jarjuk/jrr/jrr-rpi.org

#PROPERTY: header-args+ :var  JRR5_IP_="192.168.1.241"
#PROPERTY: header-args+ :var  JRR5_IP="jrr5.local"
#+PROPERTY: header-args+ :var  JRR5_IP="jrr5x.local"
#+PROPERTY: header-args+ :var  CONDA_ENV="pyyton3"
#+PROPERTY: header-args+ :var  FIRMWARE_RELEASE="5"

Somewhat dirtyish trick to be able to tangle files pointed by a global property.

#+BEGIN_SRC elisp :eval no-export :exports none
(defun jj-org-tmp-get-global-prop ( prop )
  "Read global org property 'prop'"
(let ((keyVal 
       (seq-find (lambda (x) (string= (car(split-string  x "=")) prop))
		 (org-babel--get-vars (org-babel-parse-header-arguments (org-entry-get-with-inheritance "header-args")))
		)))	
  (if keyVal (string-trim  (nth 1 (split-string keyVal "=" )) "\""  "\""  )))
)
#+END_SRC

#+RESULTS:
: jj-org-tmp-get-global-prop

* Design
** PCB design

[[file:jrr-pcb.org]]

** 3.5inch TFT display

In jrr.org

#+begin_example
ssh pi@$IP  "cd LCD-show; sudo ./MHS35-show"

#+end_example

Search for MHS35-show finds

http://www.lcdwiki.com/MHS-3.5inch_RPi_Display#Product_Features

with specs

| Name                                  | Description                          |
|---------------------------------------+--------------------------------------|
| SKU                                   | MHS3528                              |
| Screen Size                           | 3.5inch                              |
| LCD Type                              | TFT                                  |
| Module Interface                      | SPI (upports up to 125MHz SPI input) |
| Resolution                            | 320*480 (Pixel)                      |
| Touch Screen Controller               | XPT2046                              |
| LCD Driver IC                         | ILI9486                              |
| Backlight                             | LED                                  |
| power consumption                     | 0.16A*5V                             |
| Working temperature）                 | -20~60                               |
| Active Area                           | 48.96x73.44(mm)                      |
| Module PCB Size                       | 85.42*55.60 (mm)                     |
| Package Size                          | 136x98x41 (mm)                       |
| Product Weight(Package containing)(g) | 92 (g)                               |

Especially LCD Driver IC ~ILI9486~

Locate ILI9486 python driver https://github.com/SirLefti/Python_ILI9486

** Raspberry PI pinout

https://pinout.xyz/

** Physical design

https://datasheets.raspberrypi.com/rpi3/raspberry-pi-3-b-plus-product-brief.pdf

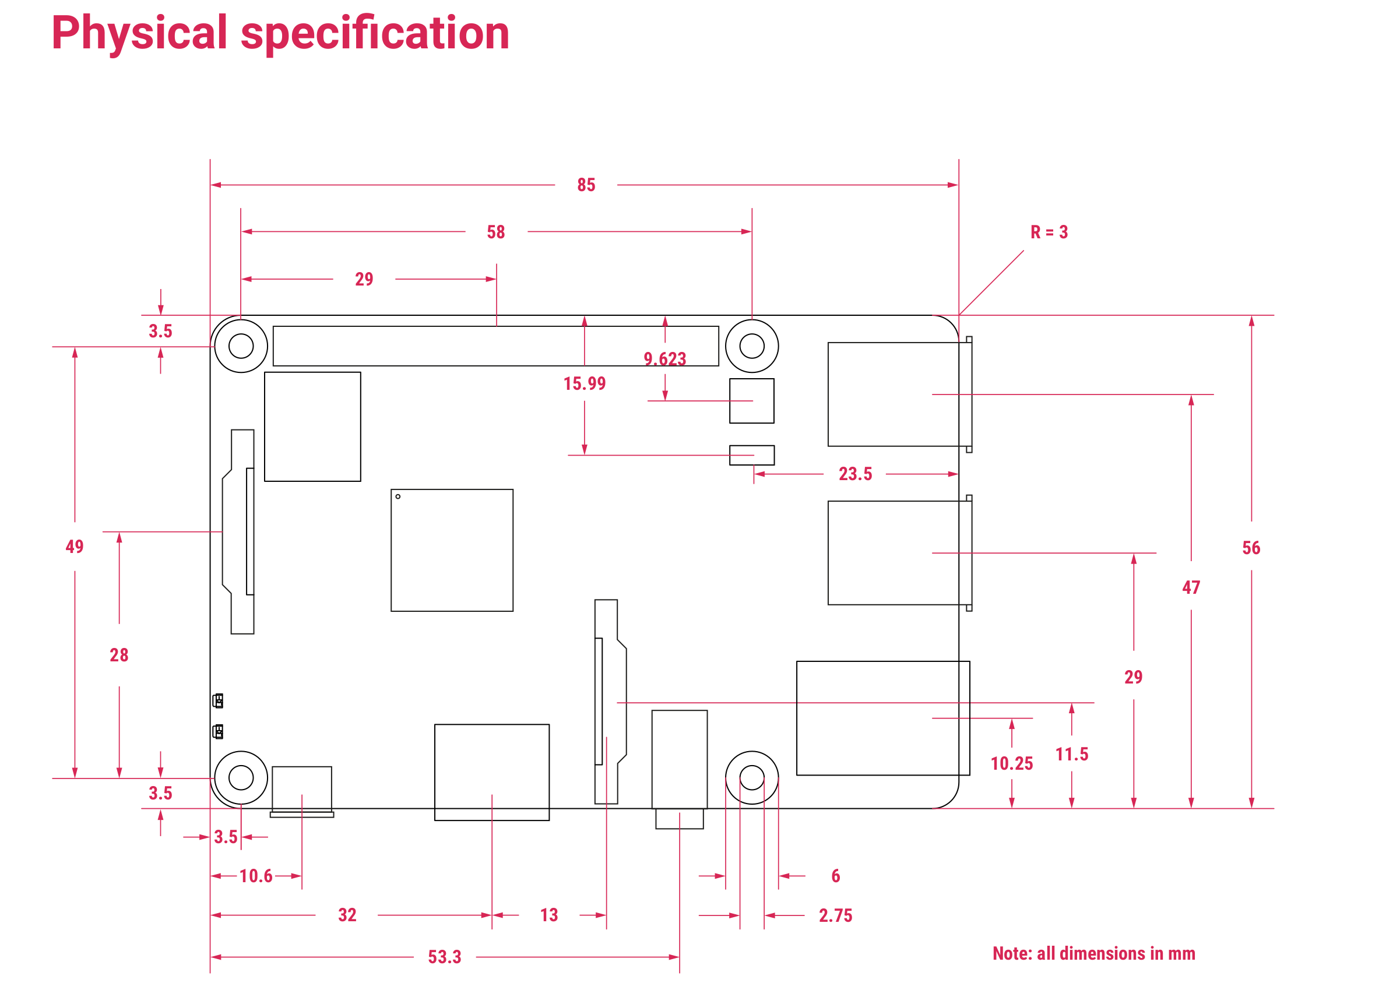
[picture p13: pics-keep/RPI-physical-dimensions.png]


** Current

Mitattu USB virrankultus jrr1
- n. 0.37A max volyymi
- n. 0.57A max virta

Mitattu USB virrankulutus jrr5
- n. 0.37A max volyymi
- n. 0.70A max virta (hekllinen)

--> 1.1A sulake ok

--> USB-C current resistores
   - https://community.infineon.com/t5/Knowledge-Base-Articles/USB-Type-C-connector-Rp-Rd-and-Ra-termination-resistors/ta-p/253544

     DFP Advertisement 	     Resistor Pull-up to
     4.75 V – 5.5 V 	     Resistor Pull-up to
     3.3 ± 5%
     Default USB power 	     56 kΩ ± 20% 	     36 kΩ ± 20%
     1.5 A at 5 V 	     22 kΩ ± 5% 	     12 kΩ ± 5%
     3.0 A at 5 V 	     10 kΩ ± 5% 	     4.7 kΩ ± 5%

| DFP Advertisement | Pull-up to 4.75 V – 5.5 V | Pull-up to 3.3 ± 5% |
|-------------------+---------------------------+---------------------|
| Default USB power | 56 kΩ ± 20%               | 36 kΩ ± 20%         |
| 1.5 A at 5 V      | 22 kΩ ± 5%                | 12 kΩ ± 5%          |
| 3.0 A at 5 V      | 10 kΩ ± 5%                | 4.7 kΩ ± 5%         |

--> 22kOhm     

* Config ssh access

** Create entry into ~.ssh/config~
:PROPERTIES:
:header-args+: :var  FILE="/home/jj/.ssh/config"
:END:

#+BEGIN_SRC bash :eval no-export :results output :dir .
echo "Running in $(pwd) for user '$(whoami)' on host '$(hostname)' on $(date)"
echo "FILE=$FILE"
echo JRR5_IP=${JRR5_IP}
#+END_SRC

#+RESULTS:
: Running in /home/jj/work/jrr for user 'jj' on host 'Leo' on ke 15.7.2026 15.39.07 +0300
: FILE=/home/jj/.ssh/config
: JRR5_IP=jrr5x.local

#+BEGIN_SRC bash :eval no-export :results output :dir .
echo "Running in $(pwd) for user '$(whoami)' on host '$(hostname)' on $(date)"
echo "FILE=$FILE"
cat $FILE
#+END_SRC

Expect raspberry pi to be online
#+call: ping-ip[:dir "."]()

#+RESULTS:
: User 'jj pinging JRR5_IP=jrr5x.local from Leo on ke 15.7.2026 15.39.31 +0300
: PING jrr5x.local (192.168.1.203) 56(84) bytes of data.
: 64 bytes from jrr5x.local (192.168.1.203): icmp_seq=1 ttl=64 time=1.92 ms
: 64 bytes from jrr5x.local (192.168.1.203): icmp_seq=2 ttl=64 time=5.18 ms
: 64 bytes from jrr5x.local (192.168.1.203): icmp_seq=3 ttl=64 time=5.69 ms
: 
: --- jrr5x.local ping statistics ---
: 3 packets transmitted, 3 received, 0% packet loss, time 2003ms
: rtt min/avg/max/mdev = 1.924/4.264/5.693/1.668 ms

#+BEGIN_SRC bash :eval no-export :results output :dir .
FILE=~/.ssh/config
START="added by raspberry.org in jrr-pi  - start"
END="added by raspberry.org in jrr-pi - end"

sed -i -e "/$START/,/$END/d" $FILE

cat <<HERE >> $FILE
# $START
host jrr5
     user pi
     IdentityFile ~/.ssh/id_ed25519
     hostname ${JRR5_IP}
# $END
HERE
#+END_SRC

#+RESULTS:

* Create SD -card image with 3-partitions
:PROPERTIES:
:header-args+: :var  SD_DEV="/dev/sda"
:END:

** Flash rasbian OS using Raspberry Pi Imager (v2.0.4)

- Selections:
  - [ ] Device: RPi 3B+
  - [ ] OS RPi Other, PI OS-light (64 bi)
    - Released 2026-04-21
    - A port of Debian Trixie with Raspberry Desktop
  - [ ] User name: pi
  - [ ] Wifi
  - [ ] Disblae Raspberry Pi Connect
  - [ ] Finnish keyboard
  - [ ] SSH identity id_ed25519.pub
  - [ ] hostname ~jrr5x~ (expect to change jrr5x1, jrr5x2, ...)

** Allocate system partiton 10G, add 2G partision 3 (CLI)
*** Extend partition 2 to include all space on SD card on RPI

#+call: ping-ip[:dir .]()

#+RESULTS:
: User 'jj pinging JRR5_IP=jrr5x.local from Leo on to 16.7.2026 12.32.57 +0300
: PING jrr5x.local (192.168.1.203) 56(84) bytes of data.
: 64 bytes from jrr5x.local (192.168.1.203): icmp_seq=1 ttl=64 time=105 ms
: 64 bytes from jrr5x.local (192.168.1.203): icmp_seq=2 ttl=64 time=5.91 ms
: 64 bytes from jrr5x.local (192.168.1.203): icmp_seq=3 ttl=64 time=5.97 ms
: 
: --- jrr5x.local ping statistics ---
: 3 packets transmitted, 3 received, 0% packet loss, time 2003ms
: rtt min/avg/max/mdev = 5.907/39.015/105.167/46.776 ms

: Ping JRR5_IP=jrr5.local on ti 19.5.2026 10.24.41 +0300
: PING jrr5.local (192.168.1.203) 56(84) bytes of data.
: 64 bytes from jrr5.local (192.168.1.203): icmp_seq=1 ttl=64 time=5.66 ms
: 64 bytes from jrr5.local (192.168.1.203): icmp_seq=2 ttl=64 time=5.60 ms
: 64 bytes from jrr5.local (192.168.1.203): icmp_seq=3 ttl=64 time=2.46 ms
: 
: --- jrr5.local ping statistics ---
: 3 packets transmitted, 3 received, 0% packet loss, time 2002ms
: rtt min/avg/max/mdev = 2.464/4.573/5.657/1.491 ms

Expect ~/ssh:jrr5:~ to log in as pi
#+call: greet-tramp[:dir /ssh:jrr5:]()

#+RESULTS:
: User 'pi' from host 'jrr5x' greeting on Thu Jul 16 12:33:52 EEST 2026  (using eshell tramp)

#+RESULTS:
: Greet Tue May 19 10:25:07 EEST 2026 from host 'jrr5' (using eshell tramp)

*** Check partions on RPI 
:PROPERTIES:
:header-args+: :dir  /ssh:jrr5:
:header-args+: :var  RPI_DISK="/dev/mmcblk0"
:END:

Ensure that running on RPI and RPI_DISK correctly set
#+BEGIN_SRC bash :eval no-export :results output
echo "Running in $(pwd) host '$(hostname)' on $(date)"
[[ -z "$RPI_DISK" ]] && echo "Missing parameter RPI_DISK" && exit 1
echo "RPI_DISK=$RPI_DISK"
#+END_SRC

#+RESULTS:
: Running in /home/pi host 'jrr5x' on Thu Jul 16 12:34:02 EEST 2026
: RPI_DISK=/dev/mmcblk0

#+BEGIN_SRC bash :eval no-export :results output :dir /ssh:jrr5:
  echo "Running in $(pwd) host '$(hostname)' on $(date)"
  sudo lsblk
#+END_SRC

#+RESULTS:
: Running in /home/pi host 'jrr5x' on Thu Jul 16 12:34:08 EEST 2026
: NAME        MAJ:MIN RM  SIZE RO TYPE MOUNTPOINTS
: loop0         7:0    0  905M  0 loop 
: mmcblk0     179:0    0 28.9G  0 disk 
: ├─mmcblk0p1 179:1    0  512M  0 part /boot/firmware
: └─mmcblk0p2 179:2    0 28.4G  0 part /
: zram0       254:0    0  905M  0 disk [SWAP]

: Running in /home/pi host 'jrr5' on Tue May 19 10:25:39 EEST 2026
: NAME        MAJ:MIN RM  SIZE RO TYPE MOUNTPOINTS
: loop0         7:0    0  905M  0 loop 
: mmcblk0     179:0    0 28.9G  0 disk 
: ├─mmcblk0p1 179:1    0  512M  0 part /boot/firmware
: └─mmcblk0p2 179:2    0 28.4G  0 part /
: zram0       254:0    0  905M  0 disk [SWAP]

#+BEGIN_SRC bash :eval no-export :results output
echo "Running in $(pwd) host '$(hostname)' on $(date)"
sudo fdisk -l $RPI_DISK
#+END_SRC

#+RESULTS:
#+begin_example
Running in /home/pi host 'jrr5x' on Thu Jul 16 12:34:14 EEST 2026
Disk /dev/mmcblk0: 28.88 GiB, 31008489472 bytes, 60563456 sectors
Units: sectors of 1 * 512 = 512 bytes
Sector size (logical/physical): 512 bytes / 512 bytes
I/O size (minimum/optimal): 512 bytes / 512 bytes
Disklabel type: dos
Disk identifier: 0x08059157

Device         Boot   Start      End  Sectors  Size Id Type
/dev/mmcblk0p1        16384  1064959  1048576  512M  c W95 FAT32 (LBA)
/dev/mmcblk0p2      1064960 60563455 59498496 28.4G 83 Linux
#+end_example

#+BEGIN_SRC sh :eval no-export :results output :noweb yes
  echo "Running in $(pwd) for user '$(whoami)' on host '$(hostname)' on $(date)"
  echo RPI_DISK=$RPI_DISK
  sudo fdisk $RPI_DISK <<EOF
  p
  EOF
#+END_SRC

#+RESULTS:
#+begin_example
Running in /home/pi for user 'pi' on host 'jrr5x' on Thu Jul 16 12:34:20 EEST 2026
RPI_DISK=/dev/mmcblk0

Welcome to fdisk (util-linux 2.41).
Changes will remain in memory only, until you decide to write them.
Be careful before using the write command.

Command (m for help): 
Disk /dev/mmcblk0: 28.88 GiB, 31008489472 bytes, 60563456 sectors
Units: sectors of 1 * 512 = 512 bytes
Sector size (logical/physical): 512 bytes / 512 bytes
I/O size (minimum/optimal): 512 bytes / 512 bytes
Disklabel type: dos
Disk identifier: 0x08059157

Device         Boot   Start      End  Sectors  Size Id Type
/dev/mmcblk0p1        16384  1064959  1048576  512M  c W95 FAT32 (LBA)
/dev/mmcblk0p2      1064960 60563455 59498496 28.4G 83 Linux

Command (m for help): 
#+end_example

*** Mount to develoment host - resize partition 2 and create new 2GB partition 3 on SD_DEV

**** Using SD_DEV
Mount SD card on host as SD_DEV

#+BEGIN_SRC bash :eval no-export :results output
  echo "Running in $(pwd) host '$(hostname)' on $(date)"
  echo SD_DEV=$SD_DEV
#+END_SRC

#+RESULTS:
: Running in /home/jj/work/jrr host 'Leo' on to 16.7.2026 18.07.29 +0300
: SD_DEV=/dev/sda

**** Ensure that ~SD_DEV~ is pointing to SD card mounted over usb

#+BEGIN_SRC bash :eval no-export :results output
echo "Running in $(pwd) host '$(hostname)' on $(date)"
echo "SD_DEV=$SD_DEV"
#+END_SRC

#+RESULTS:
: Running in /home/jj/work/jrr host 'Leo' on to 16.7.2026 18.07.34 +0300
: SD_DEV=/dev/sda

Check:
- RM=1 → removable device
- TRAN=usb → often SD card readers appear as USB
- Size matches your SD card
  - sda    28,9G usb - OK
  - sda2  28.4G    1 OS system

#+call: lsblk-conf()

#+RESULTS:
: Running in /home/jj/work/jrr host 'Leo' on to 16.7.2026 18.07.39 +0300
: SD_DEV=/dev/sda
: NAME    SIZE TRAN RM MOUNTPOINT
: sda    29,7G usb   1 
: ├─sda1  512M       1 
: └─sda2  2,3G       1 

Expect something like this:

: Running in /home/jj/work/jrr host 'Leo' on to 16.7.2026 12.07.54 +0300
: SD_DEV=/dev/sda
: NAME    SIZE TRAN RM MOUNTPOINT
: sda    28,9G usb   1 
: ├─sda1  512M       1 /media/jj/bootfs
: └─sda2  2,3G       1 /media/jj/rootfs

**** Unmount partitions on SD_DEV

#+BEGIN_SRC bash :eval no-export :results output
echo "Running in $(pwd) host '$(hostname)' on $(date)"
mount | grep $SD_DEV
#+END_SRC

#+RESULTS:
: Running in /home/jj/work/jrr host 'Leo' on to 16.7.2026 18.07.49 +0300

#+name: umount-sd-dev
#+BEGIN_SRC bash :eval no-export :results output  :dir /sudo::
echo "Running in $(pwd) host '$(hostname)' on $(date)"
sudo umount ${SD_DEV}1
sudo umount ${SD_DEV}2
sudo umount ${SD_DEV}3
#+END_SRC

#+RESULTS: umount-sd-dev
: Running in /root host 'Leo' on Thu Jul 16 06:07:53 PM EEST 2026

#+RESULTS:
: Running in /root host 'Leo' on Tue May 19 10:27:24 AM EEST 2026

Show 

#+call: sd-partitions()

#+RESULTS:
#+begin_example
Running in /root host 'Leo' on Thu Jul 16 06:13:08 PM EEST 2026
SD_DEV=/dev/sda

Welcome to fdisk (util-linux 2.39.3).
Changes will remain in memory only, until you decide to write them.
Be careful before using the write command.

Command (m for help): Disk /dev/sda: 29.72 GiB, 31914983424 bytes, 62333952 sectors
Disk model: Storage Device  
Units: sectors of 1 * 512 = 512 bytes
Sector size (logical/physical): 512 bytes / 512 bytes
I/O size (minimum/optimal): 512 bytes / 512 bytes
Disklabel type: dos
Disk identifier: 0x041bba91

Device     Boot   Start     End Sectors  Size Id Type
/dev/sda1         16384 1064959 1048576  512M  c W95 FAT32 (LBA)
/dev/sda2       1064960 5816319 4751360  2.3G 83 Linux

Command (m for help): 
#+end_example

Example of expected output
#+begin_example
Running in /root host 'Leo' on Tue May 19 10:27:32 AM EEST 2026

Welcome to fdisk (util-linux 2.39.3).
Changes will remain in memory only, until you decide to write them.
Be careful before using the write command.

Command (m for help): Disk /dev/sda: 28.88 GiB, 31008489472 bytes, 60563456 sectors
Disk model: Storage Device  
Units: sectors of 1 * 512 = 512 bytes
Sector size (logical/physical): 512 bytes / 512 bytes
I/O size (minimum/optimal): 512 bytes / 512 bytes
Disklabel type: dos
Disk identifier: 0xf307c993

Device     Boot   Start      End  Sectors  Size Id Type
/dev/sda1         16384  1064959  1048576  512M  c W95 FAT32 (LBA)
/dev/sda2       1064960 60563455 59498496 28.4G 83 Linux

Command (m for help): 
#+end_example

**** Shrink PARTITION 2 on SD_DEV 
:PROPERTIES:
:header-args+: :var  PARTITION=2
:END:

#+call: parted-print()

#+RESULTS:
#+begin_example
Running in /root host 'Leo' on Thu Jul 16 06:12:37 PM EEST 2026
Model: Mass Storage Device (scsi)
Disk /dev/sda: 31.9GB
Sector size (logical/physical): 512B/512B
Partition Table: msdos
Disk Flags: 

Number  Start   End     Size    Type     File system  Flags
 1      8389kB  545MB   537MB   primary  fat32        lba
 2      545MB   2978MB  2433MB  primary  ext4

Model: Mass Storage Device (scsi)
Disk /dev/sda: 29.7GiB
Sector size (logical/physical): 512B/512B
Partition Table: msdos
Disk Flags: 

Number  Start    End      Size     Type     File system  Flags
 1      0.01GiB  0.51GiB  0.50GiB  primary  fat32        lba
 2      0.51GiB  2.77GiB  2.27GiB  primary  ext4

#+end_example

Expect something like this

#+begin_example
Running in /root host 'Leo' on Thu Jul 16 12:58:25 PM EEST 2026
Model: Mass Storage Device (scsi)
Disk /dev/sda: 32.2GB
Sector size (logical/physical): 512B/512B
Partition Table: msdos
Disk Flags: 

Number  Start   End     Size    Type     File system  Flags
 1      8389kB  545MB   537MB   primary  fat32        lba
 2      545MB   2978MB  2433MB  primary  ext4

Model: Mass Storage Device (scsi)
Disk /dev/sda: 30.0GiB
Sector size (logical/physical): 512B/512B
Partition Table: msdos
Disk Flags: 

Number  Start    End      Size     Type     File system  Flags
 1      0.01GiB  0.51GiB  0.50GiB  primary  fat32        lba
 2      0.51GiB  2.77GiB  2.27GiB  primary  ext4

#+end_example

#+call: fs-check(PARTITION=2)
#+RESULTS:
: CHeck /dev/sda2 in /root host 'Leo' on Thu Jul 16 06:08:59 PM EEST 2026
: e2fsck 1.47.0 (5-Feb-2023)
: Pass 1: Checking inodes, blocks, and sizes
: Pass 2: Checking directory structure
: Pass 3: Checking directory connectivity
: Pass 4: Checking reference counts
: Pass 5: Checking group summary information
: rootfs: 73256/148656 files (0.2% non-contiguous), 513060/593920 blocks

Expected output 

: CHeck /dev/sda2 in /root host 'Leo' on Wed Jul 15 07:42:36 PM EEST 2026
: Pass 1: Checking inodes, blocks, and sizes
: Pass 2: Checking directory structure
: Pass 3: Checking directory connectivity
: Pass 4: Checking reference counts
: Pass 5: Checking group summary information
: rootfs: 73281/1776048 files (0.2% non-contiguous), 847924/7437312 blocks

Shrink ext4 filesystem FIRST to +22G+ 10G
#+BEGIN_SRC bash :eval no-export :results output  :dir /sudo::
  echo "Running in $(pwd) host '$(hostname)' on $(date)"
  sudo resize2fs ${SD_DEV}${PARTITION} 10G
#+END_SRC

#+RESULTS:
: Running in /root host 'Leo' on Thu Jul 16 06:11:02 PM EEST 2026

#+BEGIN_SRC bash :eval no-export :results output
  echo "Running in $(pwd) host '$(hostname)' on $(date)"
  echo Partition ${SD_DEV}${PARTITION}
  df -h ${SD_DEV}${PARTITION}
#+END_SRC

#+RESULTS:
: Running in /home/jj/work/jrr host 'Leo' on to 16.7.2026 18.10.27 +0300
: Partition /dev/sda2
: Filesystem      Size  Used Avail Use% Mounted on
: udev             16G     0   16G   0% /dev

Expected output
: Running in /home/jj/work/jrr host 'Leo' on ti 19.5.2026 10.28.03 +0300
: Partition /dev/sda2
: Filesystem      Size  Used Avail Use% Mounted on
: udev             16G     0   16G   0% /dev

#+BEGIN_SRC octave :eval no-export :results output :session *Octave* :exports both
  pico = 10^-12;
  nano = 10^-9;
  micro = 10^-6;
  milli = 10^-3;
  kilo = 10^3;
  mega = 10^6;
  giga = 10^9;

5767168 * 4*1024
  #+END_SRC   

#+RESULTS:
: ans = 2.3622e+10

Check file system (after resize - expect pass)
#+call: fs-check(PARTITION=2)

#+RESULTS:
: CHeck /dev/sda2 in /root host 'Leo' on Thu Jul 16 12:59:08 PM EEST 2026
: e2fsck 1.47.0 (5-Feb-2023)
: Pass 1: Checking inodes, blocks, and sizes
: Pass 2: Checking directory structure
: Pass 3: Checking directory connectivity
: Pass 4: Checking reference counts
: Pass 5: Checking group summary information
: rootfs: 73256/148656 files (0.2% non-contiguous), 513060/593920 blocks

Before resize confirm:
- partition 2 currently extends beyond 25GiB
- partition 1 stays untouched
- there’s room afterward for partition 3

#+call: parted-print()  

#+RESULTS:
#+begin_example
Running in /root host 'Leo' on Thu Jul 16 12:59:26 PM EEST 2026
Model: Mass Storage Device (scsi)
Disk /dev/sda: 32.2GB
Sector size (logical/physical): 512B/512B
Partition Table: msdos
Disk Flags: 

Number  Start   End     Size    Type     File system  Flags
 1      8389kB  545MB   537MB   primary  fat32        lba
 2      545MB   2978MB  2433MB  primary  ext4

Model: Mass Storage Device (scsi)
Disk /dev/sda: 30.0GiB
Sector size (logical/physical): 512B/512B
Partition Table: msdos
Disk Flags: 

Number  Start    End      Size     Type     File system  Flags
 1      0.01GiB  0.51GiB  0.50GiB  primary  fat32        lba
 2      0.51GiB  2.77GiB  2.27GiB  primary  ext4

#+end_example

Expected output
#+begin_example
Running in /root host 'Leo' on Tue May 19 10:28:20 AM EEST 2026
Model: Mass Storage Device (scsi)
Disk /dev/sda: 31.0GB
Sector size (logical/physical): 512B/512B
Partition Table: msdos
Disk Flags: 

Number  Start   End     Size    Type     File system  Flags
 1      8389kB  545MB   537MB   primary  fat32        lba
 2      545MB   31.0GB  30.5GB  primary  ext4

Model: Mass Storage Device (scsi)
Disk /dev/sda: 28.9GiB
Sector size (logical/physical): 512B/512B
Partition Table: msdos
Disk Flags: 

Number  Start    End      Size     Type     File system  Flags
 1      0.01GiB  0.51GiB  0.50GiB  primary  fat32        lba
 2      0.51GiB  28.9GiB  28.4GiB  primary  ext4

#+end_example

Run on command line (notice 23GiB for 22G filesystem)
#+BEGIN_SRC bash :eval no-export :results output  :dir /sudo::
echo "Running in $(pwd) host '$(hostname)' on $(date)"
echo sudo parted  $SD_DEV resizepart 2 23GiB
#+END_SRC

#+RESULTS:
: Running in /root host 'Leo' on Thu Jul 16 12:59:35 PM EEST 2026
: sudo parted /dev/sda resizepart 2 23GiB

Check 
#+call: parted-print()  

#+RESULTS:
#+begin_example
Running in /root host 'Leo' on Thu Jul 16 01:00:01 PM EEST 2026
Model: Mass Storage Device (scsi)
Disk /dev/sda: 32.2GB
Sector size (logical/physical): 512B/512B
Partition Table: msdos
Disk Flags: 

Number  Start   End     Size    Type     File system  Flags
 1      8389kB  545MB   537MB   primary  fat32        lba
 2      545MB   24.7GB  24.2GB  primary  ext4

Model: Mass Storage Device (scsi)
Disk /dev/sda: 30.0GiB
Sector size (logical/physical): 512B/512B
Partition Table: msdos
Disk Flags: 

Number  Start    End      Size     Type     File system  Flags
 1      0.01GiB  0.51GiB  0.50GiB  primary  fat32        lba
 2      0.51GiB  23.0GiB  22.5GiB  primary  ext4

#+end_example

Expected output

#+begin_example
Running in /root host 'Leo' on Tue May 19 10:29:16 AM EEST 2026
Model: Mass Storage Device (scsi)
Disk /dev/sda: 31.0GB
Sector size (logical/physical): 512B/512B
Partition Table: msdos
Disk Flags: 

Number  Start   End     Size    Type     File system  Flags
 1      8389kB  545MB   537MB   primary  fat32        lba
 2      545MB   24.7GB  24.2GB  primary  ext4

Model: Mass Storage Device (scsi)
Disk /dev/sda: 28.9GiB
Sector size (logical/physical): 512B/512B
Partition Table: msdos
Disk Flags: 

Number  Start    End      Size     Type     File system  Flags
 1      0.01GiB  0.51GiB  0.50GiB  primary  fat32        lba
 2      0.51GiB  23.0GiB  22.5GiB  primary  ext4

#+end_example

Expect fs-check pass
#+call: fs-check()

#+RESULTS:
: CHeck /dev/sda2 in /root host 'Leo' on Thu Jul 16 01:00:21 PM EEST 2026
: e2fsck 1.47.0 (5-Feb-2023)
: Pass 1: Checking inodes, blocks, and sizes
: Pass 2: Checking directory structure
: Pass 3: Checking directory connectivity
: Pass 4: Checking reference counts
: Pass 5: Checking group summary information
: rootfs: 73256/148656 files (0.2% non-contiguous), 513060/593920 blocks

: CHeck /dev/sda2 in /root host 'Leo' on Tue May 19 10:29:30 AM EEST 2026
: Pass 1: Checking inodes, blocks, and sizes
: Pass 2: Checking directory structure
: Pass 3: Checking directory connectivity
: Pass 4: Checking reference counts
: Pass 5: Checking group summary information
: rootfs: 73201/1441792 files (0.2% non-contiguous), 877124/5767168 blocks

#+BEGIN_SRC bash :eval no-export :results output
echo "Running in $(pwd) host '$(hostname)' on $(date)"
lsblk $SD_DEV
#+END_SRC

#+RESULTS:
: Running in /home/jj/work/jrr host 'Leo' on to 16.7.2026 13.00.50 +0300
: NAME   MAJ:MIN RM  SIZE RO TYPE MOUNTPOINTS
: sda      8:0    1   30G  0 disk 
: ├─sda1   8:1    1  512M  0 part 
: └─sda2   8:2    1 22,5G  0 part 

Expected output

: Running in /home/jj/work/jrr host 'Leo' on ti 19.5.2026 10.29.38 +0300
: NAME   MAJ:MIN RM  SIZE RO TYPE MOUNTPOINTS
: sda      8:0    1 28,9G  0 disk 
: ├─sda1   8:1    1  512M  0 part 
: └─sda2   8:2    1 22,5G  0 part 

**** Add partition 3 of size 2G and label it ~home~
:PROPERTIES:
:header-args+: :var  PARTITION=3
:END:

#+BEGIN_SRC bash :eval no-export :results output
  echo "Running in $(pwd) host '$(hostname)' on $(date)"
  echo "SD_DEV=$SD_DEV"
  echo "PARTITION=$PARTITION"
#+END_SRC

#+RESULTS:
: Running in /home/jj/work/jrr host 'Leo' on to 16.7.2026 13.00.56 +0300
: SD_DEV=/dev/sda
: PARTITION=3

#+BEGIN_SRC bash :eval no-export :results output  :dir /sudo::
echo "Running in $(pwd) host '$(hostname)' on $(date)"
sudo parted $SD_DEV unit GiB print free
#+END_SRC

#+RESULTS:
#+begin_example
Running in /root host 'Leo' on Thu Jul 16 01:01:11 PM EEST 2026
Model: Mass Storage Device (scsi)
Disk /dev/sda: 30.0GiB
Sector size (logical/physical): 512B/512B
Partition Table: msdos
Disk Flags: 

Number  Start    End      Size     Type     File system  Flags
        0.00GiB  0.01GiB  0.01GiB           Free Space
 1      0.01GiB  0.51GiB  0.50GiB  primary  fat32        lba
 2      0.51GiB  23.0GiB  22.5GiB  primary  ext4
        23.0GiB  30.0GiB  7.01GiB           Free Space

#+end_example

Expected output

#+begin_example
Running in /root host 'Leo' on Tue May 19 10:29:57 AM EEST 2026
Model: Mass Storage Device (scsi)
Disk /dev/sda: 28.9GiB
Sector size (logical/physical): 512B/512B
Partition Table: msdos
Disk Flags: 

Number  Start    End      Size     Type     File system  Flags
        0.00GiB  0.01GiB  0.01GiB           Free Space
 1      0.01GiB  0.51GiB  0.50GiB  primary  fat32        lba
 2      0.51GiB  23.0GiB  22.5GiB  primary  ext4
        23.0GiB  28.9GiB  5.88GiB           Free Space

#+end_example

Run on terminal *check start address for free space*
#+BEGIN_SRC bash :eval no-export :results output
echo "Running in $(pwd) host '$(hostname)' on $(date)"
echo sudo parted -s $SD_DEV  mkpart primary ext4 23.0GiB 25.5GiB
#+END_SRC

#+RESULTS:
: Running in /home/jj/work/jrr host 'Leo' on to 16.7.2026 13.01.27 +0300
: sudo parted -s /dev/sda mkpart primary ext4 23.0GiB 25.5GiB

Check change (expect three partitions)
#+call: parted-print()

#+RESULTS:
#+begin_example
Running in /root host 'Leo' on Thu Jul 16 01:02:12 PM EEST 2026
Model: Mass Storage Device (scsi)
Disk /dev/sda: 32.2GB
Sector size (logical/physical): 512B/512B
Partition Table: msdos
Disk Flags: 

Number  Start   End     Size    Type     File system  Flags
 1      8389kB  545MB   537MB   primary  fat32        lba
 2      545MB   24.7GB  24.2GB  primary  ext4
 3      24.7GB  26.8GB  2147MB  primary

Model: Mass Storage Device (scsi)
Disk /dev/sda: 30.0GiB
Sector size (logical/physical): 512B/512B
Partition Table: msdos
Disk Flags: 

Number  Start    End      Size     Type     File system  Flags
 1      0.01GiB  0.51GiB  0.50GiB  primary  fat32        lba
 2      0.51GiB  23.0GiB  22.5GiB  primary  ext4
 3      23.0GiB  25.0GiB  2.00GiB  primary

#+end_example

Expected output
#+begin_example
Running in /root host 'Leo' on Tue May 19 10:30:22 AM EEST 2026
Model: Mass Storage Device (scsi)
Disk /dev/sda: 31.0GB
Sector size (logical/physical): 512B/512B
Partition Table: msdos
Disk Flags: 

Number  Start   End     Size    Type     File system  Flags
 1      8389kB  545MB   537MB   primary  fat32        lba
 2      545MB   24.7GB  24.2GB  primary  ext4
 3      24.7GB  26.8GB  2147MB  primary

Model: Mass Storage Device (scsi)
Disk /dev/sda: 28.9GiB
Sector size (logical/physical): 512B/512B
Partition Table: msdos
Disk Flags: 

Number  Start    End      Size     Type     File system  Flags
 1      0.01GiB  0.51GiB  0.50GiB  primary  fat32        lba
 2      0.51GiB  23.0GiB  22.5GiB  primary  ext4
 3      23.0GiB  25.0GiB  2.00GiB  primary

#+end_example

Format filesystem on PARTITION
#+BEGIN_SRC bash :eval no-export :results output  :dir /sudo::
echo "Running in $(pwd) host '$(hostname)' on $(date)"
sudo mkfs.ext4 ${SD_DEV}${PARTITION}
#+END_SRC

#+RESULTS:
#+begin_example
Running in /root host 'Leo' on Thu Jul 16 01:02:40 PM EEST 2026
Creating filesystem with 524288 4k blocks and 131072 inodes
Filesystem UUID: 74fdccdf-2264-4627-8bf0-18e41384ce01
Superblock backups stored on blocks: 
	32768, 98304, 163840, 229376, 294912

Allocating group tables:  0/16     done                            
Writing inode tables:  0/16     done                            
Creating journal (16384 blocks): done
Writing superblocks and filesystem accounting information:  0/16     done

#+end_example

Expected output
#+begin_example
Running in /root host 'Leo' on Tue May 19 10:30:30 AM EEST 2026
Creating filesystem with 524288 4k blocks and 131072 inodes
Filesystem UUID: fa610b2a-3c01-408b-acf1-093e30072a64
Superblock backups stored on blocks: 
	32768, 98304, 163840, 229376, 294912

Allocating group tables:  0/16     done                            
Writing inode tables:  0/16     done                            
Creating journal (16384 blocks): done
Writing superblocks and filesystem accounting information:  0/16     done

#+end_example

#+BEGIN_SRC bash :eval no-export :results output
echo "Running in $(pwd) host '$(hostname)' on $(date)"
lsblk $SD_DEV
#+END_SRC

#+RESULTS:
: Running in /home/jj/work/jrr host 'Leo' on to 16.7.2026 13.03.15 +0300
: NAME   MAJ:MIN RM  SIZE RO TYPE MOUNTPOINTS
: sda      8:0    1   30G  0 disk 
: ├─sda1   8:1    1  512M  0 part 
: ├─sda2   8:2    1 22,5G  0 part 
: └─sda3   8:3    1    2G  0 part 

Expected output
: Running in /home/jj/work/jrr host 'Leo' on ti 19.5.2026 10.30.38 +0300
: NAME   MAJ:MIN RM  SIZE RO TYPE MOUNTPOINTS
: sda      8:0    1 28,9G  0 disk 
: ├─sda1   8:1    1  512M  0 part 
: ├─sda2   8:2    1 22,5G  0 part 
: └─sda3   8:3    1    2G  0 part 

Label PARTITION 3 as ~home2~
#+BEGIN_SRC bash :eval no-export :results output  :dir /sudo:: :var PARTITION=3
  echo "Running in $(pwd) host '$(hostname)' on $(date)"
  echo "SD_DEV=$SD_DEV"
  echo PARTITION=$PARTITION
  echo ${SD_DEV}${PARTITION}
  sudo e2label ${SD_DEV}${PARTITION} home2
#+END_SRC

#+RESULTS:
: Running in /root host 'Leo' on Thu Jul 16 01:03:24 PM EEST 2026
: SD_DEV=/dev/sda
: PARTITION=3
: /dev/sda3

Shouw mounts
#+BEGIN_SRC bash :eval no-export :results output
echo "Running in $(pwd) for user '$(whoami)' on host '$(hostname)' on $(date)"
echo "mount | grep $SD_DEV"
#+END_SRC

#+RESULTS:
: Running in /home/jj/work/jrr for user 'jj' on host 'Leo' on to 16.7.2026 13.03.31 +0300
: mount | grep /dev/sda

#+call: umount-sd-dev()

#+RESULTS:
: Running in /root host 'Leo' on Thu Jul 16 01:03:40 PM EEST 2026

** Allocate system partiton 10G, add 2G partision 3 (GUI)

Using gparted

#+begin_example
sudo gparted
#+end_example

- Choose SD-vard *important*
- Increate parition 2
  - right click, right arrow --> 10GB
  - apply
- Add partition 3
  - primary partition
  - label home2
  - about 2000 Mib ~ 2GB
  - apply

Check

#+call: lsblk-conf()

#+RESULTS:
: Running in /home/jj/work/jrr host 'Leo' on to 16.7.2026 18.35.23 +0300
: SD_DEV=/dev/sda
: NAME    SIZE TRAN RM MOUNTPOINT
: sda    29,7G usb   1 
: ├─sda1  512M       1 
: ├─sda2  9,8G       1 
: └─sda3    2G       1 

#+call: parted-print(PARTITION=2)

#+RESULTS:
#+begin_example
Running in /root host 'Leo' on Thu Jul 16 06:35:54 PM EEST 2026
Model: Mass Storage Device (scsi)
Disk /dev/sda: 31.9GB
Sector size (logical/physical): 512B/512B
Partition Table: msdos
Disk Flags: 

Number  Start   End     Size    Type     File system  Flags
 1      8389kB  545MB   537MB   primary  fat32        lba
 2      545MB   11.0GB  10.5GB  primary  ext4
 3      11.0GB  13.1GB  2097MB  primary  ext4

Model: Mass Storage Device (scsi)
Disk /dev/sda: 29.7GiB
Sector size (logical/physical): 512B/512B
Partition Table: msdos
Disk Flags: 

Number  Start    End      Size     Type     File system  Flags
 1      0.01GiB  0.51GiB  0.50GiB  primary  fat32        lba
 2      0.51GiB  10.3GiB  9.77GiB  primary  ext4
 3      10.3GiB  12.2GiB  1.95GiB  primary  ext4

#+end_example

Check file sysstems

#+call: fs-check(PARTITION=2)

#+RESULTS:
: CHeck /dev/sda2 in /root host 'Leo' on Thu Jul 16 06:36:23 PM EEST 2026
: e2fsck 1.47.0 (5-Feb-2023)
: Pass 1: Checking inodes, blocks, and sizes
: Pass 2: Checking directory structure
: Pass 3: Checking directory connectivity
: Pass 4: Checking reference counts
: Pass 5: Checking group summary information
: rootfs: 73256/618096 files (0.2% non-contiguous), 542958/2560000 blocks

#+call: fs-check(PARTITION=3)

#+RESULTS:
: CHeck /dev/sda3 in /root host 'Leo' on Thu Jul 16 06:36:32 PM EEST 2026
: e2fsck 1.47.0 (5-Feb-2023)
: Pass 1: Checking inodes, blocks, and sizes
: Pass 2: Checking directory structure
: Pass 3: Checking directory connectivity
: Pass 4: Checking reference counts
: Pass 5: Checking group summary information
: home2: 11/128000 files (0.0% non-contiguous), 16986/512000 blocks

#+call: vfat-chk(PARTITION=1)

#+RESULTS:
: CHeck VFAT file system on /dev/sda1 in /root host 'Leo' on Thu Jul 16 06:36:47 PM EEST 2026
: fsck.fat 4.2 (2021-01-31)
: /dev/sda1: 421 files, 152612/1032408 clusters

#+call: mount-devs[:dir .]()

#+RESULTS:
#+begin_example
Running in /home/jj/work/jrr host 'Leo' on to 16.7.2026 18.39.06 +0300
udev on /dev type devtmpfs (rw,nosuid,relatime,size=16121596k,nr_inodes=4030399,mode=755,inode64)
devpts on /dev/pts type devpts (rw,nosuid,noexec,relatime,gid=5,mode=620,ptmxmode=000)
/dev/nvme0n1p2 on / type ext4 (rw,relatime)
tmpfs on /dev/shm type tmpfs (rw,nosuid,nodev,inode64)
mqueue on /dev/mqueue type mqueue (rw,nosuid,nodev,noexec,relatime)
hugetlbfs on /dev/hugepages type hugetlbfs (rw,nosuid,nodev,relatime,pagesize=2M)
/dev/nvme0n1p1 on /boot/efi type vfat (rw,relatime,fmask=0022,dmask=0022,codepage=437,iocharset=iso8859-1,shortname=mixed,errors=remount-ro)
/dev/mapper/veracrypt1 on /home/jj/vc type ext4 (rw,relatime)
/dev/mapper/veracrypt2 on /media/veracrypt2 type vfat (rw,relatime,uid=1000,gid=1000,fmask=0077,dmask=0077,codepage=437,iocharset=iso8859-1,shortname=mixed,errors=remount-ro)
#+end_example

* OS install & config
:PROPERTIES:
:header-args+: :dir  /ssh:jrr5:
:END:

** Expect JRR_IP to respond to ping and ssh connection to work

#+call: ping-ip[:dir .]()

#+RESULTS:
: User 'jj pinging JRR5_IP=jrr5x.local from Leo on to 16.7.2026 18.45.28 +0300
: PING jrr5x.local (192.168.1.203) 56(84) bytes of data.
: 64 bytes from jrr5x.local (192.168.1.203): icmp_seq=1 ttl=64 time=106 ms
: 64 bytes from jrr5x.local (192.168.1.203): icmp_seq=2 ttl=64 time=5.32 ms
: 64 bytes from jrr5x.local (192.168.1.203): icmp_seq=3 ttl=64 time=5.83 ms
: 
: --- jrr5x.local ping statistics ---
: 3 packets transmitted, 3 received, 0% packet loss, time 2002ms
: rtt min/avg/max/mdev = 5.323/39.151/106.303/47.483 ms

#+call: greet-tramp()

#+RESULTS:
: User 'pi' from host 'jrr5x' greeting on Thu Jul 16 18:45:50 EEST 2026  (using eshell tramp)

** Update && upgrade

#+call: disk-space()

#+RESULTS:
#+begin_example
Installation target host jrr5x on Thu Jul 16 18:45:59 EEST 2026 for user pi
Free disk space
Filesystem      Size  Used Avail Use% Mounted on
udev            332M     0  332M   0% /dev
tmpfs           190M  4.0M  186M   3% /run
/dev/mmcblk0p2   11G  3.0G  6.8G  31% /
tmpfs           475M     0  475M   0% /dev/shm
tmpfs           5.3M   17k  5.3M   1% /run/lock
tmpfs           1.1M     0  1.1M   0% /run/credentials/systemd-journald.service
tmpfs           475M  4.1k  475M   1% /tmp
/dev/mmcblk0p1  529M   79M  451M  15% /boot/firmware
tmpfs           1.1M     0  1.1M   0% /run/credentials/getty@tty1.service
tmpfs           1.1M     0  1.1M   0% /run/credentials/serial-getty@ttyS0.service
tmpfs            95M  8.2k   95M   1% /run/user/1000
#+end_example

#+call: apt-update()

#+RESULTS:
#+begin_example
Running in /home/pi host 'jrr5x' on Thu Jul 16 18:46:04 EEST 2026

0% [Working]
            
Get:1 http://deb.debian.org/debian trixie InRelease [140 kB]

0% [1 InRelease 140 kB/140 kB 100%] [Connecting to archive.raspberrypi.com (176
                                                                               
0% [Connecting to archive.raspberrypi.com (176.126.243.6)]
                                                          
Get:2 http://deb.debian.org/debian trixie-updates InRelease [47.3 kB]

Get:3 http://deb.debian.org/debian-security trixie-security InRelease [43.4 kB]

0% [Waiting for headers]
0% [Waiting for headers]
                        
Get:4 http://archive.raspberrypi.com/debian trixie InRelease [54.8 kB]

0% [4 InRelease 15.7 kB/54.8 kB 29%]
                                    
Get:5 http://deb.debian.org/debian trixie/main armhf Packages [9240 kB]

0% [5 Packages 1444 B/9240 kB 0%] [4 InRelease 18.6 kB/54.8 kB 34%]
0% [5 Packages 160 kB/9240 kB 2%] [4 InRelease 43.2 kB/54.8 kB 79%]
0% [5 Packages 234 kB/9240 kB 3%] [4 InRelease 46.1 kB/54.8 kB 84%]
                                                                   
0% [5 Packages 549 kB/9240 kB 6%]
0% [5 Packages 707 kB/9240 kB 8%]
                                 
Get:6 http://archive.raspberrypi.com/debian trixie/main arm64 Packages [463 kB]

0% [5 Packages 887 kB/9240 kB 10%] [6 Packages 5547 B/463 kB 1%]
                                                                
0% [5 Packages 1577 kB/9240 kB 17%]
0% [6 Packages store 0 B] [5 Packages 1581 kB/9240 kB 17%] [Waiting for headers
                                                                               
Get:7 http://archive.raspberrypi.com/debian trixie/main armhf Packages [455 kB]

0% [6 Packages store 0 B] [5 Packages 1688 kB/9240 kB 18%] [7 Packages 1203 B/4
                                                                               
0% [5 Packages 1740 kB/9240 kB 19%] [7 Packages 123 kB/455 kB 27%]
                                                                  
0% [5 Packages 1988 kB/9240 kB 22%]
0% [7 Packages store 0 B] [5 Packages 1988 kB/9240 kB 22%]
                                                          
0% [5 Packages 2433 kB/9240 kB 26%]
0% [5 Packages 4111 kB/9240 kB 44%]
0% [5 Packages 5728 kB/9240 kB 62%]
0% [5 Packages 7281 kB/9240 kB 79%]
0% [5 Packages 8961 kB/9240 kB 97%]
0% [5 Packages 9240 kB/9240 kB 100%]
                                    
0% [Working]
0% [5 Packages store 0 B]
                         
Get:8 http://deb.debian.org/debian trixie-updates/main arm64 Packages.diff/Index [3854 B]

0% [5 Packages store 0 B] [8 Packages 3854 B/3854 B 100%]
                                                         
0% [5 Packages store 0 B]
                         
Get:9 http://deb.debian.org/debian trixie-updates/main armhf Packages.diff/Index [3854 B]

Get:10 http://deb.debian.org/debian trixie-updates/main Translation-en.diff/Index [3854 B]

48% [5 Packages store 0 B]
                          
Get:11 http://deb.debian.org/debian trixie-updates/main arm64 Packages T-2026-07-14-1401.03-F-2026-07-14-1401.03.pdiff [569 B]

48% [5 Packages store 0 B] [11 Packages 0 B/569 B 0%]
                                                     
48% [5 Packages store 0 B]
                          
Get:12 http://deb.debian.org/debian trixie-updates/main armhf Packages T-2026-07-14-1401.03-F-2026-07-14-1401.03.pdiff [568 B]

48% [5 Packages store 0 B]
                          
Get:11 http://deb.debian.org/debian trixie-updates/main arm64 Packages T-2026-07-14-1401.03-F-2026-07-14-1401.03.pdiff [569 B]

48% [5 Packages store 0 B]
                          
Get:12 http://deb.debian.org/debian trixie-updates/main armhf Packages T-2026-07-14-1401.03-F-2026-07-14-1401.03.pdiff [568 B]

48% [12 Packages rred 0 B] [5 Packages store 0 B] [Waiting for headers]
                                                                       
Get:13 http://deb.debian.org/debian trixie-updates/main Translation-en T-2026-07-14-1401.03-F-2026-07-14-1401.03.pdiff [353 B]

48% [12 Packages rred 0 B] [5 Packages store 0 B] [13 Translation-en 0 B/353 B 
                                                                               
48% [12 Packages rred 0 B] [5 Packages store 0 B]
                                                 
48% [5 Packages store 0 B]
                          
Get:13 http://deb.debian.org/debian trixie-updates/main Translation-en T-2026-07-14-1401.03-F-2026-07-14-1401.03.pdiff [353 B]

48% [13 Translation-en rred 0 B] [5 Packages store 0 B]
                                                       
49% [5 Packages store 0 B] [Waiting for headers]
                                                
Get:14 http://deb.debian.org/debian trixie/main arm64 Packages [9607 kB]

49% [5 Packages store 0 B] [14 Packages 724 B/9607 kB 0%]
54% [5 Packages store 0 B] [14 Packages 1689 kB/9607 kB 18%]
59% [5 Packages store 0 B] [14 Packages 3303 kB/9607 kB 34%]
63% [5 Packages store 0 B] [14 Packages 4926 kB/9607 kB 51%]
68% [5 Packages store 0 B] [14 Packages 6535 kB/9607 kB 68%]       2788 kB/s 3s
73% [5 Packages store 0 B] [14 Packages 8146 kB/9607 kB 85%]       2788 kB/s 3s
77% [5 Packages store 0 B] [14 Packages 9607 kB/9607 kB 100%]      2788 kB/s 2s
77% [5 Packages store 0 B]                                         2788 kB/s 2s
                                                                               
Get:15 http://deb.debian.org/debian trixie/main Translation-en [6484 kB]

77% [5 Packages store 0 B] [15 Translation-en 5381 B/6484 kB 0%]   2788 kB/s 2s
81% [15 Translation-en 1109 kB/6484 kB 17%]                        2788 kB/s 2s
                                                                               
81% [14 Packages store 0 B] [15 Translation-en 1109 kB/6484 kB 17%]
85% [14 Packages store 0 B] [15 Translation-en 2697 kB/6484 kB 42%]
90% [14 Packages store 0 B] [15 Translation-en 4344 kB/6484 kB 67%]
95% [14 Packages store 0 B] [15 Translation-en 5957 kB/6484 kB 92%]
97% [14 Packages store 0 B]                                        2788 kB/s 0s
                                                                               
Get:16 http://deb.debian.org/debian-security trixie-security/main armhf Packages [207 kB]

97% [14 Packages store 0 B] [16 Packages 8214 B/207 kB 4%]         2788 kB/s 0s
97% [14 Packages store 0 B]                                        2788 kB/s 0s
                                                                               
Get:17 http://deb.debian.org/debian-security trixie-security/main arm64 Packages [227 kB]

97% [14 Packages store 0 B] [17 Packages 54.3 kB/227 kB 24%]       2788 kB/s 0s
98% [14 Packages store 0 B]                                        2788 kB/s 0s
                                                                               
Get:18 http://deb.debian.org/debian-security trixie-security/main Translation-en [136 kB]

98% [14 Packages store 0 B] [18 Translation-en 21.0 kB/136 kB 15%]
98% [14 Packages store 0 B]                                        2788 kB/s 0s
98% [14 Packages store 0 B]                                        2788 kB/s 0s
98% [14 Packages store 0 B]                                        2788 kB/s 0s
98% [14 Packages store 0 B]                                        2788 kB/s 0s
98% [14 Packages store 0 B]                                        2788 kB/s 0s
98% [14 Packages store 0 B]                                        1672 kB/s 0s
99% [Working]                                                      1672 kB/s 0s
99% [15 Translation-en store 0 B]                                  1672 kB/s 0s
99% [15 Translation-en store 0 B]                                  1672 kB/s 0s
99% [15 Translation-en store 0 B]                                  1672 kB/s 0s
99% [15 Translation-en store 0 B]                                  1672 kB/s 0s
99% [Working]                                                      1672 kB/s 0s
99% [16 Packages store 0 B]                                        1672 kB/s 0s
99% [Working]                                                      1672 kB/s 0s
99% [17 Packages store 0 B]                                        1672 kB/s 0s
100% [Working]                                                     1672 kB/s 0s
100% [18 Translation-en store 0 B]                                 1672 kB/s 0s
100% [Working]                                                     1672 kB/s 0s
                                                                               
Fetched 26.9 MB in 14s (1880 kB/s)

Reading package lists... 0%

Reading package lists... 0%

Reading package lists... 0%

Reading package lists... 10%

Reading package lists... 20%

Reading package lists... 29%

Reading package lists... 36%

Reading package lists... 36%

Reading package lists... 37%

Reading package lists... 51%

Reading package lists... 64%

Reading package lists... 71%

Reading package lists... 71%

Reading package lists... 77%

Reading package lists... 93%

Reading package lists... 93%

Reading package lists... 94%

Reading package lists... 94%

Reading package lists... 94%

Reading package lists... 94%

Reading package lists... 94%

Reading package lists... 94%

Reading package lists... 94%

Reading package lists... 94%

Reading package lists... 94%

Reading package lists... 94%

Reading package lists... 94%

Reading package lists... 94%

Reading package lists... 94%

Reading package lists... 94%

Reading package lists... 95%

Reading package lists... 95%

Reading package lists... 95%

Reading package lists... 95%

Reading package lists... 95%

Reading package lists... 95%

Reading package lists... 95%

Reading package lists... 95%

Reading package lists... 95%

Reading package lists... 95%

Reading package lists... 96%

Reading package lists... 96%

Reading package lists... 96%

Reading package lists... 96%

Reading package lists... 97%

Reading package lists... 97%

Reading package lists... 97%

Reading package lists... 97%

Reading package lists... 98%

Reading package lists... 98%

Reading package lists... 99%

Reading package lists... 99%

Reading package lists... Done
#+end_example

#+call: apt-list-upgradeable()

#+call: apt-upgrade()

#+RESULTS:
#+begin_example
Running in /home/pi host 'jrr5x' on Thu Jul 16 18:47:11 EEST 2026

Reading package lists... 0%

Reading package lists... 100%

Reading package lists... Done

Building dependency tree... 0%

Building dependency tree... 0%

Building dependency tree... 50%

Building dependency tree... 50%

Building dependency tree... 69%

Building dependency tree... Done

Reading state information... 0% 

Reading state information... 0%

Reading state information... Done

Calculating upgrade... 0%

Calculating upgrade... 50%

Calculating upgrade... Done
The following packages will be upgraded:
  base-files curl dhcpcd-base dirmngr firmware-atheros firmware-brcm80211
  firmware-libertas firmware-mediatek firmware-realtek gnupg-utils gpg
  gpg-agent gpg-wks-client gpgconf gpgsm gpgv libcurl3t64-gnutls libcurl4t64
  libdtovl0 libgpiolib0 liblzma5 libnss3 libntfs-3g89t64 libpisp-common
  libpisp1 libpython3.13 libpython3.13-minimal libpython3.13-stdlib
  librpieepromab0 librpifwcrypto0 libssh2-1t64 libtalloc2 libtasn1-6
  libwbclient0 libxml2 ntfs-3g python3-idna python3-urllib3 python3.13
  python3.13-minimal python3.13-venv raspi-utils raspi-utils-core
  raspi-utils-dt raspi-utils-eeprom raspi-utils-otp raspinfo rpi-connect-lite
  rpi-eeprom rpi-loop-utils rpi-swap rpieepromab rpifwcrypto rsync
  wireless-regdb xz-utils
56 upgraded, 0 newly installed, 0 to remove and 0 not upgraded.
Need to get 104 MB of archives.
After this operation, 53.4 MB of additional disk space will be used.

0% [Working]
            
Get:1 http://deb.debian.org/debian trixie/main arm64 base-files arm64 13.8+deb13u6 [73.3 kB]

0% [1 base-files 0 B/73.3 kB 0%] [Connecting to archive.raspberrypi.com (93.93.
                                                                               
0% [Connecting to archive.raspberrypi.com (93.93.135.117)]
                                                          
Get:2 http://deb.debian.org/debian trixie/main arm64 python3.13-venv arm64 3.13.5-2+deb13u3 [5480 B]

0% [2 python3.13-venv 0 B/5480 B 0%] [Connecting to archive.raspberrypi.com (93
                                                                               
1% [Connecting to archive.raspberrypi.com (93.93.135.117)]
                                                          
Get:3 http://deb.debian.org/debian trixie/main arm64 libpython3.13 arm64 3.13.5-2+deb13u3 [1978 kB]

1% [3 libpython3.13 0 B/1978 kB 0%] [Connecting to archive.raspberrypi.com (93.
                                                                               
Get:4 http://archive.raspberrypi.com/debian trixie/main arm64 firmware-atheros all 1:20260519-1~bpo13+1+rpt1 [38.0 MB]

1% [3 libpython3.13 220 kB/1978 kB 11%] [4 firmware-atheros 2590 B/38.0 MB 0%]
2% [3 libpython3.13 1821 kB/1978 kB 92%] [4 firmware-atheros 159 kB/38.0 MB 0%]
                                                                               
3% [4 firmware-atheros 396 kB/38.0 MB 1%]
                                         
Get:5 http://deb.debian.org/debian trixie/main arm64 python3.13 arm64 3.13.5-2+deb13u3 [757 kB]

3% [5 python3.13 37.2 kB/757 kB 5%] [4 firmware-atheros 396 kB/38.0 MB 1%]
4% [5 python3.13 404 kB/757 kB 53%] [4 firmware-atheros 1394 kB/38.0 MB 4%]
6% [5 python3.13 745 kB/757 kB 98%] [4 firmware-atheros 2988 kB/38.0 MB 8%]
                                                                           
6% [4 firmware-atheros 3022 kB/38.0 MB 8%]
                                          
Get:6 http://deb.debian.org/debian trixie/main arm64 libpython3.13-stdlib arm64 3.13.5-2+deb13u3 [1893 kB]

6% [6 libpython3.13-stdlib 24.3 kB/1893 kB 1%] [4 firmware-atheros 3022 kB/38.0
7% [6 libpython3.13-stdlib 336 kB/1893 kB 18%] [4 firmware-atheros 4491 kB/38.0
8% [6 libpython3.13-stdlib 663 kB/1893 kB 35%] [4 firmware-atheros 5647 kB/38.0
10% [6 libpython3.13-stdlib 970 kB/1893 kB 51%] [4 firmware-atheros 6947 kB/38.
11% [6 libpython3.13-stdlib 1372 kB/1893 kB 72%] [4 firmware-atheros 8067 kB/38
12% [6 libpython3.13-stdlib 1694 kB/1893 kB 89%] [4 firmware-atheros 9580 kB/38
                                                                               
13% [4 firmware-atheros 10.3 MB/38.0 MB 27%]
                                            
Get:7 http://deb.debian.org/debian trixie/main arm64 python3.13-minimal arm64 3.13.5-2+deb13u3 [2003 kB]

13% [7 python3.13-minimal 8192 B/2003 kB 0%] [4 firmware-atheros 10.3 MB/38.0 M
15% [7 python3.13-minimal 392 kB/2003 kB 20%] [4 firmware-atheros 11.7 MB/38.0 
16% [7 python3.13-minimal 726 kB/2003 kB 36%] [4 firmware-atheros 13.0 MB/38.0 
17% [7 python3.13-minimal 1059 kB/2003 kB 53%] [4 firmware-atheros 14.3 MB/38.0
18% [7 python3.13-minimal 1439 kB/2003 kB 72%] [4 firmware-atheros 15.5 MB/38.0
20% [7 python3.13-minimal 1820 kB/2003 kB 91%] [4 firmware-atheros 16.7 MB/38.0
21% [4 firmware-atheros 17.5 MB/38.0 MB 46%]                      3170 kB/s 25s
                                                                               
Get:8 http://deb.debian.org/debian trixie/main arm64 libpython3.13-minimal arm64 3.13.5-2+deb13u3 [856 kB]

21% [8 libpython3.13-minimal 35.3 kB/856 kB 4%] [4 firmware-atheros 17.5 MB/38.
22% [8 libpython3.13-minimal 496 kB/856 kB 58%] [4 firmware-atheros 18.7 MB/38.
23% [8 libpython3.13-minimal 856 kB/856 kB 100%] [4 firmware-atheros 19.9 MB/38
24% [4 firmware-atheros 19.9 MB/38.0 MB 53%]                      3170 kB/s 24s
                                                                               
Get:9 http://deb.debian.org/debian trixie/main arm64 liblzma5 arm64 5.8.1-1+deb13u1 [303 kB]

24% [9 liblzma5 3562 B/303 kB 1%] [4 firmware-atheros 20.0 MB/38.0 MB 53%]
25% [4 firmware-atheros 20.8 MB/38.0 MB 55%]                      3170 kB/s 23s
                                                                               
Get:10 http://deb.debian.org/debian trixie/main arm64 rsync arm64 3.4.1+ds1-5+deb13u4 [414 kB]

25% [10 rsync 10.8 kB/414 kB 3%] [4 firmware-atheros 20.9 MB/38.0 MB 55%]
26% [10 rsync 353 kB/414 kB 85%] [4 firmware-atheros 22.1 MB/38.0 MB 58%]
27% [4 firmware-atheros 22.4 MB/38.0 MB 59%]                      3170 kB/s 23s
                                                                               
Get:11 http://deb.debian.org/debian trixie/main arm64 dhcpcd-base arm64 1:10.1.0-11+deb13u3 [188 kB]

27% [11 dhcpcd-base 2888 B/188 kB 2%] [4 firmware-atheros 22.5 MB/38.0 MB 59%]
28% [4 firmware-atheros 23.2 MB/38.0 MB 61%]                      3170 kB/s 22s
                                                                               
Get:12 http://deb.debian.org/debian trixie/main arm64 xz-utils arm64 5.8.1-1+deb13u1 [658 kB]

28% [12 xz-utils 7220 B/658 kB 1%] [4 firmware-atheros 23.5 MB/38.0 MB 62%]
29% [12 xz-utils 277 kB/658 kB 42%] [4 firmware-atheros 24.8 MB/38.0 MB 65%]
31% [12 xz-utils 529 kB/658 kB 80%] [4 firmware-atheros 26.2 MB/38.0 MB 69%]
32% [4 firmware-atheros 26.7 MB/38.0 MB 70%]                      3170 kB/s 21s
                                                                               
Get:13 http://deb.debian.org/debian trixie/main arm64 libssh2-1t64 arm64 1.11.1-1+deb13u1 [236 kB]

32% [13 libssh2-1t64 9340 B/236 kB 4%] [4 firmware-atheros 27.0 MB/38.0 MB 71%]
33% [4 firmware-atheros 27.9 MB/38.0 MB 74%]                      3170 kB/s 21s
                                                                               
Get:14 http://deb.debian.org/debian trixie/main arm64 curl arm64 8.14.1-2+deb13u4 [262 kB]

33% [14 curl 1444 B/262 kB 1%] [4 firmware-atheros 27.9 MB/38.0 MB 74%]
34% [14 curl 256 kB/262 kB 97%] [4 firmware-atheros 29.3 MB/38.0 MB 77%]
35% [4 firmware-atheros 29.5 MB/38.0 MB 78%]                      3170 kB/s 20s
                                                                               
Get:15 http://deb.debian.org/debian trixie/main arm64 libcurl4t64 arm64 8.14.1-2+deb13u4 [360 kB]

35% [15 libcurl4t64 1444 B/360 kB 0%] [4 firmware-atheros 29.6 MB/38.0 MB 78%]
36% [4 firmware-atheros 29.8 MB/38.0 MB 78%]                      3138 kB/s 20s
                                                                               
Get:16 http://deb.debian.org/debian trixie/main arm64 gpgsm arm64 2.4.7-21+deb13u1+b4 [252 kB]

36% [16 gpgsm 0 B/252 kB 0%] [4 firmware-atheros 29.8 MB/38.0 MB 78%]
                                                                     
36% [Waiting for headers] [4 firmware-atheros 29.9 MB/38.0 MB 79%]
                                                                  
Get:17 http://deb.debian.org/debian trixie/main arm64 gnupg-utils arm64 2.4.7-21+deb13u1+b4 [181 kB]

36% [17 gnupg-utils 14.4 kB/181 kB 8%] [4 firmware-atheros 30.0 MB/38.0 MB 79%]
37% [4 firmware-atheros 30.1 MB/38.0 MB 79%]                      3138 kB/s 20s
                                                                               
Get:18 http://deb.debian.org/debian trixie/main arm64 gpg-wks-client arm64 2.4.7-21+deb13u1+b4 [102 kB]

37% [18 gpg-wks-client 2576 B/102 kB 3%] [4 firmware-atheros 30.1 MB/38.0 MB 79
38% [4 firmware-atheros 30.5 MB/38.0 MB 80%]                      3138 kB/s 20s
                                                                               
Get:19 http://deb.debian.org/debian trixie/main arm64 dirmngr arm64 2.4.7-21+deb13u1+b4 [359 kB]

38% [19 dirmngr 2783 B/359 kB 1%] [4 firmware-atheros 30.5 MB/38.0 MB 80%]
39% [19 dirmngr 251 kB/359 kB 70%] [4 firmware-atheros 32.0 MB/38.0 MB 84%]
40% [4 firmware-atheros 32.3 MB/38.0 MB 85%]                      3138 kB/s 19s
                                                                               
Get:20 http://deb.debian.org/debian trixie/main arm64 gpg arm64 2.4.7-21+deb13u1+b4 [579 kB]

40% [20 gpg 10.1 kB/579 kB 2%] [4 firmware-atheros 32.3 MB/38.0 MB 85%]
41% [20 gpg 303 kB/579 kB 52%] [4 firmware-atheros 33.7 MB/38.0 MB 89%]
43% [4 firmware-atheros 35.0 MB/38.0 MB 92%]                      3138 kB/s 18s
                                                                               
Get:21 http://deb.debian.org/debian trixie/main arm64 gpgconf arm64 2.4.7-21+deb13u1+b4 [122 kB]

43% [21 gpgconf 16.6 kB/122 kB 14%] [4 firmware-atheros 35.0 MB/38.0 MB 92%]
43% [4 firmware-atheros 35.3 MB/38.0 MB 93%]                      3138 kB/s 18s
                                                                               
Get:22 http://deb.debian.org/debian trixie/main arm64 gpg-agent arm64 2.4.7-21+deb13u1+b4 [249 kB]

43% [22 gpg-agent 0 B/249 kB 0%] [4 firmware-atheros 35.4 MB/38.0 MB 93%]
44% [4 firmware-atheros 36.2 MB/38.0 MB 95%]                      3138 kB/s 17s
                                                                               
Get:23 http://deb.debian.org/debian trixie/main arm64 gpgv arm64 2.4.7-21+deb13u1+b4 [221 kB]

44% [23 gpgv 674 B/221 kB 0%] [4 firmware-atheros 36.2 MB/38.0 MB 95%]
46% [4 firmware-atheros 37.2 MB/38.0 MB 98%]                      3138 kB/s 17s
                                                                               
Get:24 http://deb.debian.org/debian trixie/main arm64 libcurl3t64-gnutls arm64 8.14.1-2+deb13u4 [354 kB]

46% [24 libcurl3t64-gnutls 0 B/354 kB 0%] [4 firmware-atheros 37.3 MB/38.0 MB 9
47% [4 firmware-atheros 38.0 MB/38.0 MB 100%]                     3138 kB/s 17s
                                                                               
Get:25 http://deb.debian.org/debian trixie/main arm64 libnss3 arm64 2:3.110-1+deb13u3 [1292 kB]

47% [25 libnss3 0 B/1292 kB 0%] [4 firmware-atheros 38.0 MB/38.0 MB 100%]
48% [25 libnss3 481 kB/1292 kB 37%]                               3138 kB/s 16s
                                                                               
Get:26 http://archive.raspberrypi.com/debian trixie/main arm64 firmware-brcm80211 all 1:20260519-1~bpo13+1+rpt1 [5942 kB]

48% [25 libnss3 858 kB/1292 kB 66%] [26 firmware-brcm80211 1182 B/5942 kB 0%]
49% [25 libnss3 1281 kB/1292 kB 99%] [26 firmware-brcm80211 805 kB/5942 kB 14%]
49% [26 firmware-brcm80211 805 kB/5942 kB 14%]                    3138 kB/s 16s
                                                                               
Get:27 http://deb.debian.org/debian-security trixie-security/main arm64 ntfs-3g arm64 1:2022.10.3-5+deb13u2 [377 kB]

49% [27 ntfs-3g 0 B/377 kB 0%] [26 firmware-brcm80211 805 kB/5942 kB 14%]
51% [27 ntfs-3g 352 kB/377 kB 93%] [26 firmware-brcm80211 2561 kB/5942 kB 43%]
51% [26 firmware-brcm80211 2621 kB/5942 kB 44%]                   3138 kB/s 15s
                                                                               
Get:28 http://deb.debian.org/debian-security trixie-security/main arm64 libntfs-3g89t64 arm64 1:2022.10.3-5+deb13u2 [152 kB]

51% [28 libntfs-3g89t64 10.1 kB/152 kB 7%] [26 firmware-brcm80211 2650 kB/5942 
52% [26 firmware-brcm80211 2967 kB/5942 kB 50%]                   3138 kB/s 15s
                                                                               
Get:29 http://deb.debian.org/debian trixie/main arm64 libtalloc2 arm64 2:2.4.3+samba4.22.10+dfsg-0+deb13u1 [62.0 kB]

52% [29 libtalloc2 347 B/62.0 kB 1%] [26 firmware-brcm80211 2967 kB/5942 kB 50%
52% [26 firmware-brcm80211 2983 kB/5942 kB 50%]                   3138 kB/s 15s
                                                                               
Get:30 http://deb.debian.org/debian trixie/main arm64 libtasn1-6 arm64 4.20.0-2+deb13u1 [47.3 kB]

52% [30 libtasn1-6 1072 B/47.3 kB 2%] [26 firmware-brcm80211 2983 kB/5942 kB 50
53% [26 firmware-brcm80211 3300 kB/5942 kB 56%]                   3138 kB/s 15s
                                                                               
Get:31 http://deb.debian.org/debian trixie/main arm64 libwbclient0 arm64 2:4.22.10+dfsg-0+deb13u1 [70.8 kB]

53% [31 libwbclient0 652 B/70.8 kB 1%] [26 firmware-brcm80211 3300 kB/5942 kB 5
54% [26 firmware-brcm80211 3830 kB/5942 kB 64%]                   3138 kB/s 15s
                                                                               
Get:32 http://deb.debian.org/debian trixie/main arm64 libxml2 arm64 2.12.7+dfsg+really2.9.14-2.1+deb13u3 [631 kB]

54% [32 libxml2 2767 B/631 kB 0%] [26 firmware-brcm80211 3837 kB/5942 kB 65%]
55% [32 libxml2 331 kB/631 kB 52%] [26 firmware-brcm80211 5046 kB/5942 kB 85%]
56% [26 firmware-brcm80211 5942 kB/5942 kB 100%]                  3151 kB/s 14s
                                                                               
Get:33 http://deb.debian.org/debian trixie/main arm64 python3-idna all 3.10-1+deb13u1 [43.0 kB]

56% [33 python3-idna 4488 B/43.0 kB 10%] [26 firmware-brcm80211 5942 kB/5942 kB
57% [26 firmware-brcm80211 5942 kB/5942 kB 100%]                  3151 kB/s 14s
                                                                               
Get:34 http://deb.debian.org/debian trixie/main arm64 python3-urllib3 all 2.3.0-3+deb13u2 [115 kB]

57% [34 python3-urllib3 2562 B/115 kB 2%] [26 firmware-brcm80211 5942 kB/5942 k
57% [26 firmware-brcm80211 5942 kB/5942 kB 100%]                  3151 kB/s 14s
                                                                               
Get:35 http://deb.debian.org/debian trixie/main arm64 wireless-regdb all 2026.05.30-1~deb13u1 [12.4 kB]

57% [35 wireless-regdb 533 B/12.4 kB 4%] [26 firmware-brcm80211 5942 kB/5942 kB
58% [26 firmware-brcm80211 5942 kB/5942 kB 100%]                  3151 kB/s 14s
58% [Working]                                                     3151 kB/s 14s
                                                                               
Get:36 http://archive.raspberrypi.com/debian trixie/main arm64 firmware-libertas all 1:20260519-1~bpo13+1+rpt1 [3637 kB]

58% [36 firmware-libertas 15.0 kB/3637 kB 0%]                     3151 kB/s 14s
60% [36 firmware-libertas 2202 kB/3637 kB 61%]                    3151 kB/s 13s
60% [36 firmware-libertas 3191 kB/3637 kB 88%]                    3151 kB/s 13s
61% [Working]                                                     3151 kB/s 13s
                                                                               
Get:37 http://archive.raspberrypi.com/debian trixie/main arm64 firmware-mediatek all 1:20260519-1~bpo13+1+rpt1 [25.9 MB]

61% [37 firmware-mediatek 12.6 kB/25.9 MB 0%]                     3151 kB/s 13s
63% [37 firmware-mediatek 2212 kB/25.9 MB 9%]                     3151 kB/s 12s
64% [37 firmware-mediatek 3788 kB/25.9 MB 15%]                    3151 kB/s 11s
65% [37 firmware-mediatek 5224 kB/25.9 MB 20%]                    3151 kB/s 11s
67% [37 firmware-mediatek 7057 kB/25.9 MB 27%]                    3151 kB/s 10s
68% [37 firmware-mediatek 8676 kB/25.9 MB 33%]                    3151 kB/s 10s
69% [37 firmware-mediatek 10.3 MB/25.9 MB 40%]                     3151 kB/s 9s
70% [37 firmware-mediatek 11.7 MB/25.9 MB 45%]                     3151 kB/s 9s
72% [37 firmware-mediatek 13.5 MB/25.9 MB 52%]                     3151 kB/s 8s
73% [37 firmware-mediatek 15.1 MB/25.9 MB 58%]                     3151 kB/s 8s
74% [37 firmware-mediatek 16.7 MB/25.9 MB 65%]                     3169 kB/s 7s
75% [37 firmware-mediatek 18.2 MB/25.9 MB 70%]                     3169 kB/s 7s
76% [37 firmware-mediatek 19.9 MB/25.9 MB 77%]                     3169 kB/s 6s
78% [37 firmware-mediatek 21.5 MB/25.9 MB 83%]                     3169 kB/s 6s
78% [37 firmware-mediatek 22.3 MB/25.9 MB 86%]                     3169 kB/s 5s
79% [37 firmware-mediatek 23.5 MB/25.9 MB 91%]                     3169 kB/s 5s
80% [37 firmware-mediatek 24.9 MB/25.9 MB 96%]                     3169 kB/s 5s
81% [37 firmware-mediatek 25.9 MB/25.9 MB 100%]                    3169 kB/s 4s
81% [37 firmware-mediatek 25.9 MB/25.9 MB 100%]                    3169 kB/s 4s
81% [Working]                                                      3169 kB/s 4s
                                                                               
Get:38 http://archive.raspberrypi.com/debian trixie/main arm64 firmware-realtek all 1:20260519-1~bpo13+1+rpt1 [3540 kB]

81% [38 firmware-realtek 9532 B/3540 kB 0%]                        3169 kB/s 4s
85% [Working]                                                      3169 kB/s 3s
                                                                               
Get:39 http://archive.raspberrypi.com/debian trixie/main arm64 libdtovl0 arm64 20260626-1 [30.0 kB]

85% [39 libdtovl0 12.3 kB/30.0 kB 41%]                             3169 kB/s 3s
85% [Working]                                                      3169 kB/s 3s
                                                                               
Get:40 http://archive.raspberrypi.com/debian trixie/main arm64 libgpiolib0 arm64 20260626-1 [41.0 kB]

85% [40 libgpiolib0 36.9 kB/41.0 kB 90%]                           3169 kB/s 3s
85% [Working]                                                      3169 kB/s 3s
                                                                               
Get:41 http://archive.raspberrypi.com/debian trixie/main arm64 libpisp1 arm64 1.6.0-1 [312 kB]

85% [41 libpisp1 1876 B/312 kB 1%]                                 3169 kB/s 3s
86% [Working]                                                      3169 kB/s 3s
                                                                               
Get:42 http://archive.raspberrypi.com/debian trixie/main arm64 libpisp-common all 1.6.0-1 [8942 B]

86% [42 libpisp-common 8942 B/8942 B 100%]                         3169 kB/s 3s
86% [Working]                                                      3169 kB/s 3s
                                                                               
Get:43 http://archive.raspberrypi.com/debian trixie/main arm64 librpieepromab0 arm64 20260626-1 [14.8 kB]

86% [43 librpieepromab0 8192 B/14.8 kB 55%]                        3169 kB/s 3s
87% [Working]                                                      3169 kB/s 3s
                                                                               
Get:44 http://archive.raspberrypi.com/debian trixie/main arm64 librpifwcrypto0 arm64 20260626-1 [13.8 kB]

87% [44 librpifwcrypto0 13.8 kB/13.8 kB 100%]                      3169 kB/s 3s
87% [Working]                                                      3169 kB/s 3s
                                                                               
Get:45 http://archive.raspberrypi.com/debian trixie/main arm64 raspi-utils-core arm64 20260626-1 [41.4 kB]

87% [45 raspi-utils-core 8192 B/41.4 kB 20%]                       3169 kB/s 3s
87% [Working]                                                      3169 kB/s 3s
                                                                               
Get:46 http://archive.raspberrypi.com/debian trixie/main arm64 raspinfo all 20260626-1 [10.6 kB]

87% [46 raspinfo 3015 B/10.6 kB 29%]                               3169 kB/s 3s
88% [Working]                                                      3169 kB/s 3s
                                                                               
Get:47 http://archive.raspberrypi.com/debian trixie/main arm64 raspi-utils-otp all 20260626-1 [10.3 kB]

88% [47 raspi-utils-otp 10.3 kB/10.3 kB 100%]                      3169 kB/s 3s
88% [Working]                                                      3169 kB/s 3s
                                                                               
Get:48 http://archive.raspberrypi.com/debian trixie/main arm64 raspi-utils-eeprom arm64 20260626-1 [27.6 kB]

88% [48 raspi-utils-eeprom 1186 B/27.6 kB 4%]                      3169 kB/s 3s
88% [Working]                                                      3169 kB/s 3s
                                                                               
Get:49 http://archive.raspberrypi.com/debian trixie/main arm64 raspi-utils-dt arm64 20260626-1 [54.9 kB]

88% [49 raspi-utils-dt 9874 B/54.9 kB 18%]                         3169 kB/s 3s
89% [Working]                                                      3169 kB/s 3s
                                                                               
Get:50 http://archive.raspberrypi.com/debian trixie/main arm64 raspi-utils all 20260626-1 [7794 B]

89% [50 raspi-utils 7794 B/7794 B 100%]                            3169 kB/s 3s
89% [Working]                                                      3169 kB/s 3s
                                                                               
Get:51 http://archive.raspberrypi.com/debian trixie/main arm64 rpi-connect-lite arm64 2.12.1 [8459 kB]

89% [51 rpi-connect-lite 1663 B/8459 kB 0%]                        3169 kB/s 3s
90% [51 rpi-connect-lite 1590 kB/8459 kB 19%]                      3169 kB/s 3s
92% [51 rpi-connect-lite 3208 kB/8459 kB 38%]                      3169 kB/s 2s
93% [51 rpi-connect-lite 4806 kB/8459 kB 57%]                      2860 kB/s 2s
94% [51 rpi-connect-lite 6470 kB/8459 kB 76%]                      2860 kB/s 1s
95% [51 rpi-connect-lite 8060 kB/8459 kB 95%]                      2860 kB/s 1s
96% [51 rpi-connect-lite 8459 kB/8459 kB 100%]                     2860 kB/s 0s
96% [Working]                                                      2860 kB/s 0s
                                                                               
Get:52 http://archive.raspberrypi.com/debian trixie/main arm64 rpi-eeprom all 28.28-1 [2691 kB]

96% [52 rpi-eeprom 16.1 kB/2691 kB 1%]                             2860 kB/s 0s
98% [52 rpi-eeprom 2691 kB/2691 kB 100%]                           2860 kB/s 0s
99% [Working]                                                      2860 kB/s 0s
                                                                               
Get:53 http://archive.raspberrypi.com/debian trixie/main arm64 rpi-loop-utils all 1.2.3 [7872 B]

99% [53 rpi-loop-utils 4096 B/7872 B 52%]                          2860 kB/s 0s
99% [Working]                                                      2860 kB/s 0s
                                                                               
Get:54 http://archive.raspberrypi.com/debian trixie/main arm64 rpi-swap all 1.2.3 [17.1 kB]

99% [54 rpi-swap 17.1 kB/17.1 kB 100%]                             2860 kB/s 0s
99% [Working]                                                      2860 kB/s 0s
                                                                               
Get:55 http://archive.raspberrypi.com/debian trixie/main arm64 rpieepromab arm64 20260626-1 [14.9 kB]

99% [55 rpieepromab 14.9 kB/14.9 kB 100%]                          2860 kB/s 0s
100% [Working]                                                     2860 kB/s 0s
                                                                               
Get:56 http://archive.raspberrypi.com/debian trixie/main arm64 rpifwcrypto arm64 20260626-1 [15.4 kB]

100% [56 rpifwcrypto 15.4 kB/15.4 kB 100%]                         2860 kB/s 0s
100% [Working]                                                     2860 kB/s 0s
                                                                               
Fetched 104 MB in 34s (3095 kB/s)
apt-listchanges: Reading changelogs...
(Reading database ... 
(Reading database ... 5%
(Reading database ... 10%
(Reading database ... 15%
(Reading database ... 20%
(Reading database ... 25%
(Reading database ... 30%
(Reading database ... 35%
(Reading database ... 40%
(Reading database ... 45%
(Reading database ... 50%
(Reading database ... 55%
(Reading database ... 60%
(Reading database ... 65%
(Reading database ... 70%
(Reading database ... 75%
(Reading database ... 80%
(Reading database ... 85%
(Reading database ... 90%
(Reading database ... 95%
(Reading database ... 100%
(Reading database ... 66501 files and directories currently installed.)
Preparing to unpack .../base-files_13.8+deb13u6_arm64.deb ...
Unpacking base-files (13.8+deb13u6) over (13.8+deb13u5) ...
Setting up base-files (13.8+deb13u6) ...
Installing new version of config file /etc/debian_version ...
(Reading database ... 
(Reading database ... 5%
(Reading database ... 10%
(Reading database ... 15%
(Reading database ... 20%
(Reading database ... 25%
(Reading database ... 30%
(Reading database ... 35%
(Reading database ... 40%
(Reading database ... 45%
(Reading database ... 50%
(Reading database ... 55%
(Reading database ... 60%
(Reading database ... 65%
(Reading database ... 70%
(Reading database ... 75%
(Reading database ... 80%
(Reading database ... 85%
(Reading database ... 90%
(Reading database ... 95%
(Reading database ... 100%
(Reading database ... 66501 files and directories currently installed.)
Preparing to unpack .../0-python3.13-venv_3.13.5-2+deb13u3_arm64.deb ...
Unpacking python3.13-venv (3.13.5-2+deb13u3) over (3.13.5-2+deb13u2) ...
Preparing to unpack .../1-libpython3.13_3.13.5-2+deb13u3_arm64.deb ...
Unpacking libpython3.13:arm64 (3.13.5-2+deb13u3) over (3.13.5-2+deb13u2) ...
Preparing to unpack .../2-python3.13_3.13.5-2+deb13u3_arm64.deb ...
Unpacking python3.13 (3.13.5-2+deb13u3) over (3.13.5-2+deb13u2) ...
Preparing to unpack .../3-libpython3.13-stdlib_3.13.5-2+deb13u3_arm64.deb ...
Unpacking libpython3.13-stdlib:arm64 (3.13.5-2+deb13u3) over (3.13.5-2+deb13u2) ...
Preparing to unpack .../4-python3.13-minimal_3.13.5-2+deb13u3_arm64.deb ...
Unpacking python3.13-minimal (3.13.5-2+deb13u3) over (3.13.5-2+deb13u2) ...
Preparing to unpack .../5-libpython3.13-minimal_3.13.5-2+deb13u3_arm64.deb ...
Unpacking libpython3.13-minimal:arm64 (3.13.5-2+deb13u3) over (3.13.5-2+deb13u2) ...
Preparing to unpack .../6-liblzma5_5.8.1-1+deb13u1_arm64.deb ...
Unpacking liblzma5:arm64 (5.8.1-1+deb13u1) over (5.8.1-1) ...
Setting up liblzma5:arm64 (5.8.1-1+deb13u1) ...
(Reading database ... 
(Reading database ... 5%
(Reading database ... 10%
(Reading database ... 15%
(Reading database ... 20%
(Reading database ... 25%
(Reading database ... 30%
(Reading database ... 35%
(Reading database ... 40%
(Reading database ... 45%
(Reading database ... 50%
(Reading database ... 55%
(Reading database ... 60%
(Reading database ... 65%
(Reading database ... 70%
(Reading database ... 75%
(Reading database ... 80%
(Reading database ... 85%
(Reading database ... 90%
(Reading database ... 95%
(Reading database ... 100%
(Reading database ... 66501 files and directories currently installed.)
Preparing to unpack .../00-rsync_3.4.1+ds1-5+deb13u4_arm64.deb ...
Unpacking rsync (3.4.1+ds1-5+deb13u4) over (3.4.1+ds1-5+deb13u3) ...
Preparing to unpack .../01-dhcpcd-base_1%3a10.1.0-11+deb13u3_arm64.deb ...
Unpacking dhcpcd-base (1:10.1.0-11+deb13u3) over (1:10.1.0-11+deb13u2) ...
Preparing to unpack .../02-xz-utils_5.8.1-1+deb13u1_arm64.deb ...
Unpacking xz-utils (5.8.1-1+deb13u1) over (5.8.1-1) ...
Preparing to unpack .../03-libssh2-1t64_1.11.1-1+deb13u1_arm64.deb ...
Unpacking libssh2-1t64:arm64 (1.11.1-1+deb13u1) over (1.11.1-1) ...
Preparing to unpack .../04-curl_8.14.1-2+deb13u4_arm64.deb ...
Unpacking curl (8.14.1-2+deb13u4) over (8.14.1-2+deb13u3) ...
Preparing to unpack .../05-libcurl4t64_8.14.1-2+deb13u4_arm64.deb ...
Unpacking libcurl4t64:arm64 (8.14.1-2+deb13u4) over (8.14.1-2+deb13u3) ...
Preparing to unpack .../06-gpgsm_2.4.7-21+deb13u1+b4_arm64.deb ...
Unpacking gpgsm (2.4.7-21+deb13u1+b4) over (2.4.7-21+deb13u1+b3) ...
Preparing to unpack .../07-gnupg-utils_2.4.7-21+deb13u1+b4_arm64.deb ...
Unpacking gnupg-utils (2.4.7-21+deb13u1+b4) over (2.4.7-21+deb13u1+b3) ...
Preparing to unpack .../08-gpg-wks-client_2.4.7-21+deb13u1+b4_arm64.deb ...
Unpacking gpg-wks-client (2.4.7-21+deb13u1+b4) over (2.4.7-21+deb13u1+b3) ...
Preparing to unpack .../09-dirmngr_2.4.7-21+deb13u1+b4_arm64.deb ...
Unpacking dirmngr (2.4.7-21+deb13u1+b4) over (2.4.7-21+deb13u1+b3) ...
Preparing to unpack .../10-gpg_2.4.7-21+deb13u1+b4_arm64.deb ...
Unpacking gpg (2.4.7-21+deb13u1+b4) over (2.4.7-21+deb13u1+b3) ...
Preparing to unpack .../11-gpgconf_2.4.7-21+deb13u1+b4_arm64.deb ...
Unpacking gpgconf (2.4.7-21+deb13u1+b4) over (2.4.7-21+deb13u1+b3) ...
Preparing to unpack .../12-gpg-agent_2.4.7-21+deb13u1+b4_arm64.deb ...
Unpacking gpg-agent (2.4.7-21+deb13u1+b4) over (2.4.7-21+deb13u1+b3) ...
Preparing to unpack .../13-firmware-atheros_1%3a20260519-1~bpo13+1+rpt1_all.deb ...
Unpacking firmware-atheros (1:20260519-1~bpo13+1+rpt1) over (1:20250410-2+rpt1) ...
Preparing to unpack .../14-firmware-brcm80211_1%3a20260519-1~bpo13+1+rpt1_all.deb ...
Unpacking firmware-brcm80211 (1:20260519-1~bpo13+1+rpt1) over (1:20250410-2+rpt1) ...
Preparing to unpack .../15-firmware-libertas_1%3a20260519-1~bpo13+1+rpt1_all.deb ...
Unpacking firmware-libertas (1:20260519-1~bpo13+1+rpt1) over (1:20250410-2+rpt1) ...
Preparing to unpack .../16-firmware-mediatek_1%3a20260519-1~bpo13+1+rpt1_all.deb ...
Unpacking firmware-mediatek (1:20260519-1~bpo13+1+rpt1) over (1:20250410-2+rpt1) ...
Preparing to unpack .../17-firmware-realtek_1%3a20260519-1~bpo13+1+rpt1_all.deb ...
Unpacking firmware-realtek (1:20260519-1~bpo13+1+rpt1) over (1:20250410-2+rpt1) ...
Preparing to unpack .../18-gpgv_2.4.7-21+deb13u1+b4_arm64.deb ...
Unpacking gpgv (2.4.7-21+deb13u1+b4) over (2.4.7-21+deb13u1+b3) ...
Preparing to unpack .../19-libcurl3t64-gnutls_8.14.1-2+deb13u4_arm64.deb ...
Unpacking libcurl3t64-gnutls:arm64 (8.14.1-2+deb13u4) over (8.14.1-2+deb13u3) ...
Preparing to unpack .../20-libdtovl0_20260626-1_arm64.deb ...
Unpacking libdtovl0:arm64 (20260626-1) over (20260601-1) ...
Preparing to unpack .../21-libgpiolib0_20260626-1_arm64.deb ...
Unpacking libgpiolib0:arm64 (20260626-1) over (20260601-1) ...
Preparing to unpack .../22-libnss3_2%3a3.110-1+deb13u3_arm64.deb ...
Unpacking libnss3:arm64 (2:3.110-1+deb13u3) over (2:3.110-1+deb13u2) ...
Preparing to unpack .../23-ntfs-3g_1%3a2022.10.3-5+deb13u2_arm64.deb ...
Unpacking ntfs-3g (1:2022.10.3-5+deb13u2) over (1:2022.10.3-5+deb13u1) ...
Preparing to unpack .../24-libntfs-3g89t64_1%3a2022.10.3-5+deb13u2_arm64.deb ...
Adding 'diversion of /lib/aarch64-linux-gnu/libntfs-3g.so.89 to /lib/aarch64-linux-gnu/libntfs-3g.so.89.usr-is-merged by libntfs-3g89t64'
Adding 'diversion of /lib/aarch64-linux-gnu/libntfs-3g.so.89.0.0 to /lib/aarch64-linux-gnu/libntfs-3g.so.89.0.0.usr-is-merged by libntfs-3g89t64'
Unpacking libntfs-3g89t64:arm64 (1:2022.10.3-5+deb13u2) over (1:2022.10.3-5+deb13u1) ...
Preparing to unpack .../25-libpisp1_1.6.0-1_arm64.deb ...
Unpacking libpisp1:arm64 (1.6.0-1) over (1.5.0-1) ...
Preparing to unpack .../26-libpisp-common_1.6.0-1_all.deb ...
Unpacking libpisp-common (1.6.0-1) over (1.5.0-1) ...
Preparing to unpack .../27-librpieepromab0_20260626-1_arm64.deb ...
Unpacking librpieepromab0:arm64 (20260626-1) over (20260601-1) ...
Preparing to unpack .../28-librpifwcrypto0_20260626-1_arm64.deb ...
Unpacking librpifwcrypto0:arm64 (20260626-1) over (20260601-1) ...
Preparing to unpack .../29-libtalloc2_2%3a2.4.3+samba4.22.10+dfsg-0+deb13u1_arm64.deb ...
Unpacking libtalloc2:arm64 (2:2.4.3+samba4.22.10+dfsg-0+deb13u1) over (2:2.4.3+samba4.22.8+dfsg-0+deb13u2) ...
Preparing to unpack .../30-libtasn1-6_4.20.0-2+deb13u1_arm64.deb ...
Unpacking libtasn1-6:arm64 (4.20.0-2+deb13u1) over (4.20.0-2) ...
Preparing to unpack .../31-libwbclient0_2%3a4.22.10+dfsg-0+deb13u1_arm64.deb ...
Unpacking libwbclient0:arm64 (2:4.22.10+dfsg-0+deb13u1) over (2:4.22.8+dfsg-0+deb13u2) ...
Preparing to unpack .../32-libxml2_2.12.7+dfsg+really2.9.14-2.1+deb13u3_arm64.deb ...
Unpacking libxml2:arm64 (2.12.7+dfsg+really2.9.14-2.1+deb13u3) over (2.12.7+dfsg+really2.9.14-2.1+deb13u2) ...
Preparing to unpack .../33-python3-idna_3.10-1+deb13u1_all.deb ...
Unpacking python3-idna (3.10-1+deb13u1) over (3.10-1) ...
Preparing to unpack .../34-python3-urllib3_2.3.0-3+deb13u2_all.deb ...
Unpacking python3-urllib3 (2.3.0-3+deb13u2) over (2.3.0-3+deb13u1) ...
Preparing to unpack .../35-raspi-utils-core_20260626-1_arm64.deb ...
Unpacking raspi-utils-core (20260626-1) over (20260601-1) ...
Preparing to unpack .../36-raspinfo_20260626-1_all.deb ...
Unpacking raspinfo (20260626-1) over (20260601-1) ...
Preparing to unpack .../37-raspi-utils-otp_20260626-1_all.deb ...
Unpacking raspi-utils-otp (20260626-1) over (20260601-1) ...
Preparing to unpack .../38-raspi-utils-eeprom_20260626-1_arm64.deb ...
Unpacking raspi-utils-eeprom (20260626-1) over (20260601-1) ...
Preparing to unpack .../39-raspi-utils-dt_20260626-1_arm64.deb ...
Unpacking raspi-utils-dt (20260626-1) over (20260601-1) ...
Preparing to unpack .../40-raspi-utils_20260626-1_all.deb ...
Unpacking raspi-utils (20260626-1) over (20260601-1) ...
Preparing to unpack .../41-rpi-connect-lite_2.12.1_arm64.deb ...
Unpacking rpi-connect-lite (2.12.1) over (2.12.0) ...
Preparing to unpack .../42-rpi-eeprom_28.28-1_all.deb ...
Unpacking rpi-eeprom (28.28-1) over (28.27-1) ...
Preparing to unpack .../43-rpi-loop-utils_1.2.3_all.deb ...
Unpacking rpi-loop-utils (1.2.3) over (1.2.2) ...
Preparing to unpack .../44-rpi-swap_1.2.3_all.deb ...
Unpacking rpi-swap (1.2.3) over (1.2.2) ...
Preparing to unpack .../45-rpieepromab_20260626-1_arm64.deb ...
Unpacking rpieepromab (20260626-1) over (20260601-1) ...
Preparing to unpack .../46-rpifwcrypto_20260626-1_arm64.deb ...
Unpacking rpifwcrypto (20260626-1) over (20260601-1) ...
Preparing to unpack .../47-wireless-regdb_2026.05.30-1~deb13u1_all.deb ...
Unpacking wireless-regdb (2026.05.30-1~deb13u1) over (2026.02.04-1~deb13u1) ...
Setting up raspi-utils-eeprom (20260626-1) ...
Setting up raspi-utils-otp (20260626-1) ...
Setting up libntfs-3g89t64:arm64 (1:2022.10.3-5+deb13u2) ...
Removing 'diversion of /lib/aarch64-linux-gnu/libntfs-3g.so.89 to /lib/aarch64-linux-gnu/libntfs-3g.so.89.usr-is-merged by libntfs-3g89t64'
Removing 'diversion of /lib/aarch64-linux-gnu/libntfs-3g.so.89.0.0 to /lib/aarch64-linux-gnu/libntfs-3g.so.89.0.0.usr-is-merged by libntfs-3g89t64'
Setting up libdtovl0:arm64 (20260626-1) ...
Setting up wireless-regdb (2026.05.30-1~deb13u1) ...
Setting up raspi-utils-dt (20260626-1) ...
Setting up firmware-atheros (1:20260519-1~bpo13+1+rpt1) ...
Setting up libnss3:arm64 (2:3.110-1+deb13u3) ...
Setting up libwbclient0:arm64 (2:4.22.10+dfsg-0+deb13u1) ...
Setting up ntfs-3g (1:2022.10.3-5+deb13u2) ...
Setting up libtalloc2:arm64 (2:2.4.3+samba4.22.10+dfsg-0+deb13u1) ...
Setting up libpython3.13-minimal:arm64 (3.13.5-2+deb13u3) ...
Setting up firmware-brcm80211 (1:20260519-1~bpo13+1+rpt1) ...
Setting up firmware-mediatek (1:20260519-1~bpo13+1+rpt1) ...
Setting up firmware-realtek (1:20260519-1~bpo13+1+rpt1) ...
Setting up rpi-connect-lite (2.12.1) ...

For Raspberry Pi OS Lite, enable user lingering for your user:

    loginctl enable-linger

This allows users who are not logged in to run long-running services.

For information on getting started with Raspberry Pi Connect, please see the official documentation:

    https://rpltd.co/rpi-connect

Setting up xz-utils (5.8.1-1+deb13u1) ...
Setting up libpisp-common (1.6.0-1) ...
Setting up python3-idna (3.10-1+deb13u1) ...
Setting up libgpiolib0:arm64 (20260626-1) ...
Setting up dhcpcd-base (1:10.1.0-11+deb13u3) ...
Setting up librpifwcrypto0:arm64 (20260626-1) ...
Setting up python3-urllib3 (2.3.0-3+deb13u2) ...
Setting up firmware-libertas (1:20260519-1~bpo13+1+rpt1) ...
Setting up gpgv (2.4.7-21+deb13u1+b4) ...
Setting up gpgconf (2.4.7-21+deb13u1+b4) ...
Setting up libtasn1-6:arm64 (4.20.0-2+deb13u1) ...
Setting up python3.13-minimal (3.13.5-2+deb13u3) ...
Setting up libpisp1:arm64 (1.6.0-1) ...
Setting up libssh2-1t64:arm64 (1.11.1-1+deb13u1) ...
Setting up libpython3.13-stdlib:arm64 (3.13.5-2+deb13u3) ...
Setting up libxml2:arm64 (2.12.7+dfsg+really2.9.14-2.1+deb13u3) ...
Setting up gpg (2.4.7-21+deb13u1+b4) ...
Setting up rsync (3.4.1+ds1-5+deb13u4) ...
rsync.service is a disabled or a static unit not running, not starting it.
Setting up raspi-utils-core (20260626-1) ...
Setting up gnupg-utils (2.4.7-21+deb13u1+b4) ...
Setting up librpieepromab0:arm64 (20260626-1) ...
Setting up rpi-loop-utils (1.2.3) ...
Setting up libpython3.13:arm64 (3.13.5-2+deb13u3) ...
Setting up gpg-agent (2.4.7-21+deb13u1+b4) ...
Setting up raspinfo (20260626-1) ...
Setting up libcurl4t64:arm64 (8.14.1-2+deb13u4) ...
Setting up python3.13 (3.13.5-2+deb13u3) ...
Setting up gpgsm (2.4.7-21+deb13u1+b4) ...
Setting up rpieepromab (20260626-1) ...
Setting up libcurl3t64-gnutls:arm64 (8.14.1-2+deb13u4) ...
Setting up rpifwcrypto (20260626-1) ...
Setting up python3.13-venv (3.13.5-2+deb13u3) ...
Setting up raspi-utils (20260626-1) ...
Setting up rpi-swap (1.2.3) ...
Setting up dirmngr (2.4.7-21+deb13u1+b4) ...
Setting up rpi-eeprom (28.28-1) ...
Setting up curl (8.14.1-2+deb13u4) ...
Setting up gpg-wks-client (2.4.7-21+deb13u1+b4) ...
Processing triggers for systemd (257.13-1~deb13u1) ...
Processing triggers for man-db (2.13.1-1) ...
Processing triggers for initramfs-tools (0.148.4+rpt2) ...
update-initramfs: Generating /boot/initrd.img-6.18.34+rpt-rpi-v8
'/boot/initrd.img-6.18.34+rpt-rpi-v8' -> '/boot/firmware/initramfs8'
update-initramfs: Generating /boot/initrd.img-6.18.34+rpt-rpi-2712
'/boot/initrd.img-6.18.34+rpt-rpi-2712' -> '/boot/firmware/initramfs_2712'
Processing triggers for libc-bin (2.41-12+rpt1+deb13u3) ...
#+end_example

#+call: apt-autoremove()

#+RESULTS:
: Running in /home/pi host 'jrr5x' on Thu Jul 16 18:50:50 EEST 2026
: 
Reading package lists... 0%

Reading package lists... 100%

Reading package lists... Done
: 
Building dependency tree... 0%

Building dependency tree... 0%

Building dependency tree... 50%

Building dependency tree... 50%

Building dependency tree... 69%

Building dependency tree... Done
: 
Reading state information... 0% 

Reading state information... 0%

Reading state information... Done
: 0 upgraded, 0 newly installed, 0 to remove and 0 not upgraded.

** Create ~/home/pi/tmp~ directory

#+call: create-dir(DIR="tmp")

#+RESULTS:
: Create DIR=tmp in /home/pi for user 'pi' on host='jrr5x' on Thu Jul 16 18:51:05 EEST 2026
: Directory tmp created

** ~evtest~: Input device event monitor and query tool

#+call: apt-install(PKG="evtest")

#+RESULTS:
#+begin_example
Running 'sudo apt install -y evtest' in host 'jrr5x' on Thu Jul 16 18:51:10 EEST 2026

Reading package lists... 0%

Reading package lists... 100%

Building dependency tree... 0%

Building dependency tree... 0%

Building dependency tree... 50%

Building dependency tree... 50%

Building dependency tree... 68%

Reading state information... 0%

Reading state information... 0%

Reading state information... 0%
                                
Installing:
[32m  evtest
[0m
Installing dependencies:
[32m  evemu-tools  libevdev2  libevemu3t64
[0m
Summary:
  Upgrading: 0, Installing: 4, Removing: 0, Not Upgrading: 0
  Download size: 71.9 kB
  Space needed: 693 kB / 6617 MB available

[33m
0% [Working][0m
            
Get:1 http://deb.debian.org/debian trixie/main arm64 libevdev2 arm64 1.13.4+dfsg-1 [30.4 kB]
[33m
0% [1 libevdev2 0 B/30.4 kB 0%][0m[33m
                               
39% [Working][0m
             
Get:2 http://deb.debian.org/debian trixie/main arm64 libevemu3t64 arm64 2.7.0-4+b1 [11.6 kB]
[33m
39% [2 libevemu3t64 0 B/11.6 kB 0%][0m[33m
                                   
57% [Working][0m
             
Get:3 http://deb.debian.org/debian trixie/main arm64 evemu-tools arm64 2.7.0-4+b1 [14.3 kB]
[33m
70% [3 evemu-tools 11.6 kB/14.3 kB 81%][0m[33m
                                       
78% [Working][0m
             
Get:4 http://deb.debian.org/debian trixie/main arm64 evtest arm64 1:1.35-1+b1 [15.7 kB]
[33m
84% [4 evtest 6134 B/15.7 kB 39%][0m[33m
                                 
100% [Working][0m
              
Fetched 71.9 kB in 0s (836 kB/s)
debconf: unable to initialize frontend: Dialog
debconf: (Dialog frontend will not work on a dumb terminal, an emacs shell buffer, or without a controlling terminal.)
debconf: falling back to frontend: Readline
Selecting previously unselected package libevdev2:arm64.
(Reading database ... 
(Reading database ... 5%
(Reading database ... 10%
(Reading database ... 15%
(Reading database ... 20%
(Reading database ... 25%
(Reading database ... 30%
(Reading database ... 35%
(Reading database ... 40%
(Reading database ... 45%
(Reading database ... 50%
(Reading database ... 55%
(Reading database ... 60%
(Reading database ... 65%
(Reading database ... 70%
(Reading database ... 75%
(Reading database ... 80%
(Reading database ... 85%
(Reading database ... 90%
(Reading database ... 95%
(Reading database ... 100%
(Reading database ... 66582 files and directories currently installed.)
Preparing to unpack .../libevdev2_1.13.4+dfsg-1_arm64.deb ...
Unpacking libevdev2:arm64 (1.13.4+dfsg-1) ...
Selecting previously unselected package libevemu3t64:arm64.
Preparing to unpack .../libevemu3t64_2.7.0-4+b1_arm64.deb ...
Unpacking libevemu3t64:arm64 (2.7.0-4+b1) ...
Selecting previously unselected package evemu-tools.
Preparing to unpack .../evemu-tools_2.7.0-4+b1_arm64.deb ...
Unpacking evemu-tools (2.7.0-4+b1) ...
Selecting previously unselected package evtest.
Preparing to unpack .../evtest_1%3a1.35-1+b1_arm64.deb ...
Unpacking evtest (1:1.35-1+b1) ...
Setting up evtest (1:1.35-1+b1) ...
Setting up libevdev2:arm64 (1.13.4+dfsg-1) ...
Setting up libevemu3t64:arm64 (2.7.0-4+b1) ...
Setting up evemu-tools (2.7.0-4+b1) ...
Processing triggers for man-db (2.13.1-1) ...
Processing triggers for libc-bin (2.41-12+rpt1+deb13u3) ...
#+end_example

Testing evtest. Hint: connect keyboard to have something usefull to test with

#+BEGIN_SRC elisp :noweb yes :results output :eval no-export :exports none 
(start-process "server" "buf-server" "xterm"  "-T" "evtest" "-fa" "'Monospace'" "-fs" "12"  "-hold" "-e"  "bash" "-c" "ssh jrr5 sudo evtest")
#+END_SRC

#+RESULTS:

** ~python3-dev~: 
:PROPERTIES:
:header-args+: :var  PKG="python3-dev"
:END:

#+call: apt-install-doc()

#+RESULTS:
: Running 'sudo apt install -y python3-dev' in host 'jrr5x' on Thu Jul 16 18:51:33 EEST 2026
: PKG=python3-dev

#+call: apt-install()

#+RESULTS:
#+begin_example
Running 'sudo apt install -y python3-dev' in host 'jrr5x' on Thu Jul 16 18:51:38 EEST 2026

Reading package lists... 0%

Reading package lists... 100%

Building dependency tree... 0%

Building dependency tree... 0%

Building dependency tree... 50%

Building dependency tree... 50%

Building dependency tree... 68%

Reading state information... 0%

Reading state information... 0%

Reading state information... 0%
                                
Installing:
[32m  python3-dev
[0m
Installing dependencies:
[32m  javascript-common  libjs-sphinxdoc   libpython3.13-dev
  libexpat1-dev      libjs-underscore  python3.13-dev
  libjs-jquery       libpython3-dev    zlib1g-dev
[0m
Suggested packages:
  apache2  | lighttpd  | httpd

Summary:
  Upgrading: 0, Installing: 10, Removing: 0, Not Upgrading: 0
  Download size: 7009 kB
  Space needed: 29.9 MB / 6617 MB available

[33m
0% [Working][0m
            
Get:1 http://deb.debian.org/debian trixie/main arm64 javascript-common all 12+nmu1 [4864 B]
[33m
0% [1 javascript-common 4864 B/4864 B 100%][0m[33m
                                           
2% [Working][0m
            
Get:2 http://deb.debian.org/debian trixie/main arm64 libexpat1-dev arm64 2.7.1-2 [145 kB]
[33m
2% [2 libexpat1-dev 0 B/145 kB 0%][0m[33m
                                  
6% [Working][0m
            
Get:3 http://deb.debian.org/debian trixie/main arm64 libjs-jquery all 3.6.1+dfsg+~3.5.14-1 [326 kB]
[33m
6% [3 libjs-jquery 5758 B/326 kB 2%][0m[33m
                                    
11% [Working][0m
             
Get:4 http://deb.debian.org/debian trixie/main arm64 libjs-underscore all 1.13.4~dfsg+~1.11.4-3 [116 kB]
[33m
12% [4 libjs-underscore 16.6 kB/116 kB 14%][0m[33m
                                           
15% [Working][0m
             
Get:5 http://deb.debian.org/debian trixie/main arm64 libjs-sphinxdoc all 8.1.3-5 [30.5 kB]
[33m
15% [5 libjs-sphinxdoc 30.5 kB/30.5 kB 100%][0m[33m
                                            
17% [Working][0m
             
Get:6 http://deb.debian.org/debian trixie/main arm64 zlib1g-dev arm64 1:1.3.dfsg+really1.3.1-1+b1 [917 kB]
[33m
17% [6 zlib1g-dev 0 B/917 kB 0%][0m[33m
                                
30% [Working][0m
             
Get:7 http://deb.debian.org/debian trixie/main arm64 libpython3.13-dev arm64 3.13.5-2+deb13u3 [4929 kB]
[33m
30% [7 libpython3.13-dev 0 B/4929 kB 0%][0m[33m
49% [7 libpython3.13-dev 1679 kB/4929 kB 34%][0m[33m
67% [7 libpython3.13-dev 3301 kB/4929 kB 67%][0m[33m
86% [7 libpython3.13-dev 4909 kB/4929 kB 100%][0m[33m
                                              
88% [Working][0m
             
Get:8 http://deb.debian.org/debian trixie/main arm64 libpython3-dev arm64 3.13.5-1 [10.4 kB]
[33m
88% [8 libpython3-dev 1202 B/10.4 kB 12%][0m[33m
                                         
90% [Working][0m
             
Get:9 http://deb.debian.org/debian trixie/main arm64 python3.13-dev arm64 3.13.5-2+deb13u3 [504 kB]
[33m
90% [9 python3.13-dev 12.3 kB/504 kB 2%][0m[33m
                                        
98% [Working][0m
             
Get:10 http://deb.debian.org/debian trixie/main arm64 python3-dev arm64 3.13.5-1 [26.1 kB]
[33m
98% [10 python3-dev 4510 B/26.1 kB 17%][0m[33m
                                       
100% [Working][0m
              
Fetched 7009 kB in 2s (2950 kB/s)
debconf: unable to initialize frontend: Dialog
debconf: (Dialog frontend will not work on a dumb terminal, an emacs shell buffer, or without a controlling terminal.)
debconf: falling back to frontend: Readline
Selecting previously unselected package javascript-common.
(Reading database ... 
(Reading database ... 5%
(Reading database ... 10%
(Reading database ... 15%
(Reading database ... 20%
(Reading database ... 25%
(Reading database ... 30%
(Reading database ... 35%
(Reading database ... 40%
(Reading database ... 45%
(Reading database ... 50%
(Reading database ... 55%
(Reading database ... 60%
(Reading database ... 65%
(Reading database ... 70%
(Reading database ... 75%
(Reading database ... 80%
(Reading database ... 85%
(Reading database ... 90%
(Reading database ... 95%
(Reading database ... 100%
(Reading database ... 66614 files and directories currently installed.)
Preparing to unpack .../0-javascript-common_12+nmu1_all.deb ...
Unpacking javascript-common (12+nmu1) ...
Selecting previously unselected package libexpat1-dev:arm64.
Preparing to unpack .../1-libexpat1-dev_2.7.1-2_arm64.deb ...
Unpacking libexpat1-dev:arm64 (2.7.1-2) ...
Selecting previously unselected package libjs-jquery.
Preparing to unpack .../2-libjs-jquery_3.6.1+dfsg+~3.5.14-1_all.deb ...
Unpacking libjs-jquery (3.6.1+dfsg+~3.5.14-1) ...
Selecting previously unselected package libjs-underscore.
Preparing to unpack .../3-libjs-underscore_1.13.4~dfsg+~1.11.4-3_all.deb ...
Unpacking libjs-underscore (1.13.4~dfsg+~1.11.4-3) ...
Selecting previously unselected package libjs-sphinxdoc.
Preparing to unpack .../4-libjs-sphinxdoc_8.1.3-5_all.deb ...
Unpacking libjs-sphinxdoc (8.1.3-5) ...
Selecting previously unselected package zlib1g-dev:arm64.
Preparing to unpack .../5-zlib1g-dev_1%3a1.3.dfsg+really1.3.1-1+b1_arm64.deb ...
Unpacking zlib1g-dev:arm64 (1:1.3.dfsg+really1.3.1-1+b1) ...
Selecting previously unselected package libpython3.13-dev:arm64.
Preparing to unpack .../6-libpython3.13-dev_3.13.5-2+deb13u3_arm64.deb ...
Unpacking libpython3.13-dev:arm64 (3.13.5-2+deb13u3) ...
Selecting previously unselected package libpython3-dev:arm64.
Preparing to unpack .../7-libpython3-dev_3.13.5-1_arm64.deb ...
Unpacking libpython3-dev:arm64 (3.13.5-1) ...
Selecting previously unselected package python3.13-dev.
Preparing to unpack .../8-python3.13-dev_3.13.5-2+deb13u3_arm64.deb ...
Unpacking python3.13-dev (3.13.5-2+deb13u3) ...
Selecting previously unselected package python3-dev.
Preparing to unpack .../9-python3-dev_3.13.5-1_arm64.deb ...
Unpacking python3-dev (3.13.5-1) ...
Setting up javascript-common (12+nmu1) ...
Setting up libexpat1-dev:arm64 (2.7.1-2) ...
Setting up zlib1g-dev:arm64 (1:1.3.dfsg+really1.3.1-1+b1) ...
Setting up libjs-jquery (3.6.1+dfsg+~3.5.14-1) ...
Setting up libjs-underscore (1.13.4~dfsg+~1.11.4-3) ...
Setting up libpython3.13-dev:arm64 (3.13.5-2+deb13u3) ...
Setting up libjs-sphinxdoc (8.1.3-5) ...
Setting up libpython3-dev:arm64 (3.13.5-1) ...
Setting up python3.13-dev (3.13.5-2+deb13u3) ...
Setting up python3-dev (3.13.5-1) ...
Processing triggers for man-db (2.13.1-1) ...
#+end_example

** ~git~: version control
:PROPERTIES:
:header-args+: :var  PKG="git"
:END:

#+call: apt-install-doc()

#+RESULTS:
: Running 'sudo apt install -y git' in host 'jrr5x' on Thu Jul 16 18:52:08 EEST 2026
: PKG=git

#+call: apt-install()

#+RESULTS:
#+begin_example
Running 'sudo apt install -y git' in host 'jrr5x' on Thu Jul 16 18:52:18 EEST 2026

Reading package lists... 0%

Reading package lists... 100%

Building dependency tree... 0%

Building dependency tree... 0%

Building dependency tree... 50%

Building dependency tree... 50%

Building dependency tree... 68%

Building dependency tree... 99%

Reading state information... 0%

Reading state information... 0%
                                
Installing:
[32m  git
[0m
Installing dependencies:
[32m  git-man  liberror-perl
[0m
Suggested packages:
  git-doc  git-email  git-gui  gitk  gitweb  git-cvs  git-mediawiki  git-svn

Summary:
  Upgrading: 0, Installing: 3, Removing: 0, Not Upgrading: 0
  Download size: 10.9 MB
  Space needed: 53.1 MB / 6586 MB available

[33m
0% [Working][0m
            
Get:1 http://deb.debian.org/debian trixie/main arm64 liberror-perl all 0.17030-1 [26.9 kB]
[33m
0% [1 liberror-perl 0 B/26.9 kB 0%][0m[33m
                                   
7% [Working][0m
            
Get:2 http://deb.debian.org/debian trixie/main arm64 git-man all 1:2.47.3-0+deb13u1 [2205 kB]
[33m
7% [2 git-man 0 B/2205 kB 0%][0m[33m
19% [2 git-man 1688 kB/2205 kB 77%][0m[33m
                                   
30% [Working][0m
             
Get:3 http://deb.debian.org/debian trixie/main arm64 git arm64 1:2.47.3-0+deb13u1 [8666 kB]
[33m
30% [3 git 0 B/8666 kB 0%][0m[33m
43% [3 git 1854 kB/8666 kB 21%][0m[33m
55% [3 git 3464 kB/8666 kB 40%][0m[33m
67% [3 git 5088 kB/8666 kB 59%][0m[33m
79% [3 git 6694 kB/8666 kB 77%][0m[33m
91% [3 git 8317 kB/8666 kB 96%][0m[33m
93% [3 git 8666 kB/8666 kB 100%][0m[33m
                                
100% [Working][0m
              
Fetched 10.9 MB in 4s (2845 kB/s)
debconf: unable to initialize frontend: Dialog
debconf: (Dialog frontend will not work on a dumb terminal, an emacs shell buffer, or without a controlling terminal.)
debconf: falling back to frontend: Readline
Selecting previously unselected package liberror-perl.
(Reading database ... 
(Reading database ... 5%
(Reading database ... 10%
(Reading database ... 15%
(Reading database ... 20%
(Reading database ... 25%
(Reading database ... 30%
(Reading database ... 35%
(Reading database ... 40%
(Reading database ... 45%
(Reading database ... 50%
(Reading database ... 55%
(Reading database ... 60%
(Reading database ... 65%
(Reading database ... 70%
(Reading database ... 75%
(Reading database ... 80%
(Reading database ... 85%
(Reading database ... 90%
(Reading database ... 95%
(Reading database ... 100%
(Reading database ... 67062 files and directories currently installed.)
Preparing to unpack .../liberror-perl_0.17030-1_all.deb ...
Unpacking liberror-perl (0.17030-1) ...
Selecting previously unselected package git-man.
Preparing to unpack .../git-man_1%3a2.47.3-0+deb13u1_all.deb ...
Unpacking git-man (1:2.47.3-0+deb13u1) ...
Selecting previously unselected package git.
Preparing to unpack .../git_1%3a2.47.3-0+deb13u1_arm64.deb ...
Unpacking git (1:2.47.3-0+deb13u1) ...
Setting up liberror-perl (0.17030-1) ...
Setting up git-man (1:2.47.3-0+deb13u1) ...
Setting up git (1:2.47.3-0+deb13u1) ...
Processing triggers for man-db (2.13.1-1) ...
#+end_example

** ~lsof~, ~iotop~, ~sysstat~: debug tools
:PROPERTIES:
:header-args+: :var  PKG="lsof iotop sysstat"
:END:

#+call: apt-install-doc()

#+RESULTS:
: Running 'sudo apt install -y lsof iotop sysstat' in host 'jrr5x' on Thu Jul 16 18:53:09 EEST 2026
: PKG=lsof iotop sysstat

#+call: apt-install()

#+RESULTS:
#+begin_example
Running 'sudo apt install -y lsof iotop sysstat' in host 'jrr5x' on Thu Jul 16 18:53:13 EEST 2026

Reading package lists... 0%

Reading package lists... 100%

Building dependency tree... 0%

Building dependency tree... 0%

Building dependency tree... 50%

Building dependency tree... 50%

Building dependency tree... 68%

Building dependency tree... 99%

Reading state information... 0%

Reading state information... 0%
                                
Installing:
[32m  iotop  lsof  sysstat
[0m
Installing dependencies:
[32m  liblsof0  libsensors-config  libsensors5
[0m
Suggested packages:
  lm-sensors  isag

Summary:
  Upgrading: 0, Installing: 6, Removing: 0, Not Upgrading: 0
  Download size: 1108 kB
  Space needed: 3205 kB / 6530 MB available

[33m
0% [Working][0m
            
Get:1 http://deb.debian.org/debian trixie/main arm64 liblsof0 arm64 4.99.4+dfsg-2 [128 kB]
[33m
0% [1 liblsof0 0 B/128 kB 0%][0m[33m
                             
13% [Working][0m
             
Get:2 http://deb.debian.org/debian trixie/main arm64 lsof arm64 4.99.4+dfsg-2 [306 kB]
[33m
13% [2 lsof 687 B/306 kB 0%][0m[33m
                            
38% [Working][0m
             
Get:3 http://deb.debian.org/debian trixie/main arm64 iotop arm64 0.6-42-ga14256a-0.3+b1 [24.1 kB]
[33m
39% [3 iotop 20.6 kB/24.1 kB 85%][0m[33m
                                 
43% [Working][0m
             
Get:4 http://deb.debian.org/debian trixie/main arm64 libsensors-config all 1:3.6.2-2 [16.2 kB]
[33m
44% [4 libsensors-config 16.2 kB/16.2 kB 100%][0m[33m
                                              
48% [Working][0m
             
Get:5 http://deb.debian.org/debian trixie/main arm64 libsensors5 arm64 1:3.6.2-2 [36.4 kB]
[33m
50% [5 libsensors5 36.4 kB/36.4 kB 100%][0m[33m
                                        
54% [Working][0m
             
Get:6 http://deb.debian.org/debian trixie/main arm64 sysstat arm64 12.7.5-2+b2 [597 kB]
[33m
55% [6 sysstat 24.6 kB/597 kB 4%][0m[33m
                                 
100% [Working][0m
              
Fetched 1108 kB in 0s (2801 kB/s)
debconf: unable to initialize frontend: Dialog
debconf: (Dialog frontend will not work on a dumb terminal, an emacs shell buffer, or without a controlling terminal.)
debconf: falling back to frontend: Readline
Preconfiguring packages ...
Selecting previously unselected package liblsof0.
(Reading database ... 
(Reading database ... 5%
(Reading database ... 10%
(Reading database ... 15%
(Reading database ... 20%
(Reading database ... 25%
(Reading database ... 30%
(Reading database ... 35%
(Reading database ... 40%
(Reading database ... 45%
(Reading database ... 50%
(Reading database ... 55%
(Reading database ... 60%
(Reading database ... 65%
(Reading database ... 70%
(Reading database ... 75%
(Reading database ... 80%
(Reading database ... 85%
(Reading database ... 90%
(Reading database ... 95%
(Reading database ... 100%
(Reading database ... 68210 files and directories currently installed.)
Preparing to unpack .../0-liblsof0_4.99.4+dfsg-2_arm64.deb ...
Unpacking liblsof0 (4.99.4+dfsg-2) ...
Selecting previously unselected package lsof.
Preparing to unpack .../1-lsof_4.99.4+dfsg-2_arm64.deb ...
Unpacking lsof (4.99.4+dfsg-2) ...
Selecting previously unselected package iotop.
Preparing to unpack .../2-iotop_0.6-42-ga14256a-0.3+b1_arm64.deb ...
Unpacking iotop (0.6-42-ga14256a-0.3+b1) ...
Selecting previously unselected package libsensors-config.
Preparing to unpack .../3-libsensors-config_1%3a3.6.2-2_all.deb ...
Unpacking libsensors-config (1:3.6.2-2) ...
Selecting previously unselected package libsensors5:arm64.
Preparing to unpack .../4-libsensors5_1%3a3.6.2-2_arm64.deb ...
Unpacking libsensors5:arm64 (1:3.6.2-2) ...
Selecting previously unselected package sysstat.
Preparing to unpack .../5-sysstat_12.7.5-2+b2_arm64.deb ...
Unpacking sysstat (12.7.5-2+b2) ...
Setting up liblsof0 (4.99.4+dfsg-2) ...
Setting up libsensors-config (1:3.6.2-2) ...
Setting up iotop (0.6-42-ga14256a-0.3+b1) ...
update-alternatives: using /usr/sbin/iotop-py to provide /usr/sbin/iotop (iotop) in auto mode
Setting up libsensors5:arm64 (1:3.6.2-2) ...
Setting up lsof (4.99.4+dfsg-2) ...
Setting up sysstat (12.7.5-2+b2) ...
debconf: unable to initialize frontend: Dialog
debconf: (Dialog frontend will not work on a dumb terminal, an emacs shell buffer, or without a controlling terminal.)
debconf: falling back to frontend: Readline
debconf: unable to initialize frontend: Readline
debconf: (This frontend requires a controlling tty.)
debconf: falling back to frontend: Teletype
debconf: unable to initialize frontend: Teletype
debconf: (This frontend requires a controlling tty.)
debconf: falling back to frontend: Noninteractive
Creating config file /etc/default/sysstat with new version
update-alternatives: using /usr/bin/sar.sysstat to provide /usr/bin/sar (sar) in auto mode
Created symlink '/etc/systemd/system/sysstat.service.wants/sysstat-collect.timer' → '/usr/lib/systemd/system/sysstat-collect.timer'.
Created symlink '/etc/systemd/system/sysstat.service.wants/sysstat-rotate.timer' → '/usr/lib/systemd/system/sysstat-rotate.timer'.
Created symlink '/etc/systemd/system/sysstat.service.wants/sysstat-summary.timer' → '/usr/lib/systemd/system/sysstat-summary.timer'.
Created symlink '/etc/systemd/system/multi-user.target.wants/sysstat.service' → '/usr/lib/systemd/system/sysstat.service'.
Processing triggers for man-db (2.13.1-1) ...
Processing triggers for libc-bin (2.41-12+rpt1+deb13u3) ...
#+end_example

** ~raspi-utils~: CLI utilities to access GPIO
:PROPERTIES:
:header-args+: :var  PKG="raspi-utils"
:END:

#+call: apt-install-doc()

#+RESULTS:
: Running 'sudo apt install -y raspi-utils' in host 'jrr5x' on Thu Jul 16 18:54:06 EEST 2026
: PKG=raspi-utils

#+call: apt-install()

#+RESULTS:
: Running 'sudo apt install -y raspi-utils' in host 'jrr5x' on Thu Jul 16 18:54:11 EEST 2026
: 
Reading package lists... 0%

Reading package lists... 100%

Building dependency tree... 0%

Building dependency tree... 0%

Building dependency tree... 50%

Building dependency tree... 50%

Building dependency tree... 68%

Building dependency tree... 99%

Reading state information... 0%

Reading state information... 0%
                                
raspi-utils is already the newest version (20260626-1).
: Summary:
:   Upgrading: 0, Installing: 0, Removing: 0, Not Upgrading: 0

** ~swig~: Simplified Wrapper and Interface Generator
:PROPERTIES:
:header-args+: :var  PKG="swig build-essential liblgpio-dev"
:END:

#+call: apt-install-doc()

#+RESULTS:
: Running 'sudo apt install -y swig build-essential liblgpio-dev' in host 'jrr5x' on Thu Jul 16 18:54:34 EEST 2026
: PKG=swig build-essential liblgpio-dev

#+call: apt-install()

#+RESULTS:
#+begin_example
Running 'sudo apt install -y swig build-essential liblgpio-dev' in host 'jrr5x' on Thu Jul 16 18:54:43 EEST 2026

Reading package lists... 0%

Reading package lists... 100%

Building dependency tree... 0%

Building dependency tree... 0%

Building dependency tree... 50%

Building dependency tree... 50%

Building dependency tree... 68%

Reading state information... 0%

Reading state information... 0%

Reading state information... 0%
                                
build-essential is already the newest version (12.12).
Installing:
[32m  liblgpio-dev  swig
[0m
Suggested packages:
  swig-doc  swig-examples

Summary:
  Upgrading: 0, Installing: 2, Removing: 0, Not Upgrading: 0
  Download size: 1461 kB
  Space needed: 6307 kB / 6525 MB available

[33m
0% [Working][0m
            
Get:1 http://deb.debian.org/debian trixie/main arm64 swig arm64 4.3.0-1 [1406 kB]
[33m
0% [Connecting to archive.raspberrypi.com (93.93.135.141)] [1 swig 0 B/1406 kB [0m
                                                                               
Get:2 http://archive.raspberrypi.com/debian trixie/main arm64 liblgpio-dev arm64 0.2.2-1~rpt1+trixie [54.3 kB]
[33m
                                                                               
19% [2 liblgpio-dev 2596 B/54.3 kB 5%] [1 swig 342 kB/1406 kB 24%][0m[33m
                                                                  
57% [1 swig 808 kB/1406 kB 57%][0m[33m
                               
100% [Working][0m
              
Fetched 1461 kB in 1s (2575 kB/s)
debconf: unable to initialize frontend: Dialog
debconf: (Dialog frontend will not work on a dumb terminal, an emacs shell buffer, or without a controlling terminal.)
debconf: falling back to frontend: Readline
Selecting previously unselected package liblgpio-dev:arm64.
(Reading database ... 
(Reading database ... 5%
(Reading database ... 10%
(Reading database ... 15%
(Reading database ... 20%
(Reading database ... 25%
(Reading database ... 30%
(Reading database ... 35%
(Reading database ... 40%
(Reading database ... 45%
(Reading database ... 50%
(Reading database ... 55%
(Reading database ... 60%
(Reading database ... 65%
(Reading database ... 70%
(Reading database ... 75%
(Reading database ... 80%
(Reading database ... 85%
(Reading database ... 90%
(Reading database ... 95%
(Reading database ... 100%
(Reading database ... 68380 files and directories currently installed.)
Preparing to unpack .../liblgpio-dev_0.2.2-1~rpt1+trixie_arm64.deb ...
Unpacking liblgpio-dev:arm64 (0.2.2-1~rpt1+trixie) ...
Selecting previously unselected package swig.
Preparing to unpack .../swig_4.3.0-1_arm64.deb ...
Unpacking swig (4.3.0-1) ...
Setting up swig (4.3.0-1) ...
Setting up liblgpio-dev:arm64 (0.2.2-1~rpt1+trixie) ...
Processing triggers for man-db (2.13.1-1) ...
#+end_example

** ~ffmpeg~: A complete, cross-platform solution to record, convert and stream audio and video
:PROPERTIES:
:header-args+: :var  PKG="ffmpeg"
:END:

#+call: apt-install-doc()

#+RESULTS:
: Running 'sudo apt install -y ffmpeg' in host 'jrr5x' on Thu Jul 16 18:55:04 EEST 2026
: PKG=ffmpeg

#+call: apt-install()

#+RESULTS:
#+begin_example
Running 'sudo apt install -y ffmpeg' in host 'jrr5x' on Thu Jul 16 18:55:10 EEST 2026

Reading package lists... 0%

Reading package lists... 100%

Building dependency tree... 0%

Building dependency tree... 0%

Building dependency tree... 50%

Building dependency tree... 50%

Building dependency tree... 69%

Reading state information... 0%

Reading state information... 0%
                                
Installing:
[32m  ffmpeg
[0m
Installing dependencies:
[32m  adwaita-icon-theme         libglvnd0            libtheoradec1
  at-spi2-common             libglx-mesa0         libtheoraenc1
  at-spi2-core               libglx0              libtwolame0
  dconf-gsettings-backend    libgme0              libudfread0
  dconf-service              libgraphite2-3       libunibreak6
  fontconfig                 libgsm1              libva-drm2
  fontconfig-config          libgtk-3-0t64        libva-x11-2
  fonts-dejavu-core          libgtk-3-bin         libva2
  fonts-dejavu-mono          libgtk-3-common      libvdpau-va-gl1
  gsettings-desktop-schemas  libharfbuzz0b        libvdpau1
  gtk-update-icon-cache      libhwy1t64           libvidstab1.1
  hicolor-icon-theme         libiec61883-0        libvorbisenc2
  libaacs0                   libjack-jackd2-0     libvorbisfile3
  libaom3                    libjxl0.11           libvpx9
  libass9                    liblapack3           libvulkan1
  libasyncns0                liblcms2-2           libwayland-client0
  libatk-bridge2.0-0t64      liblilv-0-0          libwayland-cursor0
  libatk1.0-0t64             libllvm19            libwayland-egl1
  libatspi2.0-0t64           libmbedcrypto16      libwayland-server0
  libavahi-client3           libmp3lame0          libwebpmux3
  libavc1394-0               libmpg123-0t64       libx11-xcb1
  libavcodec61               libmysofa1           libx264-164
  libavdevice61              libnorm1t64          libx265-215
  libavfilter10              libopenal-data       libxcb-dri3-0
  libavformat61              libopenal1           libxcb-glx0
  libavutil59                libopenjp2-7         libxcb-present0
  libbdplus0                 libopenmpt0t64       libxcb-randr0
  libblas3                   libopus0             libxcb-render0
  libbluray2                 libpango-1.0-0       libxcb-shape0
  libbs2b0                   libpangocairo-1.0-0  libxcb-shm0
  libcaca0                   libpangoft2-1.0-0    libxcb-sync1
  libcairo-gobject2          libpgm-5.3-0t64      libxcb-xfixes0
  libcairo2                  libpixman-1-0        libxcomposite1
  libcdio-cdda2t64           libplacebo349        libxcursor1
  libcdio-paranoia2t64       libpocketsphinx3     libxdamage1
  libcdio19t64               libpostproc58        libxfixes3
  libchromaprint1            libpulse0            libxi6
  libcjson1                  librabbitmq4         libxinerama1
  libcloudproviders0         librav1e0.7          libxkbcommon0
  libcodec2-1.2              libraw1394-11        libxrandr2
  libcolord2                 librist4             libxrender1
  libcups2t64                librsvg2-2           libxshmfence1
  libdatrie1                 librsvg2-common      libxss1
  libdav1d7                  librubberband2       libxtst6
  libdc1394-25               libsdl2-2.0-0        libxv1
  libdecor-0-0               libserd-0-0          libxvidcore4
  libdecor-0-plugin-1-gtk    libshine3            libxxf86vm1
  libdrm-amdgpu1             libsnappy1v5         libz3-4
  libdvdnav4                 libsndfile1          libzimg2
  libepoxy0                  libsodium23          libzix-0-0
  libfftw3-double3           libsord-0-0          libzmq5
  libflite1                  libsoxr0             libzvbi-common
  libfontconfig1             libspeex1            libzvbi0t64
  libfreetype6               libsphinxbase3t64    mesa-libgallium
  libfribidi0                libsratom-0-0        mesa-va-drivers
  libgbm1                    libsrt1.5-gnutls     mesa-vdpau-drivers
  libgdk-pixbuf-2.0-0        libssh-4             mesa-vulkan-drivers
  libgdk-pixbuf2.0-bin       libsvtav1enc2        ocl-icd-libopencl1
  libgdk-pixbuf2.0-common    libswresample5       pocketsphinx-en-us
  libgfortran5               libswscale8          va-driver-all
  libgl1                     libthai-data         vdpau-driver-all
  libgl1-mesa-dri            libthai0             x11-common
[0m
Suggested packages:
  adwaita-icon-theme-legacy  libfftw3-bin    libraw1394-doc
  ffmpeg-doc                 libfftw3-dev    librsvg2-bin
  libcuda1                   gvfs            xdg-utils
  libnvcuvid1                jackd2          serdi
  libnvidia-encode1          liblcms2-utils  sordi
  libbluray-bdj              libportaudio2   speex
  colord                     libsndio7.0     opencl-icd
  cups-common                opus-tools      nvidia-vdpau-driver
  libdvdcss2                 pulseaudio

Summary:
  Upgrading: 0, Installing: 187, Removing: 0, Not Upgrading: 0
  Download size: 176 MB
  Space needed: 564 MB / 6516 MB available

[33m
0% [Working][0m
            
Get:1 http://deb.debian.org/debian trixie/main arm64 libgdk-pixbuf2.0-common all 2.42.12+dfsg-4+deb13u1 [312 kB]
[33m
0% [1 libgdk-pixbuf2.0-common 687 B/312 kB 0%] [Connecting to archive.raspberry[0m[33m
                                                                               
0% [Waiting for headers][0m
                        
Get:2 http://archive.raspberrypi.com/debian trixie/main arm64 gsettings-desktop-schemas all 48.0-1+rpt1 [1681 kB]
[33m
0% [Waiting for headers] [2 gsettings-desktop-schemas 1144 B/1681 kB 0%][0m
                                                                        
Get:3 http://deb.debian.org/debian trixie/main arm64 libgdk-pixbuf-2.0-0 arm64 2.42.12+dfsg-4+deb13u1 [131 kB]
[33m
0% [3 libgdk-pixbuf-2.0-0 0 B/131 kB 0%] [2 gsettings-desktop-schemas 14.2 kB/1[0m[33m
                                                                               
0% [2 gsettings-desktop-schemas 22.9 kB/1681 kB 1%][0m
                                                   
Get:4 http://deb.debian.org/debian trixie/main arm64 gtk-update-icon-cache arm64 4.18.6+ds-2 [52.3 kB]
[33m
0% [4 gtk-update-icon-cache 3444 B/52.3 kB 7%] [2 gsettings-desktop-schemas 22.[0m[33m
                                                                               
1% [2 gsettings-desktop-schemas 28.7 kB/1681 kB 2%][0m
                                                   
Get:5 http://deb.debian.org/debian trixie/main arm64 hicolor-icon-theme all 0.18-2 [11.8 kB]
[33m
1% [5 hicolor-icon-theme 11.8 kB/11.8 kB 100%] [2 gsettings-desktop-schemas 28.[0m[33m
                                                                               
1% [2 gsettings-desktop-schemas 28.7 kB/1681 kB 2%][0m
                                                   
Get:6 http://deb.debian.org/debian trixie/main arm64 adwaita-icon-theme all 48.1-1 [504 kB]
[33m
1% [6 adwaita-icon-theme 13.0 kB/504 kB 3%] [2 gsettings-desktop-schemas 28.7 k[0m[33m
                                                                               
1% [2 gsettings-desktop-schemas 152 kB/1681 kB 9%][0m
                                                  
Get:7 http://deb.debian.org/debian trixie/main arm64 at-spi2-common all 2.56.2-1+deb13u1 [171 kB]
[33m
1% [7 at-spi2-common 158 B/171 kB 0%] [2 gsettings-desktop-schemas 152 kB/1681 [0m[33m
                                                                               
1% [2 gsettings-desktop-schemas 349 kB/1681 kB 21%][0m
                                                   
Get:8 http://deb.debian.org/debian trixie/main arm64 libxi6 arm64 2:1.8.2-1 [77.8 kB]
[33m
1% [8 libxi6 1867 B/77.8 kB 2%] [2 gsettings-desktop-schemas 349 kB/1681 kB 21%[0m[33m
                                                                               
1% [Waiting for headers] [2 gsettings-desktop-schemas 349 kB/1681 kB 21%][0m
                                                                         
Get:9 http://deb.debian.org/debian trixie/main arm64 libatspi2.0-0t64 arm64 2.56.2-1+deb13u1 [76.3 kB]
[33m
1% [9 libatspi2.0-0t64 2761 B/76.3 kB 4%] [2 gsettings-desktop-schemas 349 kB/1[0m[33m
                                                                               
2% [2 gsettings-desktop-schemas 1441 kB/1681 kB 86%][0m
                                                    
Get:10 http://deb.debian.org/debian trixie/main arm64 x11-common all 1:7.7+24+deb13u1 [217 kB]
[33m
2% [10 x11-common 2256 B/217 kB 1%] [2 gsettings-desktop-schemas 1469 kB/1681 k[0m[33m
                                                                               
2% [2 gsettings-desktop-schemas 1681 kB/1681 kB 100%][0m
                                                     
Get:11 http://deb.debian.org/debian trixie/main arm64 libxtst6 arm64 2:1.2.5-1 [25.7 kB]
[33m
2% [11 libxtst6 1184 B/25.7 kB 5%] [2 gsettings-desktop-schemas 1681 kB/1681 kB[0m[33m
                                                                               
3% [2 gsettings-desktop-schemas 1681 kB/1681 kB 100%][0m
                                                     
Get:12 http://deb.debian.org/debian trixie/main arm64 dconf-service arm64 0.40.0-5 [30.9 kB]
[33m
3% [12 dconf-service 2095 B/30.9 kB 7%] [2 gsettings-desktop-schemas 1681 kB/16[0m[33m
                                                                               
3% [2 gsettings-desktop-schemas 1681 kB/1681 kB 100%][0m
                                                     
Get:13 http://deb.debian.org/debian trixie/main arm64 dconf-gsettings-backend arm64 0.40.0-5 [27.3 kB]
[33m
3% [13 dconf-gsettings-backend 6509 B/27.3 kB 24%] [2 gsettings-desktop-schemas[0m[33m
                                                                               
3% [2 gsettings-desktop-schemas 1681 kB/1681 kB 100%][0m
                                                     
Get:14 http://deb.debian.org/debian trixie/main arm64 at-spi2-core arm64 2.56.2-1+deb13u1 [60.2 kB]
[33m
3% [14 at-spi2-core 16.0 kB/60.2 kB 26%] [2 gsettings-desktop-schemas 1681 kB/1[0m[33m
                                                                               
3% [14 at-spi2-core 16.0 kB/60.2 kB 26%][0m[33m
                                        
3% [Waiting for headers][0m
                        
Get:15 http://deb.debian.org/debian trixie/main arm64 libaom3 arm64 3.12.1-1 [1670 kB]
[33m
3% [15 libaom3 632 B/1670 kB 0%] [Waiting for headers][0m
                                                      
Get:16 http://archive.raspberrypi.com/debian trixie/main arm64 libavutil59 arm64 8:7.1.5-0+deb13u1+rpt1 [505 kB]
[33m
3% [15 libaom3 33.4 kB/1670 kB 2%] [16 libavutil59 4080 B/505 kB 1%][0m[33m
                                                                    
3% [15 libaom3 254 kB/1670 kB 15%][0m
                                  
Get:17 http://archive.raspberrypi.com/debian trixie/main arm64 libpixman-1-0 arm64 0.46.4-1+rpt1 [240 kB]
[33m
3% [15 libaom3 254 kB/1670 kB 15%] [17 libpixman-1-0 12.3 kB/240 kB 5%][0m[33m
                                                                       
4% [15 libaom3 295 kB/1670 kB 18%][0m
                                  
Get:18 http://archive.raspberrypi.com/debian trixie/main arm64 libcairo2 arm64 1.18.4-1+rpt1 [631 kB]
[33m
4% [15 libaom3 295 kB/1670 kB 18%] [18 libcairo2 8210 B/631 kB 1%][0m[33m
                                                                  
4% [15 libaom3 342 kB/1670 kB 20%][0m
                                  
Get:19 http://archive.raspberrypi.com/debian trixie/main arm64 libcairo-gobject2 arm64 1.18.4-1+rpt1 [134 kB]
[33m
4% [15 libaom3 342 kB/1670 kB 20%] [19 libcairo-gobject2 21.6 kB/134 kB 16%][0m[33m
                                                                            
4% [15 libaom3 347 kB/1670 kB 21%][0m
                                  
Get:20 http://archive.raspberrypi.com/debian trixie/main arm64 libswresample5 arm64 8:7.1.5-0+deb13u1+rpt1 [113 kB]
[33m
4% [15 libaom3 347 kB/1670 kB 21%] [20 libswresample5 18.7 kB/113 kB 17%][0m[33m
                                                                         
4% [15 libaom3 358 kB/1670 kB 21%][0m
                                  
Get:21 http://archive.raspberrypi.com/debian trixie/main arm64 libavcodec61 arm64 8:7.1.5-0+deb13u1+rpt1 [7236 kB]
[33m
4% [15 libaom3 358 kB/1670 kB 21%] [21 libavcodec61 21.2 kB/7236 kB 0%][0m[33m
5% [15 libaom3 501 kB/1670 kB 30%] [21 libavcodec61 1602 kB/7236 kB 22%][0m[33m
6% [15 libaom3 647 kB/1670 kB 39%] [21 libavcodec61 2962 kB/7236 kB 41%][0m[33m
7% [15 libaom3 815 kB/1670 kB 49%] [21 libavcodec61 4421 kB/7236 kB 61%][0m[33m
7% [15 libaom3 1011 kB/1670 kB 61%] [21 libavcodec61 5937 kB/7236 kB 82%][0m[33m
8% [15 libaom3 1246 kB/1670 kB 75%] [21 libavcodec61 7236 kB/7236 kB 100%][0m[33m
                                                                          
8% [15 libaom3 1415 kB/1670 kB 85%][0m
                                   
Get:22 http://archive.raspberrypi.com/debian trixie/main arm64 libavformat61 arm64 8:7.1.5-0+deb13u1+rpt1 [1475 kB]
[33m
8% [15 libaom3 1415 kB/1670 kB 85%] [22 libavformat61 9394 B/1475 kB 1%][0m[33m
                                                                        
9% [15 libaom3 1629 kB/1670 kB 98%][0m
                                   
Get:23 http://archive.raspberrypi.com/debian trixie/main arm64 libpulse0 arm64 17.0+dfsg1-2+rpt1 [336 kB]
[33m
9% [15 libaom3 1629 kB/1670 kB 98%] [23 libpulse0 41.5 kB/336 kB 12%][0m[33m
                                                                     
10% [15 libaom3 1670 kB/1670 kB 100%] [Waiting for headers][0m
                                                           
Get:24 http://archive.raspberrypi.com/debian trixie/main arm64 libpostproc58 arm64 8:7.1.5-0+deb13u1+rpt1 [94.3 kB]
[33m
10% [15 libaom3 1670 kB/1670 kB 100%] [24 libpostproc58 32.8 kB/94.3 kB 35%][0m[33m
                                                                            
10% [15 libaom3 1670 kB/1670 kB 100%][0m
                                     
Get:25 http://archive.raspberrypi.com/debian trixie/main arm64 libswscale8 arm64 8:7.1.5-0+deb13u1+rpt1 [269 kB]
[33m
10% [15 libaom3 1670 kB/1670 kB 100%] [25 libswscale8 15.1 kB/269 kB 6%][0m[33m
                                                                        
10% [25 libswscale8 238 kB/269 kB 88%][0m
                                      
Get:26 http://deb.debian.org/debian trixie/main arm64 libva2 arm64 2.22.0-3 [74.2 kB]
[33m
10% [26 libva2 21.6 kB/74.2 kB 29%] [25 libswscale8 250 kB/269 kB 93%][0m[33m
                                                                      
10% [26 libva2 31.7 kB/74.2 kB 43%][0m
                                   
Get:27 http://archive.raspberrypi.com/debian trixie/main arm64 libavfilter10 arm64 8:7.1.5-0+deb13u1+rpt1 [5307 kB]
[33m
10% [26 libva2 31.7 kB/74.2 kB 43%] [27 libavfilter10 33.5 kB/5307 kB 1%][0m[33m
                                                                         
10% [27 libavfilter10 287 kB/5307 kB 5%][0m
                                        
Get:28 http://deb.debian.org/debian trixie/main arm64 libva-drm2 arm64 2.22.0-3 [18.5 kB]
[33m
10% [28 libva-drm2 9 B/18.5 kB 0%] [27 libavfilter10 287 kB/5307 kB 5%][0m[33m
                                                                       
10% [27 libavfilter10 387 kB/5307 kB 7%][0m
                                        
Get:29 http://deb.debian.org/debian trixie/main arm64 libx11-xcb1 arm64 2:1.8.12-1 [247 kB]
[33m
10% [29 libx11-xcb1 2365 B/247 kB 1%] [27 libavfilter10 387 kB/5307 kB 7%][0m[33m
11% [29 libx11-xcb1 231 kB/247 kB 93%] [27 libavfilter10 1770 kB/5307 kB 33%][0m[33m
                                                                             
11% [27 libavfilter10 1871 kB/5307 kB 35%][0m
                                          
Get:30 http://deb.debian.org/debian trixie/main arm64 libxcb-dri3-0 arm64 1.17.0-2+b1 [107 kB]
[33m
11% [30 libxcb-dri3-0 7220 B/107 kB 7%] [27 libavfilter10 1928 kB/5307 kB 36%][0m[33m
12% [27 libavfilter10 2583 kB/5307 kB 49%]                        3164 kB/s 49s[0m
                                                                               
Get:31 http://deb.debian.org/debian trixie/main arm64 libxfixes3 arm64 1:6.0.0-2+b4 [20.5 kB]
[33m
                                                                               
12% [31 libxfixes3 3365 B/20.5 kB 16%] [27 libavfilter10 2583 kB/5307 kB 49%][0m[33m
12% [27 libavfilter10 2670 kB/5307 kB 50%]                        3164 kB/s 49s[0m
                                                                               
Get:32 http://deb.debian.org/debian trixie/main arm64 libva-x11-2 arm64 2.22.0-3 [23.0 kB]
[33m
                                                                               
12% [32 libva-x11-2 2368 B/23.0 kB 10%] [27 libavfilter10 2686 kB/5307 kB 51%][0m[33m
12% [27 libavfilter10 2795 kB/5307 kB 53%]                        3164 kB/s 49s[0m
                                                                               
Get:33 http://deb.debian.org/debian trixie/main arm64 libvdpau1 arm64 1.5-3+b1 [24.4 kB]
[33m
                                                                               
12% [33 libvdpau1 269 B/24.4 kB 1%] [27 libavfilter10 2795 kB/5307 kB 53%][0m[33m
12% [Waiting for headers] [27 libavfilter10 2890 kB/5307 kB 54%]  3164 kB/s 49s[0m
                                                                               
Get:34 http://deb.debian.org/debian trixie/main arm64 ocl-icd-libopencl1 arm64 2.3.3-1 [42.7 kB]
[33m
12% [34 ocl-icd-libopencl1 3985 B/42.7 kB 9%] [27 libavfilter10 2890 kB/5307 kB[0m[33m
12% [27 libavfilter10 3005 kB/5307 kB 57%]                        3164 kB/s 49s[0m
                                                                               
Get:35 http://deb.debian.org/debian trixie/main arm64 libfreetype6 arm64 2.13.3+dfsg-1+deb13u1 [422 kB]
[33m
                                                                               
13% [35 libfreetype6 10.1 kB/422 kB 2%] [27 libavfilter10 3111 kB/5307 kB 59%][0m[33m
13% [35 libfreetype6 289 kB/422 kB 68%] [27 libavfilter10 4518 kB/5307 kB 85%][0m[33m
14% [27 libavfilter10 5041 kB/5307 kB 95%]                        3164 kB/s 48s[0m
                                                                               
Get:36 http://deb.debian.org/debian trixie/main arm64 fonts-dejavu-mono all 2.37-8 [489 kB]
[33m
14% [36 fonts-dejavu-mono 3648 B/489 kB 1%] [27 libavfilter10 5090 kB/5307 kB 9[0m[33m
14% [36 fonts-dejavu-mono 232 kB/489 kB 47%]                      3164 kB/s 48s[0m
                                                                               
Get:37 http://archive.raspberrypi.com/debian trixie/main arm64 libdrm-amdgpu1 arm64 2.4.131-1~bpo13+1+rpt2 [27.8 kB]
[33m
14% [36 fonts-dejavu-mono 232 kB/489 kB 47%] [37 libdrm-amdgpu1 27.8 kB/27.8 kB[0m[33m
14% [36 fonts-dejavu-mono 235 kB/489 kB 48%]                      3164 kB/s 48s[0m
                                                                               
Get:38 http://archive.raspberrypi.com/debian trixie/main arm64 mesa-libgallium arm64 25.0.7-2+rpt4 [11.8 MB]
[33m
14% [36 fonts-dejavu-mono 235 kB/489 kB 48%] [38 mesa-libgallium 35.2 kB/11.8 M[0m[33m
15% [38 mesa-libgallium 1870 kB/11.8 MB 16%]                      3164 kB/s 47s[0m
                                                                               
Get:39 http://deb.debian.org/debian trixie/main arm64 fonts-dejavu-core all 2.37-8 [840 kB]
[33m
15% [39 fonts-dejavu-core 568 B/840 kB 0%] [38 mesa-libgallium 1884 kB/11.8 MB [0m[33m
16% [39 fonts-dejavu-core 324 kB/840 kB 39%] [38 mesa-libgallium 3279 kB/11.8 M[0m[33m
17% [39 fonts-dejavu-core 584 kB/840 kB 69%] [38 mesa-libgallium 4504 kB/11.8 M[0m[33m
17% [39 fonts-dejavu-core 840 kB/840 kB 100%] [38 mesa-libgallium 5992 kB/11.8 [0m[33m
18% [38 mesa-libgallium 6005 kB/11.8 MB 51%]                      3164 kB/s 46s[0m
                                                                               
Get:40 http://deb.debian.org/debian trixie/main arm64 fontconfig-config arm64 2.15.0-2.3 [318 kB]
[33m
18% [40 fontconfig-config 4332 B/318 kB 1%] [38 mesa-libgallium 6035 kB/11.8 MB[0m[33m
18% [40 fontconfig-config 312 kB/318 kB 98%] [38 mesa-libgallium 7321 kB/11.8 M[0m[33m
18% [38 mesa-libgallium 7321 kB/11.8 MB 62%]                      3164 kB/s 45s[0m
                                                                               
Get:41 http://deb.debian.org/debian trixie/main arm64 libfontconfig1 arm64 2.15.0-2.3 [387 kB]
[33m
18% [41 libfontconfig1 5017 B/387 kB 1%] [38 mesa-libgallium 7321 kB/11.8 MB 62[0m[33m
19% [38 mesa-libgallium 8320 kB/11.8 MB 71%]                      3164 kB/s 45s[0m
                                                                               
Get:42 http://deb.debian.org/debian trixie/main arm64 libxcb-render0 arm64 1.17.0-2+b1 [115 kB]
[33m
19% [42 libxcb-render0 11.6 kB/115 kB 10%] [38 mesa-libgallium 8320 kB/11.8 MB [0m[33m
19% [38 mesa-libgallium 8323 kB/11.8 MB 71%]                      3164 kB/s 45s[0m
                                                                               
Get:43 http://deb.debian.org/debian trixie/main arm64 libxcb-shm0 arm64 1.17.0-2+b1 [105 kB]
[33m
                                                                               
19% [43 libxcb-shm0 2700 B/105 kB 3%] [38 mesa-libgallium 8323 kB/11.8 MB 71%][0m[33m
19% [38 mesa-libgallium 8327 kB/11.8 MB 71%]                      3164 kB/s 45s[0m
                                                                               
Get:44 http://deb.debian.org/debian trixie/main arm64 libxrender1 arm64 1:0.9.12-1 [27.0 kB]
[33m
20% [44 libxrender1 9121 B/27.0 kB 34%] [38 mesa-libgallium 8327 kB/11.8 MB 71%[0m[33m
                                                                               
20% [Waiting for headers] [38 mesa-libgallium 8327 kB/11.8 MB 71%][0m
                                                                  
Get:45 http://deb.debian.org/debian trixie/main arm64 libcodec2-1.2 arm64 1.2.0-3 [8163 kB]
[33m
20% [45 libcodec2-1.2 13.1 kB/8163 kB 0%] [38 mesa-libgallium 8327 kB/11.8 MB 7[0m[33m
20% [45 libcodec2-1.2 726 kB/8163 kB 9%] [38 mesa-libgallium 9276 kB/11.8 MB 79[0m[33m
21% [45 libcodec2-1.2 1028 kB/8163 kB 13%] [38 mesa-libgallium 10.5 MB/11.8 MB [0m[33m
22% [45 libcodec2-1.2 1329 kB/8163 kB 16%]                        3164 kB/s 43s[0m
                                                                               
Get:46 http://archive.raspberrypi.com/debian trixie/main arm64 libwayland-server0 arm64 1.24.0-2~bpo13+1~rpt1 [42.4 kB]
[33m
22% [45 libcodec2-1.2 1329 kB/8163 kB 16%] [46 libwayland-server0 25.8 kB/42.4 [0m[33m
22% [45 libcodec2-1.2 1334 kB/8163 kB 16%]                        3164 kB/s 43s[0m
                                                                               
Get:47 http://archive.raspberrypi.com/debian trixie/main arm64 libgbm1 arm64 25.0.7-2+rpt4 [53.7 kB]
[33m
                                                                               
22% [45 libcodec2-1.2 1334 kB/8163 kB 16%] [47 libgbm1 1966 B/53.7 kB 4%][0m[33m
22% [45 libcodec2-1.2 1347 kB/8163 kB 17%]                        3164 kB/s 43s[0m
                                                                               
Get:48 http://archive.raspberrypi.com/debian trixie/main arm64 libgl1-mesa-dri arm64 25.0.7-2+rpt4 [57.0 kB]
[33m
22% [45 libcodec2-1.2 1347 kB/8163 kB 17%] [48 libgl1-mesa-dri 1576 B/57.0 kB 3[0m[33m
22% [45 libcodec2-1.2 1360 kB/8163 kB 17%]                        3164 kB/s 43s[0m
                                                                               
Get:49 http://archive.raspberrypi.com/debian trixie/main arm64 libglx-mesa0 arm64 25.0.7-2+rpt4 [189 kB]
[33m
                                                                               
22% [45 libcodec2-1.2 1360 kB/8163 kB 17%] [49 libglx-mesa0 2198 B/189 kB 1%][0m[33m
23% [45 libcodec2-1.2 1446 kB/8163 kB 18%] [Waiting for headers]  3164 kB/s 43s[0m
                                                                               
Get:50 http://archive.raspberrypi.com/debian trixie/main arm64 libwayland-client0 arm64 1.24.0-2~bpo13+1~rpt1 [33.5 kB]
[33m
23% [45 libcodec2-1.2 1447 kB/8163 kB 18%] [50 libwayland-client0 914 B/33.5 kB[0m[33m
23% [45 libcodec2-1.2 1453 kB/8163 kB 18%]                        3164 kB/s 43s[0m
                                                                               
Get:51 http://archive.raspberrypi.com/debian trixie/main arm64 libwayland-cursor0 arm64 1.24.0-2~bpo13+1~rpt1 [13.9 kB]
[33m
23% [45 libcodec2-1.2 1456 kB/8163 kB 18%] [51 libwayland-cursor0 10.6 kB/13.9 [0m[33m
23% [45 libcodec2-1.2 1464 kB/8163 kB 18%]                        3197 kB/s 43s[0m
                                                                               
Get:52 http://archive.raspberrypi.com/debian trixie/main arm64 libwayland-egl1 arm64 1.24.0-2~bpo13+1~rpt1 [6772 B]
[33m
23% [45 libcodec2-1.2 1464 kB/8163 kB 18%] [52 libwayland-egl1 6772 B/6772 B 10[0m[33m
23% [45 libcodec2-1.2 1464 kB/8163 kB 18%]                        3197 kB/s 43s[0m
                                                                               
Get:53 http://archive.raspberrypi.com/debian trixie/main arm64 libavdevice61 arm64 8:7.1.5-0+deb13u1+rpt1 [151 kB]
[33m
23% [45 libcodec2-1.2 1470 kB/8163 kB 18%] [53 libavdevice61 48.5 kB/151 kB 32%[0m[33m
23% [45 libcodec2-1.2 1513 kB/8163 kB 19%]                        3197 kB/s 42s[0m
                                                                               
Get:54 http://archive.raspberrypi.com/debian trixie/main arm64 ffmpeg arm64 8:7.1.5-0+deb13u1+rpt1 [2220 kB]
[33m
                                                                               
23% [45 libcodec2-1.2 1513 kB/8163 kB 19%] [54 ffmpeg 19.4 kB/2220 kB 1%][0m[33m
24% [45 libcodec2-1.2 1828 kB/8163 kB 22%] [54 ffmpeg 1334 kB/2220 kB 60%][0m[33m
24% [45 libcodec2-1.2 2124 kB/8163 kB 26%]                        3197 kB/s 42s[0m
                                                                               
Get:55 http://archive.raspberrypi.com/debian trixie/main arm64 libcups2t64 arm64 2.4.10-3+rpt2+deb13u2 [304 kB]
[33m
                                                                               
24% [45 libcodec2-1.2 2124 kB/8163 kB 26%] [55 libcups2t64 17.6 kB/304 kB 6%][0m[33m
25% [45 libcodec2-1.2 2166 kB/8163 kB 27%]                        3197 kB/s 41s[0m
                                                                               
Get:56 http://archive.raspberrypi.com/debian trixie/main arm64 libgtk-3-common all 1:3.24.49-3+rpt8 [10.4 MB]
[33m
25% [45 libcodec2-1.2 2166 kB/8163 kB 27%] [56 libgtk-3-common 17.5 kB/10.4 MB [0m[33m
26% [45 libcodec2-1.2 2474 kB/8163 kB 30%] [56 libgtk-3-common 1474 kB/10.4 MB [0m[33m
26% [45 libcodec2-1.2 2767 kB/8163 kB 34%] [56 libgtk-3-common 2805 kB/10.4 MB [0m[33m
27% [45 libcodec2-1.2 3067 kB/8163 kB 38%] [56 libgtk-3-common 4098 kB/10.4 MB [0m[33m
28% [45 libcodec2-1.2 3378 kB/8163 kB 41%] [56 libgtk-3-common 5420 kB/10.4 MB [0m[33m
28% [45 libcodec2-1.2 3655 kB/8163 kB 45%] [56 libgtk-3-common 6606 kB/10.4 MB [0m[33m
29% [45 libcodec2-1.2 3945 kB/8163 kB 48%] [56 libgtk-3-common 8080 kB/10.4 MB [0m[33m
30% [45 libcodec2-1.2 4263 kB/8163 kB 52%] [56 libgtk-3-common 9289 kB/10.4 MB [0m[33m
31% [45 libcodec2-1.2 4524 kB/8163 kB 55%]                        3197 kB/s 37s[0m
                                                                               
Get:57 http://archive.raspberrypi.com/debian trixie/main arm64 libgtk-3-0t64 arm64 1:3.24.49-3+rpt8 [3638 kB]
[33m
31% [45 libcodec2-1.2 4524 kB/8163 kB 55%] [57 libgtk-3-0t64 3626 B/3638 kB 0%][0m[33m
31% [45 libcodec2-1.2 4868 kB/8163 kB 60%] [57 libgtk-3-0t64 1492 kB/3638 kB 41[0m[33m
32% [45 libcodec2-1.2 5188 kB/8163 kB 64%] [57 libgtk-3-0t64 2761 kB/3638 kB 76[0m[33m
33% [45 libcodec2-1.2 5464 kB/8163 kB 67%]                        3235 kB/s 36s[0m
                                                                               
Get:58 http://archive.raspberrypi.com/debian trixie/main arm64 libgtk-3-bin arm64 1:3.24.49-3+rpt8 [111 kB]
[33m
                                                                               
33% [45 libcodec2-1.2 5464 kB/8163 kB 67%] [58 libgtk-3-bin 4096 B/111 kB 4%][0m[33m
33% [45 libcodec2-1.2 5471 kB/8163 kB 67%]                        3235 kB/s 36s[0m
                                                                               
Get:59 http://archive.raspberrypi.com/debian trixie/main arm64 mesa-va-drivers arm64 25.0.7-2+rpt4 [21.3 kB]
[33m
33% [45 libcodec2-1.2 5471 kB/8163 kB 67%] [59 mesa-va-drivers 8164 B/21.3 kB 3[0m[33m
33% [45 libcodec2-1.2 5509 kB/8163 kB 67%]                        3235 kB/s 36s[0m
                                                                               
Get:60 http://archive.raspberrypi.com/debian trixie/main arm64 mesa-vdpau-drivers arm64 25.0.7-2+rpt4 [21.4 kB]
[33m
33% [45 libcodec2-1.2 5509 kB/8163 kB 67%] [60 mesa-vdpau-drivers 21.4 kB/21.4 [0m[33m
33% [45 libcodec2-1.2 5512 kB/8163 kB 68%]                        3235 kB/s 36s[0m
                                                                               
Get:61 http://archive.raspberrypi.com/debian trixie/main arm64 mesa-vulkan-drivers arm64 25.0.7-2+rpt4 [16.7 MB]
[33m
33% [45 libcodec2-1.2 5512 kB/8163 kB 68%] [61 mesa-vulkan-drivers 43.1 kB/16.7[0m[33m
33% [45 libcodec2-1.2 5577 kB/8163 kB 68%] [61 mesa-vulkan-drivers 438 kB/16.7 [0m[33m
33% [45 libcodec2-1.2 5577 kB/8163 kB 68%] [61 mesa-vulkan-drivers 438 kB/16.7 [0m[33m
33% [45 libcodec2-1.2 5577 kB/8163 kB 68%] [61 mesa-vulkan-drivers 438 kB/16.7 [0m[33m
36% [45 libcodec2-1.2 6365 kB/8163 kB 78%] [61 mesa-vulkan-drivers 4503 kB/16.7[0m[33m
36% [45 libcodec2-1.2 6567 kB/8163 kB 80%] [61 mesa-vulkan-drivers 6083 kB/16.7[0m[33m
37% [45 libcodec2-1.2 6811 kB/8163 kB 83%] [61 mesa-vulkan-drivers 7466 kB/16.7[0m[33m
38% [45 libcodec2-1.2 7073 kB/8163 kB 87%] [61 mesa-vulkan-drivers 8738 kB/16.7[0m[33m
39% [45 libcodec2-1.2 7376 kB/8163 kB 90%] [61 mesa-vulkan-drivers 10.1 MB/16.7[0m[33m
39% [45 libcodec2-1.2 7655 kB/8163 kB 94%] [61 mesa-vulkan-drivers 11.5 MB/16.7[0m[33m
40% [45 libcodec2-1.2 7946 kB/8163 kB 97%] [61 mesa-vulkan-drivers 12.8 MB/16.7[0m[33m
41% [45 libcodec2-1.2 8163 kB/8163 kB 100%] [61 mesa-vulkan-drivers 14.2 MB/16.[0m[33m
41% [61 mesa-vulkan-drivers 15.0 MB/16.7 MB 90%]                  3043 kB/s 32s[0m
                                                                               
Get:62 http://deb.debian.org/debian trixie/main arm64 libdav1d7 arm64 1.5.1-1 [252 kB]
[33m
41% [62 libdav1d7 58.3 kB/252 kB 23%] [61 mesa-vulkan-drivers 15.0 MB/16.7 MB 9[0m[33m
42% [61 mesa-vulkan-drivers 15.7 MB/16.7 MB 94%]                  3043 kB/s 32s[0m
                                                                               
Get:63 http://deb.debian.org/debian trixie/main arm64 libgsm1 arm64 1.0.22-1+b2 [27.3 kB]
[33m
42% [63 libgsm1 2702 B/27.3 kB 10%] [61 mesa-vulkan-drivers 15.7 MB/16.7 MB 94%[0m[33m
42% [61 mesa-vulkan-drivers 16.0 MB/16.7 MB 96%]                  3043 kB/s 32s[0m
                                                                               
Get:64 http://deb.debian.org/debian trixie/main arm64 libhwy1t64 arm64 1.2.0-2+b2 [499 kB]
[33m
42% [64 libhwy1t64 2118 B/499 kB 0%] [61 mesa-vulkan-drivers 16.0 MB/16.7 MB 96[0m[33m
43% [61 mesa-vulkan-drivers 16.7 MB/16.7 MB 100%]                 3043 kB/s 31s[0m
                                                                               
Get:65 http://deb.debian.org/debian trixie/main arm64 liblcms2-2 arm64 2.16-2+deb13u2 [152 kB]
[33m
43% [65 liblcms2-2 688 B/152 kB 0%] [61 mesa-vulkan-drivers 16.7 MB/16.7 MB 100[0m[33m
43% [61 mesa-vulkan-drivers 16.7 MB/16.7 MB 100%]                 3043 kB/s 31s[0m
                                                                               
Get:66 http://deb.debian.org/debian trixie/main arm64 libjxl0.11 arm64 0.11.2-0.1~deb13u2 [887 kB]
[33m
43% [66 libjxl0.11 0 B/887 kB 0%] [61 mesa-vulkan-drivers 16.7 MB/16.7 MB 100%][0m[33m
43% [66 libjxl0.11 670 kB/887 kB 76%]                             3043 kB/s 31s[0m[33m
44% [Working]                                                     3043 kB/s 31s[0m
                                                                               
Get:67 http://deb.debian.org/debian trixie/main arm64 libmp3lame0 arm64 3.100-6+b3 [355 kB]
[33m
44% [67 libmp3lame0 6351 B/355 kB 2%]                             3043 kB/s 31s[0m[33m
44% [Working]                                                     3043 kB/s 31s[0m
                                                                               
Get:68 http://deb.debian.org/debian trixie/main arm64 libopenjp2-7 arm64 2.5.3-2.1~deb13u2 [189 kB]
[33m
44% [68 libopenjp2-7 0 B/189 kB 0%]                               3043 kB/s 31s[0m[33m
44% [Working]                                                     3043 kB/s 31s[0m
                                                                               
Get:69 http://deb.debian.org/debian trixie/main arm64 libopus0 arm64 1.5.2-2 [2813 kB]
[33m
44% [69 libopus0 375 B/2813 kB 0%]                                3043 kB/s 31s[0m[33m
45% [69 libopus0 1618 kB/2813 kB 58%]                             3043 kB/s 30s[0m[33m
45% [69 libopus0 2813 kB/2813 kB 100%]                            3043 kB/s 30s[0m[33m
45% [Working]                                                     3043 kB/s 30s[0m
                                                                               
Get:70 http://deb.debian.org/debian trixie/main arm64 librav1e0.7 arm64 0.7.1-9+b2 [662 kB]
[33m
46% [70 librav1e0.7 55.4 kB/662 kB 8%]                            3043 kB/s 30s[0m[33m
46% [Working]                                                     3043 kB/s 30s[0m
                                                                               
Get:71 http://deb.debian.org/debian trixie/main arm64 fontconfig arm64 2.15.0-2.3 [463 kB]
[33m
46% [71 fontconfig 13.4 kB/463 kB 3%]                             3043 kB/s 30s[0m[33m
46% [Working]                                                     3043 kB/s 29s[0m
                                                                               
Get:72 http://deb.debian.org/debian trixie/main arm64 libfribidi0 arm64 1.0.16-1 [26.5 kB]
[33m
46% [72 libfribidi0 3010 B/26.5 kB 11%]                           3043 kB/s 29s[0m[33m
46% [Working]                                                     3043 kB/s 29s[0m
                                                                               
Get:73 http://deb.debian.org/debian trixie/main arm64 libgraphite2-3 arm64 1.3.14-2+deb13u1 [70.3 kB]
[33m
46% [73 libgraphite2-3 15.9 kB/70.3 kB 23%]                       3043 kB/s 29s[0m[33m
46% [Working]                                                     3043 kB/s 29s[0m
                                                                               
Get:74 http://deb.debian.org/debian trixie/main arm64 libharfbuzz0b arm64 10.2.0-1+deb13u1 [442 kB]
[33m
46% [74 libharfbuzz0b 10.3 kB/442 kB 2%]                          3043 kB/s 29s[0m[33m
47% [Working]                                                     3043 kB/s 29s[0m
                                                                               
Get:75 http://deb.debian.org/debian trixie/main arm64 libthai-data all 0.1.29-2 [168 kB]
[33m
47% [75 libthai-data 0 B/168 kB 0%]                               3043 kB/s 29s[0m[33m
47% [Working]                                                     3043 kB/s 29s[0m
                                                                               
Get:76 http://deb.debian.org/debian trixie/main arm64 libdatrie1 arm64 0.2.13-3+b1 [37.6 kB]
[33m
47% [76 libdatrie1 3570 B/37.6 kB 9%]                             3043 kB/s 29s[0m[33m
47% [Working]                                                     3043 kB/s 29s[0m
                                                                               
Get:77 http://deb.debian.org/debian trixie/main arm64 libthai0 arm64 0.1.29-2+b1 [48.4 kB]
[33m
47% [77 libthai0 7090 B/48.4 kB 15%]                              3043 kB/s 29s[0m[33m
47% [Working]                                                     3043 kB/s 29s[0m
                                                                               
Get:78 http://deb.debian.org/debian trixie/main arm64 libpango-1.0-0 arm64 1.56.3-1 [213 kB]
[33m
47% [78 libpango-1.0-0 2602 B/213 kB 1%]                          3043 kB/s 29s[0m[33m
47% [Working]                                                     3043 kB/s 29s[0m
                                                                               
Get:79 http://deb.debian.org/debian trixie/main arm64 libpangoft2-1.0-0 arm64 1.56.3-1 [52.9 kB]
[33m
47% [79 libpangoft2-1.0-0 3993 B/52.9 kB 8%]                      3043 kB/s 29s[0m[33m
48% [Working]                                                     3043 kB/s 29s[0m
                                                                               
Get:80 http://deb.debian.org/debian trixie/main arm64 libpangocairo-1.0-0 arm64 1.56.3-1 [33.7 kB]
[33m
48% [80 libpangocairo-1.0-0 9497 B/33.7 kB 28%]                   3043 kB/s 29s[0m[33m
48% [Working]                                                     3043 kB/s 29s[0m
                                                                               
Get:81 http://deb.debian.org/debian trixie/main arm64 librsvg2-2 arm64 2.60.0+dfsg-1 [1588 kB]
[33m
48% [81 librsvg2-2 0 B/1588 kB 0%]                                3043 kB/s 29s[0m[33m
48% [81 librsvg2-2 1588 kB/1588 kB 100%]                          3043 kB/s 29s[0m[33m
48% [Working]                                                     3043 kB/s 29s[0m
                                                                               
Get:82 http://deb.debian.org/debian trixie/main arm64 libshine3 arm64 3.1.1-2+b2 [24.6 kB]
[33m
48% [82 libshine3 8713 B/24.6 kB 35%]                             3043 kB/s 29s[0m[33m
49% [Working]                                                     3043 kB/s 29s[0m
                                                                               
Get:83 http://deb.debian.org/debian trixie/main arm64 libsnappy1v5 arm64 1.2.2-1 [28.3 kB]
[33m
49% [83 libsnappy1v5 17.5 kB/28.3 kB 62%]                         3043 kB/s 29s[0m[33m
49% [Working]                                                     3043 kB/s 29s[0m
                                                                               
Get:84 http://deb.debian.org/debian trixie/main arm64 libspeex1 arm64 1.2.1-3 [50.4 kB]
[33m
49% [84 libspeex1 41.0 kB/50.4 kB 81%]                            3043 kB/s 28s[0m[33m
49% [Working]                                                     3043 kB/s 28s[0m
                                                                               
Get:85 http://deb.debian.org/debian trixie/main arm64 libsvtav1enc2 arm64 2.3.0+dfsg-1 [1558 kB]
[33m
49% [85 libsvtav1enc2 36.0 kB/1558 kB 2%]                         3043 kB/s 28s[0m[33m
50% [85 libsvtav1enc2 1558 kB/1558 kB 100%]                       3043 kB/s 28s[0m[33m
50% [Working]                                                     3043 kB/s 28s[0m
                                                                               
Get:86 http://deb.debian.org/debian trixie/main arm64 libsoxr0 arm64 0.1.3-4+b2 [54.9 kB]
[33m
50% [86 libsoxr0 8192 B/54.9 kB 15%]                              3043 kB/s 28s[0m[33m
50% [Working]                                                     3043 kB/s 28s[0m
                                                                               
Get:87 http://deb.debian.org/debian trixie/main arm64 libtheoradec1 arm64 1.2.0~alpha1+dfsg-6 [52.6 kB]
[33m
50% [87 libtheoradec1 16.4 kB/52.6 kB 31%]                        3043 kB/s 28s[0m[33m
50% [Working]                                                     3043 kB/s 28s[0m
                                                                               
Get:88 http://deb.debian.org/debian trixie/main arm64 libtheoraenc1 arm64 1.2.0~alpha1+dfsg-6 [99.1 kB]
[33m
50% [88 libtheoraenc1 28.6 kB/99.1 kB 29%]                        3043 kB/s 28s[0m[33m
50% [Working]                                                     3043 kB/s 28s[0m
                                                                               
Get:89 http://deb.debian.org/debian trixie/main arm64 libtwolame0 arm64 0.4.0-2+b2 [49.3 kB]
[33m
50% [89 libtwolame0 11.4 kB/49.3 kB 23%]                          3043 kB/s 28s[0m[33m
50% [Working]                                                     3043 kB/s 28s[0m
                                                                               
Get:90 http://deb.debian.org/debian trixie/main arm64 libvorbisenc2 arm64 1.3.7-3 [75.5 kB]
[33m
50% [90 libvorbisenc2 20.2 kB/75.5 kB 27%]                        3043 kB/s 28s[0m[33m
50% [Working]                                                     3043 kB/s 28s[0m
                                                                               
Get:91 http://deb.debian.org/debian trixie/main arm64 libvpx9 arm64 1.15.0-2.1+deb13u1 [1158 kB]
[33m
50% [91 libvpx9 20.7 kB/1158 kB 2%]                               3043 kB/s 28s[0m[33m
51% [Working]                                                     3043 kB/s 27s[0m
                                                                               
Get:92 http://deb.debian.org/debian trixie/main arm64 libwebpmux3 arm64 1.5.0-0.1 [125 kB]
[33m
51% [92 libwebpmux3 12.4 kB/125 kB 10%]                           3043 kB/s 27s[0m[33m
51% [Working]                                                     3043 kB/s 27s[0m
                                                                               
Get:93 http://deb.debian.org/debian trixie/main arm64 libx264-164 arm64 2:0.164.3108+git31e19f9-2+b1 [454 kB]
[33m
51% [93 libx264-164 7018 B/454 kB 2%]                             3043 kB/s 27s[0m[33m
51% [Working]                                                     3043 kB/s 27s[0m
                                                                               
Get:94 http://deb.debian.org/debian trixie/main arm64 libx265-215 arm64 4.1-2 [1857 kB]
[33m
51% [94 libx265-215 0 B/1857 kB 0%]                               3043 kB/s 27s[0m[33m
52% [94 libx265-215 1627 kB/1857 kB 88%]                          3043 kB/s 27s[0m[33m
52% [Working]                                                     3043 kB/s 27s[0m
                                                                               
Get:95 http://deb.debian.org/debian trixie/main arm64 libxvidcore4 arm64 2:1.3.7-1+b2 [202 kB]
[33m
52% [95 libxvidcore4 17.4 kB/202 kB 9%]                           3043 kB/s 27s[0m[33m
53% [Working]                                                     3043 kB/s 27s[0m
                                                                               
Get:96 http://deb.debian.org/debian trixie/main arm64 libzvbi-common all 0.2.44-1 [71.4 kB]
[33m
53% [96 libzvbi-common 11.2 kB/71.4 kB 16%]                       3043 kB/s 27s[0m[33m
53% [Working]                                                     3043 kB/s 27s[0m
                                                                               
Get:97 http://deb.debian.org/debian trixie/main arm64 libzvbi0t64 arm64 0.2.44-1 [262 kB]
[33m
53% [97 libzvbi0t64 24.6 kB/262 kB 9%]                            3043 kB/s 27s[0m[33m
53% [Working]                                                     3043 kB/s 27s[0m
                                                                               
Get:98 http://deb.debian.org/debian trixie/main arm64 libraw1394-11 arm64 2.1.2-2+b2 [38.1 kB]
[33m
53% [98 libraw1394-11 4758 B/38.1 kB 12%]                         3043 kB/s 27s[0m[33m
53% [Working]                                                     3043 kB/s 26s[0m
                                                                               
Get:99 http://deb.debian.org/debian trixie/main arm64 libavc1394-0 arm64 0.5.4-5+b2 [17.9 kB]
[33m
53% [99 libavc1394-0 10.6 kB/17.9 kB 59%]                         3043 kB/s 26s[0m[33m
53% [Working]                                                     3043 kB/s 26s[0m
                                                                               
Get:100 http://deb.debian.org/debian trixie/main arm64 libunibreak6 arm64 6.1-3 [21.5 kB]
[33m
53% [100 libunibreak6 3408 B/21.5 kB 16%]                         3043 kB/s 26s[0m[33m
53% [Working]                                                     3043 kB/s 26s[0m
                                                                               
Get:101 http://deb.debian.org/debian trixie/main arm64 libass9 arm64 1:0.17.3-1+deb13u1 [101 kB]
[33m
53% [101 libass9 12.9 kB/101 kB 13%]                              3043 kB/s 26s[0m[33m
53% [Working]                                                     3043 kB/s 26s[0m
                                                                               
Get:102 http://deb.debian.org/debian trixie/main arm64 libudfread0 arm64 1.1.2-1+b2 [17.3 kB]
[33m
53% [102 libudfread0 331 B/17.3 kB 2%]                            3043 kB/s 26s[0m[33m
54% [Working]                                                     3043 kB/s 26s[0m
                                                                               
Get:103 http://deb.debian.org/debian trixie/main arm64 libbluray2 arm64 1:1.3.4-1+b2 [126 kB]
[33m
54% [103 libbluray2 9642 B/126 kB 8%]                             3043 kB/s 26s[0m[33m
54% [Working]                                                     3043 kB/s 26s[0m
                                                                               
Get:104 http://deb.debian.org/debian trixie/main arm64 libchromaprint1 arm64 1.5.1-7 [38.9 kB]
[33m
54% [104 libchromaprint1 1734 B/38.9 kB 4%]                       3043 kB/s 26s[0m[33m
54% [Working]                                                     3043 kB/s 26s[0m
                                                                               
Get:105 http://deb.debian.org/debian trixie/main arm64 libdvdnav4 arm64 6.1.1-3+b1 [41.0 kB]
[33m
54% [105 libdvdnav4 12.3 kB/41.0 kB 30%]                          3043 kB/s 26s[0m[33m
54% [Working]                                                     3043 kB/s 26s[0m
                                                                               
Get:106 http://deb.debian.org/debian trixie/main arm64 libgme0 arm64 0.6.3-7+b2 [120 kB]
[33m
54% [106 libgme0 1126 B/120 kB 1%]                                3043 kB/s 26s[0m[33m
54% [Working]                                                     3043 kB/s 26s[0m
                                                                               
Get:107 http://deb.debian.org/debian trixie/main arm64 libmpg123-0t64 arm64 1.32.10-1+deb13u1 [143 kB]
[33m
54% [107 libmpg123-0t64 0 B/143 kB 0%]                            3043 kB/s 26s[0m[33m
54% [Working]                                                     3043 kB/s 26s[0m
                                                                               
Get:108 http://deb.debian.org/debian trixie/main arm64 libvorbisfile3 arm64 1.3.7-3 [20.1 kB]
[33m
54% [108 libvorbisfile3 1827 B/20.1 kB 9%]                        3043 kB/s 26s[0m[33m
54% [Working]                                                     3043 kB/s 26s[0m
                                                                               
Get:109 http://deb.debian.org/debian trixie/main arm64 libopenmpt0t64 arm64 0.7.13-1+b1 [745 kB]
[33m
54% [109 libopenmpt0t64 15.6 kB/745 kB 2%]                        3043 kB/s 26s[0m[33m
55% [Working]                                                     3043 kB/s 26s[0m
                                                                               
Get:110 http://deb.debian.org/debian trixie/main arm64 librabbitmq4 arm64 0.15.0-1+deb13u1 [41.1 kB]
[33m
55% [110 librabbitmq4 41.1 kB/41.1 kB 100%]                       3043 kB/s 26s[0m[33m
55% [Working]                                                     3043 kB/s 26s[0m
                                                                               
Get:111 http://deb.debian.org/debian trixie/main arm64 libcjson1 arm64 1.7.18-3.1+deb13u1 [29.0 kB]
[33m
55% [111 libcjson1 28.3 kB/29.0 kB 98%]                           3043 kB/s 26s[0m[33m
55% [Working]                                                     3043 kB/s 26s[0m
                                                                               
Get:112 http://deb.debian.org/debian trixie/main arm64 libmbedcrypto16 arm64 3.6.5-0.1~deb13u1 [347 kB]
[33m
55% [112 libmbedcrypto16 21.7 kB/347 kB 6%]                       3043 kB/s 26s[0m[33m
55% [Working]                                                     3043 kB/s 26s[0m
                                                                               
Get:113 http://deb.debian.org/debian trixie/main arm64 librist4 arm64 0.2.11+dfsg-1 [69.0 kB]
[33m
55% [113 librist4 17.1 kB/69.0 kB 25%]                            3043 kB/s 26s[0m[33m
56% [Working]                                                     3043 kB/s 26s[0m
                                                                               
Get:114 http://deb.debian.org/debian trixie/main arm64 libsrt1.5-gnutls arm64 1.5.4-1 [300 kB]
[33m
56% [114 libsrt1.5-gnutls 0 B/300 kB 0%]                          3043 kB/s 26s[0m[33m
56% [Working]                                                     3161 kB/s 25s[0m
                                                                               
Get:115 http://deb.debian.org/debian trixie/main arm64 libssh-4 arm64 0.11.2-1+deb13u1 [196 kB]
[33m
56% [115 libssh-4 0 B/196 kB 0%]                                  3161 kB/s 25s[0m[33m
56% [Working]                                                     3161 kB/s 25s[0m
                                                                               
Get:116 http://deb.debian.org/debian trixie/main arm64 libnorm1t64 arm64 1.5.9+dfsg-3.1+b2 [205 kB]
[33m
56% [116 libnorm1t64 0 B/205 kB 0%]                               3161 kB/s 25s[0m[33m
56% [Working]                                                     3161 kB/s 25s[0m
                                                                               
Get:117 http://deb.debian.org/debian trixie/main arm64 libpgm-5.3-0t64 arm64 5.3.128~dfsg-2.1+b1 [152 kB]
[33m
56% [117 libpgm-5.3-0t64 0 B/152 kB 0%]                           3161 kB/s 25s[0m[33m
56% [Working]                                                     3161 kB/s 25s[0m
                                                                               
Get:118 http://deb.debian.org/debian trixie/main arm64 libsodium23 arm64 1.0.18-1+deb13u1 [120 kB]
[33m
56% [118 libsodium23 8664 B/120 kB 7%]                            3161 kB/s 25s[0m[33m
57% [Working]                                                     3161 kB/s 25s[0m
                                                                               
Get:119 http://deb.debian.org/debian trixie/main arm64 libzmq5 arm64 4.3.5-1+b3 [253 kB]
[33m
57% [119 libzmq5 0 B/253 kB 0%]                                   3161 kB/s 25s[0m[33m
57% [Working]                                                     3161 kB/s 25s[0m
                                                                               
Get:120 http://deb.debian.org/debian trixie/main arm64 libbs2b0 arm64 3.1.0+dfsg-8+b1 [11.4 kB]
[33m
57% [120 libbs2b0 8953 B/11.4 kB 78%]                             3161 kB/s 25s[0m[33m
57% [Working]                                                     3161 kB/s 25s[0m
                                                                               
Get:121 http://deb.debian.org/debian trixie/main arm64 libflite1 arm64 2.2-7 [12.8 MB]
[33m
57% [121 libflite1 8258 B/12.8 MB 0%]                             3161 kB/s 24s[0m[33m
58% [121 libflite1 1665 kB/12.8 MB 13%]                           3161 kB/s 24s[0m[33m
58% [121 libflite1 3277 kB/12.8 MB 26%]                           3161 kB/s 23s[0m[33m
59% [121 libflite1 4891 kB/12.8 MB 38%]                           3161 kB/s 23s[0m[33m
60% [121 libflite1 6496 kB/12.8 MB 51%]                           3161 kB/s 22s[0m[33m
61% [121 libflite1 8115 kB/12.8 MB 63%]                           3161 kB/s 22s[0m[33m
61% [121 libflite1 9728 kB/12.8 MB 76%]                           3161 kB/s 21s[0m[33m
62% [121 libflite1 11.3 MB/12.8 MB 88%]                           3161 kB/s 21s[0m[33m
63% [121 libflite1 12.8 MB/12.8 MB 100%]                          3161 kB/s 20s[0m[33m
63% [121 libflite1 12.8 MB/12.8 MB 100%]                          3161 kB/s 20s[0m[33m
63% [Working]                                                     3161 kB/s 20s[0m
                                                                               
Get:122 http://deb.debian.org/debian trixie/main arm64 libserd-0-0 arm64 0.32.4-1 [45.6 kB]
[33m
63% [122 libserd-0-0 8681 B/45.6 kB 19%]                          3161 kB/s 20s[0m[33m
63% [Working]                                                     3161 kB/s 20s[0m
                                                                               
Get:123 http://deb.debian.org/debian trixie/main arm64 libzix-0-0 arm64 0.6.2-1 [22.5 kB]
[33m
63% [123 libzix-0-0 14.6 kB/22.5 kB 65%]                          3161 kB/s 20s[0m[33m
63% [Working]                                                     3161 kB/s 20s[0m
                                                                               
Get:124 http://deb.debian.org/debian trixie/main arm64 libsord-0-0 arm64 0.16.18-1 [17.3 kB]
[33m
63% [124 libsord-0-0 17.3 kB/17.3 kB 100%]                        3161 kB/s 20s[0m[33m
63% [Working]                                                     3161 kB/s 20s[0m
                                                                               
Get:125 http://deb.debian.org/debian trixie/main arm64 libsratom-0-0 arm64 0.6.18-1 [16.0 kB]
[33m
63% [125 libsratom-0-0 16.0 kB/16.0 kB 100%]                      3161 kB/s 20s[0m[33m
63% [Working]                                                     3161 kB/s 20s[0m
                                                                               
Get:126 http://deb.debian.org/debian trixie/main arm64 liblilv-0-0 arm64 0.24.26-1 [41.7 kB]
[33m
63% [126 liblilv-0-0 22.0 kB/41.7 kB 53%]                         3161 kB/s 20s[0m[33m
63% [Working]                                                     3161 kB/s 20s[0m
                                                                               
Get:127 http://deb.debian.org/debian trixie/main arm64 libmysofa1 arm64 1.3.3+dfsg-1 [1157 kB]
[33m
63% [127 libmysofa1 45.0 kB/1157 kB 4%]                           3161 kB/s 20s[0m[33m
64% [Working]                                                     3161 kB/s 20s[0m
                                                                               
Get:128 http://deb.debian.org/debian trixie/main arm64 libvulkan1 arm64 1.4.309.0-1 [127 kB]
[33m
64% [128 libvulkan1 64.8 kB/127 kB 51%]                           3161 kB/s 20s[0m[33m
64% [Working]                                                     3161 kB/s 20s[0m
                                                                               
Get:129 http://deb.debian.org/debian trixie/main arm64 libplacebo349 arm64 7.349.0-3 [2275 kB]
[33m
64% [129 libplacebo349 0 B/2275 kB 0%]                            3161 kB/s 20s[0m[33m
65% [129 libplacebo349 1687 kB/2275 kB 74%]                       3161 kB/s 19s[0m[33m
65% [Working]                                                     3161 kB/s 19s[0m
                                                                               
Get:130 http://deb.debian.org/debian trixie/main arm64 libblas3 arm64 3.12.1-6 [104 kB]
[33m
65% [130 libblas3 22.8 kB/104 kB 22%]                             3161 kB/s 19s[0m[33m
66% [Working]                                                     3161 kB/s 19s[0m
                                                                               
Get:131 http://deb.debian.org/debian trixie/main arm64 libgfortran5 arm64 14.2.0-19 [361 kB]
[33m
66% [131 libgfortran5 0 B/361 kB 0%]                              3161 kB/s 19s[0m[33m
66% [Working]                                                     3161 kB/s 19s[0m
                                                                               
Get:132 http://deb.debian.org/debian trixie/main arm64 liblapack3 arm64 3.12.1-6 [1820 kB]
[33m
66% [132 liblapack3 424 B/1820 kB 0%]                             3161 kB/s 19s[0m[33m
67% [132 liblapack3 1622 kB/1820 kB 89%]                          3037 kB/s 19s[0m[33m
67% [Working]                                                     3037 kB/s 19s[0m
                                                                               
Get:133 http://deb.debian.org/debian trixie/main arm64 libasyncns0 arm64 0.8-6+b5 [11.7 kB]
[33m
67% [133 libasyncns0 11.7 kB/11.7 kB 100%]                        3037 kB/s 19s[0m[33m
67% [Working]                                                     3037 kB/s 19s[0m
                                                                               
Get:134 http://deb.debian.org/debian trixie/main arm64 libsndfile1 arm64 1.2.2-2+deb13u1 [186 kB]
[33m
67% [134 libsndfile1 16.3 kB/186 kB 9%]                           3037 kB/s 19s[0m[33m
67% [Working]                                                     3037 kB/s 19s[0m
                                                                               
Get:135 http://deb.debian.org/debian trixie/main arm64 libsphinxbase3t64 arm64 0.8+5prealpha+1-21+b1 [112 kB]
[33m
67% [135 libsphinxbase3t64 0 B/112 kB 0%]                         3037 kB/s 19s[0m[33m
67% [Working]                                                     3037 kB/s 19s[0m
                                                                               
Get:136 http://deb.debian.org/debian trixie/main arm64 libpocketsphinx3 arm64 0.8+5prealpha+1-15+b4 [115 kB]
[33m
67% [136 libpocketsphinx3 15.8 kB/115 kB 14%]                     3037 kB/s 19s[0m[33m
67% [Working]                                                     3037 kB/s 19s[0m
                                                                               
Get:137 http://deb.debian.org/debian trixie/main arm64 libfftw3-double3 arm64 3.3.10-2+b1 [337 kB]
[33m
67% [137 libfftw3-double3 5898 B/337 kB 2%]                       3037 kB/s 19s[0m[33m
68% [Working]                                                     3037 kB/s 19s[0m
                                                                               
Get:138 http://deb.debian.org/debian trixie/main arm64 librubberband2 arm64 3.3.0+dfsg-2+b3 [123 kB]
[33m
68% [138 librubberband2 0 B/123 kB 0%]                            3037 kB/s 19s[0m[33m
68% [Working]                                                     3037 kB/s 19s[0m
                                                                               
Get:139 http://deb.debian.org/debian trixie/main arm64 libvidstab1.1 arm64 1.1.0-2+b2 [36.8 kB]
[33m
68% [139 libvidstab1.1 3482 B/36.8 kB 9%]                         3037 kB/s 19s[0m[33m
68% [Working]                                                     3037 kB/s 19s[0m
                                                                               
Get:140 http://deb.debian.org/debian trixie/main arm64 libzimg2 arm64 3.0.5+ds1-1+b2 [117 kB]
[33m
68% [140 libzimg2 4908 B/117 kB 4%]                               3037 kB/s 19s[0m[33m
68% [Working]                                                     3037 kB/s 19s[0m
                                                                               
Get:141 http://deb.debian.org/debian trixie/main arm64 libcaca0 arm64 0.99.beta20-5+deb13u1 [196 kB]
[33m
68% [141 libcaca0 0 B/196 kB 0%]                                  3037 kB/s 19s[0m[33m
68% [Working]                                                     3037 kB/s 19s[0m
                                                                               
Get:142 http://deb.debian.org/debian trixie/main arm64 libcdio19t64 arm64 2.2.0-4.1~deb13u1 [59.3 kB]
[33m
68% [142 libcdio19t64 10.8 kB/59.3 kB 18%]                        3037 kB/s 19s[0m[33m
68% [Working]                                                     3037 kB/s 19s[0m
                                                                               
Get:143 http://deb.debian.org/debian trixie/main arm64 libcdio-cdda2t64 arm64 10.2+2.0.2-1+b1 [17.2 kB]
[33m
68% [143 libcdio-cdda2t64 12.7 kB/17.2 kB 74%]                    3037 kB/s 19s[0m[33m
69% [Working]                                                     3037 kB/s 19s[0m
                                                                               
Get:144 http://deb.debian.org/debian trixie/main arm64 libcdio-paranoia2t64 arm64 10.2+2.0.2-1+b1 [16.5 kB]
[33m
69% [144 libcdio-paranoia2t64 6316 B/16.5 kB 38%]                 3037 kB/s 19s[0m[33m
69% [Working]                                                     3037 kB/s 19s[0m
                                                                               
Get:145 http://deb.debian.org/debian trixie/main arm64 libdc1394-25 arm64 2.2.6-5 [106 kB]
[33m
69% [145 libdc1394-25 6372 B/106 kB 6%]                           3037 kB/s 19s[0m[33m
69% [Working]                                                     3037 kB/s 19s[0m
                                                                               
Get:146 http://deb.debian.org/debian trixie/main arm64 libepoxy0 arm64 1.5.10-2 [200 kB]
[33m
69% [146 libepoxy0 0 B/200 kB 0%]                                 3037 kB/s 19s[0m[33m
69% [Working]                                                     3037 kB/s 19s[0m
                                                                               
Get:147 http://deb.debian.org/debian trixie/main arm64 libglvnd0 arm64 1.7.0-1+b2 [41.6 kB]
[33m
69% [147 libglvnd0 5315 B/41.6 kB 13%]                            3037 kB/s 19s[0m[33m
69% [Working]                                                     3037 kB/s 19s[0m
                                                                               
Get:148 http://deb.debian.org/debian trixie/main arm64 libxcb-glx0 arm64 1.17.0-2+b1 [123 kB]
[33m
69% [148 libxcb-glx0 461 B/123 kB 0%]                             3037 kB/s 19s[0m[33m
69% [Working]                                                     3037 kB/s 19s[0m
                                                                               
Get:149 http://deb.debian.org/debian trixie/main arm64 libxcb-present0 arm64 1.17.0-2+b1 [106 kB]
[33m
69% [149 libxcb-present0 0 B/106 kB 0%]                           3037 kB/s 19s[0m[33m
69% [Working]                                                     3037 kB/s 19s[0m
                                                                               
Get:150 http://deb.debian.org/debian trixie/main arm64 libxcb-xfixes0 arm64 1.17.0-2+b1 [110 kB]
[33m
69% [150 libxcb-xfixes0 258 B/110 kB 0%]                          3037 kB/s 19s[0m[33m
70% [Working]                                                     3037 kB/s 19s[0m
                                                                               
Get:151 http://deb.debian.org/debian trixie/main arm64 libxxf86vm1 arm64 1:1.1.4-1+b4 [19.2 kB]
[33m
70% [151 libxxf86vm1 8264 B/19.2 kB 43%]                          3037 kB/s 19s[0m[33m
70% [Working]                                                     3037 kB/s 19s[0m
                                                                               
Get:152 http://deb.debian.org/debian trixie/main arm64 libz3-4 arm64 4.13.3-1 [7507 kB]
[33m
70% [152 libz3-4 12.8 kB/7507 kB 0%]                              3037 kB/s 19s[0m[33m
70% [152 libz3-4 1632 kB/7507 kB 22%]                             3037 kB/s 18s[0m[33m
71% [152 libz3-4 3253 kB/7507 kB 43%]                             3037 kB/s 18s[0m[33m
72% [152 libz3-4 4859 kB/7507 kB 65%]                             3037 kB/s 17s[0m[33m
73% [152 libz3-4 6479 kB/7507 kB 86%]                             3037 kB/s 17s[0m[33m
73% [152 libz3-4 7507 kB/7507 kB 100%]                            3037 kB/s 16s[0m[33m
73% [Working]                                                     3037 kB/s 16s[0m
                                                                               
Get:153 http://deb.debian.org/debian trixie/main arm64 libllvm19 arm64 1:19.1.7-3+b1 [23.3 MB]
[33m
73% [153 libllvm19 43.4 kB/23.3 MB 0%]                            3037 kB/s 16s[0m[33m
74% [153 libllvm19 2306 kB/23.3 MB 10%]                           3037 kB/s 15s[0m[33m
75% [153 libllvm19 3916 kB/23.3 MB 17%]                           3037 kB/s 15s[0m[33m
76% [153 libllvm19 5483 kB/23.3 MB 24%]                           3037 kB/s 14s[0m[33m
76% [153 libllvm19 7106 kB/23.3 MB 31%]                           3037 kB/s 14s[0m[33m
77% [153 libllvm19 8719 kB/23.3 MB 37%]                           3037 kB/s 13s[0m[33m
78% [153 libllvm19 10.3 MB/23.3 MB 44%]                           3128 kB/s 12s[0m[33m
79% [153 libllvm19 11.9 MB/23.3 MB 51%]                           3128 kB/s 12s[0m[33m
79% [153 libllvm19 13.5 MB/23.3 MB 58%]                           3128 kB/s 11s[0m[33m
80% [153 libllvm19 15.2 MB/23.3 MB 65%]                           3128 kB/s 11s[0m[33m
81% [153 libllvm19 16.8 MB/23.3 MB 72%]                           3128 kB/s 10s[0m[33m
82% [153 libllvm19 18.4 MB/23.3 MB 79%]                           3128 kB/s 10s[0m[33m
82% [153 libllvm19 20.0 MB/23.3 MB 86%]                            3128 kB/s 9s[0m[33m
83% [153 libllvm19 21.6 MB/23.3 MB 93%]                            3128 kB/s 9s[0m[33m
84% [153 libllvm19 23.2 MB/23.3 MB 100%]                           3128 kB/s 8s[0m[33m
84% [153 libllvm19 23.3 MB/23.3 MB 100%]                           3128 kB/s 8s[0m[33m
84% [Waiting for headers]                                          3128 kB/s 8s[0m
                                                                               
Get:154 http://deb.debian.org/debian trixie/main arm64 libxcb-randr0 arm64 1.17.0-2+b1 [117 kB]
[33m
84% [Waiting for headers]                                          3128 kB/s 8s[0m
                                                                               
Get:155 http://deb.debian.org/debian trixie/main arm64 libxcb-sync1 arm64 1.17.0-2+b1 [109 kB]
[33m
84% [155 libxcb-sync1 36.1 kB/109 kB 33%]                          3128 kB/s 8s[0m[33m
84% [Working]                                                      3128 kB/s 8s[0m
                                                                               
Get:156 http://deb.debian.org/debian trixie/main arm64 libxshmfence1 arm64 1.3.3-1 [11.1 kB]
[33m
84% [156 libxshmfence1 11.1 kB/11.1 kB 100%]                       3128 kB/s 8s[0m[33m
84% [Working]                                                      3128 kB/s 8s[0m
                                                                               
Get:157 http://deb.debian.org/debian trixie/main arm64 libglx0 arm64 1.7.0-1+b2 [31.1 kB]
[33m
84% [157 libglx0 31.1 kB/31.1 kB 100%]                             3128 kB/s 8s[0m[33m
84% [Working]                                                      3128 kB/s 8s[0m
                                                                               
Get:158 http://deb.debian.org/debian trixie/main arm64 libgl1 arm64 1.7.0-1+b2 [90.9 kB]
[33m
84% [158 libgl1 13.8 kB/90.9 kB 15%]                               3128 kB/s 8s[0m[33m
85% [Working]                                                      3128 kB/s 8s[0m
                                                                               
Get:159 http://deb.debian.org/debian trixie/main arm64 libiec61883-0 arm64 1.2.0-7 [29.1 kB]
[33m
85% [159 libiec61883-0 29.1 kB/29.1 kB 100%]                       3128 kB/s 8s[0m[33m
85% [Working]                                                      3128 kB/s 8s[0m
                                                                               
Get:160 http://deb.debian.org/debian trixie/main arm64 libjack-jackd2-0 arm64 1.9.22~dfsg-4 [265 kB]
[33m
85% [160 libjack-jackd2-0 23.3 kB/265 kB 9%]                       3128 kB/s 8s[0m[33m
85% [Working]                                                      3128 kB/s 8s[0m
                                                                               
Get:161 http://deb.debian.org/debian trixie/main arm64 libopenal-data all 1:1.24.2-1 [168 kB]
[33m
85% [161 libopenal-data 19.5 kB/168 kB 12%]                        3128 kB/s 8s[0m[33m
85% [Working]                                                      3128 kB/s 8s[0m
                                                                               
Get:162 http://deb.debian.org/debian trixie/main arm64 libopenal1 arm64 1:1.24.2-1 [577 kB]
[33m
85% [162 libopenal1 23.4 kB/577 kB 4%]                             3128 kB/s 8s[0m[33m
86% [Working]                                                      3128 kB/s 8s[0m
                                                                               
Get:163 http://deb.debian.org/debian trixie/main arm64 libdecor-0-0 arm64 0.2.2-2 [15.2 kB]
[33m
86% [163 libdecor-0-0 11.0 kB/15.2 kB 72%]                         3128 kB/s 8s[0m[33m
86% [Working]                                                      3128 kB/s 8s[0m
                                                                               
Get:164 http://deb.debian.org/debian trixie/main arm64 libxcursor1 arm64 1:1.2.3-1 [39.3 kB]
[33m
86% [164 libxcursor1 12.4 kB/39.3 kB 32%]                          3128 kB/s 8s[0m[33m
86% [Working]                                                      3128 kB/s 8s[0m
                                                                               
Get:165 http://deb.debian.org/debian trixie/main arm64 libxkbcommon0 arm64 1.7.0-2 [106 kB]
[33m
86% [165 libxkbcommon0 14.2 kB/106 kB 13%]                         3128 kB/s 8s[0m[33m
86% [Waiting for headers]                                          3128 kB/s 8s[0m
                                                                               
Get:166 http://deb.debian.org/debian trixie/main arm64 libxrandr2 arm64 2:1.5.4-1+b3 [35.9 kB]
[33m
86% [166 libxrandr2 8286 B/35.9 kB 23%]                            3128 kB/s 8s[0m[33m
86% [Working]                                                      3128 kB/s 8s[0m
                                                                               
Get:167 http://deb.debian.org/debian trixie/main arm64 libxss1 arm64 1:1.2.3-1+b3 [17.1 kB]
[33m
86% [167 libxss1 4760 B/17.1 kB 28%]                               3128 kB/s 8s[0m[33m
86% [Working]                                                      3128 kB/s 8s[0m
                                                                               
Get:168 http://deb.debian.org/debian trixie/main arm64 libsdl2-2.0-0 arm64 2.32.4+dfsg-1 [603 kB]
[33m
86% [168 libsdl2-2.0-0 2746 B/603 kB 0%]                           3128 kB/s 8s[0m[33m
87% [Working]                                                      3128 kB/s 8s[0m
                                                                               
Get:169 http://deb.debian.org/debian trixie/main arm64 libxcb-shape0 arm64 1.17.0-2+b1 [106 kB]
[33m
87% [169 libxcb-shape0 122 B/106 kB 0%]                            3128 kB/s 8s[0m[33m
87% [Working]                                                      3128 kB/s 8s[0m
                                                                               
Get:170 http://deb.debian.org/debian trixie/main arm64 libxv1 arm64 2:1.0.11-1.1+b3 [23.3 kB]
[33m
87% [170 libxv1 9098 B/23.3 kB 39%]                                3128 kB/s 8s[0m[33m
87% [Working]                                                      3128 kB/s 8s[0m
                                                                               
Get:171 http://deb.debian.org/debian trixie/main arm64 libaacs0 arm64 0.11.1-4+b1 [52.6 kB]
[33m
87% [171 libaacs0 13.9 kB/52.6 kB 26%]                             3128 kB/s 8s[0m[33m
87% [Working]                                                      3128 kB/s 7s[0m
                                                                               
Get:172 http://deb.debian.org/debian trixie/main arm64 libatk1.0-0t64 arm64 2.56.2-1+deb13u1 [50.2 kB]
[33m
87% [172 libatk1.0-0t64 11.1 kB/50.2 kB 22%]                       3128 kB/s 7s[0m[33m
87% [Working]                                                      3128 kB/s 7s[0m
                                                                               
Get:173 http://deb.debian.org/debian trixie/main arm64 libatk-bridge2.0-0t64 arm64 2.56.2-1+deb13u1 [65.0 kB]
[33m
87% [173 libatk-bridge2.0-0t64 477 B/65.0 kB 1%]                   3128 kB/s 7s[0m[33m
87% [Waiting for headers]                                          3128 kB/s 7s[0m
                                                                               
Get:174 http://deb.debian.org/debian trixie/main arm64 libavahi-client3 arm64 0.8-16 [46.7 kB]
[33m
87% [174 libavahi-client3 11.2 kB/46.7 kB 24%]                     3128 kB/s 7s[0m[33m
87% [Working]                                                      3128 kB/s 7s[0m
                                                                               
Get:175 http://deb.debian.org/debian trixie/main arm64 libbdplus0 arm64 0.2.0-4+b1 [49.7 kB]
[33m
87% [175 libbdplus0 9898 B/49.7 kB 20%]                            3128 kB/s 7s[0m[33m
87% [Working]                                                      3128 kB/s 7s[0m
                                                                               
Get:176 http://deb.debian.org/debian trixie/main arm64 libcloudproviders0 arm64 0.3.6-2 [27.4 kB]
[33m
87% [176 libcloudproviders0 1290 B/27.4 kB 5%]                     3128 kB/s 7s[0m[33m
88% [Working]                                                      3128 kB/s 7s[0m
                                                                               
Get:177 http://deb.debian.org/debian trixie/main arm64 libcolord2 arm64 1.4.7-3 [130 kB]
[33m
88% [177 libcolord2 12.2 kB/130 kB 9%]                             3128 kB/s 7s[0m[33m
88% [Working]                                                      3128 kB/s 7s[0m
                                                                               
Get:178 http://deb.debian.org/debian trixie/main arm64 libxcomposite1 arm64 1:0.4.6-1 [16.4 kB]
[33m
88% [178 libxcomposite1 13.1 kB/16.4 kB 80%]                       3128 kB/s 7s[0m[33m
88% [Working]                                                      3128 kB/s 7s[0m
                                                                               
Get:179 http://deb.debian.org/debian trixie/main arm64 libxdamage1 arm64 1:1.1.6-1+b2 [15.6 kB]
[33m
88% [179 libxdamage1 7448 B/15.6 kB 48%]                           3128 kB/s 7s[0m[33m
88% [Working]                                                      3128 kB/s 7s[0m
                                                                               
Get:180 http://deb.debian.org/debian trixie/main arm64 libxinerama1 arm64 2:1.1.4-3+b4 [16.0 kB]
[33m
88% [180 libxinerama1 5442 B/16.0 kB 34%]                          3128 kB/s 7s[0m[33m
88% [Working]                                                      3128 kB/s 7s[0m
                                                                               
Get:181 http://deb.debian.org/debian trixie/main arm64 libdecor-0-plugin-1-gtk arm64 0.2.2-2 [20.9 kB]
[33m
88% [181 libdecor-0-plugin-1-gtk 11.7 kB/20.9 kB 56%]              3128 kB/s 7s[0m[33m
88% [Working]                                                      3128 kB/s 7s[0m
                                                                               
Get:182 http://deb.debian.org/debian trixie/main arm64 libgdk-pixbuf2.0-bin arm64 2.42.12+dfsg-4+deb13u1 [19.2 kB]
[33m
88% [182 libgdk-pixbuf2.0-bin 13.2 kB/19.2 kB 69%]                 3128 kB/s 7s[0m[33m
88% [Working]                                                      3128 kB/s 7s[0m
                                                                               
Get:183 http://deb.debian.org/debian trixie/main arm64 librsvg2-common arm64 2.60.0+dfsg-1 [139 kB]
[33m
88% [183 librsvg2-common 7682 B/139 kB 6%]                         3128 kB/s 7s[0m[33m
88% [Working]                                                      3128 kB/s 7s[0m
                                                                               
Get:184 http://deb.debian.org/debian trixie/main arm64 libvdpau-va-gl1 arm64 0.4.2-2 [65.1 kB]
[33m
88% [184 libvdpau-va-gl1 12.3 kB/65.1 kB 19%]                      3128 kB/s 7s[0m[33m
89% [Working]                                                      3128 kB/s 7s[0m
                                                                               
Get:185 http://deb.debian.org/debian trixie/main arm64 pocketsphinx-en-us all 0.8+5prealpha+1-15 [24.3 MB]
[33m
89% [185 pocketsphinx-en-us 8511 B/24.3 MB 0%]                     3128 kB/s 7s[0m[33m
89% [185 pocketsphinx-en-us 1625 kB/24.3 MB 7%]                    3128 kB/s 7s[0m[33m
90% [185 pocketsphinx-en-us 3239 kB/24.3 MB 13%]                   3058 kB/s 6s[0m[33m
91% [185 pocketsphinx-en-us 4846 kB/24.3 MB 20%]                   3058 kB/s 6s[0m[33m
92% [185 pocketsphinx-en-us 6474 kB/24.3 MB 27%]                   3058 kB/s 5s[0m[33m
92% [185 pocketsphinx-en-us 8081 kB/24.3 MB 33%]                   3058 kB/s 5s[0m[33m
93% [185 pocketsphinx-en-us 9703 kB/24.3 MB 40%]                   3058 kB/s 4s[0m[33m
94% [185 pocketsphinx-en-us 11.3 MB/24.3 MB 47%]                   3058 kB/s 4s[0m[33m
94% [185 pocketsphinx-en-us 12.9 MB/24.3 MB 53%]                   3058 kB/s 3s[0m[33m
95% [185 pocketsphinx-en-us 14.5 MB/24.3 MB 60%]                   3058 kB/s 3s[0m[33m
96% [185 pocketsphinx-en-us 16.2 MB/24.3 MB 66%]                   3058 kB/s 2s[0m[33m
97% [185 pocketsphinx-en-us 17.8 MB/24.3 MB 73%]                   3058 kB/s 2s[0m[33m
97% [185 pocketsphinx-en-us 19.4 MB/24.3 MB 80%]                   3058 kB/s 1s[0m[33m
98% [185 pocketsphinx-en-us 21.0 MB/24.3 MB 86%]                   3058 kB/s 1s[0m[33m
99% [185 pocketsphinx-en-us 22.6 MB/24.3 MB 93%]                   3223 kB/s 0s[0m[33m
100% [185 pocketsphinx-en-us 24.2 MB/24.3 MB 100%]                 3223 kB/s 0s[0m[33m
100% [185 pocketsphinx-en-us 24.3 MB/24.3 MB 100%]                 3223 kB/s 0s[0m[33m
100% [185 pocketsphinx-en-us 24.3 MB/24.3 MB 100%]                 3223 kB/s 0s[0m[33m
100% [Working]                                                     3223 kB/s 0s[0m
                                                                               
Get:186 http://deb.debian.org/debian trixie/main arm64 va-driver-all arm64 2.22.0-3 [14.9 kB]
[33m
100% [186 va-driver-all 14.9 kB/14.9 kB 100%]                      3223 kB/s 0s[0m[33m
100% [Working]                                                     3223 kB/s 0s[0m
                                                                               
Get:187 http://deb.debian.org/debian trixie/main arm64 vdpau-driver-all arm64 1.5-3+b1 [4676 B]
[33m
100% [187 vdpau-driver-all 4676 B/4676 B 100%]                     3223 kB/s 0s[0m[33m
100% [Working]                                                     3223 kB/s 0s[0m
                                                                               
Fetched 176 MB in 57s (3076 kB/s)
debconf: unable to initialize frontend: Dialog
debconf: (Dialog frontend will not work on a dumb terminal, an emacs shell buffer, or without a controlling terminal.)
debconf: falling back to frontend: Readline

Extracting templates from packages: 16%
Extracting templates from packages: 32%
Extracting templates from packages: 48%
Extracting templates from packages: 64%
Extracting templates from packages: 80%
Extracting templates from packages: 96%
Extracting templates from packages: 100%
Preconfiguring packages ...
Selecting previously unselected package libgdk-pixbuf2.0-common.
(Reading database ... 
(Reading database ... 5%
(Reading database ... 10%
(Reading database ... 15%
(Reading database ... 20%
(Reading database ... 25%
(Reading database ... 30%
(Reading database ... 35%
(Reading database ... 40%
(Reading database ... 45%
(Reading database ... 50%
(Reading database ... 55%
(Reading database ... 60%
(Reading database ... 65%
(Reading database ... 70%
(Reading database ... 75%
(Reading database ... 80%
(Reading database ... 85%
(Reading database ... 90%
(Reading database ... 95%
(Reading database ... 100%
(Reading database ... 69279 files and directories currently installed.)
Preparing to unpack .../000-libgdk-pixbuf2.0-common_2.42.12+dfsg-4+deb13u1_all.deb ...
Unpacking libgdk-pixbuf2.0-common (2.42.12+dfsg-4+deb13u1) ...
Selecting previously unselected package libgdk-pixbuf-2.0-0:arm64.
Preparing to unpack .../001-libgdk-pixbuf-2.0-0_2.42.12+dfsg-4+deb13u1_arm64.deb ...
Unpacking libgdk-pixbuf-2.0-0:arm64 (2.42.12+dfsg-4+deb13u1) ...
Selecting previously unselected package gtk-update-icon-cache.
Preparing to unpack .../002-gtk-update-icon-cache_4.18.6+ds-2_arm64.deb ...
No diversion 'diversion of /usr/sbin/update-icon-caches to /usr/sbin/update-icon-caches.gtk2 by libgtk-3-bin', none removed.
No diversion 'diversion of /usr/share/man/man8/update-icon-caches.8.gz to /usr/share/man/man8/update-icon-caches.gtk2.8.gz by libgtk-3-bin', none removed.
Unpacking gtk-update-icon-cache (4.18.6+ds-2) ...
Selecting previously unselected package hicolor-icon-theme.
Preparing to unpack .../003-hicolor-icon-theme_0.18-2_all.deb ...
Unpacking hicolor-icon-theme (0.18-2) ...
Selecting previously unselected package adwaita-icon-theme.
Preparing to unpack .../004-adwaita-icon-theme_48.1-1_all.deb ...
Unpacking adwaita-icon-theme (48.1-1) ...
Selecting previously unselected package at-spi2-common.
Preparing to unpack .../005-at-spi2-common_2.56.2-1+deb13u1_all.deb ...
Unpacking at-spi2-common (2.56.2-1+deb13u1) ...
Selecting previously unselected package libxi6:arm64.
Preparing to unpack .../006-libxi6_2%3a1.8.2-1_arm64.deb ...
Unpacking libxi6:arm64 (2:1.8.2-1) ...
Selecting previously unselected package libatspi2.0-0t64:arm64.
Preparing to unpack .../007-libatspi2.0-0t64_2.56.2-1+deb13u1_arm64.deb ...
Unpacking libatspi2.0-0t64:arm64 (2.56.2-1+deb13u1) ...
Selecting previously unselected package x11-common.
Preparing to unpack .../008-x11-common_1%3a7.7+24+deb13u1_all.deb ...
Unpacking x11-common (1:7.7+24+deb13u1) ...
Selecting previously unselected package libxtst6:arm64.
Preparing to unpack .../009-libxtst6_2%3a1.2.5-1_arm64.deb ...
Unpacking libxtst6:arm64 (2:1.2.5-1) ...
Selecting previously unselected package dconf-service.
Preparing to unpack .../010-dconf-service_0.40.0-5_arm64.deb ...
Unpacking dconf-service (0.40.0-5) ...
Selecting previously unselected package dconf-gsettings-backend:arm64.
Preparing to unpack .../011-dconf-gsettings-backend_0.40.0-5_arm64.deb ...
Unpacking dconf-gsettings-backend:arm64 (0.40.0-5) ...
Selecting previously unselected package gsettings-desktop-schemas.
Preparing to unpack .../012-gsettings-desktop-schemas_48.0-1+rpt1_all.deb ...
Unpacking gsettings-desktop-schemas (48.0-1+rpt1) ...
Selecting previously unselected package at-spi2-core.
Preparing to unpack .../013-at-spi2-core_2.56.2-1+deb13u1_arm64.deb ...
Unpacking at-spi2-core (2.56.2-1+deb13u1) ...
Selecting previously unselected package libaom3:arm64.
Preparing to unpack .../014-libaom3_3.12.1-1_arm64.deb ...
Unpacking libaom3:arm64 (3.12.1-1) ...
Selecting previously unselected package libva2:arm64.
Preparing to unpack .../015-libva2_2.22.0-3_arm64.deb ...
Unpacking libva2:arm64 (2.22.0-3) ...
Selecting previously unselected package libva-drm2:arm64.
Preparing to unpack .../016-libva-drm2_2.22.0-3_arm64.deb ...
Unpacking libva-drm2:arm64 (2.22.0-3) ...
Selecting previously unselected package libx11-xcb1:arm64.
Preparing to unpack .../017-libx11-xcb1_2%3a1.8.12-1_arm64.deb ...
Unpacking libx11-xcb1:arm64 (2:1.8.12-1) ...
Selecting previously unselected package libxcb-dri3-0:arm64.
Preparing to unpack .../018-libxcb-dri3-0_1.17.0-2+b1_arm64.deb ...
Unpacking libxcb-dri3-0:arm64 (1.17.0-2+b1) ...
Selecting previously unselected package libxfixes3:arm64.
Preparing to unpack .../019-libxfixes3_1%3a6.0.0-2+b4_arm64.deb ...
Unpacking libxfixes3:arm64 (1:6.0.0-2+b4) ...
Selecting previously unselected package libva-x11-2:arm64.
Preparing to unpack .../020-libva-x11-2_2.22.0-3_arm64.deb ...
Unpacking libva-x11-2:arm64 (2.22.0-3) ...
Selecting previously unselected package libvdpau1:arm64.
Preparing to unpack .../021-libvdpau1_1.5-3+b1_arm64.deb ...
Unpacking libvdpau1:arm64 (1.5-3+b1) ...
Selecting previously unselected package ocl-icd-libopencl1:arm64.
Preparing to unpack .../022-ocl-icd-libopencl1_2.3.3-1_arm64.deb ...
Unpacking ocl-icd-libopencl1:arm64 (2.3.3-1) ...
Selecting previously unselected package libavutil59:arm64.
Preparing to unpack .../023-libavutil59_8%3a7.1.5-0+deb13u1+rpt1_arm64.deb ...
Unpacking libavutil59:arm64 (8:7.1.5-0+deb13u1+rpt1) ...
Selecting previously unselected package libfreetype6:arm64.
Preparing to unpack .../024-libfreetype6_2.13.3+dfsg-1+deb13u1_arm64.deb ...
Unpacking libfreetype6:arm64 (2.13.3+dfsg-1+deb13u1) ...
Selecting previously unselected package fonts-dejavu-mono.
Preparing to unpack .../025-fonts-dejavu-mono_2.37-8_all.deb ...
Unpacking fonts-dejavu-mono (2.37-8) ...
Selecting previously unselected package fonts-dejavu-core.
Preparing to unpack .../026-fonts-dejavu-core_2.37-8_all.deb ...
Unpacking fonts-dejavu-core (2.37-8) ...
Selecting previously unselected package fontconfig-config.
Preparing to unpack .../027-fontconfig-config_2.15.0-2.3_arm64.deb ...
Unpacking fontconfig-config (2.15.0-2.3) ...
Selecting previously unselected package libfontconfig1:arm64.
Preparing to unpack .../028-libfontconfig1_2.15.0-2.3_arm64.deb ...
Unpacking libfontconfig1:arm64 (2.15.0-2.3) ...
Selecting previously unselected package libpixman-1-0:arm64.
Preparing to unpack .../029-libpixman-1-0_0.46.4-1+rpt1_arm64.deb ...
Unpacking libpixman-1-0:arm64 (0.46.4-1+rpt1) ...
Selecting previously unselected package libxcb-render0:arm64.
Preparing to unpack .../030-libxcb-render0_1.17.0-2+b1_arm64.deb ...
Unpacking libxcb-render0:arm64 (1.17.0-2+b1) ...
Selecting previously unselected package libxcb-shm0:arm64.
Preparing to unpack .../031-libxcb-shm0_1.17.0-2+b1_arm64.deb ...
Unpacking libxcb-shm0:arm64 (1.17.0-2+b1) ...
Selecting previously unselected package libxrender1:arm64.
Preparing to unpack .../032-libxrender1_1%3a0.9.12-1_arm64.deb ...
Unpacking libxrender1:arm64 (1:0.9.12-1) ...
Selecting previously unselected package libcairo2:arm64.
Preparing to unpack .../033-libcairo2_1.18.4-1+rpt1_arm64.deb ...
Unpacking libcairo2:arm64 (1.18.4-1+rpt1) ...
Selecting previously unselected package libcodec2-1.2:arm64.
Preparing to unpack .../034-libcodec2-1.2_1.2.0-3_arm64.deb ...
Unpacking libcodec2-1.2:arm64 (1.2.0-3) ...
Selecting previously unselected package libdav1d7:arm64.
Preparing to unpack .../035-libdav1d7_1.5.1-1_arm64.deb ...
Unpacking libdav1d7:arm64 (1.5.1-1) ...
Selecting previously unselected package libgsm1:arm64.
Preparing to unpack .../036-libgsm1_1.0.22-1+b2_arm64.deb ...
Unpacking libgsm1:arm64 (1.0.22-1+b2) ...
Selecting previously unselected package libhwy1t64:arm64.
Preparing to unpack .../037-libhwy1t64_1.2.0-2+b2_arm64.deb ...
Unpacking libhwy1t64:arm64 (1.2.0-2+b2) ...
Selecting previously unselected package liblcms2-2:arm64.
Preparing to unpack .../038-liblcms2-2_2.16-2+deb13u2_arm64.deb ...
Unpacking liblcms2-2:arm64 (2.16-2+deb13u2) ...
Selecting previously unselected package libjxl0.11:arm64.
Preparing to unpack .../039-libjxl0.11_0.11.2-0.1~deb13u2_arm64.deb ...
Unpacking libjxl0.11:arm64 (0.11.2-0.1~deb13u2) ...
Selecting previously unselected package libmp3lame0:arm64.
Preparing to unpack .../040-libmp3lame0_3.100-6+b3_arm64.deb ...
Unpacking libmp3lame0:arm64 (3.100-6+b3) ...
Selecting previously unselected package libopenjp2-7:arm64.
Preparing to unpack .../041-libopenjp2-7_2.5.3-2.1~deb13u2_arm64.deb ...
Unpacking libopenjp2-7:arm64 (2.5.3-2.1~deb13u2) ...
Selecting previously unselected package libopus0:arm64.
Preparing to unpack .../042-libopus0_1.5.2-2_arm64.deb ...
Unpacking libopus0:arm64 (1.5.2-2) ...
Selecting previously unselected package librav1e0.7:arm64.
Preparing to unpack .../043-librav1e0.7_0.7.1-9+b2_arm64.deb ...
Unpacking librav1e0.7:arm64 (0.7.1-9+b2) ...
Selecting previously unselected package libcairo-gobject2:arm64.
Preparing to unpack .../044-libcairo-gobject2_1.18.4-1+rpt1_arm64.deb ...
Unpacking libcairo-gobject2:arm64 (1.18.4-1+rpt1) ...
Selecting previously unselected package fontconfig.
Preparing to unpack .../045-fontconfig_2.15.0-2.3_arm64.deb ...
Unpacking fontconfig (2.15.0-2.3) ...
Selecting previously unselected package libfribidi0:arm64.
Preparing to unpack .../046-libfribidi0_1.0.16-1_arm64.deb ...
Unpacking libfribidi0:arm64 (1.0.16-1) ...
Selecting previously unselected package libgraphite2-3:arm64.
Preparing to unpack .../047-libgraphite2-3_1.3.14-2+deb13u1_arm64.deb ...
Unpacking libgraphite2-3:arm64 (1.3.14-2+deb13u1) ...
Selecting previously unselected package libharfbuzz0b:arm64.
Preparing to unpack .../048-libharfbuzz0b_10.2.0-1+deb13u1_arm64.deb ...
Unpacking libharfbuzz0b:arm64 (10.2.0-1+deb13u1) ...
Selecting previously unselected package libthai-data.
Preparing to unpack .../049-libthai-data_0.1.29-2_all.deb ...
Unpacking libthai-data (0.1.29-2) ...
Selecting previously unselected package libdatrie1:arm64.
Preparing to unpack .../050-libdatrie1_0.2.13-3+b1_arm64.deb ...
Unpacking libdatrie1:arm64 (0.2.13-3+b1) ...
Selecting previously unselected package libthai0:arm64.
Preparing to unpack .../051-libthai0_0.1.29-2+b1_arm64.deb ...
Unpacking libthai0:arm64 (0.1.29-2+b1) ...
Selecting previously unselected package libpango-1.0-0:arm64.
Preparing to unpack .../052-libpango-1.0-0_1.56.3-1_arm64.deb ...
Unpacking libpango-1.0-0:arm64 (1.56.3-1) ...
Selecting previously unselected package libpangoft2-1.0-0:arm64.
Preparing to unpack .../053-libpangoft2-1.0-0_1.56.3-1_arm64.deb ...
Unpacking libpangoft2-1.0-0:arm64 (1.56.3-1) ...
Selecting previously unselected package libpangocairo-1.0-0:arm64.
Preparing to unpack .../054-libpangocairo-1.0-0_1.56.3-1_arm64.deb ...
Unpacking libpangocairo-1.0-0:arm64 (1.56.3-1) ...
Selecting previously unselected package librsvg2-2:arm64.
Preparing to unpack .../055-librsvg2-2_2.60.0+dfsg-1_arm64.deb ...
Unpacking librsvg2-2:arm64 (2.60.0+dfsg-1) ...
Selecting previously unselected package libshine3:arm64.
Preparing to unpack .../056-libshine3_3.1.1-2+b2_arm64.deb ...
Unpacking libshine3:arm64 (3.1.1-2+b2) ...
Selecting previously unselected package libsnappy1v5:arm64.
Preparing to unpack .../057-libsnappy1v5_1.2.2-1_arm64.deb ...
Unpacking libsnappy1v5:arm64 (1.2.2-1) ...
Selecting previously unselected package libspeex1:arm64.
Preparing to unpack .../058-libspeex1_1.2.1-3_arm64.deb ...
Unpacking libspeex1:arm64 (1.2.1-3) ...
Selecting previously unselected package libsvtav1enc2:arm64.
Preparing to unpack .../059-libsvtav1enc2_2.3.0+dfsg-1_arm64.deb ...
Unpacking libsvtav1enc2:arm64 (2.3.0+dfsg-1) ...
Selecting previously unselected package libsoxr0:arm64.
Preparing to unpack .../060-libsoxr0_0.1.3-4+b2_arm64.deb ...
Unpacking libsoxr0:arm64 (0.1.3-4+b2) ...
Selecting previously unselected package libswresample5:arm64.
Preparing to unpack .../061-libswresample5_8%3a7.1.5-0+deb13u1+rpt1_arm64.deb ...
Unpacking libswresample5:arm64 (8:7.1.5-0+deb13u1+rpt1) ...
Selecting previously unselected package libtheoradec1:arm64.
Preparing to unpack .../062-libtheoradec1_1.2.0~alpha1+dfsg-6_arm64.deb ...
Unpacking libtheoradec1:arm64 (1.2.0~alpha1+dfsg-6) ...
Selecting previously unselected package libtheoraenc1:arm64.
Preparing to unpack .../063-libtheoraenc1_1.2.0~alpha1+dfsg-6_arm64.deb ...
Unpacking libtheoraenc1:arm64 (1.2.0~alpha1+dfsg-6) ...
Selecting previously unselected package libtwolame0:arm64.
Preparing to unpack .../064-libtwolame0_0.4.0-2+b2_arm64.deb ...
Unpacking libtwolame0:arm64 (0.4.0-2+b2) ...
Selecting previously unselected package libvorbisenc2:arm64.
Preparing to unpack .../065-libvorbisenc2_1.3.7-3_arm64.deb ...
Unpacking libvorbisenc2:arm64 (1.3.7-3) ...
Selecting previously unselected package libvpx9:arm64.
Preparing to unpack .../066-libvpx9_1.15.0-2.1+deb13u1_arm64.deb ...
Unpacking libvpx9:arm64 (1.15.0-2.1+deb13u1) ...
Selecting previously unselected package libwebpmux3:arm64.
Preparing to unpack .../067-libwebpmux3_1.5.0-0.1_arm64.deb ...
Unpacking libwebpmux3:arm64 (1.5.0-0.1) ...
Selecting previously unselected package libx264-164:arm64.
Preparing to unpack .../068-libx264-164_2%3a0.164.3108+git31e19f9-2+b1_arm64.deb ...
Unpacking libx264-164:arm64 (2:0.164.3108+git31e19f9-2+b1) ...
Selecting previously unselected package libx265-215:arm64.
Preparing to unpack .../069-libx265-215_4.1-2_arm64.deb ...
Unpacking libx265-215:arm64 (4.1-2) ...
Selecting previously unselected package libxvidcore4:arm64.
Preparing to unpack .../070-libxvidcore4_2%3a1.3.7-1+b2_arm64.deb ...
Unpacking libxvidcore4:arm64 (2:1.3.7-1+b2) ...
Selecting previously unselected package libzvbi-common.
Preparing to unpack .../071-libzvbi-common_0.2.44-1_all.deb ...
Unpacking libzvbi-common (0.2.44-1) ...
Selecting previously unselected package libzvbi0t64:arm64.
Preparing to unpack .../072-libzvbi0t64_0.2.44-1_arm64.deb ...
Unpacking libzvbi0t64:arm64 (0.2.44-1) ...
Selecting previously unselected package libavcodec61:arm64.
Preparing to unpack .../073-libavcodec61_8%3a7.1.5-0+deb13u1+rpt1_arm64.deb ...
Unpacking libavcodec61:arm64 (8:7.1.5-0+deb13u1+rpt1) ...
Selecting previously unselected package libraw1394-11:arm64.
Preparing to unpack .../074-libraw1394-11_2.1.2-2+b2_arm64.deb ...
Unpacking libraw1394-11:arm64 (2.1.2-2+b2) ...
Selecting previously unselected package libavc1394-0:arm64.
Preparing to unpack .../075-libavc1394-0_0.5.4-5+b2_arm64.deb ...
Unpacking libavc1394-0:arm64 (0.5.4-5+b2) ...
Selecting previously unselected package libunibreak6:arm64.
Preparing to unpack .../076-libunibreak6_6.1-3_arm64.deb ...
Unpacking libunibreak6:arm64 (6.1-3) ...
Selecting previously unselected package libass9:arm64.
Preparing to unpack .../077-libass9_1%3a0.17.3-1+deb13u1_arm64.deb ...
Unpacking libass9:arm64 (1:0.17.3-1+deb13u1) ...
Selecting previously unselected package libudfread0:arm64.
Preparing to unpack .../078-libudfread0_1.1.2-1+b2_arm64.deb ...
Unpacking libudfread0:arm64 (1.1.2-1+b2) ...
Selecting previously unselected package libbluray2:arm64.
Preparing to unpack .../079-libbluray2_1%3a1.3.4-1+b2_arm64.deb ...
Unpacking libbluray2:arm64 (1:1.3.4-1+b2) ...
Selecting previously unselected package libchromaprint1:arm64.
Preparing to unpack .../080-libchromaprint1_1.5.1-7_arm64.deb ...
Unpacking libchromaprint1:arm64 (1.5.1-7) ...
Selecting previously unselected package libdvdnav4:arm64.
Preparing to unpack .../081-libdvdnav4_6.1.1-3+b1_arm64.deb ...
Unpacking libdvdnav4:arm64 (6.1.1-3+b1) ...
Selecting previously unselected package libgme0:arm64.
Preparing to unpack .../082-libgme0_0.6.3-7+b2_arm64.deb ...
Unpacking libgme0:arm64 (0.6.3-7+b2) ...
Selecting previously unselected package libmpg123-0t64:arm64.
Preparing to unpack .../083-libmpg123-0t64_1.32.10-1+deb13u1_arm64.deb ...
Unpacking libmpg123-0t64:arm64 (1.32.10-1+deb13u1) ...
Selecting previously unselected package libvorbisfile3:arm64.
Preparing to unpack .../084-libvorbisfile3_1.3.7-3_arm64.deb ...
Unpacking libvorbisfile3:arm64 (1.3.7-3) ...
Selecting previously unselected package libopenmpt0t64:arm64.
Preparing to unpack .../085-libopenmpt0t64_0.7.13-1+b1_arm64.deb ...
Unpacking libopenmpt0t64:arm64 (0.7.13-1+b1) ...
Selecting previously unselected package librabbitmq4:arm64.
Preparing to unpack .../086-librabbitmq4_0.15.0-1+deb13u1_arm64.deb ...
Unpacking librabbitmq4:arm64 (0.15.0-1+deb13u1) ...
Selecting previously unselected package libcjson1:arm64.
Preparing to unpack .../087-libcjson1_1.7.18-3.1+deb13u1_arm64.deb ...
Unpacking libcjson1:arm64 (1.7.18-3.1+deb13u1) ...
Selecting previously unselected package libmbedcrypto16:arm64.
Preparing to unpack .../088-libmbedcrypto16_3.6.5-0.1~deb13u1_arm64.deb ...
Unpacking libmbedcrypto16:arm64 (3.6.5-0.1~deb13u1) ...
Selecting previously unselected package librist4:arm64.
Preparing to unpack .../089-librist4_0.2.11+dfsg-1_arm64.deb ...
Unpacking librist4:arm64 (0.2.11+dfsg-1) ...
Selecting previously unselected package libsrt1.5-gnutls:arm64.
Preparing to unpack .../090-libsrt1.5-gnutls_1.5.4-1_arm64.deb ...
Unpacking libsrt1.5-gnutls:arm64 (1.5.4-1) ...
Selecting previously unselected package libssh-4:arm64.
Preparing to unpack .../091-libssh-4_0.11.2-1+deb13u1_arm64.deb ...
Unpacking libssh-4:arm64 (0.11.2-1+deb13u1) ...
Selecting previously unselected package libnorm1t64:arm64.
Preparing to unpack .../092-libnorm1t64_1.5.9+dfsg-3.1+b2_arm64.deb ...
Unpacking libnorm1t64:arm64 (1.5.9+dfsg-3.1+b2) ...
Selecting previously unselected package libpgm-5.3-0t64:arm64.
Preparing to unpack .../093-libpgm-5.3-0t64_5.3.128~dfsg-2.1+b1_arm64.deb ...
Unpacking libpgm-5.3-0t64:arm64 (5.3.128~dfsg-2.1+b1) ...
Selecting previously unselected package libsodium23:arm64.
Preparing to unpack .../094-libsodium23_1.0.18-1+deb13u1_arm64.deb ...
Unpacking libsodium23:arm64 (1.0.18-1+deb13u1) ...
Selecting previously unselected package libzmq5:arm64.
Preparing to unpack .../095-libzmq5_4.3.5-1+b3_arm64.deb ...
Unpacking libzmq5:arm64 (4.3.5-1+b3) ...
Selecting previously unselected package libavformat61:arm64.
Preparing to unpack .../096-libavformat61_8%3a7.1.5-0+deb13u1+rpt1_arm64.deb ...
Unpacking libavformat61:arm64 (8:7.1.5-0+deb13u1+rpt1) ...
Selecting previously unselected package libbs2b0:arm64.
Preparing to unpack .../097-libbs2b0_3.1.0+dfsg-8+b1_arm64.deb ...
Unpacking libbs2b0:arm64 (3.1.0+dfsg-8+b1) ...
Selecting previously unselected package libflite1:arm64.
Preparing to unpack .../098-libflite1_2.2-7_arm64.deb ...
Unpacking libflite1:arm64 (2.2-7) ...
Selecting previously unselected package libserd-0-0:arm64.
Preparing to unpack .../099-libserd-0-0_0.32.4-1_arm64.deb ...
Unpacking libserd-0-0:arm64 (0.32.4-1) ...
Selecting previously unselected package libzix-0-0:arm64.
Preparing to unpack .../100-libzix-0-0_0.6.2-1_arm64.deb ...
Unpacking libzix-0-0:arm64 (0.6.2-1) ...
Selecting previously unselected package libsord-0-0:arm64.
Preparing to unpack .../101-libsord-0-0_0.16.18-1_arm64.deb ...
Unpacking libsord-0-0:arm64 (0.16.18-1) ...
Selecting previously unselected package libsratom-0-0:arm64.
Preparing to unpack .../102-libsratom-0-0_0.6.18-1_arm64.deb ...
Unpacking libsratom-0-0:arm64 (0.6.18-1) ...
Selecting previously unselected package liblilv-0-0:arm64.
Preparing to unpack .../103-liblilv-0-0_0.24.26-1_arm64.deb ...
Unpacking liblilv-0-0:arm64 (0.24.26-1) ...
Selecting previously unselected package libmysofa1:arm64.
Preparing to unpack .../104-libmysofa1_1.3.3+dfsg-1_arm64.deb ...
Unpacking libmysofa1:arm64 (1.3.3+dfsg-1) ...
Selecting previously unselected package libvulkan1:arm64.
Preparing to unpack .../105-libvulkan1_1.4.309.0-1_arm64.deb ...
Unpacking libvulkan1:arm64 (1.4.309.0-1) ...
Selecting previously unselected package libplacebo349:arm64.
Preparing to unpack .../106-libplacebo349_7.349.0-3_arm64.deb ...
Unpacking libplacebo349:arm64 (7.349.0-3) ...
Selecting previously unselected package libblas3:arm64.
Preparing to unpack .../107-libblas3_3.12.1-6_arm64.deb ...
Unpacking libblas3:arm64 (3.12.1-6) ...
Selecting previously unselected package libgfortran5:arm64.
Preparing to unpack .../108-libgfortran5_14.2.0-19_arm64.deb ...
Unpacking libgfortran5:arm64 (14.2.0-19) ...
Selecting previously unselected package liblapack3:arm64.
Preparing to unpack .../109-liblapack3_3.12.1-6_arm64.deb ...
Unpacking liblapack3:arm64 (3.12.1-6) ...
Selecting previously unselected package libasyncns0:arm64.
Preparing to unpack .../110-libasyncns0_0.8-6+b5_arm64.deb ...
Unpacking libasyncns0:arm64 (0.8-6+b5) ...
Selecting previously unselected package libsndfile1:arm64.
Preparing to unpack .../111-libsndfile1_1.2.2-2+deb13u1_arm64.deb ...
Unpacking libsndfile1:arm64 (1.2.2-2+deb13u1) ...
Selecting previously unselected package libpulse0:arm64.
Preparing to unpack .../112-libpulse0_17.0+dfsg1-2+rpt1_arm64.deb ...
Unpacking libpulse0:arm64 (17.0+dfsg1-2+rpt1) ...
Selecting previously unselected package libsphinxbase3t64:arm64.
Preparing to unpack .../113-libsphinxbase3t64_0.8+5prealpha+1-21+b1_arm64.deb ...
Unpacking libsphinxbase3t64:arm64 (0.8+5prealpha+1-21+b1) ...
Selecting previously unselected package libpocketsphinx3:arm64.
Preparing to unpack .../114-libpocketsphinx3_0.8+5prealpha+1-15+b4_arm64.deb ...
Unpacking libpocketsphinx3:arm64 (0.8+5prealpha+1-15+b4) ...
Selecting previously unselected package libpostproc58:arm64.
Preparing to unpack .../115-libpostproc58_8%3a7.1.5-0+deb13u1+rpt1_arm64.deb ...
Unpacking libpostproc58:arm64 (8:7.1.5-0+deb13u1+rpt1) ...
Selecting previously unselected package libfftw3-double3:arm64.
Preparing to unpack .../116-libfftw3-double3_3.3.10-2+b1_arm64.deb ...
Unpacking libfftw3-double3:arm64 (3.3.10-2+b1) ...
Selecting previously unselected package librubberband2:arm64.
Preparing to unpack .../117-librubberband2_3.3.0+dfsg-2+b3_arm64.deb ...
Unpacking librubberband2:arm64 (3.3.0+dfsg-2+b3) ...
Selecting previously unselected package libswscale8:arm64.
Preparing to unpack .../118-libswscale8_8%3a7.1.5-0+deb13u1+rpt1_arm64.deb ...
Unpacking libswscale8:arm64 (8:7.1.5-0+deb13u1+rpt1) ...
Selecting previously unselected package libvidstab1.1:arm64.
Preparing to unpack .../119-libvidstab1.1_1.1.0-2+b2_arm64.deb ...
Unpacking libvidstab1.1:arm64 (1.1.0-2+b2) ...
Selecting previously unselected package libzimg2:arm64.
Preparing to unpack .../120-libzimg2_3.0.5+ds1-1+b2_arm64.deb ...
Unpacking libzimg2:arm64 (3.0.5+ds1-1+b2) ...
Selecting previously unselected package libavfilter10:arm64.
Preparing to unpack .../121-libavfilter10_8%3a7.1.5-0+deb13u1+rpt1_arm64.deb ...
Unpacking libavfilter10:arm64 (8:7.1.5-0+deb13u1+rpt1) ...
Selecting previously unselected package libcaca0:arm64.
Preparing to unpack .../122-libcaca0_0.99.beta20-5+deb13u1_arm64.deb ...
Unpacking libcaca0:arm64 (0.99.beta20-5+deb13u1) ...
Selecting previously unselected package libcdio19t64:arm64.
Preparing to unpack .../123-libcdio19t64_2.2.0-4.1~deb13u1_arm64.deb ...
Unpacking libcdio19t64:arm64 (2.2.0-4.1~deb13u1) ...
Selecting previously unselected package libcdio-cdda2t64:arm64.
Preparing to unpack .../124-libcdio-cdda2t64_10.2+2.0.2-1+b1_arm64.deb ...
Unpacking libcdio-cdda2t64:arm64 (10.2+2.0.2-1+b1) ...
Selecting previously unselected package libcdio-paranoia2t64:arm64.
Preparing to unpack .../125-libcdio-paranoia2t64_10.2+2.0.2-1+b1_arm64.deb ...
Unpacking libcdio-paranoia2t64:arm64 (10.2+2.0.2-1+b1) ...
Selecting previously unselected package libdc1394-25:arm64.
Preparing to unpack .../126-libdc1394-25_2.2.6-5_arm64.deb ...
Unpacking libdc1394-25:arm64 (2.2.6-5) ...
Selecting previously unselected package libepoxy0:arm64.
Preparing to unpack .../127-libepoxy0_1.5.10-2_arm64.deb ...
Unpacking libepoxy0:arm64 (1.5.10-2) ...
Selecting previously unselected package libglvnd0:arm64.
Preparing to unpack .../128-libglvnd0_1.7.0-1+b2_arm64.deb ...
Unpacking libglvnd0:arm64 (1.7.0-1+b2) ...
Selecting previously unselected package libxcb-glx0:arm64.
Preparing to unpack .../129-libxcb-glx0_1.17.0-2+b1_arm64.deb ...
Unpacking libxcb-glx0:arm64 (1.17.0-2+b1) ...
Selecting previously unselected package libxcb-present0:arm64.
Preparing to unpack .../130-libxcb-present0_1.17.0-2+b1_arm64.deb ...
Unpacking libxcb-present0:arm64 (1.17.0-2+b1) ...
Selecting previously unselected package libxcb-xfixes0:arm64.
Preparing to unpack .../131-libxcb-xfixes0_1.17.0-2+b1_arm64.deb ...
Unpacking libxcb-xfixes0:arm64 (1.17.0-2+b1) ...
Selecting previously unselected package libxxf86vm1:arm64.
Preparing to unpack .../132-libxxf86vm1_1%3a1.1.4-1+b4_arm64.deb ...
Unpacking libxxf86vm1:arm64 (1:1.1.4-1+b4) ...
Selecting previously unselected package libdrm-amdgpu1:arm64.
Preparing to unpack .../133-libdrm-amdgpu1_2.4.131-1~bpo13+1+rpt2_arm64.deb ...
Unpacking libdrm-amdgpu1:arm64 (2.4.131-1~bpo13+1+rpt2) ...
Selecting previously unselected package libz3-4:arm64.
Preparing to unpack .../134-libz3-4_4.13.3-1_arm64.deb ...
Unpacking libz3-4:arm64 (4.13.3-1) ...
Selecting previously unselected package libllvm19:arm64.
Preparing to unpack .../135-libllvm19_1%3a19.1.7-3+b1_arm64.deb ...
Unpacking libllvm19:arm64 (1:19.1.7-3+b1) ...
Selecting previously unselected package libxcb-randr0:arm64.
Preparing to unpack .../136-libxcb-randr0_1.17.0-2+b1_arm64.deb ...
Unpacking libxcb-randr0:arm64 (1.17.0-2+b1) ...
Selecting previously unselected package libxcb-sync1:arm64.
Preparing to unpack .../137-libxcb-sync1_1.17.0-2+b1_arm64.deb ...
Unpacking libxcb-sync1:arm64 (1.17.0-2+b1) ...
Selecting previously unselected package libxshmfence1:arm64.
Preparing to unpack .../138-libxshmfence1_1.3.3-1_arm64.deb ...
Unpacking libxshmfence1:arm64 (1.3.3-1) ...
Selecting previously unselected package mesa-libgallium:arm64.
Preparing to unpack .../139-mesa-libgallium_25.0.7-2+rpt4_arm64.deb ...
Unpacking mesa-libgallium:arm64 (25.0.7-2+rpt4) ...
Selecting previously unselected package libwayland-server0:arm64.
Preparing to unpack .../140-libwayland-server0_1.24.0-2~bpo13+1~rpt1_arm64.deb ...
Unpacking libwayland-server0:arm64 (1.24.0-2~bpo13+1~rpt1) ...
Selecting previously unselected package libgbm1:arm64.
Preparing to unpack .../141-libgbm1_25.0.7-2+rpt4_arm64.deb ...
Unpacking libgbm1:arm64 (25.0.7-2+rpt4) ...
Selecting previously unselected package libgl1-mesa-dri:arm64.
Preparing to unpack .../142-libgl1-mesa-dri_25.0.7-2+rpt4_arm64.deb ...
Unpacking libgl1-mesa-dri:arm64 (25.0.7-2+rpt4) ...
Selecting previously unselected package libglx-mesa0:arm64.
Preparing to unpack .../143-libglx-mesa0_25.0.7-2+rpt4_arm64.deb ...
Unpacking libglx-mesa0:arm64 (25.0.7-2+rpt4) ...
Selecting previously unselected package libglx0:arm64.
Preparing to unpack .../144-libglx0_1.7.0-1+b2_arm64.deb ...
Unpacking libglx0:arm64 (1.7.0-1+b2) ...
Selecting previously unselected package libgl1:arm64.
Preparing to unpack .../145-libgl1_1.7.0-1+b2_arm64.deb ...
Unpacking libgl1:arm64 (1.7.0-1+b2) ...
Selecting previously unselected package libiec61883-0:arm64.
Preparing to unpack .../146-libiec61883-0_1.2.0-7_arm64.deb ...
Unpacking libiec61883-0:arm64 (1.2.0-7) ...
Selecting previously unselected package libjack-jackd2-0:arm64.
Preparing to unpack .../147-libjack-jackd2-0_1.9.22~dfsg-4_arm64.deb ...
Unpacking libjack-jackd2-0:arm64 (1.9.22~dfsg-4) ...
Selecting previously unselected package libopenal-data.
Preparing to unpack .../148-libopenal-data_1%3a1.24.2-1_all.deb ...
Unpacking libopenal-data (1:1.24.2-1) ...
Selecting previously unselected package libopenal1:arm64.
Preparing to unpack .../149-libopenal1_1%3a1.24.2-1_arm64.deb ...
Unpacking libopenal1:arm64 (1:1.24.2-1) ...
Selecting previously unselected package libwayland-client0:arm64.
Preparing to unpack .../150-libwayland-client0_1.24.0-2~bpo13+1~rpt1_arm64.deb ...
Unpacking libwayland-client0:arm64 (1.24.0-2~bpo13+1~rpt1) ...
Selecting previously unselected package libdecor-0-0:arm64.
Preparing to unpack .../151-libdecor-0-0_0.2.2-2_arm64.deb ...
Unpacking libdecor-0-0:arm64 (0.2.2-2) ...
Selecting previously unselected package libwayland-cursor0:arm64.
Preparing to unpack .../152-libwayland-cursor0_1.24.0-2~bpo13+1~rpt1_arm64.deb ...
Unpacking libwayland-cursor0:arm64 (1.24.0-2~bpo13+1~rpt1) ...
Selecting previously unselected package libwayland-egl1:arm64.
Preparing to unpack .../153-libwayland-egl1_1.24.0-2~bpo13+1~rpt1_arm64.deb ...
Unpacking libwayland-egl1:arm64 (1.24.0-2~bpo13+1~rpt1) ...
Selecting previously unselected package libxcursor1:arm64.
Preparing to unpack .../154-libxcursor1_1%3a1.2.3-1_arm64.deb ...
Unpacking libxcursor1:arm64 (1:1.2.3-1) ...
Selecting previously unselected package libxkbcommon0:arm64.
Preparing to unpack .../155-libxkbcommon0_1.7.0-2_arm64.deb ...
Unpacking libxkbcommon0:arm64 (1.7.0-2) ...
Selecting previously unselected package libxrandr2:arm64.
Preparing to unpack .../156-libxrandr2_2%3a1.5.4-1+b3_arm64.deb ...
Unpacking libxrandr2:arm64 (2:1.5.4-1+b3) ...
Selecting previously unselected package libxss1:arm64.
Preparing to unpack .../157-libxss1_1%3a1.2.3-1+b3_arm64.deb ...
Unpacking libxss1:arm64 (1:1.2.3-1+b3) ...
Selecting previously unselected package libsdl2-2.0-0:arm64.
Preparing to unpack .../158-libsdl2-2.0-0_2.32.4+dfsg-1_arm64.deb ...
Unpacking libsdl2-2.0-0:arm64 (2.32.4+dfsg-1) ...
Selecting previously unselected package libxcb-shape0:arm64.
Preparing to unpack .../159-libxcb-shape0_1.17.0-2+b1_arm64.deb ...
Unpacking libxcb-shape0:arm64 (1.17.0-2+b1) ...
Selecting previously unselected package libxv1:arm64.
Preparing to unpack .../160-libxv1_2%3a1.0.11-1.1+b3_arm64.deb ...
Unpacking libxv1:arm64 (2:1.0.11-1.1+b3) ...
Selecting previously unselected package libavdevice61:arm64.
Preparing to unpack .../161-libavdevice61_8%3a7.1.5-0+deb13u1+rpt1_arm64.deb ...
Unpacking libavdevice61:arm64 (8:7.1.5-0+deb13u1+rpt1) ...
Selecting previously unselected package ffmpeg.
Preparing to unpack .../162-ffmpeg_8%3a7.1.5-0+deb13u1+rpt1_arm64.deb ...
Unpacking ffmpeg (8:7.1.5-0+deb13u1+rpt1) ...
Selecting previously unselected package libaacs0:arm64.
Preparing to unpack .../163-libaacs0_0.11.1-4+b1_arm64.deb ...
Unpacking libaacs0:arm64 (0.11.1-4+b1) ...
Selecting previously unselected package libatk1.0-0t64:arm64.
Preparing to unpack .../164-libatk1.0-0t64_2.56.2-1+deb13u1_arm64.deb ...
Unpacking libatk1.0-0t64:arm64 (2.56.2-1+deb13u1) ...
Selecting previously unselected package libatk-bridge2.0-0t64:arm64.
Preparing to unpack .../165-libatk-bridge2.0-0t64_2.56.2-1+deb13u1_arm64.deb ...
Unpacking libatk-bridge2.0-0t64:arm64 (2.56.2-1+deb13u1) ...
Selecting previously unselected package libavahi-client3:arm64.
Preparing to unpack .../166-libavahi-client3_0.8-16_arm64.deb ...
Unpacking libavahi-client3:arm64 (0.8-16) ...
Selecting previously unselected package libbdplus0:arm64.
Preparing to unpack .../167-libbdplus0_0.2.0-4+b1_arm64.deb ...
Unpacking libbdplus0:arm64 (0.2.0-4+b1) ...
Selecting previously unselected package libcloudproviders0:arm64.
Preparing to unpack .../168-libcloudproviders0_0.3.6-2_arm64.deb ...
Unpacking libcloudproviders0:arm64 (0.3.6-2) ...
Selecting previously unselected package libcolord2:arm64.
Preparing to unpack .../169-libcolord2_1.4.7-3_arm64.deb ...
Unpacking libcolord2:arm64 (1.4.7-3) ...
Selecting previously unselected package libcups2t64:arm64.
Preparing to unpack .../170-libcups2t64_2.4.10-3+rpt2+deb13u2_arm64.deb ...
Unpacking libcups2t64:arm64 (2.4.10-3+rpt2+deb13u2) ...
Selecting previously unselected package libxcomposite1:arm64.
Preparing to unpack .../171-libxcomposite1_1%3a0.4.6-1_arm64.deb ...
Unpacking libxcomposite1:arm64 (1:0.4.6-1) ...
Selecting previously unselected package libxdamage1:arm64.
Preparing to unpack .../172-libxdamage1_1%3a1.1.6-1+b2_arm64.deb ...
Unpacking libxdamage1:arm64 (1:1.1.6-1+b2) ...
Selecting previously unselected package libxinerama1:arm64.
Preparing to unpack .../173-libxinerama1_2%3a1.1.4-3+b4_arm64.deb ...
Unpacking libxinerama1:arm64 (2:1.1.4-3+b4) ...
Selecting previously unselected package libgtk-3-common.
Preparing to unpack .../174-libgtk-3-common_1%3a3.24.49-3+rpt8_all.deb ...
Unpacking libgtk-3-common (1:3.24.49-3+rpt8) ...
Selecting previously unselected package libgtk-3-0t64:arm64.
Preparing to unpack .../175-libgtk-3-0t64_1%3a3.24.49-3+rpt8_arm64.deb ...
Unpacking libgtk-3-0t64:arm64 (1:3.24.49-3+rpt8) ...
Selecting previously unselected package libdecor-0-plugin-1-gtk:arm64.
Preparing to unpack .../176-libdecor-0-plugin-1-gtk_0.2.2-2_arm64.deb ...
Unpacking libdecor-0-plugin-1-gtk:arm64 (0.2.2-2) ...
Selecting previously unselected package libgdk-pixbuf2.0-bin.
Preparing to unpack .../177-libgdk-pixbuf2.0-bin_2.42.12+dfsg-4+deb13u1_arm64.deb ...
Unpacking libgdk-pixbuf2.0-bin (2.42.12+dfsg-4+deb13u1) ...
Selecting previously unselected package libgtk-3-bin.
Preparing to unpack .../178-libgtk-3-bin_1%3a3.24.49-3+rpt8_arm64.deb ...
Unpacking libgtk-3-bin (1:3.24.49-3+rpt8) ...
Selecting previously unselected package librsvg2-common:arm64.
Preparing to unpack .../179-librsvg2-common_2.60.0+dfsg-1_arm64.deb ...
Unpacking librsvg2-common:arm64 (2.60.0+dfsg-1) ...
Selecting previously unselected package libvdpau-va-gl1:arm64.
Preparing to unpack .../180-libvdpau-va-gl1_0.4.2-2_arm64.deb ...
Unpacking libvdpau-va-gl1:arm64 (0.4.2-2) ...
Selecting previously unselected package mesa-va-drivers:arm64.
Preparing to unpack .../181-mesa-va-drivers_25.0.7-2+rpt4_arm64.deb ...
Unpacking mesa-va-drivers:arm64 (25.0.7-2+rpt4) ...
Selecting previously unselected package mesa-vdpau-drivers:arm64.
Preparing to unpack .../182-mesa-vdpau-drivers_25.0.7-2+rpt4_arm64.deb ...
Unpacking mesa-vdpau-drivers:arm64 (25.0.7-2+rpt4) ...
Selecting previously unselected package mesa-vulkan-drivers:arm64.
Preparing to unpack .../183-mesa-vulkan-drivers_25.0.7-2+rpt4_arm64.deb ...
Unpacking mesa-vulkan-drivers:arm64 (25.0.7-2+rpt4) ...
Selecting previously unselected package pocketsphinx-en-us.
Preparing to unpack .../184-pocketsphinx-en-us_0.8+5prealpha+1-15_all.deb ...
Unpacking pocketsphinx-en-us (0.8+5prealpha+1-15) ...
Selecting previously unselected package va-driver-all:arm64.
Preparing to unpack .../185-va-driver-all_2.22.0-3_arm64.deb ...
Unpacking va-driver-all:arm64 (2.22.0-3) ...
Selecting previously unselected package vdpau-driver-all:arm64.
Preparing to unpack .../186-vdpau-driver-all_1.5-3+b1_arm64.deb ...
Unpacking vdpau-driver-all:arm64 (1.5-3+b1) ...
Setting up libgme0:arm64 (0.6.3-7+b2) ...
Setting up libchromaprint1:arm64 (1.5.1-7) ...
Setting up libhwy1t64:arm64 (1.2.0-2+b2) ...
Setting up libgraphite2-3:arm64 (1.3.14-2+deb13u1) ...
Setting up libxcb-dri3-0:arm64 (1.17.0-2+b1) ...
Setting up liblcms2-2:arm64 (2.16-2+deb13u2) ...
Setting up libpixman-1-0:arm64 (0.46.4-1+rpt1) ...
Setting up libudfread0:arm64 (1.1.2-1+b2) ...
Setting up libnorm1t64:arm64 (1.5.9+dfsg-3.1+b2) ...
Setting up libwayland-server0:arm64 (1.24.0-2~bpo13+1~rpt1) ...
Setting up libaom3:arm64 (3.12.1-1) ...
Setting up libx11-xcb1:arm64 (2:1.8.12-1) ...
Setting up librabbitmq4:arm64 (0.15.0-1+deb13u1) ...
Setting up libraw1394-11:arm64 (2.1.2-2+b2) ...
Setting up libsodium23:arm64 (1.0.18-1+deb13u1) ...
Setting up libxdamage1:arm64 (1:1.1.6-1+b2) ...
Setting up libxcb-xfixes0:arm64 (1.17.0-2+b1) ...
Setting up libspeex1:arm64 (1.2.1-3) ...
Setting up libshine3:arm64 (3.1.1-2+b2) ...
Setting up libcaca0:arm64 (0.99.beta20-5+deb13u1) ...
Setting up hicolor-icon-theme (0.18-2) ...
Setting up libxi6:arm64 (2:1.8.2-1) ...
Setting up libx264-164:arm64 (2:0.164.3108+git31e19f9-2+b1) ...
Setting up libtwolame0:arm64 (0.4.0-2+b2) ...
Setting up libxrender1:arm64 (1:0.9.12-1) ...
Setting up libdatrie1:arm64 (0.2.13-3+b1) ...
Setting up libgsm1:arm64 (1.0.22-1+b2) ...
Setting up libxcb-render0:arm64 (1.17.0-2+b1) ...
Setting up libsoxr0:arm64 (0.1.3-4+b2) ...
Setting up libzix-0-0:arm64 (0.6.2-1) ...
Setting up libglvnd0:arm64 (1.7.0-1+b2) ...
Setting up libcodec2-1.2:arm64 (1.2.0-3) ...
Setting up libxcb-glx0:arm64 (1.17.0-2+b1) ...
Setting up libgdk-pixbuf2.0-common (2.42.12+dfsg-4+deb13u1) ...
Setting up libmysofa1:arm64 (1.3.3+dfsg-1) ...
Setting up libxcb-shape0:arm64 (1.17.0-2+b1) ...
Setting up x11-common (1:7.7+24+deb13u1) ...
debconf: unable to initialize frontend: Dialog
debconf: (Dialog frontend will not work on a dumb terminal, an emacs shell buffer, or without a controlling terminal.)
debconf: falling back to frontend: Readline
debconf: unable to initialize frontend: Readline
debconf: (This frontend requires a controlling tty.)
debconf: falling back to frontend: Teletype
debconf: unable to initialize frontend: Teletype
debconf: (This frontend requires a controlling tty.)
debconf: falling back to frontend: Noninteractive
Setting up libcdio19t64:arm64 (2.2.0-4.1~deb13u1) ...
Setting up libcloudproviders0:arm64 (0.3.6-2) ...
Setting up dconf-service (0.40.0-5) ...
Setting up libxcb-shm0:arm64 (1.17.0-2+b1) ...
Setting up libmpg123-0t64:arm64 (1.32.10-1+deb13u1) ...
Setting up libcjson1:arm64 (1.7.18-3.1+deb13u1) ...
Setting up libxvidcore4:arm64 (2:1.3.7-1+b2) ...
Setting up libcolord2:arm64 (1.4.7-3) ...
Setting up libxxf86vm1:arm64 (1:1.1.4-1+b4) ...
Setting up libsnappy1v5:arm64 (1.2.2-1) ...
Setting up libcdio-cdda2t64:arm64 (10.2+2.0.2-1+b1) ...
Setting up libxcb-present0:arm64 (1.17.0-2+b1) ...
Setting up libvorbisfile3:arm64 (1.3.7-3) ...
Setting up libpgm-5.3-0t64:arm64 (5.3.128~dfsg-2.1+b1) ...
Setting up libtheoraenc1:arm64 (1.2.0~alpha1+dfsg-6) ...
Setting up libz3-4:arm64 (4.13.3-1) ...
Setting up libblas3:arm64 (3.12.1-6) ...
update-alternatives: using /usr/lib/aarch64-linux-gnu/blas/libblas.so.3 to provide /usr/lib/aarch64-linux-gnu/libblas.so.3 (libblas.so.3-aarch64-linux-gnu) in auto mode
Setting up libva2:arm64 (2.22.0-3) ...
Setting up libfreetype6:arm64 (2.13.3+dfsg-1+deb13u1) ...
Setting up libsvtav1enc2:arm64 (2.3.0+dfsg-1) ...
Setting up libepoxy0:arm64 (1.5.10-2) ...
Setting up libxfixes3:arm64 (1:6.0.0-2+b4) ...
Setting up libxcb-sync1:arm64 (1.17.0-2+b1) ...
Setting up libatspi2.0-0t64:arm64 (2.56.2-1+deb13u1) ...
Setting up libfribidi0:arm64 (1.0.16-1) ...
Setting up libopus0:arm64 (1.5.2-2) ...
Setting up libxinerama1:arm64 (2:1.1.4-3+b4) ...
Setting up libcdio-paranoia2t64:arm64 (10.2+2.0.2-1+b1) ...
Setting up libdc1394-25:arm64 (2.2.6-5) ...
Setting up libxv1:arm64 (2:1.0.11-1.1+b3) ...
Setting up fonts-dejavu-mono (2.37-8) ...
Setting up libxrandr2:arm64 (2:1.5.4-1+b3) ...
Setting up fonts-dejavu-core (2.37-8) ...
Setting up libaacs0:arm64 (0.11.1-4+b1) ...
Setting up pocketsphinx-en-us (0.8+5prealpha+1-15) ...
Setting up libfftw3-double3:arm64 (3.3.10-2+b1) ...
Setting up libssh-4:arm64 (0.11.2-1+deb13u1) ...
Setting up libgfortran5:arm64 (14.2.0-19) ...
Setting up libvulkan1:arm64 (1.4.309.0-1) ...
Setting up librubberband2:arm64 (3.3.0+dfsg-2+b3) ...
Setting up libbdplus0:arm64 (0.2.0-4+b1) ...
Setting up libjack-jackd2-0:arm64 (1.9.22~dfsg-4) ...
Setting up libvidstab1.1:arm64 (1.1.0-2+b2) ...
Setting up libvpx9:arm64 (1.15.0-2.1+deb13u1) ...
Setting up libsrt1.5-gnutls:arm64 (1.5.4-1) ...
Setting up libflite1:arm64 (2.2-7) ...
Setting up libdav1d7:arm64 (1.5.1-1) ...
Setting up libva-drm2:arm64 (2.22.0-3) ...
Setting up ocl-icd-libopencl1:arm64 (2.3.3-1) ...
Setting up libasyncns0:arm64 (0.8-6+b5) ...
Setting up libxshmfence1:arm64 (1.3.3-1) ...
Setting up at-spi2-common (2.56.2-1+deb13u1) ...
Setting up libvdpau1:arm64 (1.5-3+b1) ...
Setting up libbs2b0:arm64 (3.1.0+dfsg-8+b1) ...
Setting up libxcb-randr0:arm64 (1.17.0-2+b1) ...
Setting up librav1e0.7:arm64 (0.7.1-9+b2) ...
Setting up libzimg2:arm64 (3.0.5+ds1-1+b2) ...
Setting up libopenjp2-7:arm64 (2.5.3-2.1~deb13u2) ...
Setting up libharfbuzz0b:arm64 (10.2.0-1+deb13u1) ...
Setting up libopenal-data (1:1.24.2-1) ...
Setting up libthai-data (0.1.29-2) ...
Setting up libgdk-pixbuf-2.0-0:arm64 (2.42.12+dfsg-4+deb13u1) ...
Setting up libunibreak6:arm64 (6.1-3) ...
Setting up libwayland-egl1:arm64 (1.24.0-2~bpo13+1~rpt1) ...
Setting up libxss1:arm64 (1:1.2.3-1+b3) ...
Setting up libmbedcrypto16:arm64 (3.6.5-0.1~deb13u1) ...
Setting up libx265-215:arm64 (4.1-2) ...
Setting up libva-x11-2:arm64 (2.22.0-3) ...
Setting up libwebpmux3:arm64 (1.5.0-0.1) ...
Setting up libxcomposite1:arm64 (1:0.4.6-1) ...
Setting up libjxl0.11:arm64 (0.11.2-0.1~deb13u2) ...
Setting up libopenmpt0t64:arm64 (0.7.13-1+b1) ...
Setting up libavahi-client3:arm64 (0.8-16) ...
Setting up libzvbi-common (0.2.44-1) ...
Setting up libmp3lame0:arm64 (3.100-6+b3) ...
Setting up libvorbisenc2:arm64 (1.3.7-3) ...
Setting up libdvdnav4:arm64 (6.1.1-3+b1) ...
Setting up libiec61883-0:arm64 (1.2.0-7) ...
Setting up libserd-0-0:arm64 (0.32.4-1) ...
Setting up libdrm-amdgpu1:arm64 (2.4.131-1~bpo13+1+rpt2) ...
Setting up libxkbcommon0:arm64 (1.7.0-2) ...
Setting up libwayland-client0:arm64 (1.24.0-2~bpo13+1~rpt1) ...
Setting up libavc1394-0:arm64 (0.5.4-5+b2) ...
Setting up mesa-vdpau-drivers:arm64 (25.0.7-2+rpt4) ...
Setting up libllvm19:arm64 (1:19.1.7-3+b1) ...
Setting up gtk-update-icon-cache (4.18.6+ds-2) ...
Setting up mesa-libgallium:arm64 (25.0.7-2+rpt4) ...
Setting up liblapack3:arm64 (3.12.1-6) ...
update-alternatives: using /usr/lib/aarch64-linux-gnu/lapack/liblapack.so.3 to provide /usr/lib/aarch64-linux-gnu/liblapack.so.3 (liblapack.so.3-aarch64-linux-gnu) in auto mode
Setting up libatk1.0-0t64:arm64 (2.56.2-1+deb13u1) ...
Setting up libzmq5:arm64 (4.3.5-1+b3) ...
Setting up libzvbi0t64:arm64 (0.2.44-1) ...
Setting up dconf-gsettings-backend:arm64 (0.40.0-5) ...
Setting up libgbm1:arm64 (25.0.7-2+rpt4) ...
Setting up fontconfig-config (2.15.0-2.3) ...
debconf: unable to initialize frontend: Dialog
debconf: (Dialog frontend will not work on a dumb terminal, an emacs shell buffer, or without a controlling terminal.)
debconf: falling back to frontend: Readline
debconf: unable to initialize frontend: Readline
debconf: (This frontend requires a controlling tty.)
debconf: falling back to frontend: Teletype
debconf: unable to initialize frontend: Teletype
debconf: (This frontend requires a controlling tty.)
debconf: falling back to frontend: Noninteractive
Setting up libxtst6:arm64 (2:1.2.5-1) ...
Setting up libxcursor1:arm64 (1:1.2.3-1) ...
Setting up libgl1-mesa-dri:arm64 (25.0.7-2+rpt4) ...
Setting up libopenal1:arm64 (1:1.24.2-1) ...
Setting up libavutil59:arm64 (8:7.1.5-0+deb13u1+rpt1) ...
Setting up libpostproc58:arm64 (8:7.1.5-0+deb13u1+rpt1) ...
Setting up librist4:arm64 (0.2.11+dfsg-1) ...
Setting up libthai0:arm64 (0.1.29-2+b1) ...
Setting up libswresample5:arm64 (8:7.1.5-0+deb13u1+rpt1) ...
Setting up libswscale8:arm64 (8:7.1.5-0+deb13u1+rpt1) ...
Setting up adwaita-icon-theme (48.1-1) ...
update-alternatives: using /usr/share/icons/Adwaita/cursor.theme to provide /usr/share/icons/default/index.theme (x-cursor-theme) in auto mode
Setting up libplacebo349:arm64 (7.349.0-3) ...
Setting up libgdk-pixbuf2.0-bin (2.42.12+dfsg-4+deb13u1) ...
Setting up libsord-0-0:arm64 (0.16.18-1) ...
Setting up libwayland-cursor0:arm64 (1.24.0-2~bpo13+1~rpt1) ...
Setting up libsratom-0-0:arm64 (0.6.18-1) ...
Setting up libdecor-0-0:arm64 (0.2.2-2) ...
Setting up libsndfile1:arm64 (1.2.2-2+deb13u1) ...
Setting up mesa-va-drivers:arm64 (25.0.7-2+rpt4) ...
Setting up liblilv-0-0:arm64 (0.24.26-1) ...
Setting up libcups2t64:arm64 (2.4.10-3+rpt2+deb13u2) ...
Setting up libgtk-3-common (1:3.24.49-3+rpt8) ...
Setting up gsettings-desktop-schemas (48.0-1+rpt1) ...
Setting up libatk-bridge2.0-0t64:arm64 (2.56.2-1+deb13u1) ...
Setting up mesa-vulkan-drivers:arm64 (25.0.7-2+rpt4) ...
Setting up libglx-mesa0:arm64 (25.0.7-2+rpt4) ...
Setting up libglx0:arm64 (1.7.0-1+b2) ...
Setting up libpulse0:arm64 (17.0+dfsg1-2+rpt1) ...
Setting up libsphinxbase3t64:arm64 (0.8+5prealpha+1-21+b1) ...
Setting up libgl1:arm64 (1.7.0-1+b2) ...
Setting up va-driver-all:arm64 (2.22.0-3) ...
Setting up libsdl2-2.0-0:arm64 (2.32.4+dfsg-1) ...
Setting up libvdpau-va-gl1:arm64 (0.4.2-2) ...
Setting up libpocketsphinx3:arm64 (0.8+5prealpha+1-15+b4) ...
Setting up vdpau-driver-all:arm64 (1.5-3+b1) ...
Processing triggers for libc-bin (2.41-12+rpt1+deb13u3) ...
Processing triggers for man-db (2.13.1-1) ...
Processing triggers for libglib2.0-0t64:arm64 (2.84.4-3~deb13u3) ...
Setting up at-spi2-core (2.56.2-1+deb13u1) ...
Processing triggers for sgml-base (1.31+nmu1) ...
Setting up libfontconfig1:arm64 (2.15.0-2.3) ...
Setting up libbluray2:arm64 (1:1.3.4-1+b2) ...
Setting up fontconfig (2.15.0-2.3) ...
Regenerating fonts cache... done.
Setting up libpango-1.0-0:arm64 (1.56.3-1) ...
Setting up libcairo2:arm64 (1.18.4-1+rpt1) ...
Setting up libass9:arm64 (1:0.17.3-1+deb13u1) ...
Setting up libtheoradec1:arm64 (1.2.0~alpha1+dfsg-6) ...
Setting up libcairo-gobject2:arm64 (1.18.4-1+rpt1) ...
Setting up libpangoft2-1.0-0:arm64 (1.56.3-1) ...
Setting up libpangocairo-1.0-0:arm64 (1.56.3-1) ...
Setting up librsvg2-2:arm64 (2.60.0+dfsg-1) ...
Setting up libgtk-3-0t64:arm64 (1:3.24.49-3+rpt8) ...
Setting up libavcodec61:arm64 (8:7.1.5-0+deb13u1+rpt1) ...
Setting up librsvg2-common:arm64 (2.60.0+dfsg-1) ...
Setting up libdecor-0-plugin-1-gtk:arm64 (0.2.2-2) ...
Setting up libgtk-3-bin (1:3.24.49-3+rpt8) ...
Setting up libavformat61:arm64 (8:7.1.5-0+deb13u1+rpt1) ...
Setting up libavfilter10:arm64 (8:7.1.5-0+deb13u1+rpt1) ...
Setting up libavdevice61:arm64 (8:7.1.5-0+deb13u1+rpt1) ...
Setting up ffmpeg (8:7.1.5-0+deb13u1+rpt1) ...
Processing triggers for libc-bin (2.41-12+rpt1+deb13u3) ...
Processing triggers for libgdk-pixbuf-2.0-0:arm64 (2.42.12+dfsg-4+deb13u1) ...
#+end_example

** ILI94486 driver

[[https://github.com/ustropo/Python_ILI9486]]

#+BEGIN_SRC bash :eval no-export :results output
cd tmp
echo "Running in host '$(hostname)' on $(date)"
git clone https://github.com/ustropo/Python_ILI9486
#+END_SRC

#+RESULTS:
: Running in host 'jrr5x' on Thu Jul 16 18:58:29 EEST 2026

[[file:tmp/Python_ILI9486]]

#+BEGIN_SRC bash :eval no-export :results output
echo "Running in $(pwd) for user '$(whoami)' on host '$(hostname)' on $(date)"
ls tmp

#+END_SRC

#+RESULTS:
: Running in /home/pi for user 'pi' on host 'jrr5x' on Thu Jul 16 18:58:39 EEST 2026
: Python_ILI9486

** Install RPI display driver from ~LCD-show~

Instructions from http://www.lcdwiki.com/3.5inch_RPi_Display#Driver_Installation

*** Git clone LCD-show

#+BEGIN_SRC bash :eval no-export :results output 
cd tmp
echo "Running in $(pwd) host '$(hostname)' on $(date)"
git clone https://github.com/goodtft/LCD-show.git
#+END_SRC

#+RESULTS:
: Running in /home/pi/tmp host 'jrr5x' on Thu Jul 16 18:58:47 EEST 2026

#+BEGIN_SRC bash :eval no-export :results output
  echo "Running in $(pwd) host '$(hostname)' on $(date)"
  ls tmp
#+END_SRC

#+RESULTS:
: Running in /home/pi host 'jrr5x' on Thu Jul 16 18:58:57 EEST 2026
: LCD-show  Python_ILI9486

*** Show content of ~LCD-show~

Executable bit on ~LCD-show~
#+BEGIN_SRC bash :eval no-export :results output
echo "Running in $(pwd) host '$(hostname)' on $(date)"
cd tmp
chmod -R 755 LCD-show
#+END_SRC

#+RESULTS:
: Running in /home/pi host 'jrr5x' on Thu Jul 16 18:59:03 EEST 2026

#+BEGIN_SRC bash :eval no-export :results output
cd tmp/LCD-show
echo "Running in $(pwd) host '$(hostname)' on $(date)"
ls -ltr
#+END_SRC

#+RESULTS:
#+begin_example
Running in /home/pi/tmp/LCD-show host 'jrr5x' on Thu Jul 16 18:59:06 EEST 2026
total 696
-rwxr-xr-x 1 pi pi    855 Jul 16 18:58 LCD-hdmi
-rwxr-xr-x 1 pi pi   1222 Jul 16 18:58 DPI7_1024_600-show
-rwxr-xr-x 1 pi pi   1222 Jul 16 18:58 DPI5_7_800_480-show
-rwxr-xr-x 1 pi pi   1838 Jul 16 18:58 LCD7S-show
-rwxr-xr-x 1 pi pi   1838 Jul 16 18:58 LCD7H-show
-rwxr-xr-x 1 pi pi   1777 Jul 16 18:58 LCD7C-show
-rwxr-xr-x 1 pi pi   1773 Jul 16 18:58 LCD7B-show
-rwxr-xr-x 1 pi pi   1849 Jul 16 18:58 LCD55-show
-rwxr-xr-x 1 pi pi   4157 Jul 16 18:58 LCD5-show
-rwxr-xr-x 1 pi pi   4766 Jul 16 18:58 LCD35-show
-rwxr-xr-x 1 pi pi   4772 Jul 16 18:58 LCD32-show
-rwxr-xr-x 1 pi pi   4772 Jul 16 18:58 LCD28-show
-rwxr-xr-x 1 pi pi   4771 Jul 16 18:58 LCD24-show
-rwxr-xr-x 1 pi pi   4768 Jul 16 18:58 LCD24-3A+-show
-rwxr-xr-x 1 pi pi   5152 Jul 16 18:58 LCD154-show
-rwxr-xr-x 1 pi pi   1779 Jul 16 18:58 LCD101Y-show
-rwxr-xr-x 1 pi pi   1884 Jul 16 18:58 LCD101TMP-show
-rwxr-xr-x 1 pi pi   1794 Jul 16 18:58 LCD101S-show
-rwxr-xr-x 1 pi pi   1878 Jul 16 18:58 LCD101H-show
-rwxr-xr-x 1 pi pi   1877 Jul 16 18:58 MPI5001-show
-rwxr-xr-x 1 pi pi   3449 Jul 16 18:58 MPI4009-show
-rwxr-xr-x 1 pi pi   4257 Jul 16 18:58 MPI4008-show
-rwxr-xr-x 1 pi pi   1064 Jul 16 18:58 MPI3510-show
-rwxr-xr-x 1 pi pi   1022 Jul 16 18:58 MPI3508_480_320-show
-rwxr-xr-x 1 pi pi   4066 Jul 16 18:58 MPI3508-show
-rwxr-xr-x 1 pi pi   4771 Jul 16 18:58 MIS35-show
-rwxr-xr-x 1 pi pi   5086 Jul 16 18:58 MHS40C-show
-rwxr-xr-x 1 pi pi   4776 Jul 16 18:58 MHS40-show
-rwxr-xr-x 1 pi pi   4764 Jul 16 18:58 MHS35IPS-show
-rwxr-xr-x 1 pi pi   4937 Jul 16 18:58 MHS35B-show
-rwxr-xr-x 1 pi pi   4746 Jul 16 18:58 MHS35-show
-rwxr-xr-x 1 pi pi   4773 Jul 16 18:58 MHS32-show
-rwxr-xr-x 1 pi pi   1409 Jul 16 18:58 MHS24-show
-rwxr-xr-x 1 pi pi   6520 Jul 16 18:58 README.md
-rwxr-xr-x 1 pi pi   4019 Jul 16 18:58 PyMouse-1.0.tar.gz
-rwxr-xr-x 1 pi pi   4601 Jul 16 18:58 NANO24-show
-rwxr-xr-x 1 pi pi   1751 Jul 16 18:58 Mouse_Key.py
-rwxr-xr-x 1 pi pi    750 Jul 16 18:58 MPI5094-show
drwxr-xr-x 2 pi pi   4096 Jul 16 18:58 boot
-rwxr-xr-x 1 pi pi   3215 Jul 16 18:58 system_restore.sh
-rwxr-xr-x 1 pi pi   1292 Jul 16 18:58 system_config.sh
-rwxr-xr-x 1 pi pi   3440 Jul 16 18:58 system_backup.sh
-rwxr-xr-x 1 pi pi   6482 Jul 16 18:58 rotate.sh
-rwxr-xr-x 1 pi pi 119448 Jul 16 18:58 python-xlib_0.23-2_all.deb
drwxr-xr-x 3 pi pi   4096 Jul 16 18:58 etc
-rwxr-xr-x 1 pi pi  41542 Jul 16 18:58 xinput-calibrator_0.7.5-1_armhf.deb
-rwxr-xr-x 1 pi pi  43920 Jul 16 18:58 xinput-calibrator_0.7.5+git20140201-1+b2_arm64.deb
drwxr-xr-x 4 pi pi   4096 Jul 16 18:58 usr
-rwxr-xr-x 1 pi pi 117184 Jul 16 18:58 xserver-xorg-input-evdev_1%3a2.10.6-1+b1_armhf.deb
-rwxr-xr-x 1 pi pi 119392 Jul 16 18:58 xserver-xorg-input-evdev_1%3a2.10.6-2_arm64.deb
#+end_example

*** +TFT 3.5 inch display driver installation+
:PROPERTIES:
:header-args+: :dir  /ssh:jrr5:tmp/LCD-show
:END:

Ref: https://www.lcdwiki.com/3.5inch_RPi_Display#Driver_Installation

#+BEGIN_SRC bash :eval no-export :results output
echo "Running in $(pwd) host '$(hostname)' on $(date)"
ls
#+END_SRC

#+RESULTS:
#+begin_example
Running in /home/pi/tmp/LCD-show host 'jrr5' on Tue May 19 09:51:55 EEST 2026
DPI5_7_800_480-show  MHS40C-show
DPI7_1024_600-show   MIS35-show
LCD-hdmi	     MPI3508-show
LCD101H-show	     MPI3508_480_320-show
LCD101S-show	     MPI3510-show
LCD101TMP-show	     MPI4008-show
LCD101Y-show	     MPI4009-show
LCD154-show	     MPI5001-show
LCD24-3A+-show	     MPI5094-show
LCD24-show	     Mouse_Key.py
LCD28-show	     NANO24-show
LCD32-show	     PyMouse-1.0.tar.gz
LCD35-show	     README.md
LCD5-show	     boot
LCD55-show	     etc
LCD7B-show	     python-xlib_0.23-2_all.deb
LCD7C-show	     rotate.sh
LCD7H-show	     system_backup.sh
LCD7S-show	     system_config.sh
MHS24-show	     system_restore.sh
MHS32-show	     usr
MHS35-show	     xinput-calibrator_0.7.5+git20140201-1+b2_arm64.deb
MHS35B-show	     xinput-calibrator_0.7.5-1_armhf.deb
MHS35IPS-show	     xserver-xorg-input-evdev_1%3a2.10.6-1+b1_armhf.deb
MHS40-show	     xserver-xorg-input-evdev_1%3a2.10.6-2_arm64.deb
#+end_example

#+RESULTS:
: Running in /home/pi/tmp/LCD-show host 'jrr5' on Tue May 19 09:52:35 EEST 2026

Install driver
#+BEGIN_SRC bash :eval no-export :results output
echo "Running in $(pwd) host '$(hostname)' on $(date)"
sudo ./LCD35-show 
#+END_SRC

Reboots automagically

#+call: ping-ip()

#+RESULTS:
: Ping JRR5_IP=jrr5.local on Tue May 19 09:54:29 EEST 2026
: PING jrr5.local (192.168.1.203) 56(84) bytes of data.
: 64 bytes from jrr5.local (192.168.1.203): icmp_seq=1 ttl=64 time=0.101 ms
: 64 bytes from jrr5.local (192.168.1.203): icmp_seq=2 ttl=64 time=0.065 ms
: 64 bytes from jrr5.local (192.168.1.203): icmp_seq=3 ttl=64 time=0.070 ms
: 
: --- jrr5.local ping statistics ---
: 3 packets transmitted, 3 received, 0% packet loss, time 2008ms
: rtt min/avg/max/mdev = 0.065/0.078/0.101/0.015 ms

#+call: reboot()

** Install packages needed by ILI9486 -drive

As instructed on: https://github.com/SirLefti/Python_ILI9486

#+BEGIN_SRC bash :eval no-export :results output
echo "Running in $(pwd) host '$(hostname)' on $(date)"
sudo apt -y install \
     libopenjp2-7 \
     libopenblas0 \
     python3 \
     python3-rpi-lgpio 
#+END_SRC

#+RESULTS:
#+begin_example
Running in /home/pi host 'jrr5x' on Thu Jul 16 18:59:16 EEST 2026

Reading package lists... 0%

Reading package lists... 100%

Building dependency tree... 0%

Building dependency tree... 0%

Building dependency tree... 50%

Building dependency tree... 50%

Building dependency tree... 55%

Building dependency tree... 71%

Building dependency tree... 87%

Reading state information... 0%

Reading state information... 0%
                                
libopenjp2-7 is already the newest version (2.5.3-2.1~deb13u2).
libopenjp2-7 set to manually installed.
python3 is already the newest version (3.13.5-1).
python3 set to manually installed.
python3-rpi-lgpio is already the newest version (0.6-0~rpt1+trixie).
Installing:
[32m  libopenblas0
[0m
Installing dependencies:
[32m  libopenblas0-pthread
[0m
Summary:
  Upgrading: 0, Installing: 2, Removing: 0, Not Upgrading: 0
  Download size: 3599 kB
  Space needed: 25.6 MB / 5918 MB available

[33m
0% [Working][0m
            
Get:1 http://deb.debian.org/debian trixie/main arm64 libopenblas0-pthread arm64 0.3.29+ds-3 [3557 kB]
[33m
0% [1 libopenblas0-pthread 0 B/3557 kB 0%][0m[33m
38% [1 libopenblas0-pthread 1714 kB/3557 kB 48%][0m[33m
66% [1 libopenblas0-pthread 2992 kB/3557 kB 84%][0m[33m
                                                
89% [Working][0m
             
Get:2 http://deb.debian.org/debian trixie/main arm64 libopenblas0 arm64 0.3.29+ds-3 [42.7 kB]
[33m
89% [2 libopenblas0 1444 B/42.7 kB 3%][0m[33m
                                      
100% [Working][0m
              
Fetched 3599 kB in 1s (2536 kB/s)
Selecting previously unselected package libopenblas0-pthread:arm64.
(Reading database ... 
(Reading database ... 5%
(Reading database ... 10%
(Reading database ... 15%
(Reading database ... 20%
(Reading database ... 25%
(Reading database ... 30%
(Reading database ... 35%
(Reading database ... 40%
(Reading database ... 45%
(Reading database ... 50%
(Reading database ... 55%
(Reading database ... 60%
(Reading database ... 65%
(Reading database ... 70%
(Reading database ... 75%
(Reading database ... 80%
(Reading database ... 85%
(Reading database ... 90%
(Reading database ... 95%
(Reading database ... 100%
(Reading database ... 73134 files and directories currently installed.)
Preparing to unpack .../libopenblas0-pthread_0.3.29+ds-3_arm64.deb ...
Unpacking libopenblas0-pthread:arm64 (0.3.29+ds-3) ...
Selecting previously unselected package libopenblas0:arm64.
Preparing to unpack .../libopenblas0_0.3.29+ds-3_arm64.deb ...
Unpacking libopenblas0:arm64 (0.3.29+ds-3) ...
Setting up libopenblas0-pthread:arm64 (0.3.29+ds-3) ...
update-alternatives: using /usr/lib/aarch64-linux-gnu/openblas-pthread/libblas.so.3 to provide /usr/lib/aarch64-linux-gnu/libblas.so.3 (libblas.so.3-aarch64-linux-gnu) in auto mode
update-alternatives: using /usr/lib/aarch64-linux-gnu/openblas-pthread/liblapack.so.3 to provide /usr/lib/aarch64-linux-gnu/liblapack.so.3 (liblapack.so.3-aarch64-linux-gnu) in auto mode
update-alternatives: using /usr/lib/aarch64-linux-gnu/openblas-pthread/libopenblas.so.0 to provide /usr/lib/aarch64-linux-gnu/libopenblas.so.0 (libopenblas.so.0-aarch64-linux-gnu) in auto mode
Setting up libopenblas0:arm64 (0.3.29+ds-3) ...
Processing triggers for libc-bin (2.41-12+rpt1+deb13u3) ...
#+end_example

* Packages NOT installed
** +~vlc~: vlc playrer+

#+call: apt-install(PKG="vlc")

#+RESULTS:
: Running 'sudo apt install -y vlc' in host 'jrr5' on Wed Nov 20 14:31:34 EET 2024
: 
Reading package lists... 0%

Reading package lists... 100%

Reading package lists... Done
: 
Building dependency tree... 0%

Building dependency tree... 0%

Building dependency tree... 50%

Building dependency tree... 50%

Building dependency tree... 67%

Building dependency tree... 97%

Building dependency tree... Done
: 
Reading state information... 0% 

Reading state information... 0%

Reading state information... Done
: vlc is already the newest version (1:3.0.21-0+rpt3+deb12u1).
: 0 upgraded, 0 newly installed, 0 to remove and 0 not upgraded.

Ensure that ffmpgeg is installed

#+BEGIN_SRC bash :eval no-export :results output :dir /ssh:jrr5:
echo "Running in host $(hostname) on $(date)"
ffmpeg --help 2>&1; true
#+END_SRC

#+RESULTS:
#+begin_example
Running in host jrr5 on Wed Nov 20 14:39:18 EET 2024
ffmpeg version 5.1.6-0+deb12u1+rpt1 Copyright (c) 2000-2024 the FFmpeg developers
  built with gcc 12 (Debian 12.2.0-14)
  configuration: --prefix=/usr --extra-version=0+deb12u1+rpt1 --toolchain=hardened --incdir=/usr/include/aarch64-linux-gnu --enable-gpl --disable-stripping --disable-mmal --enable-gnutls --enable-ladspa --enable-libaom --enable-libass --enable-libbluray --enable-libbs2b --enable-libcaca --enable-libcdio --enable-libcodec2 --enable-libdav1d --enable-libflite --enable-libfontconfig --enable-libfreetype --enable-libfribidi --enable-libglslang --enable-libgme --enable-libgsm --enable-libjack --enable-libmp3lame --enable-libmysofa --enable-libopenjpeg --enable-libopenmpt --enable-libopus --enable-libpulse --enable-librabbitmq --enable-librist --enable-librubberband --enable-libshine --enable-libsnappy --enable-libsoxr --enable-libspeex --enable-libsrt --enable-libssh --enable-libsvtav1 --enable-libtheora --enable-libtwolame --enable-libvidstab --enable-libvorbis --enable-libvpx --enable-libwebp --enable-libx265 --enable-libxml2 --enable-libxvid --enable-libzimg --enable-libzmq --enable-libzvbi --enable-lv2 --enable-omx --enable-openal --enable-opencl --enable-opengl --enable-sand --enable-sdl2 --disable-sndio --enable-libjxl --enable-neon --enable-v4l2-request --enable-libudev --enable-epoxy --libdir=/usr/lib/aarch64-linux-gnu --arch=arm64 --enable-pocketsphinx --enable-librsvg --enable-libdc1394 --enable-libdrm --enable-vout-drm --enable-libiec61883 --enable-chromaprint --enable-frei0r --enable-libx264 --enable-libplacebo --enable-librav1e --enable-shared
  libavutil      57. 28.100 / 57. 28.100
  libavcodec     59. 37.100 / 59. 37.100
  libavformat    59. 27.100 / 59. 27.100
  libavdevice    59.  7.100 / 59.  7.100
  libavfilter     8. 44.100 /  8. 44.100
  libswscale      6.  7.100 /  6.  7.100
  libswresample   4.  7.100 /  4.  7.100
  libpostproc    56.  6.100 / 56.  6.100
Hyper fast Audio and Video encoder
usage: ffmpeg [options] [[infile options] -i infile]... {[outfile options] outfile}...

Getting help:
    -h      -- print basic options
    -h long -- print more options
    -h full -- print all options (including all format and codec specific options, very long)
    -h type=name -- print all options for the named decoder/encoder/demuxer/muxer/filter/bsf/protocol
    See man ffmpeg for detailed description of the options.

Print help / information / capabilities:
-L                  show license
-h topic            show help
-? topic            show help
-help topic         show help
--help topic        show help
-version            show version
-buildconf          show build configuration
-formats            show available formats
-muxers             show available muxers
-demuxers           show available demuxers
-devices            show available devices
-codecs             show available codecs
-decoders           show available decoders
-encoders           show available encoders
-bsfs               show available bit stream filters
-protocols          show available protocols
-filters            show available filters
-pix_fmts           show available pixel formats
-layouts            show standard channel layouts
-sample_fmts        show available audio sample formats
-dispositions       show available stream dispositions
-colors             show available color names
-sources device     list sources of the input device
-sinks device       list sinks of the output device
-hwaccels           show available HW acceleration methods

Global options (affect whole program instead of just one file):
-loglevel loglevel  set logging level
-v loglevel         set logging level
-report             generate a report
-max_alloc bytes    set maximum size of a single allocated block
-y                  overwrite output files
-n                  never overwrite output files
-ignore_unknown     Ignore unknown stream types
-filter_threads     number of non-complex filter threads
-filter_complex_threads  number of threads for -filter_complex
-stats              print progress report during encoding
-max_error_rate maximum error rate  ratio of decoding errors (0.0: no errors, 1.0: 100% errors) above which ffmpeg returns an error instead of success.
-vol volume         change audio volume (256=normal)

Per-file main options:
-f fmt              force format
-c codec            codec name
-codec codec        codec name
-pre preset         preset name
-map_metadata outfile[,metadata]:infile[,metadata]  set metadata information of outfile from infile
-t duration         record or transcode "duration" seconds of audio/video
-to time_stop       record or transcode stop time
-fs limit_size      set the limit file size in bytes
-ss time_off        set the start time offset
-sseof time_off     set the start time offset relative to EOF
-seek_timestamp     enable/disable seeking by timestamp with -ss
-timestamp time     set the recording timestamp ('now' to set the current time)
-metadata string=string  add metadata
-program title=string:st=number...  add program with specified streams
-target type        specify target file type ("vcd", "svcd", "dvd", "dv" or "dv50" with optional prefixes "pal-", "ntsc-" or "film-")
-apad               audio pad
-frames number      set the number of frames to output
-filter filter_graph  set stream filtergraph
-filter_script filename  read stream filtergraph description from a file
-reinit_filter      reinit filtergraph on input parameter changes
-discard            discard
-disposition        disposition

Video options:
-vframes number     set the number of video frames to output
-r rate             set frame rate (Hz value, fraction or abbreviation)
-fpsmax rate        set max frame rate (Hz value, fraction or abbreviation)
-s size             set frame size (WxH or abbreviation)
-aspect aspect      set aspect ratio (4:3, 16:9 or 1.3333, 1.7777)
-vn                 disable video
-vcodec codec       force video codec ('copy' to copy stream)
-timecode hh:mm:ss[:;.]ff  set initial TimeCode value.
-pass n             select the pass number (1 to 3)
-vf filter_graph    set video filters
-ab bitrate         audio bitrate (please use -b:a)
-b bitrate          video bitrate (please use -b:v)
-dn                 disable data

Audio options:
-aframes number     set the number of audio frames to output
-aq quality         set audio quality (codec-specific)
-ar rate            set audio sampling rate (in Hz)
-ac channels        set number of audio channels
-an                 disable audio
-acodec codec       force audio codec ('copy' to copy stream)
-vol volume         change audio volume (256=normal)
-af filter_graph    set audio filters

Subtitle options:
-s size             set frame size (WxH or abbreviation)
-sn                 disable subtitle
-scodec codec       force subtitle codec ('copy' to copy stream)
-stag fourcc/tag    force subtitle tag/fourcc
-fix_sub_duration   fix subtitles duration
-canvas_size size   set canvas size (WxH or abbreviation)
-spre preset        set the subtitle options to the indicated preset

#+end_example

Generate sine wave in ~tmp/sine_1000.wav~

Ref: https://stackoverflow.com/questions/5109038/linux-sine-wave-audio-generator

#+BEGIN_SRC bash :eval no-export :results output :dir /ssh:jrr5:
echo "Running in $(pwd) in host '$(hostname)' on $(date)"
FILE="tmp/sine_1000.wav"
rm -f $FILE
ffmpeg -f lavfi -i "sine=f=1000:d=2" -ac 2 -y -nostdin $FILE 2>&1; true
ls -ltr $FILE
#+END_SRC

#+RESULTS:
#+begin_example
Running in /home/pi in host 'jrr5' on Wed Nov 20 14:52:03 EET 2024
ffmpeg version 5.1.6-0+deb12u1+rpt1 Copyright (c) 2000-2024 the FFmpeg developers
  built with gcc 12 (Debian 12.2.0-14)
  configuration: --prefix=/usr --extra-version=0+deb12u1+rpt1 --toolchain=hardened --incdir=/usr/include/aarch64-linux-gnu --enable-gpl --disable-stripping --disable-mmal --enable-gnutls --enable-ladspa --enable-libaom --enable-libass --enable-libbluray --enable-libbs2b --enable-libcaca --enable-libcdio --enable-libcodec2 --enable-libdav1d --enable-libflite --enable-libfontconfig --enable-libfreetype --enable-libfribidi --enable-libglslang --enable-libgme --enable-libgsm --enable-libjack --enable-libmp3lame --enable-libmysofa --enable-libopenjpeg --enable-libopenmpt --enable-libopus --enable-libpulse --enable-librabbitmq --enable-librist --enable-librubberband --enable-libshine --enable-libsnappy --enable-libsoxr --enable-libspeex --enable-libsrt --enable-libssh --enable-libsvtav1 --enable-libtheora --enable-libtwolame --enable-libvidstab --enable-libvorbis --enable-libvpx --enable-libwebp --enable-libx265 --enable-libxml2 --enable-libxvid --enable-libzimg --enable-libzmq --enable-libzvbi --enable-lv2 --enable-omx --enable-openal --enable-opencl --enable-opengl --enable-sand --enable-sdl2 --disable-sndio --enable-libjxl --enable-neon --enable-v4l2-request --enable-libudev --enable-epoxy --libdir=/usr/lib/aarch64-linux-gnu --arch=arm64 --enable-pocketsphinx --enable-librsvg --enable-libdc1394 --enable-libdrm --enable-vout-drm --enable-libiec61883 --enable-chromaprint --enable-frei0r --enable-libx264 --enable-libplacebo --enable-librav1e --enable-shared
  libavutil      57. 28.100 / 57. 28.100
  libavcodec     59. 37.100 / 59. 37.100
  libavformat    59. 27.100 / 59. 27.100
  libavdevice    59.  7.100 / 59.  7.100
  libavfilter     8. 44.100 /  8. 44.100
  libswscale      6.  7.100 /  6.  7.100
  libswresample   4.  7.100 /  4.  7.100
  libpostproc    56.  6.100 / 56.  6.100
Input #0, lavfi, from 'sine=f=1000:d=2':
  Duration: N/A, start: 0.000000, bitrate: 705 kb/s
  Stream #0:0: Audio: pcm_s16le, 44100 Hz, mono, s16, 705 kb/s
Stream mapping:
  Stream #0:0 -> #0:0 (pcm_s16le (native) -> pcm_s16le (native))
Output #0, wav, to 'tmp/sine_1000.wav':
  Metadata:
    ISFT            : Lavf59.27.100
  Stream #0:0: Audio: pcm_s16le ([1][0][0][0] / 0x0001), 44100 Hz, stereo, s16, 1411 kb/s
    Metadata:
      encoder         : Lavc59.37.100 pcm_s16le
size=       4kB time=00:00:00.02 bitrate=1438.1kbits/s speed=1.16e+04x    
size=     345kB time=00:00:02.00 bitrate=1411.5kbits/s speed=65.2x    
video:0kB audio:345kB subtitle:0kB other streams:0kB global headers:0kB muxing overhead: 0.022109%
-rw-r--r-- 1 pi pi 352878 Nov 20 14:52 tmp/sine_1000.wav
#+end_example
** +~audacity~: the world's most popular audio editing and recording app+

#+BEGIN_SRC bash :eval no-export :results output
echo "Running in host '$(hostname)' on $(date)"

#+END_SRC

#+RESULTS:
: Running in host 'jrr5' on Tue Nov 26 10:31:46 EET 2024

#+BEGIN_SRC bash :eval no-export :results output
sudo apt-get -y install audacity
#+END_SRC

#+RESULTS:
#+begin_example

Reading package lists... 0%

Reading package lists... 100%

Reading package lists... Done

Building dependency tree... 0%

Building dependency tree... 0%

Building dependency tree... 50%

Building dependency tree... 50%

Building dependency tree... 57%

Building dependency tree... 76%

Building dependency tree... 96%

Building dependency tree... Done

Reading state information... 0% 

Reading state information... 0%

Reading state information... Done
The following additional packages will be installed:
  audacity-data libflac++10 libpcre2-32-0 libportaudio2 libportsmf0 libsbsms10
  libsuil-0-0 libvamp-hostsdk3v5 libwxbase3.2-1 libwxgtk3.2-1
Suggested packages:
  ladspa-plugin
The following NEW packages will be installed:
  audacity audacity-data libflac++10 libpcre2-32-0 libportaudio2 libportsmf0
  libsbsms10 libsuil-0-0 libvamp-hostsdk3v5 libwxbase3.2-1 libwxgtk3.2-1
0 upgraded, 11 newly installed, 0 to remove and 9 not upgraded.
Need to get 12.7 MB of archives.
After this operation, 61.3 MB of additional disk space will be used.

0% [Working]
            
Get:1 http://deb.debian.org/debian bookworm/main arm64 audacity-data all 3.2.4+dfsg-1 [2409 kB]

0% [1 audacity-data 0 B/2409 kB 0%]
11% [1 audacity-data 1679 kB/2409 kB 70%]
                                         
17% [Working]
             
Get:2 http://deb.debian.org/debian bookworm/main arm64 libflac++10 arm64 1.4.2+ds-2 [50.4 kB]

17% [2 libflac++10 2888 B/50.4 kB 6%]
                                     
19% [Working]
             
Get:3 http://deb.debian.org/debian bookworm/main arm64 libportaudio2 arm64 19.6.0-1.2 [61.2 kB]

19% [3 libportaudio2 2335 B/61.2 kB 4%]
                                       
21% [Working]
             
Get:4 http://deb.debian.org/debian bookworm/main arm64 libportsmf0 arm64 0.1~svn20101010-6 [52.3 kB]

21% [4 libportsmf0 5776 B/52.3 kB 11%]
                                      
23% [Working]
             
Get:5 http://deb.debian.org/debian bookworm/main arm64 libsbsms10 arm64 2.3.0-1 [100 kB]

23% [5 libsbsms10 0 B/100 kB 0%]
                                
26% [Working]
             
Get:6 http://deb.debian.org/debian bookworm/main arm64 libsuil-0-0 arm64 0.10.18-1 [26.2 kB]

26% [6 libsuil-0-0 9433 B/26.2 kB 36%]
                                      
28% [Working]
             
Get:7 http://deb.debian.org/debian bookworm/main arm64 libvamp-hostsdk3v5 arm64 2.10.0-3 [81.7 kB]

28% [7 libvamp-hostsdk3v5 769 B/81.7 kB 1%]
                                           
30% [Working]
             
Get:8 http://deb.debian.org/debian bookworm/main arm64 libpcre2-32-0 arm64 10.42-1 [207 kB]

30% [8 libpcre2-32-0 15.5 kB/207 kB 8%]
                                       
33% [Working]
             
Get:9 http://deb.debian.org/debian bookworm/main arm64 libwxbase3.2-1 arm64 3.2.2+dfsg-2 [835 kB]

33% [9 libwxbase3.2-1 2966 B/835 kB 0%]
                                       
40% [Working]
             
Get:10 http://deb.debian.org/debian bookworm/main arm64 libwxgtk3.2-1 arm64 3.2.2+dfsg-2 [3984 kB]

40% [10 libwxgtk3.2-1 153 B/3984 kB 0%]
51% [10 libwxgtk3.2-1 1615 kB/3984 kB 41%]
61% [10 libwxgtk3.2-1 3242 kB/3984 kB 81%]
                                          
67% [Working]
             
Get:11 http://deb.debian.org/debian bookworm/main arm64 audacity arm64 3.2.4+dfsg-1 [4880 kB]

68% [11 audacity 21.2 kB/4880 kB 0%]
77% [11 audacity 1571 kB/4880 kB 32%]
88% [11 audacity 3250 kB/4880 kB 67%]
98% [11 audacity 4807 kB/4880 kB 98%]
                                     
100% [Working]
              
Fetched 12.7 MB in 4s (3109 kB/s)
Selecting previously unselected package audacity-data.
(Reading database ... 
(Reading database ... 5%
(Reading database ... 10%
(Reading database ... 15%
(Reading database ... 20%
(Reading database ... 25%
(Reading database ... 30%
(Reading database ... 35%
(Reading database ... 40%
(Reading database ... 45%
(Reading database ... 50%
(Reading database ... 55%
(Reading database ... 60%
(Reading database ... 65%
(Reading database ... 70%
(Reading database ... 75%
(Reading database ... 80%
(Reading database ... 85%
(Reading database ... 90%
(Reading database ... 95%
(Reading database ... 100%
(Reading database ... 128596 files and directories currently installed.)
Preparing to unpack .../00-audacity-data_3.2.4+dfsg-1_all.deb ...
Unpacking audacity-data (3.2.4+dfsg-1) ...
Selecting previously unselected package libflac++10:arm64.
Preparing to unpack .../01-libflac++10_1.4.2+ds-2_arm64.deb ...
Unpacking libflac++10:arm64 (1.4.2+ds-2) ...
Selecting previously unselected package libportaudio2:arm64.
Preparing to unpack .../02-libportaudio2_19.6.0-1.2_arm64.deb ...
Unpacking libportaudio2:arm64 (19.6.0-1.2) ...
Selecting previously unselected package libportsmf0:arm64.
Preparing to unpack .../03-libportsmf0_0.1~svn20101010-6_arm64.deb ...
Unpacking libportsmf0:arm64 (0.1~svn20101010-6) ...
Selecting previously unselected package libsbsms10:arm64.
Preparing to unpack .../04-libsbsms10_2.3.0-1_arm64.deb ...
Unpacking libsbsms10:arm64 (2.3.0-1) ...
Selecting previously unselected package libsuil-0-0:arm64.
Preparing to unpack .../05-libsuil-0-0_0.10.18-1_arm64.deb ...
Unpacking libsuil-0-0:arm64 (0.10.18-1) ...
Selecting previously unselected package libvamp-hostsdk3v5:arm64.
Preparing to unpack .../06-libvamp-hostsdk3v5_2.10.0-3_arm64.deb ...
Unpacking libvamp-hostsdk3v5:arm64 (2.10.0-3) ...
Selecting previously unselected package libpcre2-32-0:arm64.
Preparing to unpack .../07-libpcre2-32-0_10.42-1_arm64.deb ...
Unpacking libpcre2-32-0:arm64 (10.42-1) ...
Selecting previously unselected package libwxbase3.2-1:arm64.
Preparing to unpack .../08-libwxbase3.2-1_3.2.2+dfsg-2_arm64.deb ...
Unpacking libwxbase3.2-1:arm64 (3.2.2+dfsg-2) ...
Selecting previously unselected package libwxgtk3.2-1:arm64.
Preparing to unpack .../09-libwxgtk3.2-1_3.2.2+dfsg-2_arm64.deb ...
Unpacking libwxgtk3.2-1:arm64 (3.2.2+dfsg-2) ...
Selecting previously unselected package audacity.
Preparing to unpack .../10-audacity_3.2.4+dfsg-1_arm64.deb ...
Unpacking audacity (3.2.4+dfsg-1) ...
Setting up libportaudio2:arm64 (19.6.0-1.2) ...
Setting up libvamp-hostsdk3v5:arm64 (2.10.0-3) ...
Setting up audacity-data (3.2.4+dfsg-1) ...
Setting up libportsmf0:arm64 (0.1~svn20101010-6) ...
Setting up libsuil-0-0:arm64 (0.10.18-1) ...
Setting up libflac++10:arm64 (1.4.2+ds-2) ...
Setting up libpcre2-32-0:arm64 (10.42-1) ...
Setting up libsbsms10:arm64 (2.3.0-1) ...
Setting up libwxbase3.2-1:arm64 (3.2.2+dfsg-2) ...
Setting up libwxgtk3.2-1:arm64 (3.2.2+dfsg-2) ...
Setting up audacity (3.2.4+dfsg-1) ...
Processing triggers for shared-mime-info (2.2-1) ...
Processing triggers for mailcap (3.70+nmu1) ...
Processing triggers for desktop-file-utils (0.26-1) ...
Processing triggers for hicolor-icon-theme (0.17-2) ...
Processing triggers for gnome-menus (3.36.0-1.1) ...
Processing triggers for libc-bin (2.36-9+rpt2+deb12u9) ...
Processing triggers for man-db (2.11.2-2) ...
#+end_example

** ~python3-pip~: 

#+call: apt-install(PKG="python3-pip")

#+RESULTS:
#+begin_example
Running 'sudo apt install -y python3-pip' in host 'jrr5x' on Wed Jul 15 20:04:43 EEST 2026

Reading package lists... 0%

Reading package lists... 100%

Building dependency tree... 0%

Building dependency tree... 0%

Building dependency tree... 50%

Building dependency tree... 50%

Building dependency tree... 68%

Building dependency tree... 99%

Reading state information... 0%

Reading state information... 0%
                                
Installing:
[32m  python3-pip
[0m
Installing dependencies:
[32m  javascript-common  libjs-sphinxdoc   libpython3.13-dev  python3-wheel
  libexpat1-dev      libjs-underscore  python3-dev        python3.13-dev
  libjs-jquery       libpython3-dev    python3-packaging  zlib1g-dev
[0m
Suggested packages:
  apache2  | lighttpd  | httpd  python3-setuptools

Summary:
  Upgrading: 0, Installing: 13, Removing: 0, Not Upgrading: 0
  Download size: 9353 kB
  Space needed: 40.7 MB / 19.1 GB available

[33m
0% [Working][0m
            
Get:1 http://deb.debian.org/debian trixie/main arm64 javascript-common all 12+nmu1 [4864 B]
[33m
0% [1 javascript-common 1444 B/4864 B 30%] [Connecting to archive.raspberrypi.c[0m[33m
                                                                               
2% [Connecting to archive.raspberrypi.com][0m
                                          
Get:2 http://deb.debian.org/debian trixie/main arm64 libexpat1-dev arm64 2.7.1-2 [145 kB]
[33m
2% [2 libexpat1-dev 0 B/145 kB 0%] [Connecting to archive.raspberrypi.com][0m[33m
                                                                          
4% [Connecting to archive.raspberrypi.com][0m
                                          
Get:3 http://deb.debian.org/debian trixie/main arm64 libjs-jquery all 3.6.1+dfsg+~3.5.14-1 [326 kB]
[33m
4% [3 libjs-jquery 1299 B/326 kB 0%] [Connecting to archive.raspberrypi.com][0m[33m
                                                                            
9% [Connecting to archive.raspberrypi.com (46.235.231.145)][0m
                                                           
Get:4 http://deb.debian.org/debian trixie/main arm64 libjs-underscore all 1.13.4~dfsg+~1.11.4-3 [116 kB]
[33m
9% [4 libjs-underscore 25.1 kB/116 kB 22%] [Connecting to archive.raspberrypi.c[0m[33m
                                                                               
11% [Waiting for headers][0m
                         
Get:5 http://deb.debian.org/debian trixie/main arm64 libjs-sphinxdoc all 8.1.3-5 [30.5 kB]
[33m
11% [5 libjs-sphinxdoc 6774 B/30.5 kB 22%] [Waiting for headers][0m[33m
                                                                
13% [Waiting for headers][0m
                         
Get:6 http://archive.raspberrypi.com/debian trixie/main arm64 python3-pip all 25.1.1+dfsg-1+rpt1 [2266 kB]
[33m
13% [Waiting for headers] [6 python3-pip 1144 B/2266 kB 0%][0m
                                                           
Get:7 http://deb.debian.org/debian trixie/main arm64 zlib1g-dev arm64 1:1.3.dfsg+really1.3.1-1+b1 [917 kB]
[33m
13% [7 zlib1g-dev 3567 B/917 kB 0%] [6 python3-pip 20.0 kB/2266 kB 1%][0m[33m
26% [7 zlib1g-dev 802 kB/917 kB 87%] [6 python3-pip 763 kB/2266 kB 34%][0m[33m
                                                                       
36% [6 python3-pip 1597 kB/2266 kB 70%][0m
                                       
Get:8 http://deb.debian.org/debian trixie/main arm64 libpython3.13-dev arm64 3.13.5-2+deb13u3 [4929 kB]
[33m
36% [8 libpython3.13-dev 5007 B/4929 kB 0%] [6 python3-pip 1597 kB/2266 kB 70%][0m[33m
                                                                               
45% [8 libpython3.13-dev 186 kB/4929 kB 4%][0m[33m
55% [8 libpython3.13-dev 1390 kB/4929 kB 28%][0m[33m
70% [8 libpython3.13-dev 3062 kB/4929 kB 62%][0m[33m
83% [8 libpython3.13-dev 4678 kB/4929 kB 95%][0m[33m
                                             
87% [Working][0m
             
Get:9 http://deb.debian.org/debian trixie/main arm64 libpython3-dev arm64 3.13.5-1 [10.4 kB]
[33m
87% [9 libpython3-dev 7777 B/10.4 kB 74%][0m[33m
                                         
89% [Working][0m
             
Get:10 http://deb.debian.org/debian trixie/main arm64 python3.13-dev arm64 3.13.5-2+deb13u3 [504 kB]
[33m
89% [10 python3.13-dev 24.6 kB/504 kB 5%][0m[33m
                                         
94% [Waiting for headers][0m
                         
Get:11 http://deb.debian.org/debian trixie/main arm64 python3-dev arm64 3.13.5-1 [26.1 kB]
[33m
95% [11 python3-dev 2959 B/26.1 kB 11%][0m[33m
                                       
96% [Working][0m
             
Get:12 http://deb.debian.org/debian trixie/main arm64 python3-packaging all 25.0-1 [56.6 kB]
[33m
96% [12 python3-packaging 19.5 kB/56.6 kB 35%][0m[33m
                                              
98% [Working][0m
             
Get:13 http://deb.debian.org/debian trixie/main arm64 python3-wheel all 0.46.1-2 [21.7 kB]
[33m
98% [13 python3-wheel 21.7 kB/21.7 kB 100%][0m[33m
                                           
100% [Working][0m
              
Fetched 9353 kB in 3s (2794 kB/s)
debconf: unable to initialize frontend: Dialog
debconf: (Dialog frontend will not work on a dumb terminal, an emacs shell buffer, or without a controlling terminal.)
debconf: falling back to frontend: Readline
Selecting previously unselected package javascript-common.
(Reading database ... 
(Reading database ... 5%
(Reading database ... 10%
(Reading database ... 15%
(Reading database ... 20%
(Reading database ... 25%
(Reading database ... 30%
(Reading database ... 35%
(Reading database ... 40%
(Reading database ... 45%
(Reading database ... 50%
(Reading database ... 55%
(Reading database ... 60%
(Reading database ... 65%
(Reading database ... 70%
(Reading database ... 75%
(Reading database ... 80%
(Reading database ... 85%
(Reading database ... 90%
(Reading database ... 95%
(Reading database ... 100%
(Reading database ... 66614 files and directories currently installed.)
Preparing to unpack .../00-javascript-common_12+nmu1_all.deb ...
Unpacking javascript-common (12+nmu1) ...
Selecting previously unselected package libexpat1-dev:arm64.
Preparing to unpack .../01-libexpat1-dev_2.7.1-2_arm64.deb ...
Unpacking libexpat1-dev:arm64 (2.7.1-2) ...
Selecting previously unselected package libjs-jquery.
Preparing to unpack .../02-libjs-jquery_3.6.1+dfsg+~3.5.14-1_all.deb ...
Unpacking libjs-jquery (3.6.1+dfsg+~3.5.14-1) ...
Selecting previously unselected package libjs-underscore.
Preparing to unpack .../03-libjs-underscore_1.13.4~dfsg+~1.11.4-3_all.deb ...
Unpacking libjs-underscore (1.13.4~dfsg+~1.11.4-3) ...
Selecting previously unselected package libjs-sphinxdoc.
Preparing to unpack .../04-libjs-sphinxdoc_8.1.3-5_all.deb ...
Unpacking libjs-sphinxdoc (8.1.3-5) ...
Selecting previously unselected package zlib1g-dev:arm64.
Preparing to unpack .../05-zlib1g-dev_1%3a1.3.dfsg+really1.3.1-1+b1_arm64.deb ...
Unpacking zlib1g-dev:arm64 (1:1.3.dfsg+really1.3.1-1+b1) ...
Selecting previously unselected package libpython3.13-dev:arm64.
Preparing to unpack .../06-libpython3.13-dev_3.13.5-2+deb13u3_arm64.deb ...
Unpacking libpython3.13-dev:arm64 (3.13.5-2+deb13u3) ...
Selecting previously unselected package libpython3-dev:arm64.
Preparing to unpack .../07-libpython3-dev_3.13.5-1_arm64.deb ...
Unpacking libpython3-dev:arm64 (3.13.5-1) ...
Selecting previously unselected package python3.13-dev.
Preparing to unpack .../08-python3.13-dev_3.13.5-2+deb13u3_arm64.deb ...
Unpacking python3.13-dev (3.13.5-2+deb13u3) ...
Selecting previously unselected package python3-dev.
Preparing to unpack .../09-python3-dev_3.13.5-1_arm64.deb ...
Unpacking python3-dev (3.13.5-1) ...
Selecting previously unselected package python3-packaging.
Preparing to unpack .../10-python3-packaging_25.0-1_all.deb ...
Unpacking python3-packaging (25.0-1) ...
Selecting previously unselected package python3-wheel.
Preparing to unpack .../11-python3-wheel_0.46.1-2_all.deb ...
Unpacking python3-wheel (0.46.1-2) ...
Selecting previously unselected package python3-pip.
Preparing to unpack .../12-python3-pip_25.1.1+dfsg-1+rpt1_all.deb ...
Unpacking python3-pip (25.1.1+dfsg-1+rpt1) ...
Setting up javascript-common (12+nmu1) ...
Setting up python3-packaging (25.0-1) ...
Setting up libexpat1-dev:arm64 (2.7.1-2) ...
Setting up zlib1g-dev:arm64 (1:1.3.dfsg+really1.3.1-1+b1) ...
Setting up libjs-jquery (3.6.1+dfsg+~3.5.14-1) ...
Setting up libjs-underscore (1.13.4~dfsg+~1.11.4-3) ...
Setting up python3-wheel (0.46.1-2) ...
Setting up libpython3.13-dev:arm64 (3.13.5-2+deb13u3) ...
Setting up python3-pip (25.1.1+dfsg-1+rpt1) ...
Setting up libjs-sphinxdoc (8.1.3-5) ...
Setting up libpython3-dev:arm64 (3.13.5-1) ...
Setting up python3.13-dev (3.13.5-2+deb13u3) ...
Setting up python3-dev (3.13.5-1) ...
Processing triggers for man-db (2.13.1-1) ...
#+end_example

** ~python-pil~: install PKG 'pillow'

#+call: apt-install(PKG="python3-pillow")

#+RESULTS:
#+begin_example
Running 'sudo apt install -y python3-pillow' in host 'jrr5x' on Wed Jul 15 20:05:41 EEST 2026

Reading package lists... 0%

Reading package lists... 100%

Building dependency tree... 0%

Building dependency tree... 0%

Building dependency tree... 50%

Building dependency tree... 50%

Building dependency tree... 68%

Building dependency tree... 99%

Reading state information... 0%

Reading state information... 0%
                                
Note, selecting 'python3-pil' instead of 'python3-pillow'
Installing:
[32m  python3-pil
[0m
Installing dependencies:
[32m  libfreetype6    libharfbuzz0b   libopenjp2-7   libwebpmux3
  libfribidi0     libimagequant0  libraqm0       python3-olefile
  libgraphite2-3  liblcms2-2      libwebpdemux2
[0m
Suggested packages:
  liblcms2-utils  python-pil-doc

Summary:
  Upgrading: 0, Installing: 12, Removing: 0, Not Upgrading: 0
  Download size: 2122 kB
  Space needed: 6661 kB / 19.1 GB available

[33m
0% [Working][0m
            
Get:1 http://deb.debian.org/debian trixie/main arm64 libfreetype6 arm64 2.13.3+dfsg-1+deb13u1 [422 kB]
[33m
0% [1 libfreetype6 0 B/422 kB 0%][0m[33m
                                 
18% [Working][0m
             
Get:2 http://deb.debian.org/debian trixie/main arm64 libfribidi0 arm64 1.0.16-1 [26.5 kB]
[33m
18% [2 libfribidi0 1444 B/26.5 kB 5%][0m[33m
                                     
20% [Working][0m
             
Get:3 http://deb.debian.org/debian trixie/main arm64 libgraphite2-3 arm64 1.3.14-2+deb13u1 [70.3 kB]
[33m
20% [3 libgraphite2-3 0 B/70.3 kB 0%][0m[33m
                                     
25% [Working][0m
             
Get:4 http://deb.debian.org/debian trixie/main arm64 libharfbuzz0b arm64 10.2.0-1+deb13u1 [442 kB]
[33m
25% [4 libharfbuzz0b 21.3 kB/442 kB 5%][0m[33m
                                       
43% [Working][0m
             
Get:5 http://deb.debian.org/debian trixie/main arm64 libimagequant0 arm64 2.18.0-1+b2 [34.6 kB]
[33m
43% [5 libimagequant0 3263 B/34.6 kB 9%][0m[33m
                                        
46% [Working][0m
             
Get:6 http://deb.debian.org/debian trixie/main arm64 liblcms2-2 arm64 2.16-2+deb13u2 [152 kB]
[33m
46% [6 liblcms2-2 0 B/152 kB 0%][0m[33m
                                
53% [Working][0m
             
Get:7 http://deb.debian.org/debian trixie/main arm64 libopenjp2-7 arm64 2.5.3-2.1~deb13u2 [189 kB]
[33m
53% [7 libopenjp2-7 0 B/189 kB 0%][0m[33m
                                  
62% [Working][0m
             
Get:8 http://deb.debian.org/debian trixie/main arm64 libraqm0 arm64 0.10.2-1 [13.6 kB]
[33m
62% [8 libraqm0 3275 B/13.6 kB 24%][0m[33m
                                   
64% [Working][0m
             
Get:9 http://deb.debian.org/debian trixie/main arm64 libwebpdemux2 arm64 1.5.0-0.1 [113 kB]
[33m
64% [9 libwebpdemux2 0 B/113 kB 0%][0m[33m
                                   
70% [Working][0m
             
Get:10 http://deb.debian.org/debian trixie/main arm64 libwebpmux3 arm64 1.5.0-0.1 [125 kB]
[33m
70% [10 libwebpmux3 0 B/125 kB 0%][0m[33m
                                  
77% [Working][0m
             
Get:11 http://deb.debian.org/debian trixie/main arm64 python3-olefile all 0.47-1 [39.3 kB]
[33m
77% [11 python3-olefile 14.8 kB/39.3 kB 38%][0m[33m
                                            
80% [Working][0m
             
Get:12 http://deb.debian.org/debian trixie/main arm64 python3-pil arm64 11.1.0-5+deb13u4 [495 kB]
[33m
80% [12 python3-pil 0 B/495 kB 0%][0m[33m
                                  
100% [Working][0m
              
Fetched 2122 kB in 1s (2726 kB/s)
debconf: unable to initialize frontend: Dialog
debconf: (Dialog frontend will not work on a dumb terminal, an emacs shell buffer, or without a controlling terminal.)
debconf: falling back to frontend: Readline
Selecting previously unselected package libfreetype6:arm64.
(Reading database ... 
(Reading database ... 5%
(Reading database ... 10%
(Reading database ... 15%
(Reading database ... 20%
(Reading database ... 25%
(Reading database ... 30%
(Reading database ... 35%
(Reading database ... 40%
(Reading database ... 45%
(Reading database ... 50%
(Reading database ... 55%
(Reading database ... 60%
(Reading database ... 65%
(Reading database ... 70%
(Reading database ... 75%
(Reading database ... 80%
(Reading database ... 85%
(Reading database ... 90%
(Reading database ... 95%
(Reading database ... 100%
(Reading database ... 67873 files and directories currently installed.)
Preparing to unpack .../00-libfreetype6_2.13.3+dfsg-1+deb13u1_arm64.deb ...
Unpacking libfreetype6:arm64 (2.13.3+dfsg-1+deb13u1) ...
Selecting previously unselected package libfribidi0:arm64.
Preparing to unpack .../01-libfribidi0_1.0.16-1_arm64.deb ...
Unpacking libfribidi0:arm64 (1.0.16-1) ...
Selecting previously unselected package libgraphite2-3:arm64.
Preparing to unpack .../02-libgraphite2-3_1.3.14-2+deb13u1_arm64.deb ...
Unpacking libgraphite2-3:arm64 (1.3.14-2+deb13u1) ...
Selecting previously unselected package libharfbuzz0b:arm64.
Preparing to unpack .../03-libharfbuzz0b_10.2.0-1+deb13u1_arm64.deb ...
Unpacking libharfbuzz0b:arm64 (10.2.0-1+deb13u1) ...
Selecting previously unselected package libimagequant0:arm64.
Preparing to unpack .../04-libimagequant0_2.18.0-1+b2_arm64.deb ...
Unpacking libimagequant0:arm64 (2.18.0-1+b2) ...
Selecting previously unselected package liblcms2-2:arm64.
Preparing to unpack .../05-liblcms2-2_2.16-2+deb13u2_arm64.deb ...
Unpacking liblcms2-2:arm64 (2.16-2+deb13u2) ...
Selecting previously unselected package libopenjp2-7:arm64.
Preparing to unpack .../06-libopenjp2-7_2.5.3-2.1~deb13u2_arm64.deb ...
Unpacking libopenjp2-7:arm64 (2.5.3-2.1~deb13u2) ...
Selecting previously unselected package libraqm0:arm64.
Preparing to unpack .../07-libraqm0_0.10.2-1_arm64.deb ...
Unpacking libraqm0:arm64 (0.10.2-1) ...
Selecting previously unselected package libwebpdemux2:arm64.
Preparing to unpack .../08-libwebpdemux2_1.5.0-0.1_arm64.deb ...
Unpacking libwebpdemux2:arm64 (1.5.0-0.1) ...
Selecting previously unselected package libwebpmux3:arm64.
Preparing to unpack .../09-libwebpmux3_1.5.0-0.1_arm64.deb ...
Unpacking libwebpmux3:arm64 (1.5.0-0.1) ...
Selecting previously unselected package python3-olefile.
Preparing to unpack .../10-python3-olefile_0.47-1_all.deb ...
Unpacking python3-olefile (0.47-1) ...
Selecting previously unselected package python3-pil:arm64.
Preparing to unpack .../11-python3-pil_11.1.0-5+deb13u4_arm64.deb ...
Unpacking python3-pil:arm64 (11.1.0-5+deb13u4) ...
Setting up libgraphite2-3:arm64 (1.3.14-2+deb13u1) ...
Setting up liblcms2-2:arm64 (2.16-2+deb13u2) ...
Setting up python3-olefile (0.47-1) ...
Setting up libwebpdemux2:arm64 (1.5.0-0.1) ...
Setting up libfreetype6:arm64 (2.13.3+dfsg-1+deb13u1) ...
Setting up libfribidi0:arm64 (1.0.16-1) ...
Setting up libimagequant0:arm64 (2.18.0-1+b2) ...
Setting up libopenjp2-7:arm64 (2.5.3-2.1~deb13u2) ...
Setting up libharfbuzz0b:arm64 (10.2.0-1+deb13u1) ...
Setting up libwebpmux3:arm64 (1.5.0-0.1) ...
Setting up libraqm0:arm64 (0.10.2-1) ...
Setting up python3-pil:arm64 (11.1.0-5+deb13u4) ...
Processing triggers for libc-bin (2.41-12+rpt1+deb13u3) ...
#+end_example

** TODO ~RPi.GPIO~ 
:PROPERTIES:
:header-args+: :var  PKG="python3-Jetson.GPIO"
:END:

#+call: apt-search(PKG="GPIO")

#+RESULTS:
#+begin_example
Running in host 'jrr5x' on Wed Jul 15 20:07:27 EEST 2026
PKG=GPIO
airspyhf - HF+VHF software defined radio receiver - user runtime
libbcm2835-dev - access to GPIO and other IO functions on the Broadcom BCM 2835 chip
librte-raw-cnxk-gpio25 - Data Plane Development Kit (librte-raw-cnxk-gpio runtime library)
ledmon - Enclosure LED Utilities
gpiod - Tools for interacting with Linux GPIO character device - binary
libgpiod-dev - C library for interacting with Linux GPIO device - static libraries and headers
libgpiod-doc - C library for interacting with Linux GPIO device - library documentation
libgpiod3 - C library for interacting with Linux GPIO device - shared libraries
python3-libgpiod - Python bindings for libgpiod (Python 3)
libhipi-perl - Raspberry Pi GPIO Perl Modules
libpigpiod-if-dev - Development headers for client libraries for Raspberry Pi GPIO control
libpigpiod-if1t64 - Client library for Raspberry Pi GPIO control (deprecated)
libpigpiod-if2-1t64 - Client library for Raspberry Pi GPIO control
pigpio-tools - Client tools for Raspberry Pi GPIO control
python3-pigpio - Python module which talks to the pigpio daemon (Python 3)
python3-ftdi - user-space driver for popular FTDI devices
python3-ftdi-doc - user-space driver for popular FTDI devices. Documentation
python3-pyotgw - Library for interfacing with the OpenTherm Gateway
python-periphery-doc - Peripheral I/O (Documentation)
python3-periphery - Peripheral I/O (Python3 version)
reform2-lpc-dkms - dkms driver sources for Reform 2 LPC11U24
python3-rpi.gpio - Module to control Raspberry Pi GPIO channels (Python 3)
rpi.gpio-common - Module to control Raspberry Pi GPIO channels (common files)
stm32flash - STM32 chip flashing utility using a serial bootloader
svxlink-gpio - GPIO control scripts SvxLink amateur radio server
python3-typeshed - collection of library stubs for Python, with static types
python3-zigpy-zigate - Zigbee communication library for ZiGate-based devices
cm5-programming-jig-gpio-config - CM5 Programming Jig GPIO Configuration
cm5-programming-jig-gpio-config-dbgsym - debug symbols for cm5-programming-jig-gpio-config
libgpiolib-dev - GPIO library for Raspberry Pi devices
libgpiolib0 - GPIO library for Raspberry Pi devices
libgpiolib0-dbgsym - debug symbols for libgpiolib0
liblgpio-dev - Control GPIO pins via gpiochip devices - static libraries and headers
liblgpio1 - Control GPIO pins via gpiochip devices - shared libraries
librgpio-dev - Control GPIO pins remotely via rgpiod - static libraries and headers
librgpio1 - Control GPIO pins remotely via rgpiod - shared libraries
python-gpiozero-doc - Documentation for the gpiozero Python API
python-rpi-lgpio-doc - Compatibility shim for lgpio emulating the RPi.GPIO API - docs
python3-gpiozero - Simple API for controlling devices attached to a Pi's GPIO pins
python3-lgpio - Control GPIO pins via gpiochip devices - python3 bindings
python3-lgpio-dbgsym - debug symbols for python3-lgpio
python3-rgpio - Control GPIO pins remotely via rgpiod - python3 bindings
python3-rpi-lgpio - Compatibility shim for lgpio emulating the RPi.GPIO API
raspi-utils-core - Collection of scripts and simple applications
rgpio-tools - Control GPIO pins remotely
rgpiod - Daemon permitting remote control of GPIO pins
rpi-systemd-gpio - Run commands when a GPIO button is pressed on a Raspberry Pi
rpi-systemd-gpio-dbgsym - debug symbols for rpi-systemd-gpio
#+end_example

#+call: apt-install-doc()

#+RESULTS:
: Running 'sudo apt install -y python3-Jetson.GPIO' in host 'jrr5x' on Wed Jul 15 20:07:49 EEST 2026
: PKG=python3-Jetson.GPIO

#+call: apt-install()

#+RESULTS:
: Running 'sudo apt install -y python3-Jetson.GPIO' in host 'jrr5' on Tue May 19 09:37:06 EEST 2026
: 
Reading package lists... 0%

Reading package lists... 100%

Building dependency tree... 0%

Building dependency tree... 0%

Building dependency tree... 50%

Building dependency tree... 50%

Building dependency tree... 68%

Building dependency tree... 99%

Reading state information... 0%

Reading state information... 0%
                                
[1;31mError: [0m[1mUnable to locate package python3-Jetson.GPIO[0m
: [1;31mError: [0m[1mCouldn't find any package by glob 'python3-Jetson.GPIO'[0m

** ~python3-numpy~
:PROPERTIES:
:header-args+: :var  PKG="python3-numpy"
:END:

#+call: apt-search()

#+RESULTS:
: Running in host 'jrr5' on Tue May 19 10:43:03 EEST 2026
: PKG=python3-numpy
: python3-numpy - Python library for numerical computations (Python 3)
: python3-numpy-dev - Python library for numerical computations (Python 3 headers)
: python3-stl - stl file and 3d object handling for the Python language
: python3-numpydoc - Sphinx extension to support docstrings in Numpy format -- Python3
: python3-numpy-groupies - performs operations on/with subsets of n-dim arrays
: python3-numpysane - more-reasonable core functionality for numpy

#+call: apt-install()

#+RESULTS:
#+begin_example
Running 'sudo apt install -y python3-numpy' in host 'jrr5' on Tue May 19 10:43:15 EEST 2026

Reading package lists... 0%

Reading package lists... 100%

Building dependency tree... 0%

Building dependency tree... 0%

Building dependency tree... 50%

Building dependency tree... 50%

Building dependency tree... 68%

Building dependency tree... 99%

Reading state information... 0%

Reading state information... 0%
                                
Installing:
[32m  python3-numpy
[0m
Installing dependencies:
[32m  libblas3  libgfortran5  liblapack3  python3-numpy-dev
[0m
Suggested packages:
  gfortran  python-numpy-doc  python3-pytest

Summary:
  Upgrading: 0, Installing: 5, Removing: 0, Not Upgrading: 4
  Download size: 6026 kB
  Space needed: 28.8 MB / 19.1 GB available

[33m
0% [Working][0m
            
Get:1 http://deb.debian.org/debian trixie/main arm64 python3-numpy-dev arm64 1:2.2.4+ds-1 [136 kB]
[33m
0% [1 python3-numpy-dev 0 B/136 kB 0%][0m[33m
                                      
6% [Working][0m
            
Get:2 http://deb.debian.org/debian trixie/main arm64 libblas3 arm64 3.12.1-6 [104 kB]
[33m
6% [2 libblas3 0 B/104 kB 0%][0m[33m
                             
11% [Working][0m
             
Get:3 http://deb.debian.org/debian trixie/main arm64 libgfortran5 arm64 14.2.0-19 [361 kB]
[33m
11% [3 libgfortran5 0 B/361 kB 0%][0m[33m
                                  
20% [Working][0m
             
Get:4 http://deb.debian.org/debian trixie/main arm64 liblapack3 arm64 3.12.1-6 [1820 kB]
[33m
20% [4 liblapack3 0 B/1820 kB 0%][0m[33m
42% [4 liblapack3 1632 kB/1820 kB 90%][0m[33m
                                      
48% [Working][0m
             
Get:5 http://deb.debian.org/debian trixie/main arm64 python3-numpy arm64 1:2.2.4+ds-1 [3604 kB]
[33m
49% [5 python3-numpy 45.1 kB/3604 kB 1%][0m[33m
72% [5 python3-numpy 1770 kB/3604 kB 49%][0m[33m
93% [5 python3-numpy 3388 kB/3604 kB 94%][0m[33m
                                         
100% [Working][0m
              
Fetched 6026 kB in 2s (2882 kB/s)
debconf: unable to initialize frontend: Dialog
debconf: (Dialog frontend will not work on a dumb terminal, an emacs shell buffer, or without a controlling terminal.)
debconf: falling back to frontend: Readline
Selecting previously unselected package python3-numpy-dev:arm64.
(Reading database ... 
(Reading database ... 5%
(Reading database ... 10%
(Reading database ... 15%
(Reading database ... 20%
(Reading database ... 25%
(Reading database ... 30%
(Reading database ... 35%
(Reading database ... 40%
(Reading database ... 45%
(Reading database ... 50%
(Reading database ... 55%
(Reading database ... 60%
(Reading database ... 65%
(Reading database ... 70%
(Reading database ... 75%
(Reading database ... 80%
(Reading database ... 85%
(Reading database ... 90%
(Reading database ... 95%
(Reading database ... 100%
(Reading database ... 67636 files and directories currently installed.)
Preparing to unpack .../python3-numpy-dev_1%3a2.2.4+ds-1_arm64.deb ...
Unpacking python3-numpy-dev:arm64 (1:2.2.4+ds-1) ...
Selecting previously unselected package libblas3:arm64.
Preparing to unpack .../libblas3_3.12.1-6_arm64.deb ...
Unpacking libblas3:arm64 (3.12.1-6) ...
Selecting previously unselected package libgfortran5:arm64.
Preparing to unpack .../libgfortran5_14.2.0-19_arm64.deb ...
Unpacking libgfortran5:arm64 (14.2.0-19) ...
Selecting previously unselected package liblapack3:arm64.
Preparing to unpack .../liblapack3_3.12.1-6_arm64.deb ...
Unpacking liblapack3:arm64 (3.12.1-6) ...
Selecting previously unselected package python3-numpy.
Preparing to unpack .../python3-numpy_1%3a2.2.4+ds-1_arm64.deb ...
Unpacking python3-numpy (1:2.2.4+ds-1) ...
Setting up libblas3:arm64 (3.12.1-6) ...
update-alternatives: using /usr/lib/aarch64-linux-gnu/blas/libblas.so.3 to provide /usr/lib/aarch64-linux-gnu/libblas.so.3 (libblas.so.3-aarch64-linux-gnu) in auto mode
Setting up python3-numpy-dev:arm64 (1:2.2.4+ds-1) ...
Setting up libgfortran5:arm64 (14.2.0-19) ...
Setting up liblapack3:arm64 (3.12.1-6) ...
update-alternatives: using /usr/lib/aarch64-linux-gnu/lapack/liblapack.so.3 to provide /usr/lib/aarch64-linux-gnu/liblapack.so.3 (liblapack.so.3-aarch64-linux-gnu) in auto mode
Setting up python3-numpy (1:2.2.4+ds-1) ...
Processing triggers for man-db (2.13.1-1) ...
Processing triggers for libc-bin (2.41-12+rpt1+deb13u2) ...
#+end_example

** ~python3-spidev~
:PROPERTIES:
:header-args+: :var  PKG="python3-spidev"
:END:

#+call: apt-search(PKG="spidev")

#+RESULTS:
: Running in host 'jrr5' on Tue May 19 10:43:54 EEST 2026
: PKG=spidev
: flashrom - Identify, read, write, erase, and verify BIOS/ROM/flash chips
: spi-tools - Simple command line tools to help using Linux spidev devices
: python3-spidev - Python bindings for Linux SPI access through spidev
: libtss2-tcti-spidev0 - TPM2 Software stack library - TSS and TCTI libraries

: Running in host 'jrr5' on Mon Dec  9 09:52:05 EET 2024
: PKG=spidev
: flashrom - Identify, read, write, erase, and verify BIOS/ROM/flash chips
: spi-tools - Simple command line tools to help using Linux spidev devices
: python3-spidev - Bindings for Linux SPI access through spidev (Python 3)
: python3-spidev-dbgsym - debug symbols for python3-spidev

#+call: apt-install-doc()

#+RESULTS:
: Running 'sudo apt install -y python3-spidev' in host 'jrr5' on Tue May 19 10:44:15 EEST 2026
: PKG=python3-spidev

#+call: apt-install()

#+RESULTS:
: Running 'sudo apt install -y python3-spidev' in host 'jrr5' on Tue May 19 10:44:22 EEST 2026
: 
Reading package lists... 0%

Reading package lists... 100%

Building dependency tree... 0%

Building dependency tree... 0%

Building dependency tree... 50%

Building dependency tree... 50%

Building dependency tree... 68%

Building dependency tree... 99%

Reading state information... 0%

Reading state information... 0%
                                
python3-spidev is already the newest version (3.6-1+b6).
: Summary:
:   Upgrading: 0, Installing: 0, Removing: 0, Not Upgrading: 4

** ~spi-tools~:
:PROPERTIES:
:header-args+: :var  PKG="spi-tools"
:END:

#+call: apt-install-doc()

#+RESULTS:
: Running 'sudo apt install -y spi-tools' in host 'jrr5' on Tue May 19 10:45:19 EEST 2026
: PKG=spi-tools

#+call: apt-install()

#+RESULTS:
#+begin_example
Running 'sudo apt install -y spi-tools' in host 'jrr5' on Tue May 19 10:45:26 EEST 2026

Reading package lists... 0%

Reading package lists... 100%

Building dependency tree... 0%

Building dependency tree... 0%

Building dependency tree... 50%

Building dependency tree... 50%

Building dependency tree... 69%

Reading state information... 0%

Reading state information... 0%
                                
Installing:
[32m  spi-tools
[0m
Summary:
  Upgrading: 0, Installing: 1, Removing: 0, Not Upgrading: 4
  Download size: 9472 B
  Space needed: 154 kB / 19.0 GB available

[33m
0% [Working][0m
            
Get:1 http://deb.debian.org/debian trixie/main arm64 spi-tools arm64 0.8.4-1+b1 [9472 B]
[33m
12% [1 spi-tools 1444 B/9472 B 15%][0m[33m
                                   
100% [Working][0m
              
Fetched 9472 B in 0s (156 kB/s)
debconf: unable to initialize frontend: Dialog
debconf: (Dialog frontend will not work on a dumb terminal, an emacs shell buffer, or without a controlling terminal.)
debconf: falling back to frontend: Readline
Selecting previously unselected package spi-tools.
(Reading database ... 
(Reading database ... 5%
(Reading database ... 10%
(Reading database ... 15%
(Reading database ... 20%
(Reading database ... 25%
(Reading database ... 30%
(Reading database ... 35%
(Reading database ... 40%
(Reading database ... 45%
(Reading database ... 50%
(Reading database ... 55%
(Reading database ... 60%
(Reading database ... 65%
(Reading database ... 70%
(Reading database ... 75%
(Reading database ... 80%
(Reading database ... 85%
(Reading database ... 90%
(Reading database ... 95%
(Reading database ... 100%
(Reading database ... 68639 files and directories currently installed.)
Preparing to unpack .../spi-tools_0.8.4-1+b1_arm64.deb ...
Unpacking spi-tools (0.8.4-1+b1) ...
Setting up spi-tools (0.8.4-1+b1) ...
Processing triggers for man-db (2.13.1-1) ...
#+end_example

** ~pyyaml~: install yaml
:PROPERTIES:
:header-args+: :var  PKG="python3-yaml"
:END:

#+call: apt-install-doc()

#+RESULTS:
: Running 'sudo apt install -y python3-yaml' in host 'jrr5' on Tue May 19 10:45:57 EEST 2026
: PKG=python3-yaml

#+call: apt-search()

#+RESULTS:
: Running in host 'jrr5' on Tue May 19 10:46:02 EEST 2026
: PKG=python3-yaml
: python3-yamlfix - Simple opionated yaml formatter that keeps your comments
: python3-yamlordereddictloader - loader and dump for PyYAML keeping keys order
: python3-yaml - YAML parser and emitter for Python3

#+call: apt-install()

#+RESULTS:
: Running 'sudo apt install -y python3-yaml' in host 'jrr5' on Tue May 19 10:46:10 EEST 2026
: 
Reading package lists... 0%

Reading package lists... 100%

Building dependency tree... 0%

Building dependency tree... 0%

Building dependency tree... 50%

Building dependency tree... 50%

Building dependency tree... 68%

Building dependency tree... 99%

Reading state information... 0%

Reading state information... 0%
                                
python3-yaml is already the newest version (6.0.2-1+b2).
: python3-yaml set to manually installed.
: Summary:
:   Upgrading: 0, Installing: 0, Removing: 0, Not Upgrading: 4

* Configure Raspberry
** Enable SPI

Run termianal
#+begin_example
sudo raspi-config
#+end_example

#+begin_example
Interfacing Options -> SPI -> Enable SPI Interface
#+end_example

Run example program (NOT DONE)

#+BEGIN_SRC bash :eval no-export :results output :dir /ssh:jrr5:src
echo "Running in host '$(hostname)' on $(date)"
epaper/epd_2in13b_V3_test.py 2>&1; true
#+END_SRC

#+RESULTS:
#+begin_example
Running in host 'jrr5' on Mon Dec  9 09:49:07 EET 2024
INFO:root:epd2in13b_V3 Demo
INFO:root:init
DEBUG:waveshare_epd.epdconfig:module_init
DEBUG:waveshare_epd.epdconfig:setwarnings
DEBUG:waveshare_epd.epdconfig:self.RST_PIN
Traceback (most recent call last):
  File "/home/pi/src/epaper/epd_2in13b_V3_test.py", line 23, in <module>
    epd.init()
  File "/home/pi/src/lib/waveshare_epd/epd2in13b_V3.py", line 78, in init
    if (epdconfig.module_init() != 0):
        ^^^^^^^^^^^^^^^^^^^^^^^
  File "/home/pi/src/lib/waveshare_epd/epdconfig.py", line 76, in module_init
    self.GPIO.setup(self.CS_PIN, self.GPIO.OUT)
  File "/usr/lib/python3/dist-packages/RPi/GPIO/__init__.py", line 704, in setup
    initial = _check(lgpio.gpio_read(_chip, gpio))
                     ^^^^^^^^^^^^^^^^^^^^^^^^^^^^
  File "/usr/lib/python3/dist-packages/lgpio.py", line 903, in gpio_read
    return _u2i(_lgpio._gpio_read(handle&0xffff, gpio))
           ^^^^^^^^^^^^^^^^^^^^^^^^^^^^^^^^^^^^^^^^^^^^
  File "/usr/lib/python3/dist-packages/lgpio.py", line 458, in _u2i
    raise error(error_text(v))
lgpio.error: 'GPIO not allocated'
#+end_example

** Add mount for ~home2~ (PARTITION 3) to ~/etc/fstab~
:PROPERTIES:
:header-args+: :dir  /ssh:jrr5:
:header-args+:   :var  FILE="/etc/fstab"
:END:

Show current mounts 

#+name: mount-devs
#+BEGIN_SRC bash :eval no-export :results output :dir /ssh:jrr5:
echo "Running in $(pwd) host '$(hostname)' on $(date)"
mount | grep '/dev'
#+END_SRC

#+RESULTS: mount-devs
: Running in /home/pi host 'jrr5x' on Thu Jul 16 19:00:35 EEST 2026
: udev on /dev type devtmpfs (rw,nosuid,relatime,size=323340k,nr_inodes=80835,mode=755)
: devpts on /dev/pts type devpts (rw,nosuid,noexec,relatime,gid=5,mode=600,ptmxmode=000)
: /dev/mmcblk0p2 on / type ext4 (rw,noatime)
: tmpfs on /dev/shm type tmpfs (rw,nosuid,nodev)
: mqueue on /dev/mqueue type mqueue (rw,nosuid,nodev,noexec,relatime)
: /dev/mmcblk0p1 on /boot/firmware type vfat (rw,relatime,fmask=0022,dmask=0022,codepage=437,iocharset=ascii,shortname=mixed,errors=remount-ro)

Expected output

: Running in /home/pi host 'jrr5' on Tue May 19 10:51:42 EEST 2026
: udev on /dev type devtmpfs (rw,nosuid,relatime,size=323932k,nr_inodes=80983,mode=755)
: devpts on /dev/pts type devpts (rw,nosuid,noexec,relatime,gid=5,mode=600,ptmxmode=000)
: /dev/mmcblk0p2 on / type ext4 (rw,noatime)
: tmpfs on /dev/shm type tmpfs (rw,nosuid,nodev)
: mqueue on /dev/mqueue type mqueue (rw,nosuid,nodev,noexec,relatime)
: /dev/mmcblk0p1 on /boot/firmware type vfat (rw,relatime,fmask=0022,dmask=0022,codepage=437,iocharset=ascii,shortname=mixed,errors=remount-ro)

#+call: disk-space()

#+RESULTS:
#+begin_example
Installation target host jrr5x on Thu Jul 16 19:00:45 EEST 2026 for user pi
Free disk space
Filesystem      Size  Used Avail Use% Mounted on
udev            332M     0  332M   0% /dev
tmpfs           190M  4.1M  186M   3% /run
/dev/mmcblk0p2   11G  3.9G  5.9G  40% /
tmpfs           475M     0  475M   0% /dev/shm
tmpfs           5.3M   17k  5.3M   1% /run/lock
tmpfs           1.1M     0  1.1M   0% /run/credentials/systemd-journald.service
tmpfs           475M   46k  475M   1% /tmp
/dev/mmcblk0p1  529M   70M  460M  14% /boot/firmware
tmpfs           1.1M     0  1.1M   0% /run/credentials/getty@tty1.service
tmpfs           1.1M     0  1.1M   0% /run/credentials/serial-getty@ttyS0.service
tmpfs            95M  8.2k   95M   1% /run/user/1000
#+end_example

Expected output:

#+begin_example
Installation target host jrr5x on Wed Jul 15 20:17:33 EEST 2026 for user pi
Free disk space
Filesystem      Size  Used Avail Use% Mounted on
udev            332M     0  332M   0% /dev
tmpfs           190M  4.1M  186M   3% /run
/dev/mmcblk0p2   24G  3.9G   19G  18% /
tmpfs           475M     0  475M   0% /dev/shm
tmpfs           5.3M   17k  5.3M   1% /run/lock
tmpfs           1.1M     0  1.1M   0% /run/credentials/systemd-journald.service
tmpfs           475M   50k  475M   1% /tmp
/dev/mmcblk0p1  529M   70M  460M  14% /boot/firmware
tmpfs           1.1M     0  1.1M   0% /run/credentials/getty@tty1.service
tmpfs           1.1M     0  1.1M   0% /run/credentials/serial-getty@ttyS0.service
tmpfs            95M  8.2k   95M   1% /run/user/1000
#+end_example

Show partition PARTUUIDs

#+BEGIN_SRC bash :eval no-export :results output 
echo "Running in $(pwd) host '$(hostname)' on $(date)"
blkid
#+END_SRC

#+RESULTS:
: Running in /home/pi host 'jrr5x' on Thu Jul 16 19:00:59 EEST 2026
: /dev/mmcblk0p3: LABEL="home2" UUID="30f2451a-bc8f-44d6-809c-4a455f49bb52" BLOCK_SIZE="4096" TYPE="ext4" PARTUUID="0249d47d-03"
: /dev/mmcblk0p1: LABEL_FATBOOT="bootfs" LABEL="bootfs" UUID="B2F0-82D2" BLOCK_SIZE="512" TYPE="vfat" PARTUUID="0249d47d-01"
: /dev/mmcblk0p2: LABEL="rootfs" UUID="15f4c6be-1102-4331-9904-f78e78afd1fd" BLOCK_SIZE="4096" TYPE="ext4" PARTUUID="0249d47d-02"
: /dev/loop0: TYPE="swap"
: /dev/zram0: LABEL="zram0" UUID="145f73d1-c3ae-424e-85fd-7277fca7483c" TYPE="swap"

Expected output (PARTUID may change)

: Running in /home/pi host 'jrr5' on Tue May 19 10:51:56 EEST 2026
: /dev/mmcblk0p3: LABEL="home2" UUID="fa610b2a-3c01-408b-acf1-093e30072a64" BLOCK_SIZE="4096" TYPE="ext4" PARTUUID="f307c993-03"
: /dev/mmcblk0p1: LABEL_FATBOOT="bootfs" LABEL="bootfs" UUID="0D58-6978" BLOCK_SIZE="512" TYPE="vfat" PARTUUID="f307c993-01"
: /dev/mmcblk0p2: LABEL="rootfs" UUID="e634e0a4-a958-46cb-abad-862d2102573f" BLOCK_SIZE="4096" TYPE="ext4" PARTUUID="f307c993-02"
: /dev/loop0: TYPE="swap"
: /dev/zram0: LABEL="zram0" UUID="9abea693-9507-4a7e-bb07-8de1e7098aaa" TYPE="swap"

Modify ~/etc/fstab~ on SD_DEV PARTITION 2 mounted on MNT
- *Check and possibly fix PARTUUID for /home2* 

#+BEGIN_SRC bash :eval no-export :results output
#FILE=$MNT/etc/fstab
START="Modifications from  org-document raspberry.org - start"
END="Modifications from  org-document raspberry.org - end"

echo "modifying $FILE on host '$(hostname)'"
ls -ltr $FILE
sudo sed -i -e "/$START/,/$END/d" $FILE

cat <<HERE | sudo tee -a $FILE
# $START

# Mount partition 3 as  /home2 on 
PARTUUID=0249d47d-03 /home2             ext4    defaults,noatime  0       1

## tmp directorises to tmpfs (these will be lost on reboot)
# tmpfs /var/tmp tmpfs defaults,noatime,nosuid,size=50m 0 0
# tmpfs /var/cache tmpfs defaults,noatime,nosuid,size=100m 0 0

# $END
HERE

#+END_SRC

#+RESULTS:
#+begin_example
modifying /etc/fstab on host 'jrr5x'
-rw-r--r-- 1 root root 216 Jan  1  1970 /etc/fstab
# Modifications from  org-document raspberry.org - start

# Mount partition 3 as  /home2 on 
PARTUUID=0249d47d-03 /home2             ext4    defaults,noatime  0       1

## tmp directorises to tmpfs (these will be lost on reboot)
# tmpfs /var/tmp tmpfs defaults,noatime,nosuid,size=50m 0 0
# tmpfs /var/cache tmpfs defaults,noatime,nosuid,size=100m 0 0

# Modifications from  org-document raspberry.org - end
#+end_example

Show resulting file
#+BEGIN_SRC bash :eval no-export :results output
echo "Running in $(pwd) host '$(hostname)' on $(date)"
echo "FILE=$FILE"
cat $FILE
#+END_SRC

#+RESULTS:
#+begin_example
Running in /home/pi host 'jrr5x' on Thu Jul 16 19:01:28 EEST 2026
FILE=/etc/fstab
proc            /proc           proc    defaults          0       0
PARTUUID=0249d47d-01  /boot/firmware  vfat    defaults          0       2
PARTUUID=0249d47d-02  /               ext4    defaults,noatime  0       1
# Modifications from  org-document raspberry.org - start

# Mount partition 3 as  /home2 on 
PARTUUID=0249d47d-03 /home2             ext4    defaults,noatime  0       1

## tmp directorises to tmpfs (these will be lost on reboot)
# tmpfs /var/tmp tmpfs defaults,noatime,nosuid,size=50m 0 0
# tmpfs /var/cache tmpfs defaults,noatime,nosuid,size=100m 0 0

# Modifications from  org-document raspberry.org - end
#+end_example

#+begin_example
Running in /home/pi host 'jrr5' on Tue May 19 10:52:44 EEST 2026
FILE=/etc/fstab
proc            /proc           proc    defaults          0       0
PARTUUID=f307c993-01  /boot/firmware  vfat    defaults          0       2
PARTUUID=f307c993-02  /               ext4    defaults,noatime  0       1
# Modifications from  org-document raspberry.org - start

# Mount partition 3 as  /home2 on 
PARTUUID=f307c993-03  /home2             ext4    defaults,noatime  0       1

# tmp directorises to tmpfs (these will be lost on reboot)
# tmpfs /tmp tmpfs defaults,noatime,nosuid,size=100m 0 0
# tmpfs /var/tmp tmpfs defaults,noatime,nosuid,size=50m 0 0
# tmpfs /var/cache tmpfs defaults,noatime,nosuid,size=100m 0 0

# Modifications from  org-document raspberry.org - end
#+end_example

#+call: reboot()

#+call: ping-ip[:dir .]()

#+RESULTS:
: User 'jj pinging JRR5_IP=jrr5x.local from Leo on to 16.7.2026 19.02.43 +0300
: PING jrr5x.local (192.168.1.203) 56(84) bytes of data.
: 64 bytes from jrr5x.local (192.168.1.203): icmp_seq=1 ttl=64 time=16.9 ms
: 64 bytes from jrr5x.local (192.168.1.203): icmp_seq=2 ttl=64 time=5.11 ms
: 64 bytes from jrr5x.local (192.168.1.203): icmp_seq=3 ttl=64 time=5.40 ms
: 
: --- jrr5x.local ping statistics ---
: 3 packets transmitted, 3 received, 0% packet loss, time 2002ms
: rtt min/avg/max/mdev = 5.106/9.142/16.918/5.499 ms

Expect to see  ~/home2~ mounted
#+call: mount-devs()

#+RESULTS:
: Running in /home/pi host 'jrr5x' on Thu Jul 16 19:02:56 EEST 2026
: udev on /dev type devtmpfs (rw,nosuid,relatime,size=325532k,nr_inodes=81383,mode=755)
: devpts on /dev/pts type devpts (rw,nosuid,noexec,relatime,gid=5,mode=600,ptmxmode=000)
: /dev/mmcblk0p2 on / type ext4 (rw,noatime)
: tmpfs on /dev/shm type tmpfs (rw,nosuid,nodev)
: mqueue on /dev/mqueue type mqueue (rw,nosuid,nodev,noexec,relatime)
: /dev/mmcblk0p3 on /home2 type ext4 (rw,noatime)
: /dev/mmcblk0p1 on /boot/firmware type vfat (rw,relatime,fmask=0022,dmask=0022,codepage=437,iocharset=ascii,shortname=mixed,errors=remount-ro)

: Running in /home/pi host 'jrr5' on Tue May 19 11:49:43 EEST 2026
: udev on /dev type devtmpfs (rw,nosuid,relatime,size=325992k,nr_inodes=81498,mode=755)
: devpts on /dev/pts type devpts (rw,nosuid,noexec,relatime,gid=5,mode=600,ptmxmode=000)
: /dev/mmcblk0p2 on / type ext4 (rw,noatime)
: tmpfs on /dev/shm type tmpfs (rw,nosuid,nodev)
: mqueue on /dev/mqueue type mqueue (rw,nosuid,nodev,noexec,relatime)
: /dev/mmcblk0p3 on /home2 type ext4 (rw,noatime)
: /dev/mmcblk0p1 on /boot/firmware type vfat (rw,relatime,fmask=0022,dmask=0022,codepage=437,iocharset=ascii,shortname=mixed,errors=remount-ro)

** Create user ~jrr~  with right group permissions (pi@jrr5)
:PROPERTIES:
:header-args+: :dir  /ssh:jrr5:
:END:

#+BEGIN_SRC bash :eval no-export :results output
echo "Running in $(pwd) host '$(hostname)' on $(date)"
#+END_SRC

#+RESULTS:
: Running in /home/pi host 'jrr5x' on Thu Jul 16 19:03:09 EEST 2026

#+BEGIN_SRC bash :eval no-export :results output
echo "Running in $(pwd) host '$(hostname)' on $(date)"
sudo useradd -m -d /home2/jrr jrr
#+END_SRC

#+RESULTS:
: Running in /home/pi host 'jrr5x' on Thu Jul 16 19:03:13 EEST 2026

Check that user ~jrr~ found in ~/etc/passwd~
#+BEGIN_SRC bash :eval no-export :results output
echo "Running in $(pwd) host '$(hostname)' on $(date)"
cat /etc/passwd | grep jrr
#+END_SRC

#+RESULTS:
: Running in /home/pi host 'jrr5x' on Thu Jul 16 19:03:18 EEST 2026
: jrr:x:1001:1001::/home2/jrr:/bin/bash

Check what permissions are needed to access SPI

#+BEGIN_SRC bash :eval no-export :results output
echo "Running in $(pwd) for user '$(whoami)' on host '$(hostname)' on $(date)"
ls -latr /dev/spi*
ls -latr /dev/mem*
ls -latr /dev/kmsg
cat /etc/group
ls -l /dev/input/event*
#+END_SRC

#+RESULTS:
#+begin_example
Running in /home/pi for user 'pi' on host 'jrr5x' on Fri Jul 17 12:07:42 EEST 2026
crw-rw---- 1 root spi 153, 0 Jul 17 09:40 /dev/spidev0.0
crw-rw---- 1 root spi 153, 1 Jul 17 09:40 /dev/spidev0.1
crw-r----- 1 root kmem 1, 1 Jul 17 09:40 /dev/mem
crw-r--r-- 1 root root 1, 11 Jul 17 09:40 /dev/kmsg
root:x:0:
daemon:x:1:
bin:x:2:
sys:x:3:
adm:x:4:pi,jrr
tty:x:5:
disk:x:6:
lp:x:7:
mail:x:8:
news:x:9:
uucp:x:10:
man:x:12:
proxy:x:13:
kmem:x:15:jrr
dialout:x:20:pi
fax:x:21:
voice:x:22:
cdrom:x:24:pi
floppy:x:25:
tape:x:26:
sudo:x:27:pi,jrr
audio:x:29:pi,jrr
dip:x:30:
www-data:x:33:
backup:x:34:
operator:x:37:
list:x:38:
irc:x:39:
src:x:40:
shadow:x:42:
utmp:x:43:
video:x:44:pi
sasl:x:45:
plugdev:x:46:pi
staff:x:50:
games:x:60:pi
users:x:100:pi
nogroup:x:65534:
systemd-journal:x:999:
systemd-network:x:998:
crontab:x:997:
input:x:996:pi
sgx:x:995:
clock:x:994:
kvm:x:993:
render:x:992:pi
pi:x:1000:
systemd-timesync:x:991:
messagebus:x:990:
_ssh:x:101:
netdev:x:102:pi
bluetooth:x:103:
avahi:x:104:
polkitd:x:987:
spi:x:989:pi,jrr
i2c:x:988:pi
gpio:x:986:pi,jrr
jrr:x:1001:
crw-rw---- 1 root input 13, 64 Jul 17 09:40 /dev/input/event0
crw-rw---- 1 root input 13, 65 Jul 17 09:40 /dev/input/event1
crw-rw---- 1 root input 13, 66 Jul 17 09:40 /dev/input/event2
crw-rw---- 1 root input 13, 67 Jul 17 12:02 /dev/input/event3
crw-rw---- 1 root input 13, 68 Jul 17 12:02 /dev/input/event4
crw-rw---- 1 root input 13, 69 Jul 17 12:02 /dev/input/event5
#+end_example

Add jrr to required groups
#+BEGIN_SRC bash :eval no-export :results output
echo "Running in $(pwd) for user '$(whoami)' on host '$(hostname)' on $(date)"
sudo usermod -aG spi jrr
sudo usermod -aG kmem jrr
sudo usermod -aG gpio jrr
sudo usermod -aG audio jrr
sudo usermod -aG adm jrr    # to access kernel logs
sudo usermod -aG input jrr  # to evdev devices
#+END_SRC

#+RESULTS:
: Running in /home/pi for user 'pi' on host 'jrr5x' on Fri Jul 17 12:08:06 EEST 2026

#+BEGIN_SRC bash :eval no-export :results output :dir /ssh:jrr5_user:
echo "Running in $(pwd) for user '$(whoami)' on host '$(hostname)' on $(date)"
id
#+END_SRC

#+RESULTS:
: Running in /home2/jrr for user 'jrr' on host 'jrr5x' on Fri Jul 17 12:08:33 EEST 2026
: uid=1001(jrr) gid=1001(jrr) groups=1001(jrr),4(adm),15(kmem),27(sudo),29(audio),986(gpio),989(spi),996(input)

** Add ~jrr~ to sudo
:PROPERTIES:
:header-args+: :dir  /ssh:jrr5:
:END:

#+BEGIN_SRC bash :eval no-export :results output
echo "Running in $(pwd) for user '$(whoami)' on host '$(hostname)' on $(date)"
#+END_SRC

#+RESULTS:
: Running in /home/jj/work/jrr for user 'jj' on host 'Leo' on pe 17.7.2026 08.42.29 +0300

#+BEGIN_SRC bash :eval no-export :results output
echo "Running in $(pwd) for user '$(whoami)' on host '$(hostname)' on $(date)"
sudo usermod -aG sudo jrr
#+END_SRC

#+RESULTS:
: Running in /home/pi for user 'pi' on host 'jrr5x' on Thu Jul 16 22:48:19 EEST 2026

As pi -user run
#+begin_example
sudo visudo
#+end_example

#+begin_example
jrr ALL=(ALL) NOPASSWD: ALL
#+end_example

** Config ssh  ~jrr@jrr5.local~ and short cut ~jrr5_user~
:PROPERTIES:
:header-args+: :dir  /ssh:jrr5:
:END:

*** Copy .ssh/authorized_keys from pi to jrr

Expect to find ssh key in ~/home/pi/.ssh~

#+BEGIN_SRC bash :eval no-export :results output
echo "User '$(whoami)' running in $(pwd) host '$(hostname)' on $(date)"
ls -ltr .ssh
cat .ssh/authorized_keys
#+END_SRC

#+RESULTS:
: User 'pi' running in /home/pi host 'jrr5x' on Thu Jul 16 19:07:02 EEST 2026
: total 4
: -rw------- 1 pi pi 88 Jun 18 03:27 authorized_keys
: ssh-ed25519 AAAAC3NzaC1lZDI1NTE5AAAAIHPBMIivarXwrRC5vwWRihG9T13s9/fDybxfYIfX+Kjw jj@Leo

Copy ~authorized_keys~ from ~pi~ -user to user ~jrr~ :

#+BEGIN_SRC bash :eval no-export :results output
echo "Running in $(pwd) host '$(hostname)' on $(date)"
PI_SSH=/home/pi/.ssh/authorized_keys
JRR_SSH=/home2/jrr/.ssh/authorized_keys
sudo mkdir $(dirname $JRR_SSH)
sudo cp  $PI_SSH $JRR_SSH
sudo chown -R jrr:jrr $(dirname $JRR_SSH)
sudo ls -lart /home2/jrr
#+END_SRC

#+RESULTS:
: Running in /home/pi host 'jrr5x' on Thu Jul 16 19:07:17 EEST 2026
: total 24
: -rw-r--r-- 1 jrr  jrr   807 May  9 13:58 .profile
: -rw-r--r-- 1 jrr  jrr   220 May  9 13:58 .bash_logout
: -rw-r--r-- 1 jrr  jrr  3523 Jun 18 03:20 .bashrc
: drwxr-xr-x 4 root root 4096 Jul 16 19:03 ..
: drwx------ 3 jrr  jrr  4096 Jul 16 19:07 .
: drwxr-xr-x 2 jrr  jrr  4096 Jul 16 19:07 .ssh

Test

#+call: greet-tramp[:dir /ssh:jrr@jrr5x.local:]

#+RESULTS:
: User 'jrr' from host 'jrr5x' greeting on Thu Jul 16 19:07:28 EEST 2026  (using eshell tramp)

Expected output

: User 'jrr' from host 'jrr5x' greeting on Wed Jul 15 20:24:31 EEST 2026  (using eshell tramp)

*** Create entry into ~.ssh/config~
:PROPERTIES:
:header-args+: :var  FILE="/home/jj/.ssh/config"
:END:

#+BEGIN_SRC bash :eval no-export :results output :dir .
echo "Running in $(pwd) for user '$(whoami)' on host '$(hostname)' on $(date)"
echo "FILE=$FILE"
echo JRR5_IP=${JRR5_IP}
#+END_SRC

#+RESULTS:
: Running in /home/jj/work/jrr for user 'jj' on host 'Leo' on ke 15.7.2026 20.24.47 +0300
: FILE=/home/jj/.ssh/config
: JRR5_IP=jrr5x.local

#+BEGIN_SRC bash :eval no-export :results output :dir .
echo "Running in $(pwd) for user '$(whoami)' on host '$(hostname)' on $(date)"
echo "FILE=$FILE"
cat $FILE
#+END_SRC

#+RESULTS:
#+begin_example
Running in /home/jj/work/jrr for user 'jj' on host 'Leo' on ke 15.7.2026 15.31.55 +0300
FILE=/home/jj/.ssh/config
host raspis.local
     user pi

host raspisrepo
     user pi
     IdentityFile ~/.ssh/git/id_rsa

host santtu
     user jj
     hostname 192.168.1.4
     IdentityFile ~/.ssh/id_rsa

host git-jarjuk
     user git
     hostname github.com
     IdentityFile ~/.ssh/git-jarjuk/git-jarjuk
     IdentitiesOnly yes

host gitti
     user git
     hostname github.com
     IdentityFile ~/.ssh/git/id_rsa
     IdentitiesOnly yes

host tsr
     user pi
     IdentityFile ~/.ssh/id_rsa
     hostname 192.168.100.101
     
host tcg-ai
     user hacklab
     IdentityFile ~/ssh2/id_rsa
     hostname tcg-ai.com

host pertti
     user pi
     IdentityFile ~/ssh2/id_rsa
     hostname 192.168.100.9

host frankfurt
     user ec2-user
     IdentityFile ~/.ssh/marcus-frankfurt/marcus-franfurt.pem
     hostname ec2-18-185-108-147.eu-central-1.compute.amazonaws.com

host tsr2
     user pi
     IdentityFile ~/.ssh/id_rsa
     hostname 192.168.1.99
host linuxcnc
     user linuxcnc
     IdentityFile ~/.ssh/id_rsa
     hostname 127.0.0.1
     port 3022

# host git-jukka358
#      user git
#      hostname github.com
#      IdentityFile ~/.ssh/id_jukka358

host git-hacklab-jukkaj
     user git
     hostname github.com
     IdentityFile ~/.ssh/id_jukka358

# IdentityFile /media/jj/JJ/.ssh/id_jukka358

# added from org-document org-primer.org - start
host org_primer_demo
     user pi
     IdentityFile ~/.ssh/id_rsa
     hostname 192.168.100.102
# added from org-document org-primer.org - end
# added by oracle.org - start
host oracle-docker-host
     user opc
     IdentityFile ~/.ssh/oracle-docker-host
     hostname 129.151.219.196
# added by oracle.org - end
# added by welleri.org - start
host welleri
     user pi
     IdentityFile ~/.ssh/id_rsa
     hostname 192.168.100.100
# added by welleri.org - end
# added by lavatin.org - start
host lavatin
     user pi
     IdentityFile ~/.ssh/id_rsa
     hostname 192.168.1.104
# added by lavatin.org - end
# added by raspberry.org in jrr5 - start
host jrr5
     user pi
     IdentityFile ~/.ssh/id_rsa
     hostname jrr5.local
# added by raspberry.org in jrr5 - end
# added by raspberry.org in airthings - start
host sorsa
     user pi
     IdentityFile ~/.ssh/id_rsa
     hostname /ssh:pi@sorsa.local
# added by raspberry.org in airthings - end
# added by raspberry.org in jrr  - start
host jrr5_user
     user jrr
     IdentityFile ~/.ssh/id_ed25519
     hostname jrr5x.local
# added by raspberry.org in jrr - end
#+end_example

#+call: ping-ip[:dir "."]()

#+RESULTS:
: User 'jj pinging JRR5_IP=jrr5x.local from Leo on ke 15.7.2026 20.24.56 +0300
: PING jrr5x.local (192.168.1.203) 56(84) bytes of data.
: 64 bytes from jrr5x.local (192.168.1.203): icmp_seq=1 ttl=64 time=5.53 ms
: 64 bytes from jrr5x.local (192.168.1.203): icmp_seq=2 ttl=64 time=5.29 ms
: 64 bytes from jrr5x.local (192.168.1.203): icmp_seq=3 ttl=64 time=5.39 ms
: 
: --- jrr5x.local ping statistics ---
: 3 packets transmitted, 3 received, 0% packet loss, time 2002ms
: rtt min/avg/max/mdev = 5.286/5.400/5.525/0.097 ms

#+BEGIN_SRC bash :eval no-export :results output :dir .
FILE=~/.ssh/config
START="added by raspberry.org in jrr  - start"
END="added by raspberry.org in jrr - end"

sed -i -e "/$START/,/$END/d" $FILE

cat <<HERE >> $FILE
# $START
host jrr5_user
     user jrr
     IdentityFile ~/.ssh/id_ed25519
     hostname ${JRR5_IP}
# $END
HERE
#+END_SRC

#+RESULTS:

*** Test ssh user ~jrr5_user~
#+BEGIN_SRC bash :eval no-export :results output :dir /ssh:jrr5_user:
pwd
whoami
hostname
date
groups
echo PATH=$PATH
#+END_SRC

#+RESULTS:
: /home2/jrr
: jrr
: jrr5x
: Thu Jul 16 19:07:45 EEST 2026
: jrr kmem audio gpio spi
: PATH=/bin:/usr/bin:/sbin:/usr/sbin:/usr/local/bin:/usr/local/sbin

#+BEGIN_SRC bash :eval no-export :results output :dir .
# ssh sorsa hostname
ssh jrr5_user "hostname;pwd;date"
#+END_SRC

#+RESULTS:
: jrr5x
: /home2/jrr
: Thu Jul 16 19:07:48 EEST 2026

#+call: hosti()

#+RESULTS:
: User pi in host jrr5x on Thu Jul 16 19:07:53 EEST 2026

#+call: hosti[:dir .]()

#+RESULTS:
: User jj in host Leo on to 16.7.2026 19.07.56 +0300

* Local app development
:PROPERTIES:
:header-args+: :var  SRC_DIR="src"
:END:

Check - maybe should be moved to [[file:DEVELOPMENT.org]]

** +Run Waveshare examples on PI+                                  :noexport:
*** Clone Waveshare git to  ~/ssh:pi:tmp~
:PROPERTIES:
:header-args+: :dir /ssh:jrr5:tmp
:END:

Ref: https://www.waveshare.com/wiki/2.13inch_e-Paper_HAT_Manual#Working_With_Raspberry_Pi

#+BEGIN_SRC bash :eval no-export :results output
echo "Cloning to directory $(pwd) in host '$(hostname)' on $(date)"
pwd
#+END_SRC

#+RESULTS:
: Cloning to directory /home/pi/tmp in host 'jrr5' on Wed Dec 18 08:43:27 EET 2024
: /home/pi/tmp

#+BEGIN_SRC bash :eval no-export :results output 
echo "Running in host '$(hostname)' on $(date)"
git clone https://github.com/waveshare/e-Paper.git
#+END_SRC

#+RESULTS:
: Running in host 'jrr5' on Mon Dec  9 09:59:41 EET 2024

#+BEGIN_SRC bash :eval no-export :results output
echo "Running in direcotory $(pwd) host '$(hostname)' on $(date)"
wget https://files.waveshare.com/upload/7/71/E-Paper_code.zip
#+END_SRC

#+RESULTS:
: Running in direcotory /home/pi/tmp host 'jrr5' on Mon Dec  9 10:03:33 EET 2024

#+BEGIN_SRC bash :eval no-export :results output 
echo "Running in host '$(hostname)' on $(date)"
unzip E-Paper_code.zip
#+END_SRC

#+RESULTS:
: Running in host 'jrr5' on Mon Dec  9 10:05:17 EET 2024
: Archive:  E-Paper_code.zip

*** 2in13 examples 
:PROPERTIES:
:header-args+: :dir /ssh:jrr5:tmp/e-Paper/RaspberryPi_JetsonNano/python/examples
:END:

#+call: edp-demo-ls()

#+RESULTS:
: List DEMOS='epd*2in13*' for 2.13 inch display in /home/pi/tmp/e-Paper/RaspberryPi_JetsonNano/python/examples host 'jrr5' on Wed Dec 18 08:19:41 EET 2024
: epd_2in13_V2_test.py  epd_2in13_test.py      epd_2in13bc_test.py
: epd_2in13_V3_test.py  epd_2in13b_V3_test.py  epd_2in13d_test.py
: epd_2in13_V4_test.py  epd_2in13b_V4_test.py  epd_2in13g_test.py

#+call: edp-demo(EXAMPLE="epd_2in13b_V3_test.py")

Probably the best (smooth changes)

#+call: edp-demo(EXAMPLE="epd_2in13d_test.py")

- [[file:/ssh:jrr5:/home/pi/tmp/RaspberryPi_JetsonNano/python/examples/epd_2in13d_test.py]]

#+RESULTS:
#+begin_example
Running EXAMPLE='epd_2in13d_test.py' in /home/pi/tmp/RaspberryPi_JetsonNano/python/examples host 'jrr5' on Mon Dec  9 12:32:33 EET 2024
-rw-r--r-- 1 pi pi 3146 Dec 22  2023 epd_2in13d_test.py
INFO:root:epd2in13d Demo
INFO:root:init and Clear
DEBUG:waveshare_epd.epd2in13d:e-Paper busy
DEBUG:waveshare_epd.epd2in13d:e-Paper busy release
DEBUG:waveshare_epd.epd2in13d:e-Paper busy
DEBUG:waveshare_epd.epd2in13d:e-Paper busy release
INFO:root:1.Drawing on the Horizontal image...
DEBUG:waveshare_epd.epd2in13d:Horizontal
DEBUG:waveshare_epd.epd2in13d:e-Paper busy
DEBUG:waveshare_epd.epd2in13d:e-Paper busy release
INFO:root:3.read bmp file
DEBUG:waveshare_epd.epd2in13d:Horizontal
DEBUG:waveshare_epd.epd2in13d:e-Paper busy
DEBUG:waveshare_epd.epd2in13d:e-Paper busy release
INFO:root:4.read bmp file on window
DEBUG:waveshare_epd.epd2in13d:Horizontal
DEBUG:waveshare_epd.epd2in13d:e-Paper busy
DEBUG:waveshare_epd.epd2in13d:e-Paper busy release
INFO:root:5.show time...
INFO:root:Clear...
DEBUG:waveshare_epd.epd2in13d:e-Paper busy
DEBUG:waveshare_epd.epd2in13d:e-Paper busy release
DEBUG:waveshare_epd.epd2in13d:e-Paper busy
DEBUG:waveshare_epd.epd2in13d:e-Paper busy release
INFO:root:Goto Sleep...
DEBUG:waveshare_epd.epdconfig:spi end
DEBUG:waveshare_epd.epdconfig:close 5V, Module enters 0 power consumption ...
#+end_example

Seems to work -however some flikering
#+call: edp-demo(EXAMPLE="epd_2in13bc_test.py")

#+RESULTS:
#+begin_example
Running EXAMPLE='epd_2in13bc_test.py' in /home/pi/tmp/RaspberryPi_JetsonNano/python/examples host 'jrr5' on Mon Dec  9 12:29:09 EET 2024
-rw-r--r-- 1 pi pi 3768 Dec 22  2023 epd_2in13bc_test.py
INFO:root:epd2in13bc Demo
INFO:root:init and Clear
DEBUG:waveshare_epd.epd2in13bc:e-Paper busy
DEBUG:waveshare_epd.epd2in13bc:e-Paper busy release
DEBUG:waveshare_epd.epd2in13bc:e-Paper busy
DEBUG:waveshare_epd.epd2in13bc:e-Paper busy release
INFO:root:Drawing
INFO:root:1.Drawing on the Horizontal image...
DEBUG:waveshare_epd.epd2in13bc:Horizontal
DEBUG:waveshare_epd.epd2in13bc:Horizontal
DEBUG:waveshare_epd.epd2in13bc:e-Paper busy
DEBUG:waveshare_epd.epd2in13bc:e-Paper busy release
INFO:root:2.Drawing on the Vertical image...
DEBUG:waveshare_epd.epd2in13bc:Vertical
DEBUG:waveshare_epd.epd2in13bc:Vertical
DEBUG:waveshare_epd.epd2in13bc:e-Paper busy
DEBUG:waveshare_epd.epd2in13bc:e-Paper busy release
INFO:root:3.read bmp file
DEBUG:waveshare_epd.epd2in13bc:Horizontal
DEBUG:waveshare_epd.epd2in13bc:Horizontal
DEBUG:waveshare_epd.epd2in13bc:e-Paper busy
DEBUG:waveshare_epd.epd2in13bc:e-Paper busy release
INFO:root:4.read bmp file on window
DEBUG:waveshare_epd.epd2in13bc:Horizontal
DEBUG:waveshare_epd.epd2in13bc:Horizontal
DEBUG:waveshare_epd.epd2in13bc:e-Paper busy
DEBUG:waveshare_epd.epd2in13bc:e-Paper busy release
INFO:root:Clear...
DEBUG:waveshare_epd.epd2in13bc:e-Paper busy
DEBUG:waveshare_epd.epd2in13bc:e-Paper busy release
DEBUG:waveshare_epd.epd2in13bc:e-Paper busy
DEBUG:waveshare_epd.epd2in13bc:e-Paper busy release
INFO:root:Goto Sleep...
DEBUG:waveshare_epd.epd2in13bc:e-Paper busy
DEBUG:waveshare_epd.epd2in13bc:e-Paper busy release
DEBUG:waveshare_epd.epdconfig:spi end
DEBUG:waveshare_epd.epdconfig:close 5V, Module enters 0 power consumption ...
#+end_example

Hangs
#+call: edp-demo(EXAMPLE="epd_2in13_test.py")

#+RESULTS:
: Running EXAMPLE='epd_2in13b_test.py' in /home/pi/tmp/RaspberryPi_JetsonNano/python/examples host 'jrr5' on Mon Dec  9 12:31:38 EET 2024
: python3: can't open file '/home/pi/tmp/RaspberryPi_JetsonNano/python/examples/epd_2in13b_test.py': [Errno 2] No such file or directory

*** 2in7 -examples 
:PROPERTIES:
:header-args+: :dir /ssh:jrr5:tmp/e-Paper/RaspberryPi_JetsonNano/python/examples
:END:

#+call: edp-demo-ls(DEMOS="epd*2in7*")

#+RESULTS:
: List DEMOS='epd*2in7*' for Waveshare ePaper display in /home/pi/tmp/e-Paper/RaspberryPi_JetsonNano/python/examples host 'jrr5' on Mon Dec 30 13:22:04 EET 2024
: epd_2in7_V2_test.py  epd_2in7_test.py  epd_2in7b_V2_test.py  epd_2in7b_test.py

#+call: edp-demo(EXAMPLE="epd_2in7_V2_test.py")

#+RESULTS:
#+begin_example
Running EXAMPLE='epd_2in7_V2_test.py' in /home/pi/tmp/e-Paper/RaspberryPi_JetsonNano/python/examples host 'jrr5' on Mon Dec 30 13:23:18 EET 2024
-rw-r--r-- 1 pi pi 5987 Dec  9 10:01 epd_2in7_V2_test.py
INFO:root:epd2in7 Demo
INFO:root:init and Clear
DEBUG:waveshare_epd.epd2in7_V2:e-Paper busy
DEBUG:waveshare_epd.epd2in7_V2:e-Paper busy release
DEBUG:waveshare_epd.epd2in7_V2:e-Paper busy
DEBUG:waveshare_epd.epd2in7_V2:e-Paper busy release
DEBUG:waveshare_epd.epd2in7_V2:e-Paper busy
DEBUG:waveshare_epd.epd2in7_V2:e-Paper busy release
INFO:root:Quick refresh demo
DEBUG:waveshare_epd.epd2in7_V2:e-Paper busy
DEBUG:waveshare_epd.epd2in7_V2:e-Paper busy release
DEBUG:waveshare_epd.epd2in7_V2:e-Paper busy
DEBUG:waveshare_epd.epd2in7_V2:e-Paper busy release
DEBUG:waveshare_epd.epd2in7_V2:e-Paper busy
DEBUG:waveshare_epd.epd2in7_V2:e-Paper busy release
DEBUG:waveshare_epd.epd2in7_V2:e-Paper busy
DEBUG:waveshare_epd.epd2in7_V2:e-Paper busy release
DEBUG:waveshare_epd.epd2in7_V2:e-Paper busy
DEBUG:waveshare_epd.epd2in7_V2:e-Paper busy release
INFO:root:1.Drawing on the Vertical image...
DEBUG:waveshare_epd.epd2in7_V2:Vertical
DEBUG:waveshare_epd.epd2in7_V2:e-Paper busy
DEBUG:waveshare_epd.epd2in7_V2:e-Paper busy release
INFO:root:2.read bmp file
DEBUG:waveshare_epd.epd2in7_V2:Vertical
DEBUG:waveshare_epd.epd2in7_V2:e-Paper busy
DEBUG:waveshare_epd.epd2in7_V2:e-Paper busy release
INFO:root:Normal refresh demo
DEBUG:waveshare_epd.epd2in7_V2:e-Paper busy
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
DEBUG:waveshare_epd.epd2in7_V2:e-Paper busy
DEBUG:waveshare_epd.epd2in7_V2:e-Paper busy release
INFO:root:Goto Sleep...
DEBUG:waveshare_epd.epdconfig:spi end
DEBUG:waveshare_epd.epdconfig:close 5V, Module enters 0 power consumption ...
#+end_example

#+begin_example
Running EXAMPLE='epd_2in7_V2_test.py' in /home/pi/tmp/e-Paper/RaspberryPi_JetsonNano/python/examples host 'jrr5' on Wed Dec 18 08:27:12 EET 2024
-rw-r--r-- 1 pi pi 5987 Dec  9 10:01 epd_2in7_V2_test.py
INFO:root:epd2in7 Demo
INFO:root:init and Clear
DEBUG:waveshare_epd.epd2in7_V2:e-Paper busy
DEBUG:waveshare_epd.epd2in7_V2:e-Paper busy release
DEBUG:waveshare_epd.epd2in7_V2:e-Paper busy
DEBUG:waveshare_epd.epd2in7_V2:e-Paper busy release
DEBUG:waveshare_epd.epd2in7_V2:e-Paper busy
DEBUG:waveshare_epd.epd2in7_V2:e-Paper busy release
INFO:root:Quick refresh demo
DEBUG:waveshare_epd.epd2in7_V2:e-Paper busy
DEBUG:waveshare_epd.epd2in7_V2:e-Paper busy release
DEBUG:waveshare_epd.epd2in7_V2:e-Paper busy
DEBUG:waveshare_epd.epd2in7_V2:e-Paper busy release
DEBUG:waveshare_epd.epd2in7_V2:e-Paper busy
DEBUG:waveshare_epd.epd2in7_V2:e-Paper busy release
DEBUG:waveshare_epd.epd2in7_V2:e-Paper busy
DEBUG:waveshare_epd.epd2in7_V2:e-Paper busy release
DEBUG:waveshare_epd.epd2in7_V2:e-Paper busy
DEBUG:waveshare_epd.epd2in7_V2:e-Paper busy release
INFO:root:1.Drawing on the Vertical image...
DEBUG:waveshare_epd.epd2in7_V2:Vertical
DEBUG:waveshare_epd.epd2in7_V2:e-Paper busy
DEBUG:waveshare_epd.epd2in7_V2:e-Paper busy release
INFO:root:2.read bmp file
DEBUG:waveshare_epd.epd2in7_V2:Vertical
DEBUG:waveshare_epd.epd2in7_V2:e-Paper busy
DEBUG:waveshare_epd.epd2in7_V2:e-Paper busy release
INFO:root:Normal refresh demo
DEBUG:waveshare_epd.epd2in7_V2:e-Paper busy
DEBUG:waveshare_epd.epd2in7_V2:e-Paper busy release
DEBUG:waveshare_epd.epd2in7_V2:e-Paper busy
DEBUG:waveshare_epd.epd2in7_V2:e-Paper busy release
INFO:root:3.read bmp file on window
DEBUG:waveshare_epd.epd2in7_V2:Horizontal
DEBUG:waveshare_epd.epd2in7_V2:e-Paper busy
DEBUG:waveshare_epd.epd2in7_V2:e-Paper busy release
INFO:root:4.Drawing on the Horizontal image...
DEBUG:waveshare_epd.epd2in7_V2:Horizontal
DEBUG:waveshare_epd.epd2in7_V2:e-Paper busy
DEBUG:waveshare_epd.epd2in7_V2:e-Paper busy release
INFO:root:5.show time
DEBUG:waveshare_epd.epd2in7_V2:e-Paper busy
DEBUG:waveshare_epd.epd2in7_V2:e-Paper busy release
DEBUG:waveshare_epd.epd2in7_V2:e-Paper busy
DEBUG:waveshare_epd.epd2in7_V2:e-Paper busy release
DEBUG:waveshare_epd.epd2in7_V2:Horizontal
DEBUG:waveshare_epd.epd2in7_V2:e-Paper busy
DEBUG:waveshare_epd.epd2in7_V2:e-Paper busy release
DEBUG:waveshare_epd.epd2in7_V2:Horizontal
DEBUG:waveshare_epd.epd2in7_V2:e-Paper busy
DEBUG:waveshare_epd.epd2in7_V2:e-Paper busy release
DEBUG:waveshare_epd.epd2in7_V2:Horizontal
DEBUG:waveshare_epd.epd2in7_V2:e-Paper busy
DEBUG:waveshare_epd.epd2in7_V2:e-Paper busy release
DEBUG:waveshare_epd.epd2in7_V2:Horizontal
DEBUG:waveshare_epd.epd2in7_V2:e-Paper busy
DEBUG:waveshare_epd.epd2in7_V2:e-Paper busy release
DEBUG:waveshare_epd.epd2in7_V2:Horizontal
DEBUG:waveshare_epd.epd2in7_V2:e-Paper busy
DEBUG:waveshare_epd.epd2in7_V2:e-Paper busy release
DEBUG:waveshare_epd.epd2in7_V2:Horizontal
DEBUG:waveshare_epd.epd2in7_V2:e-Paper busy
DEBUG:waveshare_epd.epd2in7_V2:e-Paper busy release
DEBUG:waveshare_epd.epd2in7_V2:Horizontal
DEBUG:waveshare_epd.epd2in7_V2:e-Paper busy
DEBUG:waveshare_epd.epd2in7_V2:e-Paper busy release
DEBUG:waveshare_epd.epd2in7_V2:Horizontal
DEBUG:waveshare_epd.epd2in7_V2:e-Paper busy
DEBUG:waveshare_epd.epd2in7_V2:e-Paper busy release
DEBUG:waveshare_epd.epd2in7_V2:Horizontal
DEBUG:waveshare_epd.epd2in7_V2:e-Paper busy
DEBUG:waveshare_epd.epd2in7_V2:e-Paper busy release
DEBUG:waveshare_epd.epd2in7_V2:Horizontal
DEBUG:waveshare_epd.epd2in7_V2:e-Paper busy
DEBUG:waveshare_epd.epd2in7_V2:e-Paper busy release
INFO:root:4Gray display--------------------------------
DEBUG:waveshare_epd.epd2in7_V2:e-Paper busy
DEBUG:waveshare_epd.epd2in7_V2:e-Paper busy release
DEBUG:waveshare_epd.epd2in7_V2:e-Paper busy
DEBUG:waveshare_epd.epd2in7_V2:e-Paper busy release
DEBUG:waveshare_epd.epd2in7_V2:Vertical
DEBUG:waveshare_epd.epd2in7_V2:e-Paper busy
DEBUG:waveshare_epd.epd2in7_V2:e-Paper busy release
DEBUG:waveshare_epd.epd2in7_V2:Vertical
DEBUG:waveshare_epd.epd2in7_V2:e-Paper busy
DEBUG:waveshare_epd.epd2in7_V2:e-Paper busy release
INFO:root:Clear...
DEBUG:waveshare_epd.epd2in7_V2:e-Paper busy
DEBUG:waveshare_epd.epd2in7_V2:e-Paper busy release
DEBUG:waveshare_epd.epd2in7_V2:e-Paper busy
DEBUG:waveshare_epd.epd2in7_V2:e-Paper busy release
DEBUG:waveshare_epd.epd2in7_V2:e-Paper busy
DEBUG:waveshare_epd.epd2in7_V2:e-Paper busy release
INFO:root:Goto Sleep...
DEBUG:waveshare_epd.epdconfig:spi end
DEBUG:waveshare_epd.epdconfig:close 5V, Module enters 0 power consumption ...
#+end_example

** +Copy epaper demo-code to ~tmp/RaspberryPi_JetsonNano~ from to ~src~+
:PROPERTIES:
:header-args+: :var  DEMO_DIR_OLD="tmp/RaspberryPi_JetsonNano"
:header-args+: :var  DEMO_DIR="tmp/e-Paper/RaspberryPi_JetsonNano"
:END:

*** Init directories

#+BEGIN_SRC bash :eval no-export :results output
echo "Running in host '$(hostname)' on $(date)"
echo "DEMO_DIR_DIR=$DEMO_DIR"
echo "SRC_DIR=$SRC_DIR"
#+END_SRC

#+RESULTS:
: Running in host 'eero' on ma 9.12.2024 10.13.09 +0200
: DEMO_DIR_DIR=tmp/RaspberryPi_JetsonNano
: SRC_DIR=src

Init local directories

*Warning deletes directories*
#+BEGIN_SRC bash :eval no-export :results output
echo "Running in host '$(hostname)' on $(date)"
rm -rf src/lib
rm -rf src/pic
rm -rf src/examples
#+END_SRC

#+RESULTS:
: Running in host 'eero' on ma 9.12.2024 12.50.53 +0200

#+call: create-dir[:dir .](DIR="src/lib")

#+RESULTS:
: Create DIR=src/lib in host='eero' on ma 9.12.2024 12.51.10 +0200
: Directory src/lib created

#+call: create-dir[:dir .](DIR="src/lib/waveshare_epd")

#+RESULTS:
: Create DIR=src/lib/waveshare_epd in host='eero' on ma 9.12.2024 12.51.12 +0200
: Directory src/lib/waveshare_epd created

#+call: create-dir[:dir .](DIR="src/pic")

#+RESULTS:
: Create DIR=src/pic in host='eero' on ma 9.12.2024 12.51.14 +0200
: Directory src/pic created

#+call: create-dir[:dir .](DIR="src/examples")

#+RESULTS:
: Create DIR=src/examples in host='eero' on ma 9.12.2024 12.51.16 +0200
: Directory src/examples created

*** Copy files  ~DEMO_DIR~  to ~SRC_DIR~

#+BEGIN_SRC bash :eval no-export :results output
echo "Running in host '$(hostname)' on $(date)"
echo "DEMO_DIR_DIR=$DEMO_DIR"
echo "SRC_DIR=$SRC_DIR"
#+END_SRC

#+RESULTS:
: Running in host 'eero' on ke 18.12.2024 10.52.33 +0200
: DEMO_DIR_DIR=tmp/e-Paper/RaspberryPi_JetsonNano
: SRC_DIR=src

#+BEGIN_SRC bash :eval no-export :results output
echo "Running in host '$(hostname)' on $(date)"
ls -ltr $DEMO_DIR/python/examples/epd_2in13d_test.py
ls -ltr $DEMO_DIR/python/examples/epd_2in7_V2_test.py
#+END_SRC

#+RESULTS:
: Running in host 'eero' on ke 18.12.2024 10.52.42 +0200
: -rw-rw-r-- 1 jj jj 3056 joulu   9 09:55 tmp/e-Paper/RaspberryPi_JetsonNano/python/examples/epd_2in13d_test.py
: -rw-rw-r-- 1 jj jj 5987 joulu   9 09:55 tmp/e-Paper/RaspberryPi_JetsonNano/python/examples/epd_2in7_V2_test.py

: Running in host 'eero' on ke 18.12.2024 08.31.53 +0200
: -rw-rw-r-- 1 jj jj 3146 joulu  22  2023 tmp/RaspberryPi_JetsonNano/python/examples/epd_2in13d_test.py
: -rw-rw-r-- 1 jj jj 6146 joulu  22  2023 tmp/RaspberryPi_JetsonNano/python/examples/epd_2in7_V2_test.py

Copy pics files
#+BEGIN_SRC bash :eval no-export :results output
echo "Running in host '$(hostname)' on $(date)"
cp -R $DEMO_DIR/python/pic/100x100.bmp $SRC_DIR/pic
cp -R $DEMO_DIR/python/pic/2in13*.bmp $SRC_DIR/pic
cp -R $DEMO_DIR/python/pic/2in7*.bmp $SRC_DIR/pic
cp -R $DEMO_DIR/python/pic/Font.ttc $SRC_DIR/pic
cp -R $DEMO_DIR/python/lib/waveshare_epd/epdconfig.py $SRC_DIR/lib/waveshare_epd
#+END_SRC

#+RESULTS:
: Running in host 'eero' on to 19.12.2024 10.17.39 +0200

#+name: edp-copy-ls
#+BEGIN_SRC bash :eval no-export :results output :var DRIVER="epd2in13d" EXAMPLE="epd_2in13d_test"
echo "Running in host '$(hostname)' on $(date)"
echo DRIVER=$DRIVER
echo EXAMPLE=$EXAMPLE
ls -ltr $DEMO_DIR/python/lib/waveshare_epd/$DRIVER.py
ls -ltr $DEMO_DIR/python/examples/$EXAMPLE.py 
#+END_SRC

#+RESULTS: edp-copy-ls
: Running in host 'eero' on ke 18.12.2024 10.53.08 +0200
: DRIVER=epd2in13d
: EXAMPLE=epd_2in13d_test
: -rw-rw-r-- 1 jj jj 12269 joulu   9 09:55 tmp/e-Paper/RaspberryPi_JetsonNano/python/lib/waveshare_epd/epd2in13d.py
: -rw-rw-r-- 1 jj jj 3056 joulu   9 09:55 tmp/e-Paper/RaspberryPi_JetsonNano/python/examples/epd_2in13d_test.py

#+name: edp-copy
#+BEGIN_SRC bash :eval no-export :results output :var DRIVER="epd2in13d" EXAMPLE="epd_2in13d_test"
echo "Running in $(pwd) host '$(hostname)' on $(date)"
echo DRIVER=$DRIVER
echo EXAMPLE=$EXAMPLE
echo DEMO_DIR=$DEMO_DIR
echo SRC_DIR=$SRC_DIR
set -x
cp $DEMO_DIR/python/lib/waveshare_epd/$DRIVER.py $SRC_DIR/lib/waveshare_epd
cp $DEMO_DIR/python/examples/$EXAMPLE.py $SRC_DIR/examples/
#+END_SRC

#+RESULTS: edp-copy
: Running in host 'eero' on ke 18.12.2024 10.53.14 +0200
: DRIVER=epd2in13d
: EXAMPLE=epd_2in13d_test

#+call: edp-copy-ls(DRIVER="epd2in7_V2", EXAMPLE="epd_2in7_V2_test")

#+RESULTS:
: Running in host 'eero' on ke 18.12.2024 11.37.00 +0200
: DRIVER=epd2in7_V2
: EXAMPLE=epd_2in7_V2_test
: -rw-rw-r-- 1 jj jj 18647 joulu   9 09:55 tmp/e-Paper/RaspberryPi_JetsonNano/python/lib/waveshare_epd/epd2in7_V2.py
: -rw-rw-r-- 1 jj jj 5987 joulu   9 09:55 tmp/e-Paper/RaspberryPi_JetsonNano/python/examples/epd_2in7_V2_test.py

#+call: edp-copy(DRIVER="epd2in7_V2", EXAMPLE="epd_2in7_V2_test")

#+RESULTS:
: Running in /home/jj/work/järviradio-radio host 'eero' on ke 18.12.2024 11.37.10 +0200
: DRIVER=epd2in7_V2
: EXAMPLE=epd_2in7_V2_test
: DEMO_DIR=tmp/e-Paper/RaspberryPi_JetsonNano
: SRC_DIR=src

#+BEGIN_SRC bash :eval no-export :results output
echo "Running in host '$(hostname)' on $(date)"
echo "SRC_DIR=$var"
ls -ltr $SRC_DIR/examples
ls -ltr $SRC_DIR/lib/waveshare_epd
ls -ltr $SRC_DIR/pic
#+END_SRC

#+RESULTS:
#+begin_example
Running in host 'eero' on ke 18.12.2024 10.53.35 +0200
SRC_DIR=
total 20
-rw-rw-r-- 1 jj jj 3761 joulu   9 09:55 epd_2in13b_V3_test.py
-rw-rw-r-- 1 jj jj 3768 joulu   9 09:55 epd_2in13bc_test.py
-rw-rw-r-- 1 jj jj 3056 joulu  18 10:53 epd_2in13d_test.py
-rw-rw-r-- 1 jj jj 5987 joulu  18 10:53 epd_2in7_V2_test.py
total 23
-rw-rw-r-- 1 jj jj  9973 joulu  18 10:53 epdconfig.py
-rw-rw-r-- 1 jj jj 12269 joulu  18 10:53 epd2in13d.py
-rw-rw-r-- 1 jj jj  6624 joulu  18 10:53 epd2in7b_V2.py
total 3599
-rw-rw-r-- 1 jj jj    1662 joulu  18 10:53 100x100.bmp
-rw-rw-r-- 1 jj jj    3966 joulu  18 10:53 2in13-v2.bmp
-rw-rw-r-- 1 jj jj   92054 joulu  18 10:53 2in13g.bmp
-rw-rw-r-- 1 jj jj    2974 joulu  18 10:53 2in13d.bmp
-rw-rw-r-- 1 jj jj    2974 joulu  18 10:53 2in13d_1.bmp
-rw-rw-r-- 1 jj jj    3966 joulu  18 10:53 2in13b_V4r.bmp
-rw-rw-r-- 1 jj jj    3966 joulu  18 10:53 2in13b_V4b.bmp
-rw-rw-r-- 1 jj jj    4062 joulu  18 10:53 2in13.bmp
-rw-rw-r-- 1 jj jj    2974 joulu  18 10:53 2in13bc-ry.bmp
-rw-rw-r-- 1 jj jj    2974 joulu  18 10:53 2in13bc-b.bmp
-rw-rw-r-- 1 jj jj    2976 joulu  18 10:53 2in13_b1.bmp
-rw-rw-r-- 1 jj jj    3966 joulu  18 10:53 2in13_2.bmp
-rw-rw-r-- 1 jj jj    3966 joulu  18 10:53 2in13_1.bmp
-rw-rw-r-- 1 jj jj    2976 joulu  18 10:53 2in13_y1.bmp
-rw-rw-r-- 1 jj jj 5177387 joulu  18 10:53 Font.ttc
#+end_example

** Create sprite file  ~src/resources/icon-sprite.png~

#+BEGIN_SRC bash :eval no-export :results output
echo "Running in $(pwd) host '$(hostname)' on $(date)"
echo "SRC_DIR=$SRC_DIR"
#+END_SRC

#+RESULTS:
: Running in /home/jj/work/järviradio-radio host 'eero' on su 29.12.2024 18.59.46 +0200
: SRC_DIR=src

Ensure that dowload directory ~resources/sprite~ exists [[file:resources/sprite]]
#+call: create-dir(DIR="resources/sprite")

Download png files from https://www.pngwing.com/en/free-png-hntlj/download

Create application resources directory
#+call: create-dir(DIR="src/resources")

[[file:src/resources]]

#+RESULTS:
: Create DIR=src/resources in host='jrr5' on Sun Dec 29 18:59:54 EET 2024
: Directory src/resources already exists

Convert svg-files in ~resources~ to png files ~resources/sprite~

Converted manually *no used*
#+BEGIN_SRC bash :eval no :results output
echo "Running in $(pwd) host '$(hostname)' on $(date)"
for svg in $(ls -1 resources/*.svg); do
    png_dir=$(dirname $svg)/sprite
    svg_base=$(basename -- $svg)
    png_file="${svg_base%.*}".png
    echo "svg=$svg, png_dir=$png_dir, png_file=$png_file"
    # https://stackoverflow.com/questions/6589358/convert-svg-to-png-in-python/6599172#6599172
    inkscape $svg  --export-filename=$png_dir/$png_file
done    

#+END_SRC

#+RESULTS:
: Running in /home/jj/work/jarviradio-radio host 'eero' on to 13.3.2025 12.29.31 +0200
: svg=resources/07-keyboard-ok.svg, png_dir=resources/sprite, png_file=07-keyboard-ok.png
: svg=resources/08-keyboard-nok.svg, png_dir=resources/sprite, png_file=08-keyboard-nok.png
: svg=resources/09-keyboard-ok.svg, png_dir=resources/sprite, png_file=09-keyboard-ok.png

Help for python script ~src/spriter.py~ 
#+BEGIN_SRC bash :eval no-export :results output
echo "Running in host '$(hostname)' on $(date)"
python3 src/spriter.py --help
#+END_SRC

#+RESULTS:
#+begin_example
Running in host 'eero' on to 13.3.2025 12.01.55 +0200
usage: spriter.py [-h] [-i INPUT_DIRECTORY] [-o OUTPUT_FILE]
                  [--icon-width ICON_WIDTH] [--icon-height ICON_HEIGHT] [-v]

Create icon sprite

options:
  -h, --help            show this help message and exit
  -i INPUT_DIRECTORY, --input-directory INPUT_DIRECTORY
                        input directory
  -o OUTPUT_FILE, --output-file OUTPUT_FILE
                        Output file
  --icon-width ICON_WIDTH
                        Size of icon element in sprite
  --icon-height ICON_HEIGHT
                        Size of icon element in sprite
  -v, --verbose
#+end_example

Content of sprite input directory [[file:resources/sprite]]

#+BEGIN_SRC bash :eval no-export :results output
echo "Running in $(pwd) host '$(hostname)' on $(date)"
ls -ltr resources/sprite
#+END_SRC

#+RESULTS:
#+begin_example
Running in /home/jj/work/jarviradio-radio host 'eero' on su 16.3.2025 14.48.16 +0200
total 233
-rw-rw-r-- 1 jj jj 159363 joulu  28 11:15 02-net-nok.png
-rw-rw-r-- 1 jj jj   5121 joulu  28 11:15 08-keyboard-nok.png
-rw-rw-r-- 1 jj jj   5121 joulu  28 11:15 03-stream-play.png
-rw-rw-r-- 1 jj jj   4680 joulu  28 11:16 04-stream-paused.png
-rw-rw-r-- 1 jj jj  23492 joulu  28 16:39 01-net-ok.png
-rw-rw-r-- 1 jj jj    555 tammi  17 21:57 05-dot.png
-rw-rw-r-- 1 jj jj    206 tammi  17 22:52 06-dash.png
-rw------- 1 jj jj   1460 maalis 13 13:12 07-keyboard-ok.png
-rw------- 1 jj jj    265 maalis 13 13:14 09-keyboard-nok.png
#+end_example

Create icon sprite file  ~src/resources/icon-sprite.png~
#+BEGIN_SRC bash :eval no-export :results output
echo "Running in host '$(hostname)' on $(date)"
python3 src/spriter.py -o src/resources/icon-sprite.png
#+END_SRC

#+RESULTS:
: Running in host 'eero' on ti 27.5.2025 08.23.18 +0300
: parser.input_directory='/home/jj/work/jarviradio-radio/src/../resources/sprite'

Icon sprite file created 

#+BEGIN_SRC bash :eval no-export :results output
echo "Running in host $(pwd) '$(hostname)' on $(date)"
ls -ltr src/resources
#+END_SRC

#+RESULTS:
: Running in host /home/jj/work/järviradio-radio 'eero' on pe 17.1.2025 21.53.53 +0200
: total 5
: -rw-rw-r-- 1 jj jj 441 joulu  29 19:00 icon-sprite.png

** Clone driver Python_ILI9486  for 3.5" TFT display
 
https://github.com/SirLefti/Python_ILI9486

#+BEGIN_SRC bash :eval no-export :results output
echo "Running in $(pwd) host '$(hostname)' on $(date)"
cd $SRC_DIR
git clone https://github.com/SirLefti/Python_ILI9486
#+END_SRC

#+RESULTS:
: Running in /home/jj/work/järviradio-radio host 'eero' on ti 7.1.2025 13.16.43 +0200

#+BEGIN_SRC bash :eval no-export :results output
echo "Running in $(pwd) host '$(hostname)' on $(date)"
ls -latr src/Python_ILI9486
#+END_SRC

#+RESULTS:
#+begin_example
Running in /home/jj/work/järviradio-radio host 'eero' on ti 7.1.2025 13.17.17 +0200
total 131
drwxrwxr-x 9 jj jj    42 tammi   7 13:16 ..
-rw-rw-r-- 1 jj jj  1598 tammi   7 13:16 README.md
-rw-rw-r-- 1 jj jj  1136 tammi   7 13:16 LICENSE
-rw-rw-r-- 1 jj jj 11381 tammi   7 13:16 ILI9486.py
-rw-rw-r-- 1 jj jj    80 tammi   7 13:16 .gitignore
-rw-rw-r-- 1 jj jj    86 tammi   7 13:16 config.py
-rw-rw-r-- 1 jj jj 75673 tammi   7 13:16 sample.png
-rw-rw-r-- 1 jj jj    31 tammi   7 13:16 requirements.txt
-rw-rw-r-- 1 jj jj  2168 tammi   7 13:16 image.py
drwxrwxr-x 8 jj jj    13 tammi   7 13:16 .git
drwxrwxr-x 3 jj jj    11 tammi   7 13:16 .
#+end_example

Remove git directory from ~Python_ILI9486~ clone 

#+BEGIN_SRC bash :eval no-export :results output
echo "Running in $(pwd) host '$(hostname)' on $(date)"
rm -rf src/Python_ILI9486/.git
#+END_SRC

#+RESULTS:
: Running in /home/jj/work/järviradio-radio host 'eero' on ti 7.1.2025 13.17.58 +0200

** Convert streamer icons from ~runner/icons~ to ~cnf/icons~

Ensure that directory ~cnf/icons~ exists
#+call: create-dir(DIR="cnf/icons")

#+RESULTS:
: Create DIR=cnf/icons in host='jrr5' on Mon Mar 17 10:15:29 EET 2025
: Directory cnf/icons created

List streamer icons input files in ~runner/icons~
#+BEGIN_SRC bash :eval no-export :results output
echo "Running in $(pwd) host '$(hostname)' on $(date)"
ls -ltr runner/icons
#+END_SRC

#+RESULTS:
#+begin_example
Running in /home/jj/work/jarviradio-radio host 'eero' on ma 17.3.2025 10.15.31 +0200
total 226
-rw-r--r-- 1 jj jj  8584 maalis 16  2020 yle-radio-1.png
-rw-r--r-- 1 jj jj  7501 maalis 16  2020 radio-suomi.png
-rw-r--r-- 1 jj jj  6805 maalis 16  2020 yle-puhe.png
-rw-r--r-- 1 jj jj 30975 maalis 16  2020 järviradio.png
-rw-r--r-- 1 jj jj  9873 maalis 16  2020 jrr.png
-rw-r--r-- 1 jj jj 11144 maalis 16  2020 jrr-stop.png
-rw-rw-r-- 1 jj jj 33672 maalis 17  2020 classic.png
-rw-rw-r-- 1 jj jj 25408 maalis 17  2020 järviratio.png
-rw------- 1 jj jj  8251 touko   8  2020 jrr-help.png
-rw-rw-r-- 1 jj jj 29271 maalis 26  2023 rondo.png
-rw-rw-r-- 1 jj jj  2123 joulu  13 12:50 yle-1.jpeg
-rw-rw-r-- 1 jj jj  3236 tammi  13 14:31 YLE-1.png
-rw-rw-r-- 1 jj jj  2680 tammi  13 14:33 YLE-SUOMI.png
-rw-rw-r-- 1 jj jj  7351 tammi  13 14:35 JÄRVIRADIO.png
#+end_example

Convert (=resize) icon files in directory ~runner/icons~ to directory ~.icons/v2~

#+BEGIN_SRC bash :eval no-export :results output
echo "Running in $(pwd) host '$(hostname)' on $(date)"
# python3 jrr.py -v convert --icons-from runner/icons --icons-to  .icons/v2 2>&1; true
# python3 jrr.py -v convert --icons-from runner/icons --icons-to  .icons/v2 --yes
python3 jrr.py -v convert --icons-from runner/icons --icons-to  cnf/icons --yes 2>&1; true
#+END_SRC

#+RESULTS:
#+begin_example
Running in /home/jj/work/jarviradio-radio host 'eero' on ma 17.3.2025 12.00.22 +0200
2025-03-17:12:00:22,885 INFO     [jrr.py:125] logging.level: 0
2025-03-17:12:00:22,885 INFO     [jrr_converter.py:86] image_dir: runner/icons
2025-03-17:12:00:22,885 INFO     [jrr_converter.py:91] icon_dir: cnf/icons
2025-03-17:12:00:22,885 INFO     [jrr_converter.py:95] image_dir: runner/icons
2025-03-17:12:00:22,885 INFO     [jrr_converter.py:99] image_path: runner/icons/yle-radio-1.png
2025-03-17:12:00:22,893 INFO     [jrr_converter.py:99] image_path: runner/icons/JÄRVIRADIO.png
2025-03-17:12:00:22,895 INFO     [jrr_converter.py:99] image_path: runner/icons/jrr-help.png
2025-03-17:12:00:22,897 INFO     [jrr_converter.py:99] image_path: runner/icons/radio-suomi.png
2025-03-17:12:00:22,900 INFO     [jrr_converter.py:99] image_path: runner/icons/rondo.png
2025-03-17:12:00:22,904 INFO     [jrr_converter.py:99] image_path: runner/icons/classic.png
2025-03-17:12:00:22,911 INFO     [jrr_converter.py:99] image_path: runner/icons/jrr.png
2025-03-17:12:00:22,912 INFO     [jrr_converter.py:99] image_path: runner/icons/yle-puhe.png
2025-03-17:12:00:22,917 INFO     [jrr_converter.py:99] image_path: runner/icons/järviratio.png
2025-03-17:12:00:22,920 INFO     [jrr_converter.py:99] image_path: runner/icons/yle-1.jpeg
2025-03-17:12:00:22,922 INFO     [jrr_converter.py:99] image_path: runner/icons/YLE-1.png
2025-03-17:12:00:22,923 INFO     [jrr_converter.py:99] image_path: runner/icons/jrr-stop.png
2025-03-17:12:00:22,925 INFO     [jrr_converter.py:99] image_path: runner/icons/YLE-SUOMI.png
2025-03-17:12:00:22,926 INFO     [jrr_converter.py:99] image_path: runner/icons/järviradio.png
cnf/icons/yle-radio-1.png - created
cnf/icons/JÄRVIRADIO.png - created
cnf/icons/jrr-help.png - created
cnf/icons/radio-suomi.png - created
cnf/icons/rondo.png - created
cnf/icons/classic.png - created
cnf/icons/jrr.png - created
cnf/icons/yle-puhe.png - created
cnf/icons/järviratio.png - created
cnf/icons/yle-1.jpeg - created
cnf/icons/YLE-1.png - created
cnf/icons/jrr-stop.png - created
cnf/icons/YLE-SUOMI.png - created
cnf/icons/järviradio.png - created
#+end_example

* App  install and config to ROOT_DIR -target
:PROPERTIES:
:header-args+: :var  ROOT_DIR="/ssh:jrr5_user:"
:header-args+: :dir /ssh:jrr5_user:
:END:

** Create directories for user ~jrr~

#+BEGIN_SRC bash :eval no-export :results output
echo "Running in $(pwd) for user '$(whoami)' on host '$(hostname)' on $(date)"
#+END_SRC

#+RESULTS:
: Running in /home2/jrr for user 'jrr' on host 'jrr5x' on Thu Jul 16 19:08:05 EEST 2026

Directory where järviradioradio v1 icons exitss
#+call: create-dir(DIR=".icons")

#+RESULTS:
: Create DIR=.icons in /home2/jrr for user 'jrr' on host='jrr5x' on Thu Jul 16 19:08:10 EEST 2026
: Directory .icons created

Directory where järviradioradio v2 thumbs are found
#+call: create-dir(DIR=".icons/v2")

#+RESULTS:
: Create DIR=.icons/v2 in /home2/jrr for user 'jrr' on host='jrr5x' on Thu Jul 16 19:08:14 EEST 2026
: Directory .icons/v2 created

#+call: create-dir(DIR="tmp")

#+RESULTS:
: Create DIR=tmp in /home2/jrr for user 'jrr' on host='jrr5x' on Thu Jul 16 19:08:18 EEST 2026
: Directory tmp created

#+call: create-dir(DIR="bin")

#+RESULTS:
: Create DIR=bin in /home2/jrr for user 'jrr' on host='jrr5x' on Thu Jul 16 19:08:22 EEST 2026
: Directory bin created

#+call: create-dir(DIR="jrr")

#+RESULTS:
: Create DIR=jrr in /home2/jrr for user 'jrr' on host='jrr5x' on Thu Jul 16 19:08:27 EEST 2026
: Directory jrr created

#+call: create-dir(DIR="jrr/bin")

#+RESULTS:
: Create DIR=jrr/bin in /home2/jrr for user 'jrr' on host='jrr5x' on Thu Jul 16 19:08:33 EEST 2026
: Directory jrr/bin created

** Config path for ~jrr~ -user
*** Ensure that we are running on target system

#+BEGIN_SRC bash :eval no-export :results output
echo "User '$(whoami)' running in $(pwd) on host '$(hostname)' on $(date)"
#+END_SRC

#+RESULTS:
: User 'jrr' running in /home2/jrr on host 'jrr5x' on Thu Jul 16 19:08:41 EEST 2026

*** ~.profile~:
:PROPERTIES:
:header-args+: :var  START="added from org-document raspberry.org - start"
:header-args+: :var  END="added from org-document raspberry - end"
:header-args+:   :var  FILE=".profile"
:END:

Remove tags (if they exist)

#+BEGIN_SRC bash :eval no-export :results output
FILE=.profile
echo START=$START
echo END=$END

echo "modifying $FILE on host '$(hostname)'"
([ -f $FILE ] && echo $FILE file already exits - not created ) || (echo $FILE did not exist - created  && touch $FILE )

sed -i -e "/$START/,/$END/d" $FILE
#+END_SRC

#+RESULTS:
: START=added from org-document raspberry.org - start
: END=added from org-document raspberry - end
: modifying .profile on host 'jrr5x'
: .profile file already exits - not created

Add ~jrr/bin~ to ~PATH~
#+BEGIN_SRC bash :eval no-export :results output

#START="added from org-document jrr5.org - start"
#END="added from org-document jrr5.org - end"

echo "modifying $FILE on host '$(hostname)'"
([ -f $FILE ] && echo $FILE file already exits - not created ) || (echo $FILE did not exist - created  && touch $FILE )

sed -i -e "/$START/,/$END/d" $FILE

cat <<HERE | tee -a $FILE
# $START

# echo running $FILE
if [ -d "\$HOME/jrr/bin" ] ; then
     PATH=\$HOME/jrr/bin:\$PATH
fi

# $END
HERE
#+END_SRC

#+RESULTS:
#+begin_example
modifying .profile on host 'jrr5x'
.profile file already exits - not created
# added from org-document raspberry.org - start

# echo running .profile
if [ -d "$HOME/jrr/bin" ] ; then
     PATH=$HOME/jrr/bin:$PATH
fi

# added from org-document raspberry - end
#+end_example

#+BEGIN_SRC bash :eval no-export :results output
echo "Running in $(pwd) host '$(hostname)' on $(date)"
echo "FILE=$FILE"
cat $FILE
#+END_SRC

#+RESULTS:
#+begin_example
Running in /home2/jrr host 'jrr5x' on Thu Jul 16 19:09:05 EEST 2026
FILE=.profile
# ~/.profile: executed by the command interpreter for login shells.
# This file is not read by bash(1), if ~/.bash_profile or ~/.bash_login
# exists.
# see /usr/share/doc/bash/examples/startup-files for examples.
# the files are located in the bash-doc package.

# the default umask is set in /etc/profile; for setting the umask
# for ssh logins, install and configure the libpam-umask package.
#umask 022

# if running bash
if [ -n "$BASH_VERSION" ]; then
    # include .bashrc if it exists
    if [ -f "$HOME/.bashrc" ]; then
	. "$HOME/.bashrc"
    fi
fi

# set PATH so it includes user's private bin if it exists
if [ -d "$HOME/bin" ] ; then
    PATH="$HOME/bin:$PATH"
fi

# set PATH so it includes user's private bin if it exists
if [ -d "$HOME/.local/bin" ] ; then
    PATH="$HOME/.local/bin:$PATH"
fi
# added from org-document raspberry.org - start

# echo running .profile
if [ -d "$HOME/jrr/bin" ] ; then
     PATH=$HOME/jrr/bin:$PATH
fi

# added from org-document raspberry - end
#+end_example

[[file:/ssh:jrr@jrr5x.local:~/.profile]]

#+begin_example
Running in /home2/jrr host 'jrr5' on Tue May 19 12:14:08 EEST 2026
FILE=.profile
# ~/.profile: executed by the command interpreter for login shells.
# This file is not read by bash(1), if ~/.bash_profile or ~/.bash_login
# exists.
# see /usr/share/doc/bash/examples/startup-files for examples.
# the files are located in the bash-doc package.

# the default umask is set in /etc/profile; for setting the umask
# for ssh logins, install and configure the libpam-umask package.
#umask 022

# if running bash
if [ -n "$BASH_VERSION" ]; then
    # include .bashrc if it exists
    if [ -f "$HOME/.bashrc" ]; then
	. "$HOME/.bashrc"
    fi
fi

# set PATH so it includes user's private bin if it exists
if [ -d "$HOME/bin" ] ; then
    PATH="$HOME/bin:$PATH"
fi

# set PATH so it includes user's private bin if it exists
if [ -d "$HOME/.local/bin" ] ; then
    PATH="$HOME/.local/bin:$PATH"
fi
# added from org-document raspberry.org - start

# echo running .profile
if [ -d "$HOME/jrr/bin" ] ; then
     PATH=$HOME/jrr/bin:$PATH
fi

# added from org-document raspberry - end
#+end_example

Notice at this point .profile not yet working
#+BEGIN_SRC bash :eval no-export :results output
echo "Running in $(pwd) for user '$(whoami)' on host '$(hostname)' on $(date)"
echo "PATH=$PATH"
#+END_SRC

#+RESULTS:
: Running in /home2/jrr for user 'jrr' on host 'jrr5x' on Thu Jul 16 19:09:15 EEST 2026
: PATH=/bin:/usr/bin:/sbin:/usr/sbin:/usr/local/bin:/usr/local/sbin

#+BEGIN_SRC bash :eval no-export :results output :dir /ssh:jrr@jrr5x.local:
echo "Running in $(pwd) for user '$(whoami)' on host '$(hostname)' on $(date)"
echo "PATH=$PATH"
#+END_SRC

#+RESULTS:
: Running in /home2/jrr for user 'jrr' on host 'jrr5x' on Thu Jul 16 19:09:42 EEST 2026
: PATH=/bin:/usr/bin:/sbin:/usr/sbin:/usr/local/bin:/usr/local/sbin

: Running in /home2/jrr for user 'jrr' on host 'jrr5x' on Thu Jul 16 13:44:59 EEST 2026
: PATH=/bin:/usr/bin:/sbin:/usr/sbin:/usr/local/bin:/usr/local/sbin

#+BEGIN_SRC bash :eval no-export :results output :dir /ssh:jrr5_user:
echo "Running in $(pwd) for user '$(whoami)' on host '$(hostname)' on $(date)"
echo "PATH=$PATH"
#+END_SRC

#+RESULTS:
: Running in /home2/jrr for user 'jrr' on host 'jrr5x' on Thu Jul 16 19:09:47 EEST 2026
: PATH=/bin:/usr/bin:/sbin:/usr/sbin:/usr/local/bin:/usr/local/sbin

: Running in /home2/jrr for user 'jrr' on host 'jrr5x' on Wed Jul 15 22:19:22 EEST 2026
: PATH=/home2/jrr/jrr/bin:/home2/jrr/bin:/bin:/usr/bin:/sbin:/usr/sbin:/usr/local/bin:/usr/local/sbin

*** +~.bashrc~ : for login shells+

No need to use ~.bashrc~ because ~.profile~ adds necassary directories to path
to path.

#+BEGIN_SRC bash :eval no-export :results output :dir .
echo "Running in host '$(hostname)' on $(date)"
ssh jrr5 'echo PATH=$PATH in host $(hostname) on $(date)'
#+END_SRC

#+RESULTS:
: Running in host 'eero' on ke 20.11.2024 15.01.39 +0200
: PATH=/usr/local/bin:/usr/bin:/bin:/usr/games in host jrr5 on Wed Nov 20 15:01:40 EET 2024

#+BEGIN_SRC bash :eval no-export :results output
echo "PATH=$PATH in host '$(hostname)' on $(date)"
#+END_SRC

#+RESULTS:
: PATH=/bin:/usr/bin:/sbin:/usr/sbin:/usr/local/bin:/usr/local/sbin in host 'jrr5' on Wed Nov 20 15:01:45 EET 2024

#+BEGIN_SRC bash :eval no-export :results output
FILE=.bashrc
START="added from org-document jrr5.org - start"
END="added from org-document jrr5.org - end"

echo "Modifying $FILE on host '$(hostname)' on $(date)"

([ -f $FILE ] && echo $FILE file already exits - not created ) || (echo $FILE did not exist - created  && touch $FILE )

sed -i -e "/$START/,/$END/d" $FILE

#+END_SRC

#+RESULTS:
: Modifying .bashrc on host 'jrr5' on Wed Nov 20 15:25:47 EET 2024
: .bashrc file already exits - not created

#+BEGIN_SRC bash :eval no-export :results output
FILE=.bashrc
START="added from org-document jrr5.org - start"
END="added from org-document jrr5.org - end"

echo "Modifying $FILE on host '$(hostname)' on $(date)"

([ -f $FILE ] && echo $FILE file already exits - not created ) || (echo $FILE did not exist - created  && touch $FILE )

sed -i -e "/$START/,/$END/d" $FILE

cat <<HERE | tee -a $FILE
# $START
# echo running $FILE
if [ -d "\$HOME/.local/bin" ] ; then
     PATH=\$HOME/.local/bin:\$PATH
fi
if [ -d "\$HOME/bin" ] ; then
     PATH=\$HOME/bin:\$PATH
fi
# $END
HERE
    #+END_SRC

    #+RESULTS:
    #+begin_example
    Modifying .bashrc on host 'jrr5' on Wed Nov 20 15:02:32 EET 2024
    .bashrc file already exits - not created
    # added from org-document jrr5.org - start
    # echo running .bashrc
    if [ -d "$HOME/.local/bin" ] ; then
         PATH=$HOME/.local/bin:$PATH
    fi
    if [ -d "$HOME/bin" ] ; then
         PATH=$HOME/bin:$PATH
    fi
    # added from org-document jrr5.org - end
    #+end_example

*** User environemnt in ssh
**** ~/etc/ssh/sshd_config~ : for setting path for ssh

#+BEGIN_SRC bash :eval no-export :results output
echo "Running in $(pwd) for user '$(whoami)' on host '$(hostname)' on $(date)"
#+END_SRC

#+RESULTS:
: Running in /home2/jrr for user 'jrr' on host 'jrr5x' on Thu Jul 16 19:09:58 EEST 2026

#+BEGIN_SRC bash :eval no-export :results output
echo "Running in $(pwd) for user '$(whoami)' on host '$(hostname)' on $(date)"
ls -ltr /etc/ssh/sshd_config*
#+END_SRC

#+RESULTS:
: Running in /home2/jrr for user 'jrr' on host 'jrr5x' on Thu Jul 16 19:10:22 EEST 2026
: -rw-r--r-- 1 root root 3424 May  6 15:33 /etc/ssh/sshd_config
: 
: /etc/ssh/sshd_config.d:
: total 4
: -rw------- 1 root root 26 Jun 18 03:27 50-cloud-init.conf

Show PermitUserEnvironment (initial value)
#+BEGIN_SRC bash :eval no-export :results output
echo "Running in $(pwd) for user '$(whoami)' on host '$(hostname)' on $(date)"
cat /etc/ssh/sshd_config | grep PermitUserEnvironment
#+END_SRC

#+RESULTS:
: Running in /home2/jrr for user 'jrr' on host 'jrr5x' on Thu Jul 16 19:10:31 EEST 2026
: #PermitUserEnvironment no

This was initial value
: #PermitUserEnvironment no

Show full content of ~/etc/ssh/sshd_config~
#+BEGIN_SRC bash :eval no-export :results output
echo "Running in $(pwd) for user '$(whoami)' on host '$(hostname)' on $(date)"
FILE=/etc/ssh/sshd_config
cat $FILE
#+END_SRC

#+RESULTS:
#+begin_example
Running in /home2/jrr for user 'jrr' on host 'jrr5x' on Thu Jul 16 19:10:38 EEST 2026

# This is the sshd server system-wide configuration file.  See
# sshd_config(5) for more information.

# This sshd was compiled with PATH=/usr/local/bin:/usr/bin:/bin:/usr/games

# The strategy used for options in the default sshd_config shipped with
# OpenSSH is to specify options with their default value where
# possible, but leave them commented.  Uncommented options override the
# default value.

Include /etc/ssh/sshd_config.d/*.conf

#Port 22
#AddressFamily any
#ListenAddress 0.0.0.0
#ListenAddress ::

#HostKey /etc/ssh/ssh_host_rsa_key
#HostKey /etc/ssh/ssh_host_ecdsa_key
#HostKey /etc/ssh/ssh_host_ed25519_key

# Ciphers and keying
#RekeyLimit default none

# Logging
#SyslogFacility AUTH
#LogLevel INFO

# Authentication:

#LoginGraceTime 2m
#PermitRootLogin prohibit-password
#StrictModes yes
#MaxAuthTries 6
#MaxSessions 10

#PubkeyAuthentication yes

# Expect .ssh/authorized_keys2 to be disregarded by default in future.
#AuthorizedKeysFile	.ssh/authorized_keys .ssh/authorized_keys2

#AuthorizedPrincipalsFile none

#AuthorizedKeysCommand none
#AuthorizedKeysCommandUser nobody

# For this to work you will also need host keys in /etc/ssh/ssh_known_hosts
#HostbasedAuthentication no
# Change to yes if you don't trust ~/.ssh/known_hosts for
# HostbasedAuthentication
#IgnoreUserKnownHosts no
# Don't read the user's ~/.rhosts and ~/.shosts files
#IgnoreRhosts yes

# To disable tunneled clear text passwords, change to "no" here!
#PasswordAuthentication yes
#PermitEmptyPasswords no

# Change to "yes" to enable keyboard-interactive authentication.  Depending on
# the system's configuration, this may involve passwords, challenge-response,
# one-time passwords or some combination of these and other methods.
# Beware issues with some PAM modules and threads.
KbdInteractiveAuthentication no

# Kerberos options
#KerberosAuthentication no
#KerberosOrLocalPasswd yes
#KerberosTicketCleanup yes
#KerberosGetAFSToken no

# GSSAPI options
#GSSAPIAuthentication no
#GSSAPICleanupCredentials yes
#GSSAPIStrictAcceptorCheck yes
#GSSAPIKeyExchange no

# Set this to 'yes' to enable PAM authentication, account processing,
# and session processing. If this is enabled, PAM authentication will
# be allowed through the KbdInteractiveAuthentication and
# PasswordAuthentication.  Depending on your PAM configuration,
# PAM authentication via KbdInteractiveAuthentication may bypass
# the setting of "PermitRootLogin prohibit-password".
# If you just want the PAM account and session checks to run without
# PAM authentication, then enable this but set PasswordAuthentication
# and KbdInteractiveAuthentication to 'no'.
UsePAM yes

#AllowAgentForwarding yes
#AllowTcpForwarding yes
#GatewayPorts no
X11Forwarding yes
#X11DisplayOffset 10
#X11UseLocalhost yes
#PermitTTY yes
PrintMotd no
#PrintLastLog yes
#TCPKeepAlive yes
#PermitUserEnvironment no
#Compression delayed
#ClientAliveInterval 0
#ClientAliveCountMax 3
#UseDNS no
#PidFile /run/sshd.pid
#MaxStartups 10:30:100
#PermitTunnel no
#ChrootDirectory none
#VersionAddendum none

# no default banner path
#Banner none

# Allow client to pass locale and color environment variables
AcceptEnv LANG LC_* COLORTERM NO_COLOR

# override default of no subsystems
Subsystem	sftp	/usr/lib/openssh/sftp-server

# Example of overriding settings on a per-user basis
#Match User anoncvs
#	X11Forwarding no
#	AllowTcpForwarding no
#	PermitTTY no
#	ForceCommand cvs server
#+end_example

Original
#+begin_example
Running in /home2/jrr for user 'jrr' on host 'jrr5' on Tue May 19 12:17:21 EEST 2026

# This is the sshd server system-wide configuration file.  See
# sshd_config(5) for more information.

# This sshd was compiled with PATH=/usr/local/bin:/usr/bin:/bin:/usr/games

# The strategy used for options in the default sshd_config shipped with
# OpenSSH is to specify options with their default value where
# possible, but leave them commented.  Uncommented options override the
# default value.

Include /etc/ssh/sshd_config.d/*.conf

#Port 22
#AddressFamily any
#ListenAddress 0.0.0.0
#ListenAddress ::

#HostKey /etc/ssh/ssh_host_rsa_key
#HostKey /etc/ssh/ssh_host_ecdsa_key
#HostKey /etc/ssh/ssh_host_ed25519_key

# Ciphers and keying
#RekeyLimit default none

# Logging
#SyslogFacility AUTH
#LogLevel INFO

# Authentication:

#LoginGraceTime 2m
#PermitRootLogin prohibit-password
#StrictModes yes
#MaxAuthTries 6
#MaxSessions 10

#PubkeyAuthentication yes

# Expect .ssh/authorized_keys2 to be disregarded by default in future.
#AuthorizedKeysFile	.ssh/authorized_keys .ssh/authorized_keys2

#AuthorizedPrincipalsFile none

#AuthorizedKeysCommand none
#AuthorizedKeysCommandUser nobody

# For this to work you will also need host keys in /etc/ssh/ssh_known_hosts
#HostbasedAuthentication no
# Change to yes if you don't trust ~/.ssh/known_hosts for
# HostbasedAuthentication
#IgnoreUserKnownHosts no
# Don't read the user's ~/.rhosts and ~/.shosts files
#IgnoreRhosts yes

# To disable tunneled clear text passwords, change to "no" here!
#PasswordAuthentication yes
#PermitEmptyPasswords no

# Change to "yes" to enable keyboard-interactive authentication.  Depending on
# the system's configuration, this may involve passwords, challenge-response,
# one-time passwords or some combination of these and other methods.
# Beware issues with some PAM modules and threads.
KbdInteractiveAuthentication no

# Kerberos options
#KerberosAuthentication no
#KerberosOrLocalPasswd yes
#KerberosTicketCleanup yes
#KerberosGetAFSToken no

# GSSAPI options
#GSSAPIAuthentication no
#GSSAPICleanupCredentials yes
#GSSAPIStrictAcceptorCheck yes
#GSSAPIKeyExchange no

# Set this to 'yes' to enable PAM authentication, account processing,
# and session processing. If this is enabled, PAM authentication will
# be allowed through the KbdInteractiveAuthentication and
# PasswordAuthentication.  Depending on your PAM configuration,
# PAM authentication via KbdInteractiveAuthentication may bypass
# the setting of "PermitRootLogin prohibit-password".
# If you just want the PAM account and session checks to run without
# PAM authentication, then enable this but set PasswordAuthentication
# and KbdInteractiveAuthentication to 'no'.
UsePAM yes

#AllowAgentForwarding yes
#AllowTcpForwarding yes
#GatewayPorts no
X11Forwarding yes
#X11DisplayOffset 10
#X11UseLocalhost yes
#PermitTTY yes
PrintMotd no
#PrintLastLog yes
#TCPKeepAlive yes
#PermitUserEnvironment no
#Compression delayed
#ClientAliveInterval 0
#ClientAliveCountMax 3
#UseDNS no
#PidFile /run/sshd.pid
#MaxStartups 10:30:100
#PermitTunnel no
#ChrootDirectory none
#VersionAddendum none

# no default banner path
#Banner none

# Allow client to pass locale and color environment variables
AcceptEnv LANG LC_* COLORTERM NO_COLOR

# override default of no subsystems
Subsystem	sftp	/usr/lib/openssh/sftp-server

# Example of overriding settings on a per-user basis
#Match User anoncvs
#	X11Forwarding no
#	AllowTcpForwarding no
#	PermitTTY no
#	ForceCommand cvs server
#+end_example

Ensure ~PermitUserEnvironment yes~ in ~/etc/ssh/sshd_config~ (*notice*
as ~pi~ -user)
#+BEGIN_SRC bash :eval no-export :results output :dir /ssh:jrr5:
echo "Running in $(pwd) for user '$(whoami)' on host '$(hostname)' on $(date)"
FILE=/etc/ssh/sshd_config
sudo sed -e 's!.*PermitUserEnvironment.*!PermitUserEnvironment yes!' -i.bak $FILE
#+END_SRC

#+RESULTS:
: Running in /home/pi for user 'pi' on host 'jrr5x' on Thu Jul 16 19:11:18 EEST 2026

Show value ~PermitUserEnvironment~
#+BEGIN_SRC bash :eval no-export :results output
echo "Running in $(pwd) for user '$(whoami)' on host '$(hostname)' on $(date)"
cat /etc/ssh/sshd_config | grep PermitUserEnvironment
#+END_SRC

#+RESULTS:
: Running in /home2/jrr for user 'jrr' on host 'jrr5x' on Thu Jul 16 19:11:22 EEST 2026
: PermitUserEnvironment yes

Restart (maybe reboot)
#+call: reboot[:dir /ssh:jrr5:]()

Wait for wakeup
#+call: ping-ip[:dir .]()

#+RESULTS:
: User 'jj pinging JRR5_IP=jrr5x.local from Leo on to 16.7.2026 19.12.48 +0300
: PING jrr5x.local (192.168.1.203) 56(84) bytes of data.
: 64 bytes from jrr5x.local (192.168.1.203): icmp_seq=1 ttl=64 time=23.0 ms
: 64 bytes from jrr5x.local (192.168.1.203): icmp_seq=2 ttl=64 time=5.27 ms
: 64 bytes from jrr5x.local (192.168.1.203): icmp_seq=3 ttl=64 time=5.35 ms
: 
: --- jrr5x.local ping statistics ---
: 3 packets transmitted, 3 received, 0% packet loss, time 2003ms
: rtt min/avg/max/mdev = 5.271/11.196/22.968/8.323 ms

And wait that reboot finished
#+call: greet-tramp()

#+RESULTS:
: User 'jrr' from host 'jrr5x' greeting on Thu Jul 16 19:12:59 EEST 2026  (using eshell tramp)

Configure =~/.ssh/environment= (which initially does not exists)

#+BEGIN_SRC bash :eval no-export :results output
echo "Running in $(pwd) for user '$(whoami)' on host '$(hostname)' on $(date)"
ls -ltr .ssh
#+END_SRC

#+RESULTS:
: Running in /home2/jrr for user 'jrr' on host 'jrr5x' on Thu Jul 16 19:13:04 EEST 2026
: total 4
: -rw------- 1 jrr jrr 88 Jul 16 19:07 authorized_keys

Safe to create file =~/.ssh/environment= in tramp path pointed by

~ROOT_DIR~ because it was non-existent:
#+begin_src txt :tangle (concat  (jj-org-tmp-get-global-prop "ROOT_DIR" )  ".ssh/" "environment")
#ENV=~/.profile
BASH_ENV=~/.profile
#SSH_LOGIN=Y
#+end_src

Set permissions 
#+BEGIN_SRC bash :eval no-export :results output
echo "Running in $(pwd) for user '$(whoami)' on host '$(hostname)' on $(date)"
FILE=~/.ssh/environment
chmod 700 $FILE
ls -ltr $FILE
echo "Content of FILE=$FILE in host $(hostname) on $(date)"
cat $FILE
#+END_SRC

#+RESULTS:
: Running in /home2/jrr for user 'jrr' on host 'jrr5x' on Thu Jul 16 19:13:17 EEST 2026
: -rwx------ 1 jrr jrr 49 Jul 16 19:13 /home2/jrr/.ssh/environment
: Content of FILE=/home2/jrr/.ssh/environment in host jrr5x on Thu Jul 16 19:13:17 EEST 2026
: #ENV=~/.profile
: BASH_ENV=~/.profile
: #SSH_LOGIN=Y

Expect to see ~/home2/jrr/jrr/bin~
#+call: tramp-path()

#+RESULTS:
: Path info for user 'jrr' in host 'jrr5x' on Thu Jul 16 19:13:35 EEST 2026 for user jrr
: PATH=/home2/jrr/jrr/bin:/home2/jrr/bin:/bin:/usr/bin:/sbin:/usr/sbin:/usr/local/bin:/usr/local/sbin

: Path info for user 'jrr' in host 'jrr5' on Tue May 19 12:25:00 EEST 2026 for user jrr
: PATH=/bin:/usr/bin:/sbin:/usr/sbin:/usr/local/bin:/usr/local/sbin

: Path info host welleri on Thu Sep 7 12:59:02 EEST 2023 for user pi
: PATH=/home/pi/.local/bin:/home/pi/bin:/bin:/usr/bin:/sbin:/usr/sbin:/usr/local/bin:/usr/local/sbin

Pi does not have  ~/home2/jrr/jrr/bin~

#+call: ssh-path[:dir .](TARGET="jrr5")

#+RESULTS:
: User 'jj' calling ssh TARGET=jrr5 from Leo on to 16.7.2026 19.13.41 +0300
: PATH@jrr5x=/usr/local/bin:/usr/bin:/bin:/usr/games

: User 'jj' calling ssh TARGET=jrr5 from Leo on ti 19.5.2026 12.26.04 +0300
: PATH@jrr5=/usr/local/bin:/usr/bin:/bin:/usr/games

: call ssh TARGET=jrr5 from eero on ti 1.7.2025 14.51.12 +0300
: PATH@jrr5=/usr/local/bin:/usr/bin:/bin:/usr/games

: call ssh TARGET=jrr5 from eero on ke 20.11.2024 15.12.29 +0200
: ssh PATH@jrr5=/usr/local/bin:/usr/bin:/bin:/usr/games

: call ssh lavatin 'echo ... '  on eero
: ssh PATH@sorsa=/usr/local/bin:/usr/bin:/bin:/usr/games

#+call: ssh-path[:dir .](TARGET="jrr5_user")

#+RESULTS:
: User 'jj' calling ssh TARGET=jrr5_user from Leo on to 16.7.2026 19.13.49 +0300
: PATH@jrr5x=/usr/local/bin:/usr/bin:/bin:/usr/games

*** Test PATH -setting

#+call: greet-login()

#+RESULTS:
: PATH@jrr5x--login=/home2/jrr/jrr/bin:/home2/jrr/bin:/home2/jrr/jrr/bin:/home2/jrr/bin:/usr/local/sbin:/usr/local/bin:/usr/sbin:/usr/bin:/sbin:/bin:/usr/local/games:/usr/games

: PATH@jrr5--login=/home2/jrr/jrr/bin:/home2/jrr/bin:/usr/local/sbin:/usr/local/bin:/usr/sbin:/usr/bin:/sbin:/bin:/usr/local/games:/usr/games

: PATH@jrr5--login=/home/pi/jrr/bin:/home/pi/bin:/home/pi/jrr/bin:/home/pi/bin:/usr/local/sbin:/usr/local/bin:/usr/sbin:/usr/bin:/sbin:/bin:/usr/local/games:/usr/games

: running .profile
: PATH@jrr5--login=/home/pi/bin:/home/pi/bin:/usr/local/sbin:/usr/local/bin:/usr/sbin:/usr/bin:/sbin:/bin:/usr/local/games:/usr/games

#+call: ssh-path[:dir "."](TARGET="jrr5")

#+RESULTS:
: User 'jj' calling ssh TARGET=jrr5 from Leo on to 16.7.2026 19.14.12 +0300
: PATH@jrr5x=/usr/local/bin:/usr/bin:/bin:/usr/games

: call ssh TARGET=jrr5 from eero on ke 20.11.2024 15.27.24 +0200
: PATH@jrr5=/usr/local/bin:/usr/bin:/bin:/usr/games

#+call: tramp-path()

#+RESULTS:
: Path info for user 'jrr' in host 'jrr5x' on Thu Jul 16 19:14:19 EEST 2026 for user jrr
: PATH=/home2/jrr/jrr/bin:/home2/jrr/bin:/bin:/usr/bin:/sbin:/usr/sbin:/usr/local/bin:/usr/local/sbin

: Path info in host 'jrr5' on Wed Nov 20 15:27:31 EET 2024 for user pi
: PATH=/home/pi/bin:/bin:/usr/bin:/sbin:/usr/sbin:/usr/local/bin:/usr/local/sbin

** +~bin/sine-gen.sh~: generate sine wave+

Ref: https://trac.ffmpeg.org/wiki/AudioChannelManipulation

#+begin_src bash :eval no  :tangle (concat  (jj-org-tmp-get-global-prop "ROOT_DIR" )  "bin/" "sine-gen.sh") :shebang "#!/bin/bash"

VERSION=0.1
# 1=warning
DEBUG=1
TS_FORMAT="+%Y%m%d-%T"

# output device, one from list-devices, default  none
AUDIO_OUT="" 
SOUND_DIR=$HOME/tmp
DURATION=60
LEFT_FREQ="1000"
RIGHT_FREQ="440"
VOLUME=1.0
# override
FILE=""

# filter_complex string to add for stero/mono
MONO_OR_STEREO_CMD=""

# Left and Right channel gains
RGAIN=1.0
LGAIN=1.0
GAIN=8.0

# ------------------------------------------------------------------
# Subrus

log() {
    local LEVEL=$1
    local MSG=$2
    if [ $DEBUG -ge $LEVEL ]; then
        	echo $(date $TS_FORMAT): $0'|'$MSG 1>&2
    fi
}

usage() {
    echo 
    echo usage: $(basename $0)
    echo $0 - $VERSION
    echo ""
    echo "Generate sine waves"
    echo ""
    echo "Usage:"
    echo "$0 [options]  -- <commands>"
    echo "options:"
    echo "--sh_trace"
    echo "--version             : print out version number && exit 0"
    echo "--mono                : pan stereo streams to one mono stream"
    echo "--device AUDIO_OUT    : Set audio AUDIO_OUT one from 'list-devices', defaults $AUDIO_OUT"
    echo "--gain GAIN           : Volume gain, default $GAIN"
    echo "--rgain RGAIN         : Volume on right channel, default $RGAIN"
    echo "--lgain LGAIN         : Volume on left channel, default $LGAIN"
    echo "--left FREQ           : Set left ch frequency, default $LEFT_FREQ"
    echo "--right FREQ          : Set right ch frequency, default $RIGHT_FREQ"
    echo "--volume VOLUME       : Set output VOLUME"
    echo "--duration DURATION   : Set duration of generated sound file to DURATION=$DURATION secs"
    echo "--file FILE           : Use sound FILE"
    echo "--debug|-v (multiple) : increment debug level"
    echo "-?|--help             : usage"
    echo ""
    echo "commands:"
    echo "alsa-devices          : list ALSA hw devices"
    echo "list-devices          : list audio devices"
    echo "gen                   : sine signal generator RIGHT=$RIGHT_FREQ Hz, LEFT=$LEFT_FREQ Hz, GAIN=$GAIN DURATION=$DURATION s"
    echo "sine                  : generate 'sine FILE'"
    echo "play                  : play FILE"
    echo ""
    echo "Examples:"
    echo ""
    echo
    echo "# generate sine wave LEFT_FREQ=$LEFT_FREQ, RIGHT_FREQ=$RIGHT_FREQ to sound FILE=$FILE w"
    echo "$0 sine"
    echo ""
    echo "# play sound FILE=$FILE"
    echo "$0 play"
    echo ""

}

init_audio_out() {
    # Try USB ADC card
    log 2 "Init audio starts"
    log 3 "Audio devices $(aplay -L | grep '^hw:')"
    AUDIO_OUT=$(aplay -L | grep '^hw:CARD=Audio'); 
    if [ -z "$AUDIO_OUT" ]; then
        AUDIO_OUT=$(aplay -L | grep '^hw:CARD=SE')
    fi
    if [ -z "$AUDIO_OUT" ]; then
        AUDIO_OUT=$(aplay -L | grep '^hw:CARD=Headphones')
    fi
    if [ -z "$AUDIO_OUT" ]; then
        log 1 "Could not set AUDIO_OUT from $(aplay -L | grep '^hw:') devices"
    fi

}

# Options - after functions

# ------------------------------------------------------------------
while :
do
    if [ -z "$1" ]; then
	    break
    fi

    log 3 "Check option for '$1'"

    case "$1" in
        
	--sh_trace|--sh-trace)
	    set -x
	    shift
	    ;;
    
	--volume)
	    shift
	    VOLUME=$1; shift
	    ;;

	--gain)
	    shift
	    GAIN=$1; shift
	    ;;
    
	--mono)
	    shift
	    MONO_OR_STEREO_CMD=",pan=mono|c0=0.5*c0+0.5*c1"
	    ;;
    
	--rgain)
	    shift
	    RGAIN=$1; shift
	    ;;

	--lgain)
	    shift
	    LGAIN=$1; shift
	    ;;

	--device)
	    shift
	    AUDIO_OUT=$1; shift
        log 2 "Opiotion --device $AUDIO_OUT"
	    ;;

	--left)
	    shift
	    # LEFT_FREQ=$1; shift
	    LEFT_FREQ=$(($1+0)); shift
	    ;;
    
	--file)
	    shift
	    FILE=$1; shift
	    ;;
    
	--duration)
	    shift
	    DURATION=$1; shift
        log 1 "set DURATION=$DURATION"
	    ;;
    
	--right)
	    shift
	    # RIGHT_FREQ=$1; shift
	    RIGHT_FREQ=$(($1+0)); shift
	    ;;

	--debug|-v)
	    shift
	    DEBUG=`expr $DEBUG + 1`
	    log 1 "DEBUG=$DEBUG"
	    ;;

	-\?|--help)
	    usage
	    exit 2
	    ;;

	 '--')
	    break
	    ;;

	,*)
	    break
	    ;;
    esac
done

if [ -z "$AUDIO_OUT" -o  "$AUDIO_OUT" = "-" ]; then
    log 1 "Call init audio"
    init_audio_out
fi    
log 1 "Using AUDIO_OUT=$AUDIO_OUT"

if  [ -z "$FILE" ]; then
    FILE=$SOUND_DIR/sine-${LEFT_FREQ}l-${RIGHT_FREQ}r-${DURATION}s.wav
fi

# ------------------------------------------------------------------
# actions

# Output usage - if no commands given
if [  $# -lt 1 ]; then
    usage
    exit 2
fi

DURATION_CMD=""
if [ $DURATION -gt 0 ]; then
   DURATION_CMD=":d=$DURATION"
fi
log 3 "DURATION_CMD=$DURATION_CMD"

while :
do

    log 3 "cmdline parameters left $#"
    if [  $# -lt 1 ]; then
	    break
    fi

    CMD=$1
    shift

    case "$CMD" in

        version) 
	        echo "$0 - $VERSION"
	        ;;

        true)
            ;;

        list-devices) 
            aplay -l
            echo "------------------------------------------------------------------"
            echo "Hardware devices"
            aplay -L | grep "^hw:"
            echo "------------------------------------------------------------------"
            echo "ffmpeg sinks"
            ffmpeg -sinks
	        ;;
        
        alsa-devices) 
            echo "------------------------------------------------------------------"
            echo "Alsa Hardware devices"
            aplay -L | grep "^hw:"
	        ;;

        play)
            echo "Running in host '$(hostname)' on $(date)"
            echo "FILE=$FILE"
            echo "AUDIO_OUT=$AUDIO_OUT"
            # ffplay -f lavfi "aevalsrc=exprs=sin(2*PI*${LEFT_FREQ}*t)|sin(2*PI*${RIGHT_FREQ}*t)" -ac 2
            set -x
            ffplay  -hide_banner \
                    -autoexit \
                    -f alsa $AUDIO_OUT \
                    $FILE
            set +x
            ;;
	    
        fplay)
            echo "Running in host '$(hostname)' on $(date)"
            echo "FILE=$FILE"
            echo "AUDIO_OUT=$AUDIO_OUT"
            # ffplay -f lavfi "aevalsrc=exprs=sin(2*PI*${LEFT_FREQ}*t)|sin(2*PI*${RIGHT_FREQ}*t)" -ac 2
            set -x
            ffmpeg \
                    -f alsa $AUDIO_OUT \
                    -i $FILE
            set +x
            ;;

        gen-stereo)
            echo "Running in host '$(hostname)' on $(date)"
            echo "LEFT_FREQ=$LEFT_FREQ, RIGHT_FREQ=$RIGHT_FREQ, FILE=$FILE"            
            echo "AUDIO_OUT=$AUDIO_OUT"
            echo "RGAIN=$RGAIN"
            echo "LGAIN=$LGAIN"
            echo "DURATION_CMD=$DURATION_CMD"
            echo "MONO_OR_STEREO_CMD=$MONO_OR_STEREO_CMD"
            set -x
            ffmpeg \
                -hide_banner -nostdin -y \
                -f lavfi -i "sine=frequency=$LEFT_FREQ$DURATION_CMD" \
                -f lavfi  -i "sine=frequency=$RIGHT_FREQ$DURATION_CMD" \
                -filter_complex "join=inputs=2[joined];[joined]aeval=$LGAIN*val(ch)|$RGAIN*val(ch)${MONO_OR_STEREO_CMD}[aout]" \
                -map "[aout]" \
                -ac 2 \
                -f alsa hw:CARD=Audio,DEV=0
            set +x
            ;;

        gen2)
            echo "Running in host '$(hostname)' on $(date)"
            echo "LEFT_FREQ=$LEFT_FREQ, RIGHT_FREQ=$RIGHT_FREQ, FILE=$FILE"            
            echo "AUDIO_OUT=$AUDIO_OUT"
            echo "RGAIN=$RGAIN"
            echo "LGAIN=$LGAIN"
            echo "DURATION_CMD=$DURATION_CMD"
            set -x
            ffmpeg \
                -hide_banner -nostdin -y \
                -f lavfi -i "sine=frequency=$LEFT_FREQ$DURATION_CMD" \
                -f lavfi  -i "sine=frequency=$RIGHT_FREQ$DURATION_CMD" \
                -filter_complex "join=inputs=2[joined];[joined]aeval=$LGAIN*val(ch)|$RGAIN*val(ch)[aout]" -map "[aout]" \
                -f alsa $AUDIO_OUT
            set +x
            ;;

        gen)
            # Config command
            echo "DURATION_CMD=$DURATION_CMD"
            echo "LEFT_FREQ=$LEFT_FREQ, RIGHT_FREQ=$RIGHT_FREQ"            
            echo "AUDIO_OUT=$AUDIO_OUT"
            echo "GAIN=$GAIN"
            echo "FILE=$FILE"
            echo "MONO_OR_STEREO_CMD=$MONO_OR_STEREO_CMD"
            (set -x ; ffmpeg \
                -hide_banner -nostdin -y \
                 -f lavfi -i "sine=frequency=$LEFT_FREQ$DURATION_CMD" \
                 -f lavfi  -i "sine=frequency=$RIGHT_FREQ$DURATION_CMD"  \
                 -filter_complex "join, volume=volume=$GAIN ${MONO_OR_STEREO_CMD}[aout]" \
                 -map "[aout]" -ac 2 -f alsa $AUDIO_OUT \
                 )
            ;;
	    
        sine)
            echo "Running in host '$(hostname)' on $(date)"
            echo "LEFT_FREQ=$LEFT_FREQ, RIGHT_FREQ=$RIGHT_FREQ, FILE=$FILE"
            set -x 
            ffmpeg -nostdin -y \
                    -filter_complex "aevalsrc=exprs=sin(2*PI*$LEFT_FREQ*t)|sin(2*PI*$RIGHT_FREQ*t):s=44100:d=$DURATION" \
                    -ac 2 \
                    $FILE
            set +x
            ls -ltr $FILE
            ;;

	    ,*)
	        usage
	        echo  "Unknown action: $CMD"
	        exit 3
	        ;;

    esac

done

# https://stackoverflow.com/questions/5109038/linux-sine-wave-audio-generator
# ffplay -nodisp -f lavfi -i "sine=f=1000"
# ffplay -nodisp -f lavfi -i "sine=frequency=1000:sample_rate=44100:duration=10:channels=1[outl];sine=frequency=1500:sample_rate=44100:duration=10:channels=1[outr];[outl][outr]amerge=inputs=2" -ac 2
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
