jarjuk/jrr/DEVELOPMENT.org

#PROPERTY: header-args+ :var  RELEASE="2"
#+PROPERTY: header-args+ :var  FIRMWARE_RELEASE="4"
#+PROPERTY: header-args+ :var  CONDA_ENV="pyyton3"

* Setup development environment
:PROPERTIES:
:header-args+: :dir  .
:END:

** Create local directories

#+call: create-dir(DIR="tmp")

#+RESULTS:
: Create DIR=tmp in host='eero' on ti 24.6.2025 12.58.25 +0300
: Directory tmp created

#+call: create-dir(DIR="lib")

#+RESULTS:
: Directory lib already exists

#+call: create-dir(DIR="src")

#+RESULTS:
: Create DIR=src in host='eero' on ti 24.6.2025 12.58.31 +0300
: Directory src already exists

#+call: create-dir(DIR="spec")

#+RESULTS:
: Create DIR=spec in host='eero' on ti 24.6.2025 12.58.33 +0300
: Directory spec already exists

#+RESULTS:
: Create DIR=resources/sprite in host='eero' on la 28.12.2024 16.42.21 +0200
: Directory resources/sprite already exists

** Activate CONDA_ENV (for eglot/LSP support)

#+BEGIN_SRC bash :eval no-export :results output
echo "Running in host '$(hostname)' on $(date)"
echo "CONDA_ENV=$CONDA_ENV"
#+END_SRC

#+RESULTS:
: Running in host 'Leo' on ma 31.8.2026 10.22.21 +0300
: CONDA_ENV=pyyton3

#+BEGIN_SRC elisp :eval no-export
(conda-env-activate CONDA_ENV)
#+END_SRC

#+RESULTS:
: Switched to conda environment: /home/jj/miniconda3/envs/pyyton3/

or in the shell run

#+begin_example
conda env activate pyyton3
#+end_example

** Create ~pytest.ini~ for CI

#+begin_src txt :tangle pytest.ini
# Tangled fro DEVELOPMENT - changes will be overridden
[pytest]
log_level=DEBUG
pythonpath = .
testpaths = spec
norecursedirs = .git fixtures tmp* ltximg pics pics-keep __pycache__
markers =
    slow: marks tests as slow (deselect with '-m "not slow"')
    current:Allow just one test to run
    feature: BDD test cases

# [pytest-watch]
# ignore=test/fixtures
# ext=.py,.feature
# dont-watch-files='^\.#
#+end_src

#+BEGIN_SRC bash :eval no-export :results output
echo "Running in host '$(hostname)' on $(date)"
cat pytest.ini

#+END_SRC

#+RESULTS:
#+begin_example
Running in host 'eero' on to 26.6.2025 12.26.20 +0300
# Tangled fro DEVELOPMENT - changes will be overridden
[pytest]
log_level=DEBUG
pythonpath = .
testpaths = spec
norecursedirs = .git fixtures tmp* ltximg pics pics-keep __pycache__
markers =
    slow: marks tests as slow (deselect with '-m "not slow"')
    current:Allow just one test to run
    feature: BDD test cases

# [pytest-watch]
# ignore=test/fixtures
# ext=.py,.feature
# dont-watch-files='^\.#
#+end_example

** Start CI -tests

*Continous test FAST*
#+BEGIN_SRC elisp :noweb yes :results output :eval no-export :exports none 
(start-process "server" "buf-server" "xterm" "-fa" "monaco" "-fs" "15"  "-T" "ai-smoke" "-hold" "-e"  "bash" "-c" "ptw . --now  --ignore-patterns='#*,.#*,flycheck*' -m 'not slow and not feature'")
#+END_SRC

#+RESULTS:

Run tests manually in terminal
#+begin_example
ptw . --now  --ignore-patterns='#*,.#*,flycheck*' -m 'not slow and not feature'
#+end_example

** rsync source code to target ~jrr5~
#+BEGIN_SRC bash :eval no-export :results output
echo "Running in $(pwd) host '$(hostname)' on $(date)"
rsync -a --delete --update --verbose --checksum --recursive jrr.py jrr5:.
rsync -a --delete --update --verbose --checksum --recursive src/ jrr5:jrr/src/
#+END_SRC

#+RESULTS:
#+begin_example
Running in /home/jj/work/jrr host 'Leo' on pe 24.4.2026 10.02.01 +0300
sending incremental file list

sent 74 bytes  received 12 bytes  57,33 bytes/sec
total size is 128  speedup is 1,49
sending incremental file list
./
constants.py
jrr_radio.py
messages.py
screen_coro.py
deleting Python_ILI9486/__pycache__/ILI9486.cpython-311.pyc
deleting __pycache__/jrr_dapp.cpython-311.pyc
deleting __pycache__/console.cpython-311.pyc
Python_ILI9486/__pycache__/
__pycache__/

sent 27.767 bytes  received 1.651 bytes  19.612,00 bytes/sec
total size is 14.014.227  speedup is 476,38
#+end_example

** Some dev commands
:PROPERTIES:
:header-args+: :dir  /ssh:jrr5:
:END:

*** Debug during dev
Terminal commands

#+BEGIN_SRC bash :eval no-export :results output
echo "Running in $(pwd) host '$(hostname)' on $(date)"
sudo systemctl stop jrr
#+END_SRC

#+RESULTS:
: Running in /home/pi host 'jrr5' on Sun May 18 17:31:13 EEST 2025

#+BEGIN_SRC bash :eval no-export :results output
echo "Running in $(pwd) host '$(hostname)' on $(date)"
jrr.sh status
#+END_SRC

#+RESULTS:
: Running in /home/pi host 'jrr5' on Sun May 18 17:37:52 EEST 2025
: jrr.sh: status=1/
: jrr.py: status=1/
: ffmpeg: status=1/

#+BEGIN_SRC bash :eval no-export :results output
jrr.sh status
#+END_SRC

#+RESULTS:
: jrr.sh: status=1/
: jrr.py: status=0/pi          2519    2518  0 17:37 ?        00:00:00 bash -c bash -c .venv/bin/python ./jrr.py -v -v  radio |   tee tmp/apu.log
: ffmpeg: status=1/

After ~systemctl stop jrr; jrr.sh stop~

#+begin_example

.venv/bin/python jrr/jrr.py -v -v  radio |   tee tmp/apu.log
#+end_example

#+BEGIN_SRC bash :eval no-export :results output
echo "Running in $(pwd) host '$(hostname)' on $(date)"
jrr.sh stop
#+END_SRC

#+BEGIN_SRC bash :eval no-export :results output
echo "Running in $(pwd) host '$(hostname)' on $(date)"
jrr.sh kill
#+END_SRC

#+RESULTS:
: Running in /home/pi host 'jrr5' on Sun May 18 17:37:46 EEST 2025

From terminal 
#+begin_example
killall ffmpeg ; .venv/bin/python jrr/jrr.py -v -v  radio 2>&1 |   tee tmp/apu.log | grep -E 'gpio_coro|ERROR'
#+end_example

#+BEGIN_SRC elisp :noweb yes :results output :eval no-export :exports none :var TERM_HEADER="jrr5 dmesg"
   (start-process "server" "buf-server" "xterm"  "-T" "dmesg@sorsa" "-fa" "'Monospace'" "-fs" "12" "-hold" "-e"  "bash" "-c" (concat "ssh jrr5 bash -c '.venv/bin/python ./jrr.py -v -v  radio |   tee tmp/apu.log'" ) )
#+END_SRC

#+RESULTS:

*** Screen shots
After ~systemctl stop jrr; jrr.sh stop~

#+BEGIN_SRC bash :eval no-export :results output
  echo "Running in $(pwd) host '$(hostname)' on $(date)"
  cd jrr
  jrr.sh --help
#+END_SRC

#+RESULTS:
: Running in /home/pi host 'jrr5' on Tue Apr 28 08:13:19 EEST 2026

#+begin_example
.venv/bin/python ./jrr.py -v -v  radio |   tee tmp/apu.log
#+end_example

*** manual streaming

#+BEGIN_SRC bash :eval no-export :results output
echo "Running in $(pwd) host '$(hostname)' on $(date)"
./jrr_streamer.sh -v -v -v --file https://icecast.live.yle.fi/radio/YleRadio1/icecast.audio stream

#+END_SRC

*** Chrip from command line

#+begin_example
jrr.sh stop
jrr.sh status
#+end_example

#+BEGIN_SRC bash :eval no-export :results output
echo "Running in $(pwd) host '$(hostname)' on $(date)"
jrr.sh status
#+END_SRC

#+RESULTS:
: Running in /home/pi host 'jrr5' on Tue Apr 14 14:51:06 EEST 2026
: jrr.sh: status=0/pi           414       1  0 14:34 ?        00:00:00 /bin/bash /home/pi/jrr/bin/jrr.sh daemon
: jrr.py: status=0/pi           527     414  6 14:34 ?        00:01:01 .venv/bin/python ./jrr.py radio
: ffmpeg: status=0/pi          2549    2548  5 14:47 ?        00:00:11 ffmpeg -hide_banner -nostdin -i https://jarviradio.radiotaajuus.fi:9000/jr -filter_complex [0:a]volume=volume=2,pan=mono|c0=0.5*c0+0.5*c1,alimiter[aout] -map [aout] -ac 2 -f alsa hw:CARD=Audio,DEV=0

Stop jrr-service

#+BEGIN_SRC bash :eval no-export :results output
echo "Running in $(pwd) host '$(hostname)' on $(date)"
jrr.sh stop
#+END_SRC

#+RESULTS:
: Running in /home/pi host 'jrr5' on Tue Apr 14 14:51:20 EEST 2026

Create chipr
#+BEGIN_SRC bash :eval no-export :results output
echo "Running in $(pwd) host '$(hostname)' on $(date)"
cd jrr/src
./jrr_streamer.sh -v -v  --duration 10 --start-freq 10  --end-freq 5000 chirp
#+END_SRC

#+RESULTS:
: Running in /home/pi host 'jrr5' on Tue Apr 14 14:53:45 EEST 2026
: Using FILE=/home/pi/tmp/chrip-10-5000-10s.wav
: Running in host 'jrr5' on Tue Apr 14 14:53:46 EEST 2026
: START_FREQ=10, END_FREQ=5000, FILE=/home/pi/tmp/chrip-10-5000-10s.wav, DURATION=10
: -rw-r--r-- 1 pi pi 1764078 Apr 14 14:53 

Play chirp
#+BEGIN_SRC bash :eval no-export :results output :var CHIRP="/home/pi/tmp/chrip-10-5000-10s.wav"
echo "Running in $(pwd) host '$(hostname)' on $(date)"
echo "CHIRP=$CHIRP"
cd jrr/src
./jrr_streamer.sh --file "$CHIRP" stream  2>&1
#+END_SRC

#+RESULTS:
#+begin_example
Running in /home/pi host 'jrr5' on Tue Apr 14 15:04:05 EEST 2026
CHIRP=/home/pi/tmp/chrip-10-5000-10s.wav
20260414-15:04:05: ./jrr_streamer.sh|set_alsa_volume: card=Audio, volume=95%
Simple mixer control 'Headphone',0
  Capabilities: pvolume pswitch pswitch-joined
  Playback channels: Front Left - Front Right
  Limits: Playback 0 - 175
  Mono:
  Front Left: Playback 166 [95%] [-3.38dB] [on]
  Front Right: Playback 166 [95%] [-3.38dB] [on]
Running in host 'jrr5' on Tue Apr 14 15:04:05 EEST 2026
20260414-15:04:05: ./jrr_streamer.sh|AUDIO_OUT=hw:CARD=Audio,DEV=0, URL=/home/pi/tmp/chrip-10-5000-10s.wav, GAIN=2
+ ffmpeg -hide_banner -nostdin -nostats -loglevel error -i /home/pi/tmp/chrip-10-5000-10s.wav -filter_complex '[0:a]volume=volume=2,pan=mono|c0=0.5*c0+0.5*c1,alimiter[aout]' -map '[aout]' -ac 2 -f alsa hw:CARD=Audio,DEV=0
#+end_example

Other commands 

#+begin_example
./jrr_streamer.sh --duration 10 --end-freq 5000 chirp
./jrr_streamer.sh play /home/pi/tmp/chrip-100-5000-10s.wav
#+end_example

** Check version

#+call: python-version()

: hello world
: sys.version=3.11.11 | packaged by conda-forge | (main, Mar  3 2025, 20:43:55) [GCC 13.3.0]
: Conda environment=pyyton3

** Debug on jrr5
:PROPERTIES:
:header-args+: :dir  /ssh:jrr5:
:END:

Stop jrr-service

#+call: svc-stop[](SVC="jrr")

#+RESULTS:
: Stop SVC=jrr in host jrr5 on Wed Apr 30 14:04:22 EEST 2025

#+call: svc-status[](SVC="jrr")

#+RESULTS:
#+begin_example
Status of SVC=jrr in host 'jrr5' on Wed Apr 30 14:04:27 EEST 2025
○ jrr.service - Järvidio service
     Loaded: loaded (/etc/systemd/system/jrr.service; enabled; preset: enabled)
     Active: inactive (dead) since Wed 2025-04-30 09:03:56 EEST; 5h 0min ago
   Duration: 6min 54.490s
    Process: 2715 ExecStart=/home/pi/bin/jrr.sh daemon (code=killed, signal=TERM)
   Main PID: 2715 (code=killed, signal=TERM)
        CPU: 31.299s

Apr 30 08:57:02 jrr5 systemd[1]: Started jrr.service - Järvidio service.
Apr 30 08:57:02 jrr5 jrr.sh[2715]: Wed 30 Apr 08:57:02 EEST 2025: /home/pi/bin/jrr.sh|User 'pi' starting script '/home/pi/bin/jrr.sh' with parameters 'daemon' on host 'jrr5' in directory '/home/pi'
Apr 30 08:57:02 jrr5 jrr.sh[2724]: ffmpeg: no process found
Apr 30 08:57:02 jrr5 jrr.sh[2715]: Wed 30 Apr 08:57:02 EEST 2025: /home/pi/bin/jrr.sh|User 'pi' launching järviradioradio daemon
Apr 30 08:57:02 jrr5 jrr.sh[2715]: Wed 30 Apr 08:57:02 EEST 2025: /home/pi/bin/jrr.sh|User 'pi' runs CMD='.venv/bin/python ./jrr.py -v radio' in directory /home/pi with PATH='/usr/local/sbin:/usr/local/bin:/usr/sbin:/usr/bin:/sbin:/bin'
Apr 30 09:03:56 jrr5 systemd[1]: Stopping jrr.service - Järvidio service...
Apr 30 09:03:56 jrr5 systemd[1]: jrr.service: Killing process 2740 (python) with signal SIGKILL.
Apr 30 09:03:56 jrr5 systemd[1]: jrr.service: Deactivated successfully.
Apr 30 09:03:56 jrr5 systemd[1]: Stopped jrr.service - Järvidio service.
Apr 30 09:03:56 jrr5 systemd[1]: jrr.service: Consumed 31.299s CPU time.
#+end_example

Ref

#+BEGIN_SRC bash :eval no-export :results output :var SVC="jrr"
echo "Running in $(pwd) host '$(hostname)' on $(date)"

cat /etc/systemd/system/$SVC.service

#+END_SRC

#+RESULTS:
#+begin_example
Running in /home/pi host 'jrr5' on Wed Apr 30 14:04:33 EEST 2025
[Unit]
Description=Järvidio service

[Service]
Type=simple
Restart=always
RestartSec=1
User=pi
Group=pi
WorkingDirectory=/home/pi
ExecStart=/home/pi/bin/jrr.sh daemon
StandardOutput=null
StandardError=journal

[Install]
WantedBy=multi-user.target

#+end_example

Notice ~/home/pi/bin/jrr.sh~

#+BEGIN_SRC bash :eval no-export :results output :
echo "Running in $(pwd) host '$(hostname)' on $(date)"
jrr.sh -?

#+END_SRC

#+RESULTS:
#+begin_example
Running in /home/pi host 'jrr5' on Wed Apr 30 14:05:03 EEST 2025

usage: jrr.sh
/home/pi/bin/jrr.sh - 0.1

Järviradioradio controller script

Usage:
/home/pi/bin/jrr.sh [options]  -- <commands>
options:
--sh_trace
--version             : print out version number && exit 0
--debug|-v            : increment DEBUG='1' level (in script /home/pi/bin/jrr.sh)
--jrr-debug           : increment JRR_DEBUG='-v' level 
--jrr-log FILE        : log file to store stdout log JRR_LOG=''
-?|--help             : usage

commands:
daemon                : Run jrr.py application
stop                  : Send kill signal to jrr.py and stop streamer process, 0
status                : Show process ids for jrr.py and ffmpeg streamer process
kill-ffmpeg           : Kill ffmpeg streamer process

Examples:

#+end_example

#+BEGIN_SRC elisp :noweb yes :results output :eval no-export :exports none 
(start-process "server" "buf-server" "xterm"  "-T" "jrr" "-fa" "'Monospace'" "-fs" "12"  "-hold" "-e"  "bash" "-c" "ssh jrr5 bin/jrr.sh daemon")
#+END_SRC

#+RESULTS:

** Automation version tag
:PROPERTIES:
:header-args:
:END:

#+BEGIN_SRC bash :eval no-export :results output :shebang #!/bin/bash :tangle .git/hooks/post-commit

# Only run if VERSION file was committed
if git diff-tree --no-commit-id --name-only -r HEAD | grep -q '^src/VERSION$'; then
    VERSION=$(cat src/VERSION)

    # Check if tag already exists
    if git rev-parse "$VERSION" >/dev/null 2>&1; then
        echo "Tag '$VERSION' already exists. Skipping tagging."
    else
        git tag "$VERSION"
        echo "Tagged commit with version: $VERSION"
    fi
fi
#+END_SRC

#+RESULTS:

** Create screen snapthots

Stop ~jrr~ service

#+call: jrr-stop[:dir /ssh:jrr5: ]()

#+RESULTS:
: Running in /home/pi host 'jrr5' on Tue Apr 28 10:06:12 EEST 2026
: 'pi' runs '/home/pi/jrr/bin/jrr.sh stop' on 'jrr5:/home/pi'
: do_stop - send SIGTERM to JRR_PID=10276

Check that it is stopped
#+call: jrr-status[:dir /ssh:jrr5: ]()

#+RESULTS:
: Running in /home/pi host 'jrr5' on Tue Apr 28 10:26:12 EEST 2026
: 'pi' runs '/home/pi/jrr/bin/jrr.sh status' on 'jrr5:/home/pi'
: jrr.sh: status=1/
: jrr.py: status=1/
: ffmpeg: status=1/

Run ~jrr.sh debug~ to enable screenshot actions:
- long button 2 in radio stream
- SYSREQ/PRINT SCREEN on config screens  
#+call: jrr-debug()

#+RESULTS:

Copy screen snapthos to ~pics-keep/screenshots/~
#+BEGIN_SRC bash :eval no-export :results output
echo "Running in $(pwd) host '$(hostname)' on $(date)"
rsync -a --update --verbose --checksum jrr5:tmp/jrr-*png pics-keep/screenshots/
#+END_SRC

#+RESULTS:
: Running in /home/jj/work/jrr host 'Leo' on ti 28.4.2026 12.55.17 +0300
: receiving incremental file list
: jrr-03-channel-origin-channel-setup.png
: 
: sent 43 bytes  received 19.270 bytes  38.626,00 bytes/sec
: total size is 350.908  speedup is 18,17

[[file:pics-keep/screenshots]]

* Burn firmware on SD_DEV 
:PROPERTIES:
:header-args+: :var  SD_DEV="/dev/sda"
:header-args+: :var  FIRMWARE_DIR="/home/jj/work/jrr/firmware"
:END:

** +SSH-copy of live firmware from ~$JRR+ - did not work
:PROPERTIES:
:header-args+: :var  JRR="pi@jrr5.local"
:header-args+: :var  JRR_DISK="mmcblk0"
:END:

*** Copy firmware over ssh from ~JRR/dev/JRR_DISK~ to ~firmware/$JRR-RELEASE.img.gz~

Ensure that JRR_DIR is correct
#+BEGIN_SRC bash :eval no-export :results output
  echo "Running in $(pwd) host '$(hostname)' on $(date)"
  echo JRR_DISK=$JRR_DISK
  ssh $JRR lsblk
#+END_SRC

#+RESULTS:
: Running in /home/jj/work/jrr host 'Leo' on la 16.5.2026 11.44.06 +0300
: JRR_DISK=mmcblk0
: NAME        MAJ:MIN RM  SIZE RO TYPE MOUNTPOINTS
: mmcblk0     179:0    0 14.8G  0 disk 
: |-mmcblk0p1 179:1    0  512M  0 part /boot/firmware
: `-mmcblk0p2 179:2    0 14.3G  0 part /

Pull dev

#+BEGIN_SRC bash :eval no-export :results output
  echo "Running in $(pwd) host '$(hostname)' on $(date)"
  ssh $JRR "sudo dd if=/dev/$JRR_DISK bs=4M status=none | gzip -1" > firmware/$JRR-$RELEASE.img.gz  
#+END_SRC

#+RESULTS:
: Running in /home/jj/work/jrr host 'Leo' on la 16.5.2026 11.44.24 +0300

Create ~SHA_CHECK~ for check sum
#+BEGIN_SRC bash :eval no-export :results output
  echo "Running in $(pwd) host '$(hostname)' on $(date)"
  SHA_CHECK=firmware/$JRR-$RELEASE.img.gz.sha256
  ([[ -f  $SHA_CHECK ]] && echo SHA_CHECK=$SHA_CHECK exists - quit ; exit)  || sha256sum firmware/$JRR-$RELEASE.img.gz  | tee $SHA_CHECK
#+END_SRC

#+RESULTS:
: Running in /home/jj/work/jrr host 'Leo' on su 17.5.2026 20.10.40 +0300
: SHA_CHECK=firmware/pi@jrr5.local-2.img.gz.sha256 exists - quit

#+BEGIN_SRC bash :eval no-export :results output
  SHA_CHECK=firmware/$JRR-$RELEASE.img.gz.sha256
  echo "Checking sha256sum in SHA_CHECK=$SHA_CHECK in $(pwd) host '$(hostname)' on $(date)"
  sha256sum --check $SHA_CHECK
#+END_SRC

#+RESULTS:
: Checking sha256sum in SHA_CHECK=firmware/pi@jrr5.local-2.img.gz.sha256 in /home/jj/work/jrr host 'Leo' on su 17.5.2026 20.12.10 +0300
: firmware/pi@jrr5.local-2.img.gz: OK

** Burn ~firmware/JRR-$FIRMAWARE_RELEASE.img.gz~ on ~SD_DEV~

Ensure correct SD_DEV. Check:
- RM=1 → removable device
- TRAN=usb → often SD card readers appear as USB
- Size matches your SD card

#+BEGIN_SRC bash :eval no-export :results output
  echo "Running in $(pwd) host '$(hostname)' on $(date)"
  echo SD_DEV=$SD_DEV
  [[ -z "$SD_DEV" ]] && echo "Missing parameter SD_DEV" && exit 1
  lsblk  -o NAME,SIZE,TRAN,RM,MOUNTPOINT $SD_DEV
#+END_SRC

#+RESULTS:
: Running in /home/jj/work/jrr host 'Leo' on pe 17.7.2026 13.46.43 +0300
: SD_DEV=/dev/sda
: NAME    SIZE TRAN RM MOUNTPOINT
: sda      30G usb   1 
: ├─sda1  512M       1 /media/jj/bootfs
: ├─sda2 22,5G       1 /media/jj/rootfs
: └─sda3    2G       1 /media/jj/home2

#+BEGIN_SRC bash :eval no-export :results output  :dir /sudo::
echo "Running in $(pwd) host '$(hostname)' on $(date)"
echo "Running in $(pwd) host '$(hostname)' on $(date)"
dmesg | tail -20
#+END_SRC

#+RESULTS:
#+begin_example
Running in /root host 'Leo' on Wed Jul 15 02:47:31 PM EEST 2026
Running in /root host 'Leo' on Wed Jul 15 02:47:31 PM EEST 2026
[99176.233670] sd 0:0:0:0: Attached scsi generic sg0 type 0
[99176.448592] sd 0:0:0:0: [sda] 62945280 512-byte logical blocks: (32.2 GB/30.0 GiB)
[99176.449251] sd 0:0:0:0: [sda] Write Protect is off
[99176.449259] sd 0:0:0:0: [sda] Mode Sense: 03 00 00 00
[99176.449582] sd 0:0:0:0: [sda] No Caching mode page found
[99176.449585] sd 0:0:0:0: [sda] Assuming drive cache: write through
[99176.473655]  sda: sda1
[99176.473790] sd 0:0:0:0: [sda] Attached SCSI removable disk
[99176.753814] audit: type=1107 audit(1784115992.037:578): pid=2941 uid=101 auid=4294967295 ses=4294967295 subj=unconfined msg='apparmor="DENIED" operation="dbus_signal"  bus="system" path="/org/freedesktop/login1" interface="org.freedesktop.DBus.Properties" member="PropertiesChanged" name=":1.10" mask="receive" pid=6636 label="snap.thunderbird.thunderbird" peer_pid=2986 peer_label="unconfined"
                exe="/usr/bin/dbus-daemon" sauid=101 hostname=? addr=? terminal=?'
[99176.756098] FAT-fs (sda1): Volume was not properly unmounted. Some data may be corrupt. Please run fsck.
[99176.758371] audit: type=1107 audit(1784115992.042:579): pid=2941 uid=101 auid=4294967295 ses=4294967295 subj=unconfined msg='apparmor="DENIED" operation="dbus_signal"  bus="system" path="/org/freedesktop/login1" interface="org.freedesktop.DBus.Properties" member="PropertiesChanged" name=":1.10" mask="receive" pid=6636 label="snap.thunderbird.thunderbird" peer_pid=2986 peer_label="unconfined"
                exe="/usr/bin/dbus-daemon" sauid=101 hostname=? addr=? terminal=?'
[99176.882920] [UFW BLOCK] IN=wlp0s20f3 OUT= MAC= SRC=fe80:0000:0000:0000:7170:b81a:4bcd:98a9 DST=ff02:0000:0000:0000:0000:0000:0000:000c LEN=655 TC=0 HOPLIMIT=1 FLOWLBL=89360 PROTO=UDP SPT=50675 DPT=3702 LEN=615 
[99176.883289] [UFW BLOCK] IN=enx387c760a4be8 OUT= MAC= SRC=fe80:0000:0000:0000:8269:1bdd:d566:1142 DST=ff02:0000:0000:0000:0000:0000:0000:000c LEN=655 TC=0 HOPLIMIT=1 FLOWLBL=55480 PROTO=UDP SPT=60722 DPT=3702 LEN=615 
[99176.883726] [UFW BLOCK] IN=enx387c760a4be8 OUT= MAC=33:33:00:00:00:0c:04:f0:ee:3e:90:4f:86:dd SRC=fe80:0000:0000:0000:7170:b81a:4bcd:98a9 DST=ff02:0000:0000:0000:0000:0000:0000:000c LEN=655 TC=0 HOPLIMIT=1 FLOWLBL=89360 PROTO=UDP SPT=50675 DPT=3702 LEN=615 
[99176.910055] [UFW BLOCK] IN=wlp0s20f3 OUT= MAC=33:33:00:00:00:0c:38:7c:76:0a:4b:e8:86:dd SRC=fe80:0000:0000:0000:8269:1bdd:d566:1142 DST=ff02:0000:0000:0000:0000:0000:0000:000c LEN=655 TC=0 HOPLIMIT=1 FLOWLBL=55480 PROTO=UDP SPT=60722 DPT=3702 LEN=615 
[99188.580188] [UFW BLOCK] IN=enx387c760a4be8 OUT= MAC=01:00:5e:00:00:01:10:7c:61:80:77:a0:08:00 SRC=192.168.1.1 DST=224.0.0.1 LEN=36 TOS=0x00 PREC=0x00 TTL=1 ID=41662 DF PROTO=2 
[99208.581199] [UFW BLOCK] IN=enx387c760a4be8 OUT= MAC=01:00:5e:00:00:01:10:7c:61:80:77:a0:08:00 SRC=192.168.1.1 DST=224.0.0.1 LEN=36 TOS=0x00 PREC=0x00 TTL=1 ID=50067 DF PROTO=2 
[99228.582408] [UFW BLOCK] IN=enx387c760a4be8 OUT= MAC=01:00:5e:00:00:01:10:7c:61:80:77:a0:08:00 SRC=192.168.1.1 DST=224.0.0.1 LEN=36 TOS=0x00 PREC=0x00 TTL=1 ID=59335 DF PROTO=2 
#+end_example

Check if mounted

#+BEGIN_SRC bash :eval no-export :results output
  echo "Running in $(pwd) host '$(hostname)' on $(date)"
  mount | grep $SD_DEV
#+END_SRC

#+RESULTS:
: Running in /home/jj/work/jrr host 'Leo' on pe 17.7.2026 13.46.50 +0300
: /dev/sda3 on /media/jj/home2 type ext4 (rw,nosuid,nodev,relatime,errors=remount-ro,uhelper=udisks2)
: /dev/sda1 on /media/jj/bootfs type vfat (rw,nosuid,nodev,relatime,uid=1000,gid=1000,fmask=0022,dmask=0022,codepage=437,iocharset=iso8859-1,shortname=mixed,showexec,utf8,flush,errors=remount-ro,uhelper=udisks2)
: /dev/sda2 on /media/jj/rootfs type ext4 (rw,nosuid,nodev,relatime,errors=remount-ro,uhelper=udisks2)

: Running in /home/jj/work/jrr host 'Leo' on su 17.5.2026 20.20.31 +0300
: /dev/sda1 on /media/jj/3F4A-4CE6 type vfat (rw,nosuid,nodev,relatime,uid=1000,gid=1000,fmask=0022,dmask=0022,codepage=437,iocharset=iso8859-1,shortname=mixed,showexec,utf8,flush,errors=remount-ro,uhelper=udisks2)

Unmount ~SD_DEV~

#+BEGIN_SRC bash :eval no-export :results output  :dir /sudo::
echo "Running in $(pwd) host '$(hostname)' on $(date)"
sudo umount ${SD_DEV}1
#+END_SRC

#+RESULTS:
: Running in /root host 'Leo' on Fri Jul 17 01:46:57 PM EEST 2026

Check that SD_DEV points to usb device with RM=1 mount 
#+call: lsblk-conf()

#+RESULTS:
: Running in /home/jj/work/jrr host 'Leo' on pe 17.7.2026 13.47.04 +0300
: SD_DEV=/dev/sda
: NAME    SIZE TRAN RM MOUNTPOINT
: sda      30G usb   1 
: ├─sda1  512M       1 
: ├─sda2 22,5G       1 /media/jj/rootfs
: └─sda3    2G       1 /media/jj/home2

Ensure that ISO_FILE is there
#+BEGIN_SRC bash :eval no-export :results output
echo "Running in $(pwd) for user '$(whoami)' on host '$(hostname)' on $(date)"
ISO_FILE_GZ=$FIRMWARE_DIR/JRR-$FIRMWARE_RELEASE.img.gz
echo ISO_FILE_GZ=$ISO_FILE_GZ
ls -ltr $ISO_FILE_GZ
[[ ! -f $ISO_FILE_GZ ]] && echo "No such file ISO_FILE_GZ=$ISO_FILE_GZ - quit" && exit 1
true
#+END_SRC

#+RESULTS:
: Running in /home/jj/work/jrr for user 'jj' on host 'Leo' on pe 17.7.2026 13.49.17 +0300
: ISO_FILE_GZ=/home/jj/work/jrr/firmware/JRR-4.img.gz
: -rw-rw-r-- 1 jj jj 1648507765 heinä  17 13:20 /home/jj/work/jrr/firmware/JRR-4.img.gz

Validate ~SHA_CHECK~
#+BEGIN_SRC bash :eval no-export :results output
ISO_IMG_GZ=$FIRMWARE_DIR/JRR-$FIRMWARE_RELEASE.img.gz
[[ ! -f $ISO_IMG_GZ ]] && echo "No such file ISO_IMG_GZ=$ISO_IMG_GZ" && exit 1
SHA_CHECK=$ISO_IMG_GZ.sha256
[[ ! -f $SHA_CHECK ]] && echo "No such file SHA_CHECK=$SHA_CHECK" && exit 1
echo "Checking sha256sum in SHA_CHECK=$SHA_CHECK in $(pwd) host '$(hostname)' on $(date)"
sha256sum --check $SHA_CHECK 2>&1
#+END_SRC

#+RESULTS:
: Checking sha256sum in SHA_CHECK=/home/jj/work/jrr/firmware/JRR-4.img.gz.sha256 in /home/jj/work/jrr host 'Leo' on pe 17.7.2026 13.49.54 +0300
: /home/jj/work/jrr/firmware/JRR-4.img.gz: OK

*Warning SD_DISK MUST point to USB disk*
#+BEGIN_SRC bash :eval no-export :results output  :dir /sudo::
echo "Running in $(pwd) host '$(hostname)' on $(date)"
# [[ -z "$JRR" ]] && echo "Missing parameter JRR" && exit 1
[[ -z "$FIRMWARE_RELEASE" ]] && echo "Missing parameter FIRMWARE_RELEASE" && exit 1
ISO_FILE_GZ=$FIRMWARE_DIR/JRR-$FIRMWARE_RELEASE.img.gz
[[ ! -f "$ISO_FILE_GZ" ]] && echo "Missing file ISO_FILE_GZ=$ISO_FILE_GZ" && exit 1
echo ISO_FILE_GZ=$ISO_FILE_GZ
ls -ltr $ISO_FILE_GZ
echo SD_DEV=$SD_DEV
echo "gzip -dc $ISO_FILE_GZ | sudo dd of=$SD_DEV bs=4M status=progress oflag=sync"
#+END_SRC

#+RESULTS:
: Running in /root host 'Leo' on Fri Jul 17 01:49:59 PM EEST 2026
: ISO_FILE_GZ=/home/jj/work/jrr/firmware/JRR-4.img.gz
: -rw-rw-r-- 1 jj jj 1648507765 Jul 17 13:20 /home/jj/work/jrr/firmware/JRR-4.img.gz
: SD_DEV=/dev/sda
: gzip -dc /home/jj/work/jrr/firmware/JRR-4.img.gz | sudo dd of=/dev/sda bs=4M status=progress oflag=sync

** Assigning  HOSTNAME to ~jrr5x~
:PROPERTIES:
:header-args+: :var HOSTNAME="jrr5x1"
:END:

Assigning  HOSTNAME to jrr5x
#+BEGIN_SRC bash :eval no-export :results output
echo "Running in $(pwd) for user '$(whoami)' on host '$(hostname)' on $(date)"
echo "HOSTNAME=$HOSTNAME"
#+END_SRC

#+RESULTS:
: Running in /home/jj/work/jrr for user 'jj' on host 'Leo' on ke 22.7.2026 10.10.44 +0300
: HOSTNAME=jrr5x1

Hostname intially

#+BEGIN_SRC bash :eval no-export :results output :dir /ssh:pi@jrr5x.local:
echo "Running in $(pwd) for user '$(whoami)' on host '$(hostname)' on $(date)"
hostname
#+END_SRC

#+RESULTS:
: Running in /home/pi for user 'pi' on host 'jrr5x' on Wed Jul 22 09:51:47 EEST 2026
: jrr5x

#+BEGIN_SRC bash :eval no-export :results output :dir /ssh:pi@jrr5x.local: 
echo "Running in $(pwd) for user '$(whoami)' on host '$(hostname)' on $(date)"
echo HOSTNAME=$HOSTNAME
sudo raspi-config nonint do_hostname $HOSTNAME
#+END_SRC

#+RESULTS:
: Running in /home/pi for user 'pi' on host 'jrr5x' on Wed Jul 22 09:58:44 EEST 2026
: HOSTNAME=jrr5x1

Reboot
#+call: reboot[:dir /ssh:jrr5x:]()

#+RESULTS:
: Reboot for user 'jj' in /home/jj/work/jrr host 'Leo' on ke 22.7.2026 10.00.57 +0300

Hostname after change
#+BEGIN_SRC bash :eval no-export :results output :dir /ssh:pi@jrr5x.local:
echo "Running in $(pwd) for user '$(whoami)' on host '$(hostname)' on $(date)"
hostname
#+END_SRC

#+RESULTS:
: Running in /home/pi for user 'pi' on host 'jrr5x1' on Wed Jul 22 09:59:08 EEST 2026
: jrr5x1

#+call: hosti[:dir /ssh:pi@jrr5x1.local: ]()

#+RESULTS:
: jrr5x1 on Wed Jul 22 10:09:49 EEST 2026

* Issues

** DONE JRR_DEV-010: Fix factory reset

- bin/jrr.sh (read-gpio): debug action added
   - (do_stop/stop): use do_kill in every case
   - (pull_up_gpio): added
   - (is_factory_reset): added
   - (daemon action):  fixed factory reset

** DONE JRR_DEV-009: Browse app-versions

- firmware_available_versions.choose_applicable: Using FIRMWARE_VERSION_AFTER
- FIRMWARE_VERSION_AFTER: added
- jrr-rpi.org (src-init): symlink bin -> src.bin
- src/jrr_streamer.sh (pending): src.next includes also bin directory
  
** DONE JRR_DEV-008: Volume gain limit

   File ~/home/jj/work/jrr/src/jrr_streamer.sh~  had GAIN=1.5  is now GAIN=0.75.

** DONE JRR-DEV-007: Firmware version on screen

	- jrr-rpi.org (Add firmare info to rpi image (as jrr5_user)): 'firmware_release.txt' not overriden
	- src/jrr_radio.py (ctrl_act_update_status): pass firmware version screen update
	- src/screen_coro.py (_screen_action): Mangle jrr_version && firmware_version on screen
	- src/jrr_radio.py (ControllerState.restore_firware_version): added
	- src/messages.py (MsgClockUpdate): added firmware_version

** DONE JRR-DEV-006: Factory reset

- [X] bin/jrr.sh
- [X] Documentation

** DONE JRR-DEV-005: Support screen snapshots

- added option OPT_ALLOW_SCREENSHOTS

** DONE JRR-DEV-004: Support chirp streams

- [-] Chirp stream
  - [X] Added ~src/jrr_streamer.sh --end-freq 20000 --duration 10 chirp~
    - [X] Renamed src/jrr_streamer.sh --end-freq 20000 --duration 10 chirp-gen
  - [X] Differentiate chirp stream from network stream

** DONE JRR-DEV-003: Configurable TFT orientation

- TFT1 needs Origin = Origin.UPPER_LEFT
- TFT2 needs Origin =  Origin.LOWER_RIGHT

in [[file:src/Python_ILI9486/ILI9486.py]]  

#+begin_example
def __init__(self, spi: SpiDev, dc: int, rst: int = None, *, origin: Origin = Origin.LOWER_RIGHT,):
   # def __init__(self, spi: SpiDev, dc: int, rst: int = None, *, origin: Origin = Origin.UPPER_LEFT):
#+end_example

Added [[file:src/screen_coro.py]]

    LOWER_RIGHT = 0xE8
    UPPER_LEFT = 0x28 (--> change)

#+begin_example
    elif is_message_type(msg, TOPICS.SCREEN_MESSAGES.REORIGIN):
        msg_reorigin = cast(MsgScreenReorigin, msg)
#+end_example

** DONE JRR-DEV-002: Expect volume knob open before shutdown handler init

- Volume knob may be initially turned off (GPIO True). Wait GPPIO
  False (Volumen knob turned on) before inialitizing shutdown gpio
  handler.
  
** DONE JRR-DEV-001: Alsa volume limit
:PROPERTIES:
:header-args+:  :dir  /ssh:jrr5:
:END:

#+BEGIN_SRC bash :eval no-export :results output 
echo "Running in $(pwd) host '$(hostname)' on $(date)"
amixer -c 2 scontents
#+END_SRC

#+RESULTS:
: Running in /home/pi host 'jrr5' on Tue Apr 14 12:33:26 EEST 2026
: Simple mixer control 'Headphone',0
:   Capabilities: pvolume pswitch pswitch-joined
:   Playback channels: Front Left - Front Right
:   Limits: Playback 0 - 175
:   Mono:
:   Front Left: Playback 175 [100%] [0.00dB] [on]
:   Front Right: Playback 175 [100%] [0.00dB] [on]

Fixed:
#+begin_example
amixer -c 2 sset Headphone 100%
#+end_example

To map device name to  device number

#+BEGIN_SRC bash :eval no-export :results output
echo "Running in $(pwd) host '$(hostname)' on $(date)"
aplay -l
#+END_SRC

#+RESULTS:
#+begin_example
Running in /home/pi host 'jrr5' on Tue Apr 14 12:38:27 EEST 2026
,**** List of PLAYBACK Hardware Devices ****
card 0: Headphones [bcm2835 Headphones], device 0: bcm2835 Headphones [bcm2835 Headphones]
  Subdevices: 8/8
  Subdevice #0: subdevice #0
  Subdevice #1: subdevice #1
  Subdevice #2: subdevice #2
  Subdevice #3: subdevice #3
  Subdevice #4: subdevice #4
  Subdevice #5: subdevice #5
  Subdevice #6: subdevice #6
  Subdevice #7: subdevice #7
card 1: vc4hdmi [vc4-hdmi], device 0: MAI PCM i2s-hifi-0 [MAI PCM i2s-hifi-0]
  Subdevices: 1/1
  Subdevice #0: subdevice #0
card 2: Audio [Realtek USB2.0 Audio], device 0: USB Audio [USB Audio]
  Subdevices: 0/1
  Subdevice #0: subdevice #0
#+end_example

#+BEGIN_SRC bash :eval no-export :results output
echo "Running in $(pwd) host '$(hostname)' on $(date)"
cat /proc/asound/cards
#+END_SRC

#+RESULTS:
: Running in /home/pi host 'jrr5' on Tue Apr 14 12:39:10 EEST 2026
:  0 [Headphones     ]: bcm2835_headpho - bcm2835 Headphones
:                       bcm2835 Headphones
:  1 [vc4hdmi        ]: vc4-hdmi - vc4-hdmi
:                       vc4-hdmi
:  2 [Audio          ]: USB-Audio - Realtek USB2.0 Audio
:                       TTGK Realtek USB2.0 Audio at usb-3f980000.usb-1.5, high speed

#+BEGIN_SRC bash :eval no-export :results output
echo "Running in $(pwd) host '$(hostname)' on $(date)"
cat /proc/asound/Audio/id
#+END_SRC

#+RESULTS:
: Running in /home/pi host 'jrr5' on Tue Apr 14 12:46:32 EEST 2026
: Audio

#+BEGIN_SRC bash :eval no-export :results output
echo "Running in $(pwd) host '$(hostname)' on $(date)"
# grep -n "USB" /proc/asound/cards
# grep -E "\[ *Audio *\]" /proc/asound/cards 
awk '/\[ *Audio *\]/ {print $1}' /proc/asound/cards
#+END_SRC

#+RESULTS:
: Running in /home/pi host 'jrr5' on Tue Apr 14 12:53:15 EEST 2026
: 2

#+BEGIN_SRC bash :eval no-export :results output
echo "Running in $(pwd) host '$(hostname)' on $(date)"
cardnum() {
  awk '/\[ *Audio *\]/ {print $1}' /proc/asound/cards
}

echo cardnum=$(cardnum) 
amixer -c $(cardnum) scontents

#+END_SRC

#+RESULTS:
: Running in /home/pi host 'jrr5' on Tue Apr 14 12:53:44 EEST 2026
: cardnum=2
: Simple mixer control 'Headphone',0
:   Capabilities: pvolume pswitch pswitch-joined
:   Playback channels: Front Left - Front Right
:   Limits: Playback 0 - 175
:   Mono:

:   Front Left: Playback 175 [100%] [0.00dB] [on]
:   Front Right: Playback 175 [100%] [0.00dB] [on]

#+BEGIN_SRC bash :eval no-export :results output
echo "Running in $(pwd) host '$(hostname)' on $(date)"
cardnum() {
  awk '/\[ *Audio *\]/ {print $1}' /proc/asound/cards
}
echo cardnum=$(cardnum)
amixer -c $(cardnum) sset Headphone 100%
#+END_SRC

#+RESULTS:
: Running in /home/pi host 'jrr5' on Tue Apr 14 13:00:07 EEST 2026
: cardnum=2
: Simple mixer control 'Headphone',0
:   Capabilities: pvolume pswitch pswitch-joined
:   Playback channels: Front Left - Front Right
:   Limits: Playback 0 - 175
:   Mono:
:   Front Left: Playback 175 [100%] [0.00dB] [on]
:   Front Right: Playback 175 [100%] [0.00dB] [on]

#+BEGIN_SRC bash :eval no-export :results output
echo "Running in $(pwd) host '$(hostname)' on $(date)"
amixer -c Audio scontents

#+END_SRC

#+RESULTS:
: Running in /home/pi host 'jrr5' on Tue Apr 14 12:59:41 EEST 2026
: Simple mixer control 'Headphone',0
:   Capabilities: pvolume pswitch pswitch-joined
:   Playback channels: Front Left - Front Right
:   Limits: Playback 0 - 175
:   Mono:
:   Front Left: Playback 175 [100%] [0.00dB] [on]
:   Front Right: Playback 175 [100%] [0.00dB] [on]

* Admin                                                            :noexport:
** Os admin
*** ~reboot~: Reboot now

#+name: reboot
#+BEGIN_SRC bash :eval no-export :results output
echo "Reboot for user '$(whoami)' in $(pwd) host '$(hostname)' on $(date)"
sudo reboot
#+END_SRC

#+RESULTS: reboot
: Reboot for user 'pi' in /home/pi host 'jrr5x' on Thu Jul 16 15:06:30 EEST 2026
: sudo reboot

*** ~hosti~: Hostname
Installation hostname

#+name: hosti
#+BEGIN_SRC bash :eval no-export :results output :exports both
echo $(hostname) on $(date)
#+END_SRC

#+RESULTS: hosti
: jrr5 on Tue Nov 19 13:41:36 EET 2024

#+RESULTS:
: sorsa

*** ~mem~: free memory

#+name: mem
#+BEGIN_SRC bash :eval no-export :results output
echo memory on $(hostname) on $(date)
free -h
#+END_SRC

#+RESULTS: mem
: memory on eero on ma 3.6.2024 23.00.25 +0300
:                total        used        free      shared  buff/cache   available
: Mem:            31Gi        23Gi       1,7Gi       3,2Gi       6,1Gi       4,1Gi
: Swap:          2,0Gi          0B       2,0Gi

#+RESULTS:
: sorsa
:                total        used        free      shared  buff/cache   available
: Mem:           909Mi       257Mi       139Mi        10Mi       512Mi       583Mi
: Swap:           99Mi          0B        99Mi

The RAM information of the Raspberry Pi system is also stored in the
memory information of a processor and you can retrieve this
information through the following command:
#+BEGIN_SRC bash :eval no-export :results output
cat /proc/meminfo
#+END_SRC

#+RESULTS:
#+begin_example
MemTotal:         931460 kB
MemFree:          142500 kB
MemAvailable:     597760 kB
Buffers:           23376 kB
Cached:           473824 kB
SwapCached:            0 kB
Active:            82968 kB
Inactive:         601576 kB
Active(anon):        944 kB
Inactive(anon):   197280 kB
Active(file):      82024 kB
Inactive(file):   404296 kB
Unevictable:          16 kB
Mlocked:              16 kB
SwapTotal:        102396 kB
SwapFree:         102396 kB
Dirty:                40 kB
Writeback:             0 kB
AnonPages:        187568 kB
Mapped:           136172 kB
Shmem:             10872 kB
KReclaimable:      27992 kB
Slab:              53608 kB
SReclaimable:      27992 kB
SUnreclaim:        25616 kB
KernelStack:        3852 kB
PageTables:         5636 kB
NFS_Unstable:          0 kB
Bounce:                0 kB
WritebackTmp:          0 kB
CommitLimit:      568124 kB
Committed_AS:    1234060 kB
VmallocTotal:   259653632 kB
VmallocUsed:       10988 kB
VmallocChunk:          0 kB
Percpu:              688 kB
CmaTotal:         262144 kB
CmaFree:          101604 kB
#+end_example

*** ~architecture~: Architecture

#+name: architecture
#+BEGIN_SRC bash :eval no-export :results output
uname -m
#+END_SRC

#+RESULTS: architecture
: aarch64

#+RESULTS:
: aarch64

*** ~top~:

#+name: top
#+BEGIN_SRC bash :eval no-export :results output
  echo "Top processes in host '$(hostname)' on $(date)"
  top -bn1 | head -20
#+END_SRC

#+RESULTS: top
#+begin_example
Top processes in host 'sorsa' on Wed Jun  5 02:30:54 PM EEST 2024
top - 14:30:54 up  6:15,  7 users,  load average: 0.33, 0.14, 0.10
Tasks: 226 total,   1 running, 225 sleeping,   0 stopped,   0 zombie
%Cpu(s): 11.1 us, 22.2 sy,  0.0 ni, 66.7 id,  0.0 wa,  0.0 hi,  0.0 si,  0.0 st 
MiB Mem :   7809.0 total,   6130.4 free,    500.3 used,   1314.3 buff/cache     
MiB Swap:    200.0 total,    200.0 free,      0.0 used.   7308.7 avail Mem 

    PID USER      PR  NI    VIRT    RES    SHR S  %CPU  %MEM     TIME+ COMMAND
  30759 pi        20   0   14240   4864   2816 R  11.8   0.1   0:00.04 top
      1 root      20   0  170060  13316   8760 S   0.0   0.2   0:20.17 systemd
      2 root      20   0       0      0      0 S   0.0   0.0   0:00.04 kthreadd
      3 root      20   0       0      0      0 S   0.0   0.0   0:00.00 pool_wo+
      4 root       0 -20       0      0      0 I   0.0   0.0   0:00.00 kworker+
      5 root       0 -20       0      0      0 I   0.0   0.0   0:00.00 kworker+
      6 root       0 -20       0      0      0 I   0.0   0.0   0:00.00 kworker+
      7 root       0 -20       0      0      0 I   0.0   0.0   0:00.00 kworker+
      9 root       0 -20       0      0      0 I   0.0   0.0   0:00.00 kworker+
     12 root       0 -20       0      0      0 I   0.0   0.0   0:00.00 kworker+
     13 root      20   0       0      0      0 I   0.0   0.0   0:00.00 rcu_tas+
     14 root      20   0       0      0      0 I   0.0   0.0   0:00.00 rcu_tas+
     15 root      20   0       0      0      0 I   0.0   0.0   0:00.00 rcu_tas+
#+end_example

*** ~cpu-info~: CPU info

#+name: cpu-info
#+BEGIN_SRC bash :eval no-export :results output :exports both
cat /proc/cpuinfo
#+END_SRC

#+RESULTS: cpu-info
#+begin_example
processor	: 0
BogoMIPS	: 108.00
Features	: fp asimd evtstrm crc32 cpuid
CPU implementer	: 0x41
CPU architecture: 8
CPU variant	: 0x0
CPU part	: 0xd08
CPU revision	: 3

processor	: 1
BogoMIPS	: 108.00
Features	: fp asimd evtstrm crc32 cpuid
CPU implementer	: 0x41
CPU architecture: 8
CPU variant	: 0x0
CPU part	: 0xd08
CPU revision	: 3

processor	: 2
BogoMIPS	: 108.00
Features	: fp asimd evtstrm crc32 cpuid
CPU implementer	: 0x41
CPU architecture: 8
CPU variant	: 0x0
CPU part	: 0xd08
CPU revision	: 3

processor	: 3
BogoMIPS	: 108.00
Features	: fp asimd evtstrm crc32 cpuid
CPU implementer	: 0x41
CPU architecture: 8
CPU variant	: 0x0
CPU part	: 0xd08
CPU revision	: 3

Revision	: d03115
Serial		: 100000006ca06014
Model		: Raspberry Pi 4 Model B Rev 1.5
#+end_example

#+RESULTS:
#+begin_example
processor	: 0
BogoMIPS	: 38.40
Features	: fp asimd evtstrm crc32 cpuid
CPU implementer	: 0x41
CPU architecture: 8
CPU variant	: 0x0
CPU part	: 0xd03
CPU revision	: 4

processor	: 1
BogoMIPS	: 38.40
Features	: fp asimd evtstrm crc32 cpuid
CPU implementer	: 0x41
CPU architecture: 8
CPU variant	: 0x0
CPU part	: 0xd03
CPU revision	: 4

processor	: 2
BogoMIPS	: 38.40
Features	: fp asimd evtstrm crc32 cpuid
CPU implementer	: 0x41
CPU architecture: 8
CPU variant	: 0x0
CPU part	: 0xd03
CPU revision	: 4

processor	: 3
BogoMIPS	: 38.40
Features	: fp asimd evtstrm crc32 cpuid
CPU implementer	: 0x41
CPU architecture: 8
CPU variant	: 0x0
CPU part	: 0xd03
CPU revision	: 4

Hardware	: BCM2835
Revision	: a020d3
Serial		: 0000000021bed90e
Model		: Raspberry Pi 3 Model B Plus Rev 1.3
#+end_example

*** ~kernel-version~: Kernel version

#+name: kernel-version
#+BEGIN_SRC bash :eval no-export :results output :exports both
uname -a
#+END_SRC

#+RESULTS: kernel-version
: Linux sorsa 6.6.20+rpt-rpi-v8 #1 SMP PREEMPT Debian 1:6.6.20-1+rpt1 (2024-03-07) aarch64 GNU/Linux

: Linux sorsa 5.15.84-v8+ #1613 SMP PREEMPT Thu Jan 5 12:03:08 GMT 2023 aarch64 GNU/Linux

*** ~os-version~: Operating system release

#+name: os-version
#+BEGIN_SRC bash :eval no-export :results output :exports both
cat /etc/os-release
#+END_SRC

#+RESULTS: os-version
: PRETTY_NAME="Debian GNU/Linux 12 (bookworm)"
: NAME="Debian GNU/Linux"
: VERSION_ID="12"
: VERSION="12 (bookworm)"
: VERSION_CODENAME=bookworm
: ID=debian
: HOME_URL="https://www.debian.org/"
: SUPPORT_URL="https://www.debian.org/support"
: BUG_REPORT_URL="https://bugs.debian.org/"

#+RESULTS:
: PRETTY_NAME="Debian GNU/Linux 12 (bookworm)"
: NAME="Debian GNU/Linux"
: VERSION_ID="12"
: VERSION="12 (bookworm)"
: VERSION_CODENAME=bookworm
: ID=debian
: HOME_URL="https://www.debian.org/"
: SUPPORT_URL="https://www.debian.org/support"
: BUG_REPORT_URL="https://bugs.debian.org/"

*** Forget wlan

#+BEGIN_SRC bash :eval no-export :results output
  echo "Show known wlan configs in host '$(hostname)' on $(date)"
  sudo cat /etc/wpa_supplicant/wpa_supplicant.conf
#+END_SRC

#+RESULTS:
: Show known wlan configs in host 'sorsa' on Wed Jun  5 09:07:56 PM EEST 2024
: ctrl_interface=DIR=/var/run/wpa_supplicant GROUP=netdev
: update_config=1

#+begin_example
wpa_supplicant.conf is not used with the now default Network Manager.

Left click on the network icon and select [Advance Options] then [Edit Connections]
Select the connection and click on [-].
-OR-
Use the command line tool:

sudo nmtui

#+end_example

*** ~raspi-info~

#+BEGIN_SRC bash :eval no-export :results output
echo $(hostname)
raspinfo
#+END_SRC

#+RESULTS:
#+begin_example
welleri
System Information
------------------

Raspberry Pi 4 Model B Rev 1.5
PRETTY_NAME="Debian GNU/Linux 11 (bullseye)"
NAME="Debian GNU/Linux"
VERSION_ID="11"
VERSION="11 (bullseye)"

Raspberry Pi reference 2023-05-03
Generated using pi-gen, https://github.com/RPi-Distro/pi-gen, 7c750947a959fb626a70c09fd17c65815df192ac, stage4

Linux welleri 6.1.21-v8+ #1642 SMP PREEMPT Mon Apr  3 17:24:16 BST 2023 aarch64 GNU/Linux
Revision	: c03115
Serial		: 1000000061bcfc69
Model		: Raspberry Pi 4 Model B Rev 1.5
Throttled flag  : throttled=0x0
Camera          : supported=0 detected=0, libcamera interfaces=0

Videocore information
---------------------

Mar 17 2023 10:50:39 
Copyright (c) 2012 Broadcom
version 82f3750a65fadae9a38077e3c2e217ad158c8d54 (clean) (release) (start)

alloc failures:     0
compactions:        0
legacy block fails: 0

Filesystem information
----------------------
Filesystem     1K-blocks    Used Available Use% Mounted on
/dev/root      244762244 8221472 224034748   4% /
devtmpfs         1677960       0   1677960   0% /dev
tmpfs            1942184       0   1942184   0% /dev/shm
tmpfs             776876    1328    775548   1% /run
tmpfs               5120       4      5116   1% /run/lock
/dev/sda1         258094   31155    226939  13% /boot
tmpfs             388436      20    388416   1% /run/user/1000

Filename				Type		Size		Used		Priority
/var/swap                               file		102396		0		-2

Package version information
---------------------------
raspberrypi-ui-mods:
  Installed: 1.20230127
raspberrypi-sys-mods:
  Installed: 20230510~bullseye
openbox:
  Installed: 3.6.1-9+rpt1+deb11u1
lxpanel:
  Installed: 0.10.1-2+rpt19
pcmanfm:
  Installed: 1.3.2-1+rpt9
rpd-plym-splash:
  Installed: 0.32

Networking Information
----------------------

br-af637c9bbb91: flags=4163<UP,BROADCAST,RUNNING,MULTICAST>  mtu 1500
        inet x.x.x.x  netmask x.x.x.x  broadcast x.x.x.x
        inet6 y::y.y.y.y  prefixlen 64  scopeid 0x20<link>
        ether m.m.m.m  txqueuelen 0  (Ethernet)
        RX packets 12  bytes 1203 (1.1 KiB)
        RX errors 0  dropped 0  overruns 0  frame 0
        TX packets 67  bytes 7523 (7.3 KiB)
        TX errors 0  dropped 0 overruns 0  carrier 0  collisions 0

docker0: flags=4099<UP,BROADCAST,MULTICAST>  mtu 1500
        inet x.x.x.x  netmask x.x.x.x  broadcast x.x.x.x
        ether m.m.m.m  txqueuelen 0  (Ethernet)
        RX packets 0  bytes 0 (0.0 B)
        RX errors 0  dropped 0  overruns 0  frame 0
        TX packets 0  bytes 0 (0.0 B)
        TX errors 0  dropped 0 overruns 0  carrier 0  collisions 0

eth0: flags=4163<UP,BROADCAST,RUNNING,MULTICAST>  mtu 1500
        inet x.x.x.x  netmask x.x.x.x  broadcast x.x.x.x
        inet6 y::y.y.y.y  prefixlen 64  scopeid 0x20<link>
        ether m.m.m.m  txqueuelen 1000  (Ethernet)
        RX packets 263  bytes 31027 (30.2 KiB)
        RX errors 0  dropped 0  overruns 0  frame 0
        TX packets 333  bytes 28821 (28.1 KiB)
        TX errors 0  dropped 0 overruns 0  carrier 0  collisions 0

lo: flags=73<UP,LOOPBACK,RUNNING>  mtu 65536
        inet x.x.x.x  netmask x.x.x.x
        inet6 ::1  prefixlen 128  scopeid 0x10<host>
        loop  txqueuelen 1000  (Local Loopback)
        RX packets 225  bytes 21757 (21.2 KiB)
        RX errors 0  dropped 0  overruns 0  frame 0
        TX packets 225  bytes 21757 (21.2 KiB)
        TX errors 0  dropped 0 overruns 0  carrier 0  collisions 0

vethf390115: flags=4163<UP,BROADCAST,RUNNING,MULTICAST>  mtu 1500
        inet x.x.x.x  netmask x.x.x.x  broadcast x.x.x.x
        inet6 y::y.y.y.y  prefixlen 64  scopeid 0x20<link>
        ether m.m.m.m  txqueuelen 0  (Ethernet)
        RX packets 12  bytes 1371 (1.3 KiB)
        RX errors 0  dropped 0  overruns 0  frame 0
        TX packets 211  bytes 40353 (39.4 KiB)
        TX errors 0  dropped 1 overruns 0  carrier 0  collisions 0

wlan0: flags=4163<UP,BROADCAST,RUNNING,MULTICAST>  mtu 1500
        inet x.x.x.x  netmask x.x.x.x  broadcast x.x.x.x
        inet6 y::y.y.y.y  prefixlen 64  scopeid 0x20<link>
        ether m.m.m.m  txqueuelen 1000  (Ethernet)
        RX packets 385366  bytes 30147400 (28.7 MiB)
        RX errors 0  dropped 0  overruns 0  frame 0
        TX packets 1470  bytes 236590 (231.0 KiB)
        TX errors 0  dropped 0 overruns 0  carrier 0  collisions 0

USB Information
---------------

/:  Bus 02.Port 1: Dev 1, Class=root_hub, Driver=xhci_hcd/4p, 5000M
    |__ Port 2: Dev 2, If 0, Class=Mass Storage, Driver=uas, 5000M
/:  Bus 01.Port 1: Dev 1, Class=root_hub, Driver=xhci_hcd/1p, 480M
    |__ Port 1: Dev 2, If 0, Class=Hub, Driver=hub/4p, 480M

Display Information
-------------------

Running (F)KMS and X

Screen 0: minimum 320 x 200, current 800 x 480, maximum 7680 x 7680
HDMI-1 disconnected (normal left inverted right x axis y axis)
	Identifier: 0x45
	Timestamp:  497711
	Subpixel:   unknown
	Clones:    
	CRTCs:      3
	Transform:  1.000000 0.000000 0.000000
	            0.000000 1.000000 0.000000
	            0.000000 0.000000 1.000000
	           filter: 
	Output format: Automatic 
		supported: Automatic, RGB, YCbCr 4:2:2, YCbCr 4:4:4
	Broadcast RGB: Automatic 
		supported: Automatic, Full, Limited 16:235
	max bpc: 8 
		range: (8, 12)
	bottom margin: 0 
		range: (0, 100)
	top margin: 0 
		range: (0, 100)
	right margin: 0 
		range: (0, 100)
	left margin: 0 
		range: (0, 100)
	Colorspace: Default 
		supported: Default, SMPTE_170M_YCC, BT709_YCC, XVYCC_601, XVYCC_709, SYCC_601, opYCC_601, opRGB, BT2020_CYCC, BT2020_RGB, BT2020_YCC, DCI-P3_RGB_D65, DCI-P3_RGB_Theater
	link-status: Good 
		supported: Good, Bad
	CONNECTOR_ID: 32 
		supported: 32
	non-desktop: 0 
		range: (0, 1)
HDMI-2 disconnected primary (normal left inverted right x axis y axis)
	Identifier: 0x46
	Timestamp:  497711
	Subpixel:   unknown
	Clones:    
	CRTCs:      4
	Transform:  1.000000 0.000000 0.000000
	            0.000000 1.000000 0.000000
	            0.000000 0.000000 1.000000
	           filter: 
	_MUTTER_PRESENTATION_OUTPUT: 0 
	Output format: Automatic 
		supported: Automatic, RGB, YCbCr 4:2:2, YCbCr 4:4:4
	Broadcast RGB: Automatic 
		supported: Automatic, Full, Limited 16:235
	max bpc: 8 
		range: (8, 12)
	bottom margin: 0 
		range: (0, 100)
	top margin: 0 
		range: (0, 100)
	right margin: 0 
		range: (0, 100)
	left margin: 0 
		range: (0, 100)
	Colorspace: Default 
		supported: Default, SMPTE_170M_YCC, BT709_YCC, XVYCC_601, XVYCC_709, SYCC_601, opYCC_601, opRGB, BT2020_CYCC, BT2020_RGB, BT2020_YCC, DCI-P3_RGB_D65, DCI-P3_RGB_Theater
	link-status: Good 
		supported: Good, Bad
	CONNECTOR_ID: 42 
		supported: 42
	non-desktop: 0 
		range: (0, 1)

Connector 0 (32) HDMI-A-1 (disconnected)
  Encoder 0 (31) TMDS
Connector 1 (42) HDMI-A-2 (disconnected)
  Encoder 1 (41) TMDS

HDMI0:             HDMI_HOTPLUG = 0x00000000
HDMI1:             HDMI_HOTPLUG = 0x00000000

/sys/kernel/debug/dri/1/state:
plane[47]: plane-0
	crtc=(null)
	fb=0
	crtc-pos=0x0+0+0
	src-pos=0.000000x0.000000+0.000000+0.000000
	rotation=1
	normalized-zpos=0
	color-encoding=ITU-R BT.709 YCbCr
	color-range=YCbCr limited range
plane[64]: plane-1
	crtc=(null)
	fb=0
	crtc-pos=0x0+0+0
	src-pos=0.000000x0.000000+0.000000+0.000000
	rotation=1
	normalized-zpos=0
	color-encoding=ITU-R BT.709 YCbCr
	color-range=YCbCr limited range
plane[75]: plane-2
	crtc=(null)
	fb=0
	crtc-pos=0x0+0+0
	src-pos=0.000000x0.000000+0.000000+0.000000
	rotation=1
	normalized-zpos=0
	color-encoding=ITU-R BT.709 YCbCr
	color-range=YCbCr limited range
plane[86]: plane-3
	crtc=(null)
	fb=0
	crtc-pos=0x0+0+0
	src-pos=0.000000x0.000000+0.000000+0.000000
	rotation=1
	normalized-zpos=0
	color-encoding=ITU-R BT.709 YCbCr
	color-range=YCbCr limited range
plane[97]: plane-4
	crtc=(null)
	fb=0
	crtc-pos=800x480+0+0
	src-pos=800.000000x480.000000+0.000000+0.000000
	rotation=1
	normalized-zpos=0
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
	normalized-zpos=11
	color-encoding=ITU-R BT.709 YCbCr
	color-range=YCbCr limited range
plane[319]: plane-26
	crtc=(null)
	fb=0
	crtc-pos=0x0+0+0
	src-pos=0.000000x0.000000+0.000000+0.000000
	rotation=1
	normalized-zpos=0
	color-encoding=ITU-R BT.709 YCbCr
	color-range=YCbCr limited range
plane[329]: plane-27
	crtc=(null)
	fb=0
	crtc-pos=0x0+0+0
	src-pos=0.000000x0.000000+0.000000+0.000000
	rotation=1
	normalized-zpos=11
	color-encoding=ITU-R BT.709 YCbCr
	color-range=YCbCr limited range
crtc[57]: txp
	enable=0
	active=0
	self_refresh_active=0
	planes_changed=0
	mode_changed=0
	active_changed=0
	connectors_changed=0
	color_mgmt_changed=0
	plane_mask=0
	connector_mask=0
	encoder_mask=0
	mode: "": 0 0 0 0 0 0 0 0 0 0 0x0 0x0
crtc[74]: pixelvalve-0
	enable=0
	active=0
	self_refresh_active=0
	planes_changed=0
	mode_changed=0
	active_changed=0
	connectors_changed=0
	color_mgmt_changed=0
	plane_mask=0
	connector_mask=0
	encoder_mask=0
	mode: "": 0 0 0 0 0 0 0 0 0 0 0x0 0x0
crtc[85]: pixelvalve-1
	enable=0
	active=0
	self_refresh_active=0
	planes_changed=0
	mode_changed=0
	active_changed=0
	connectors_changed=0
	color_mgmt_changed=0
	plane_mask=0
	connector_mask=0
	encoder_mask=0
	mode: "": 0 0 0 0 0 0 0 0 0 0 0x0 0x0
crtc[96]: pixelvalve-2
	enable=0
	active=0
	self_refresh_active=0
	planes_changed=0
	mode_changed=0
	active_changed=0
	connectors_changed=0
	color_mgmt_changed=0
	plane_mask=0
	connector_mask=0
	encoder_mask=0
	mode: "": 0 0 0 0 0 0 0 0 0 0 0x0 0x0
crtc[107]: pixelvalve-4
	enable=0
	active=0
	self_refresh_active=0
	planes_changed=1
	mode_changed=0
	active_changed=0
	connectors_changed=0
	color_mgmt_changed=0
	plane_mask=0
	connector_mask=0
	encoder_mask=0
	mode: "": 0 0 0 0 0 0 0 0 0 0 0x0 0x0
crtc[118]: pixelvalve-3
	enable=0
	active=0
	self_refresh_active=0
	planes_changed=0
	mode_changed=0
	active_changed=0
	connectors_changed=0
	color_mgmt_changed=0
	plane_mask=0
	connector_mask=0
	encoder_mask=0
	mode: "": 0 0 0 0 0 0 0 0 0 0 0x0 0x0
connector[32]: HDMI-A-1
	crtc=(null)
	self_refresh_aware=0
	max_requested_bpc=8
connector[42]: HDMI-A-2
	crtc=(null)
	self_refresh_aware=0
	max_requested_bpc=8
connector[63]: Writeback-1
	crtc=(null)
	self_refresh_aware=0
	max_requested_bpc=0

config.txt
----------

arm_64bit=1
arm_boost=1
arm_freq=1800
audio_pwm_mode=514
camera_auto_detect=1
config_hdmi_boost=5
core_freq=500
core_freq_min=200
disable_commandline_tags=2
disable_l2cache=1
disable_overscan=1
display_auto_detect=1
display_hdmi_rotate=-1
display_lcd_rotate=-1
dvfs=3
enable_gic=1
enable_uart=1
force_eeprom_read=1
force_pwm_open=1
framebuffer_ignore_alpha=1
framebuffer_swap=1
gpu_freq=500
gpu_freq_min=250
init_uart_clock=0x2dc6c00
lcd_framerate=60
mask_gpu_interrupt0=3072
mask_gpu_interrupt1=25635
max_framebuffers=2
over_voltage_avs=-10000
pause_burst_frames=1
program_serial_random=1
total_mem=4096
hdmi_force_cec_address:0=65535
hdmi_force_cec_address:1=65535
hdmi_pixel_freq_limit:0=0x11e1a300
hdmi_pixel_freq_limit:1=0x11e1a300
device_tree=-
overlay_prefix=overlays/
hdmi_cvt:0=
hdmi_cvt:1=
hdmi_edid_filename:0=
hdmi_edid_filename:1=
hdmi_timings:0=
hdmi_timings:1=

cmdline.txt
-----------
coherent_pool=1M 8250.nr_uarts=1 snd_bcm2835.enable_headphones=0 snd_bcm2835.enable_headphones=1 snd_bcm2835.enable_hdmi=1 snd_bcm2835.enable_hdmi=0  smsc95xx.macaddr=D8:3A:DD:2A:85:90 vc_mem.mem_base=0x3eb00000 vc_mem.mem_size=0x3ff00000  console=tty1 root=PARTUUID=1b6efd41-02 rootfstype=ext4 fsck.repair=yes rootwait quiet splash plymouth.ignore-serial-consoles

raspi-gpio settings
-------------------

BANK0 (GPIO 0 to 27):
GPIO 0: level=1 fsel=0 func=INPUT pull=UP
GPIO 1: level=1 fsel=0 func=INPUT pull=UP
GPIO 2: level=1 fsel=4 alt=0 func=SDA1 pull=UP
GPIO 3: level=1 fsel=4 alt=0 func=SCL1 pull=UP
GPIO 4: level=0 fsel=0 func=INPUT pull=DOWN
GPIO 5: level=1 fsel=0 func=INPUT pull=UP
GPIO 6: level=1 fsel=0 func=INPUT pull=UP
GPIO 7: level=1 fsel=0 func=INPUT pull=UP
GPIO 8: level=1 fsel=0 func=INPUT pull=UP
GPIO 9: level=0 fsel=0 func=INPUT pull=DOWN
GPIO 10: level=0 fsel=0 func=INPUT pull=DOWN
GPIO 11: level=0 fsel=0 func=INPUT pull=DOWN
GPIO 12: level=0 fsel=0 func=INPUT pull=DOWN
GPIO 13: level=0 fsel=0 func=INPUT pull=DOWN
GPIO 14: level=1 fsel=2 alt=5 func=TXD1 pull=NONE
GPIO 15: level=1 fsel=2 alt=5 func=RXD1 pull=UP
GPIO 16: level=0 fsel=0 func=INPUT pull=DOWN
GPIO 17: level=0 fsel=0 func=INPUT pull=DOWN
GPIO 18: level=0 fsel=0 func=INPUT pull=DOWN
GPIO 19: level=0 fsel=0 func=INPUT pull=DOWN
GPIO 20: level=0 fsel=0 func=INPUT pull=DOWN
GPIO 21: level=0 fsel=0 func=INPUT pull=DOWN
GPIO 22: level=0 fsel=0 func=INPUT pull=DOWN
GPIO 23: level=1 fsel=0 func=INPUT pull=DOWN
GPIO 24: level=0 fsel=0 func=INPUT pull=DOWN
GPIO 25: level=0 fsel=0 func=INPUT pull=DOWN
GPIO 26: level=0 fsel=0 func=INPUT pull=DOWN
GPIO 27: level=0 fsel=0 func=INPUT pull=DOWN
BANK1 (GPIO 28 to 45):
GPIO 28: level=1 fsel=2 alt=5 func=RGMII_MDIO pull=UP
GPIO 29: level=0 fsel=2 alt=5 func=RGMII_MDC pull=DOWN
GPIO 30: level=0 fsel=7 alt=3 func=CTS0 pull=UP
GPIO 31: level=0 fsel=7 alt=3 func=RTS0 pull=NONE
GPIO 32: level=1 fsel=7 alt=3 func=TXD0 pull=NONE
GPIO 33: level=1 fsel=7 alt=3 func=RXD0 pull=UP
GPIO 34: level=1 fsel=7 alt=3 func=SD1_CLK pull=NONE
GPIO 35: level=1 fsel=7 alt=3 func=SD1_CMD pull=UP
GPIO 36: level=1 fsel=7 alt=3 func=SD1_DAT0 pull=UP
GPIO 37: level=0 fsel=7 alt=3 func=SD1_DAT1 pull=UP
GPIO 38: level=1 fsel=7 alt=3 func=SD1_DAT2 pull=UP
GPIO 39: level=1 fsel=7 alt=3 func=SD1_DAT3 pull=UP
GPIO 40: level=0 fsel=4 alt=0 func=PWM1_0 pull=NONE
GPIO 41: level=0 fsel=4 alt=0 func=PWM1_1 pull=NONE
GPIO 42: level=0 fsel=1 func=OUTPUT pull=UP
GPIO 43: level=1 fsel=0 func=INPUT pull=UP
GPIO 44: level=1 fsel=0 func=INPUT pull=UP
GPIO 45: level=1 fsel=0 func=INPUT pull=UP
BANK2 (GPIO 46 to 53):
GPIO 46: level=0 fsel=0 func=INPUT pull=UP
GPIO 47: level=0 fsel=0 func=INPUT pull=UP
GPIO 48: level=0 fsel=0 func=INPUT pull=DOWN
GPIO 49: level=0 fsel=0 func=INPUT pull=DOWN
GPIO 50: level=0 fsel=0 func=INPUT pull=DOWN
GPIO 51: level=0 fsel=0 func=INPUT pull=DOWN
GPIO 52: level=0 fsel=0 func=INPUT pull=DOWN
GPIO 53: level=0 fsel=0 func=INPUT pull=DOWN

vcdbg log messages
------------------

005124.001: brfs: File read: /mfs/sd/config.txt
005124.985: brfs: File read: 2122 bytes
005146.458: HDMI0:EDID error reading EDID block 0 attempt 0
005147.473: HDMI0:EDID giving up on reading EDID block 0
005159.278: HDMI1:EDID error reading EDID block 0 attempt 0
005160.294: HDMI1:EDID giving up on reading EDID block 0
005161.368: brfs: File read: /mfs/sd/config.txt
005931.332: gpioman: gpioman_get_pin_num: pin DISPLAY_DSI_PORT not defined
005933.856: *** Restart logging
005933.876: brfs: File read: 2122 bytes
005939.281: hdmi: HDMI0:EDID error reading EDID block 0 attempt 0
005940.299: hdmi: HDMI0:EDID giving up on reading EDID block 0
005945.341: hdmi: HDMI0:EDID error reading EDID block 0 attempt 0
005946.357: hdmi: HDMI0:EDID giving up on reading EDID block 0
005946.375: hdmi: HDMI:hdmi_get_state is deprecated, use hdmi_get_display_state instead
005951.418: hdmi: HDMI1:EDID error reading EDID block 0 attempt 0
005952.432: hdmi: HDMI1:EDID giving up on reading EDID block 0
005957.474: hdmi: HDMI1:EDID error reading EDID block 0 attempt 0
005958.491: hdmi: HDMI1:EDID giving up on reading EDID block 0
005958.506: hdmi: HDMI:hdmi_get_state is deprecated, use hdmi_get_display_state instead
005958.520: HDMI0: hdmi_pixel_encoding: 300000000
005958.534: HDMI1: hdmi_pixel_encoding: 300000000
005958.876: kernel=
005963.775: dtb_file 'bcm2711-rpi-4-b.dtb'
005966.343: brfs: File read: /mfs/sd/bcm2711-rpi-4-b.dtb
005966.358: Loaded 'bcm2711-rpi-4-b.dtb' to 0x100 size 0xcd71
005979.445: brfs: File read: 52593 bytes
005987.992: brfs: File read: /mfs/sd/overlays/overlay_map.dtb
006068.403: brfs: File read: 2347 bytes
006069.727: brfs: File read: /mfs/sd/config.txt
006070.137: dtparam: i2c_arm=on
006078.856: dtparam: audio=on
006083.427: brfs: File read: 2122 bytes
006094.206: brfs: File read: /mfs/sd/overlays/vc4-kms-v3d-pi4.dtbo
006155.364: Loaded overlay 'vc4-kms-v3d'
006313.200: brfs: File read: 3913 bytes
006314.102: brfs: File read: /mfs/sd/cmdline.txt
006314.143: Read command line from file 'cmdline.txt':
006314.155: 'console=tty1 root=PARTUUID=1b6efd41-02 rootfstype=ext4 fsck.repair=yes rootwait quiet splash plymouth.ignore-serial-consoles'
006424.707: brfs: File read: 124 bytes
006761.416: brfs: File read: /mfs/sd/kernel8.img
006761.436: Loaded 'kernel8.img' to 0x80000 size 0x7d6bd0
007932.088: Kernel relocated to 0x200000
007932.101: Device tree loaded to 0x2eff2c00 (size 0xd3c0)
007935.297: bfs_xhci_stop
007935.305: XHCI-STOP
007935.389: xHC ver: 256 HCS: 05000420 fc000031 00e70004 HCC: 002841eb
007935.407: USBSTS 18
010015.808: vchiq_core: vchiq_init_state: slot_zero = 0xcf000000, is_master = 1

dmesg log
---------
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
