jarjuk/jrr/cad/sabluunat/JussiSalmiakki.jpg

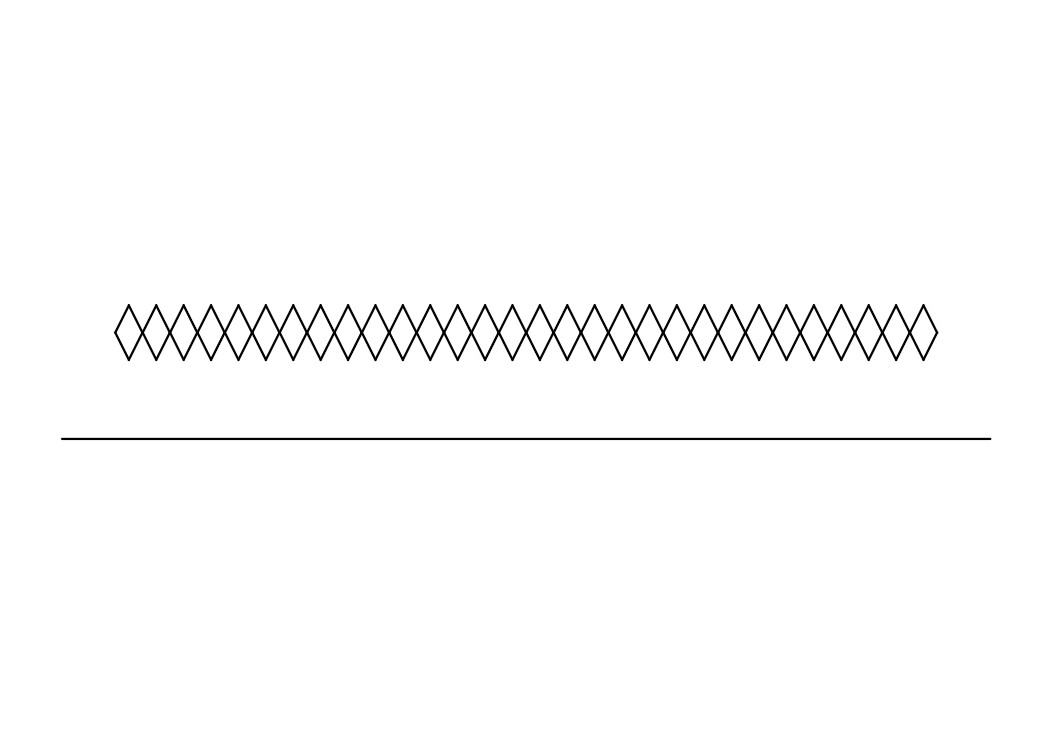
cad/sabluunat/JussiSalmiakki.jpg
