jarjuk/jrr/pics-keep/jrr5x1-distortion.jpg

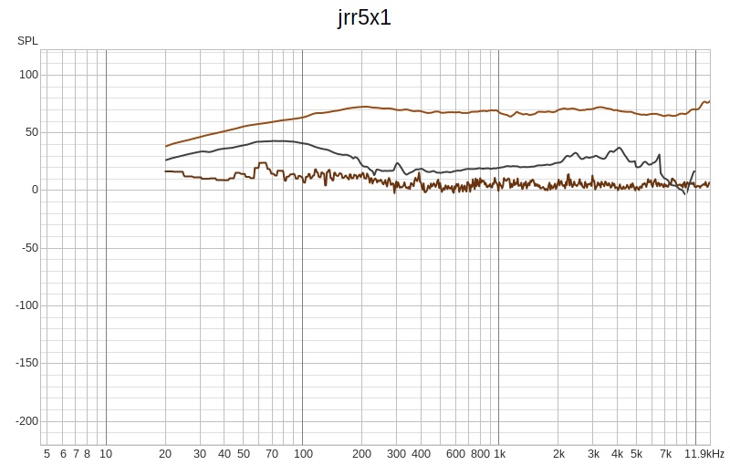
pics-keep/jrr5x1-distortion.jpg
