jarjuk/jrr/pics-keep/jrr5x1-spl.jpg

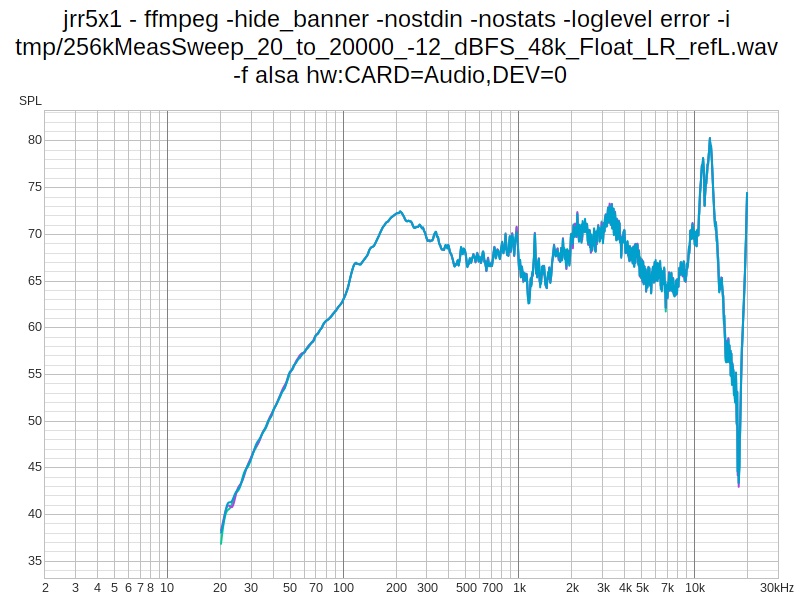
pics-keep/jrr5x1-spl.jpg
