jarjuk/jrr/pics-keep/jrr5x1-waterfall.jpg

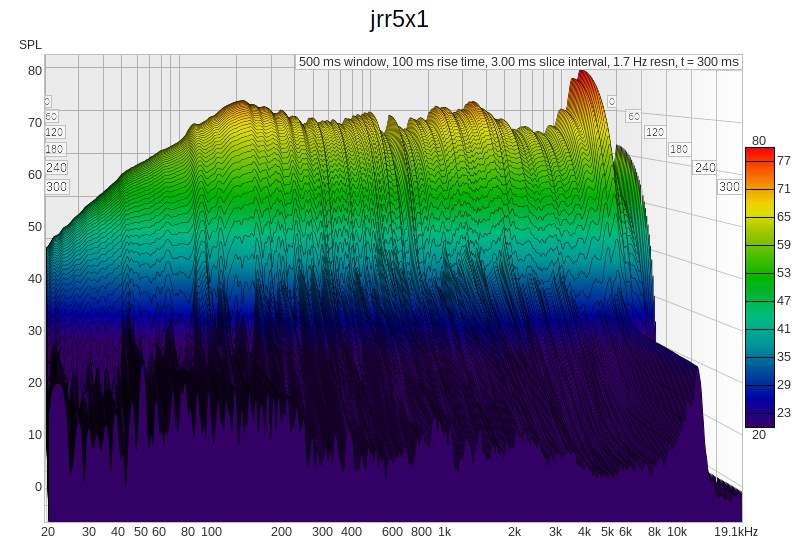
pics-keep/jrr5x1-waterfall.jpg
