jarjuk/jrr/pics-keep/jrr5x-distortion.jpg

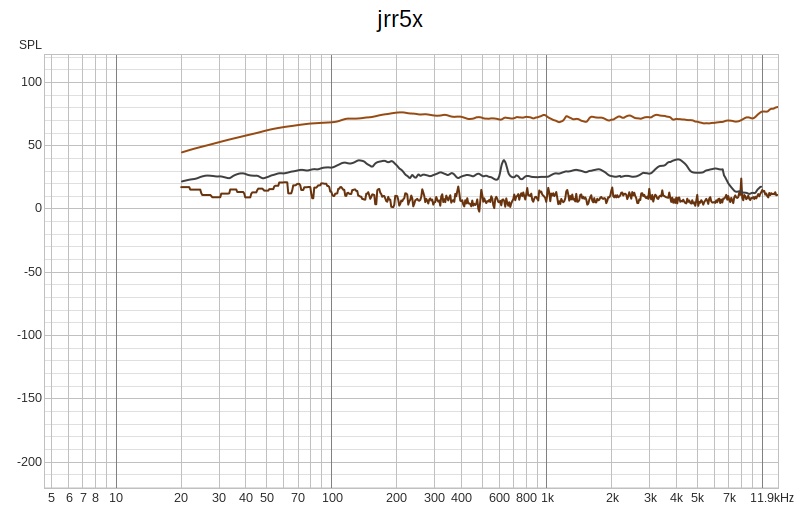
pics-keep/jrr5x-distortion.jpg
