jarjuk/jrr/pics-keep/jrr5x-spl.jpg

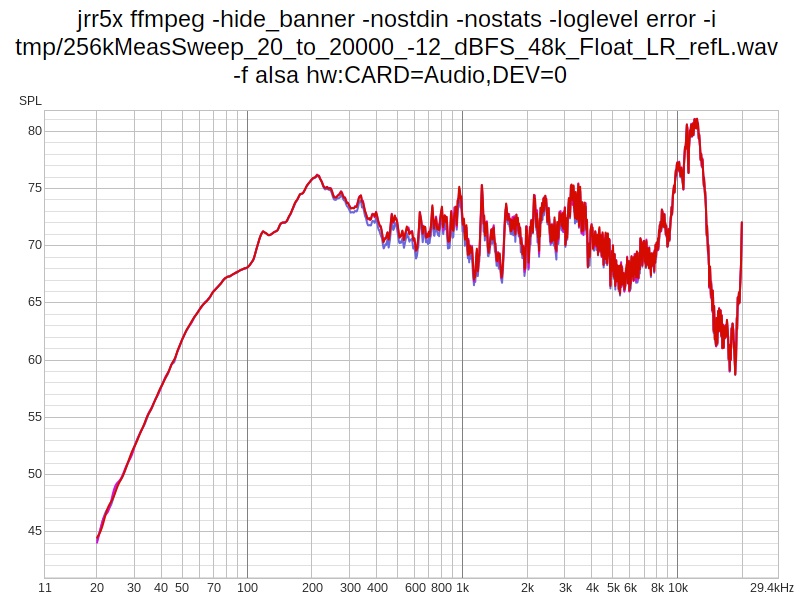
pics-keep/jrr5x-spl.jpg
