jarjuk/jrr/pics-keep/screenshots/jrr-03-channel-activate-WNRVbluegrass.png

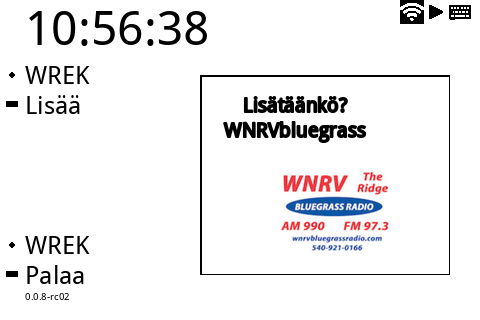
pics-keep/screenshots/jrr-03-channel-activate-WNRVbluegrass.png
