jarjuk/jrr/pics-keep/screenshots/jrr-03-channel-browse-Järviradio.png

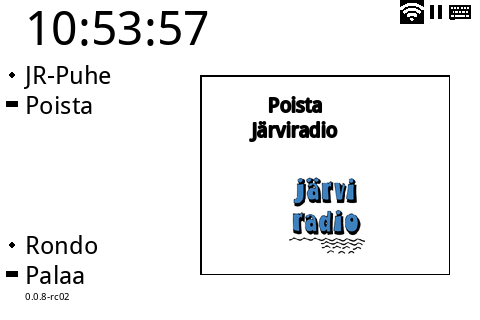
pics-keep/screenshots/jrr-03-channel-browse-Järviradio.png
