jarjuk/jrr/pics-keep/screenshots/jrr-03-firmware-update-0.0.8-rc02.png

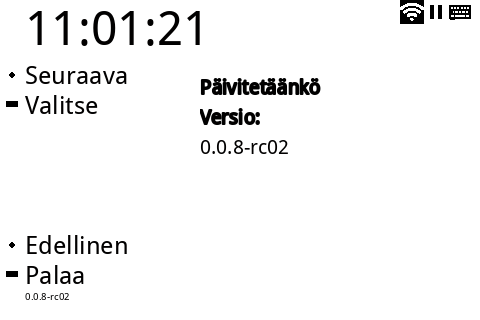
pics-keep/screenshots/jrr-03-firmware-update-0.0.8-rc02.png
