jarjuk/jrr/pics-keep/screenshots/jrr-04-channel-activate-confirm-actvate.png

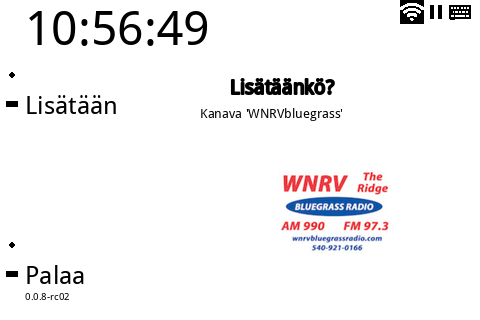
pics-keep/screenshots/jrr-04-channel-activate-confirm-actvate.png
