jarjuk/jrr/pics-keep/screenshots/jrr-04-channel-browse-delete-confirm-delete.png

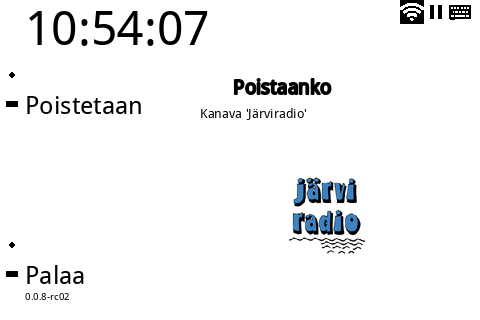
pics-keep/screenshots/jrr-04-channel-browse-delete-confirm-delete.png
