jarjuk/jrr/pics-keep/screenshots/jrr-04-firmware-update-confirm-activate.png

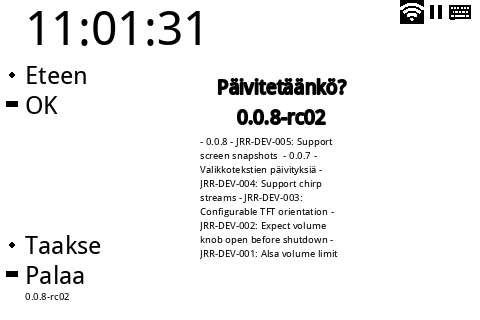
pics-keep/screenshots/jrr-04-firmware-update-confirm-activate.png
