jarjuk/jrr/pics-keep/screenshots/jrr-90-error-Ei päivitettävää.png

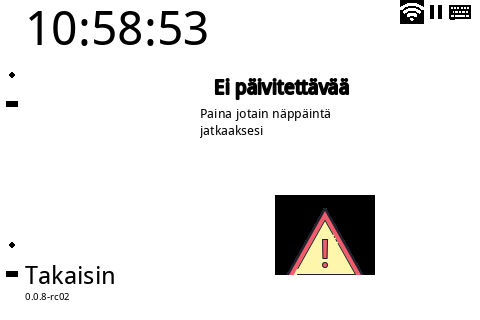
pics-keep/screenshots/jrr-90-error-Ei päivitettävää.png
