jarjuk/jrr/pics/jrr-menu.png

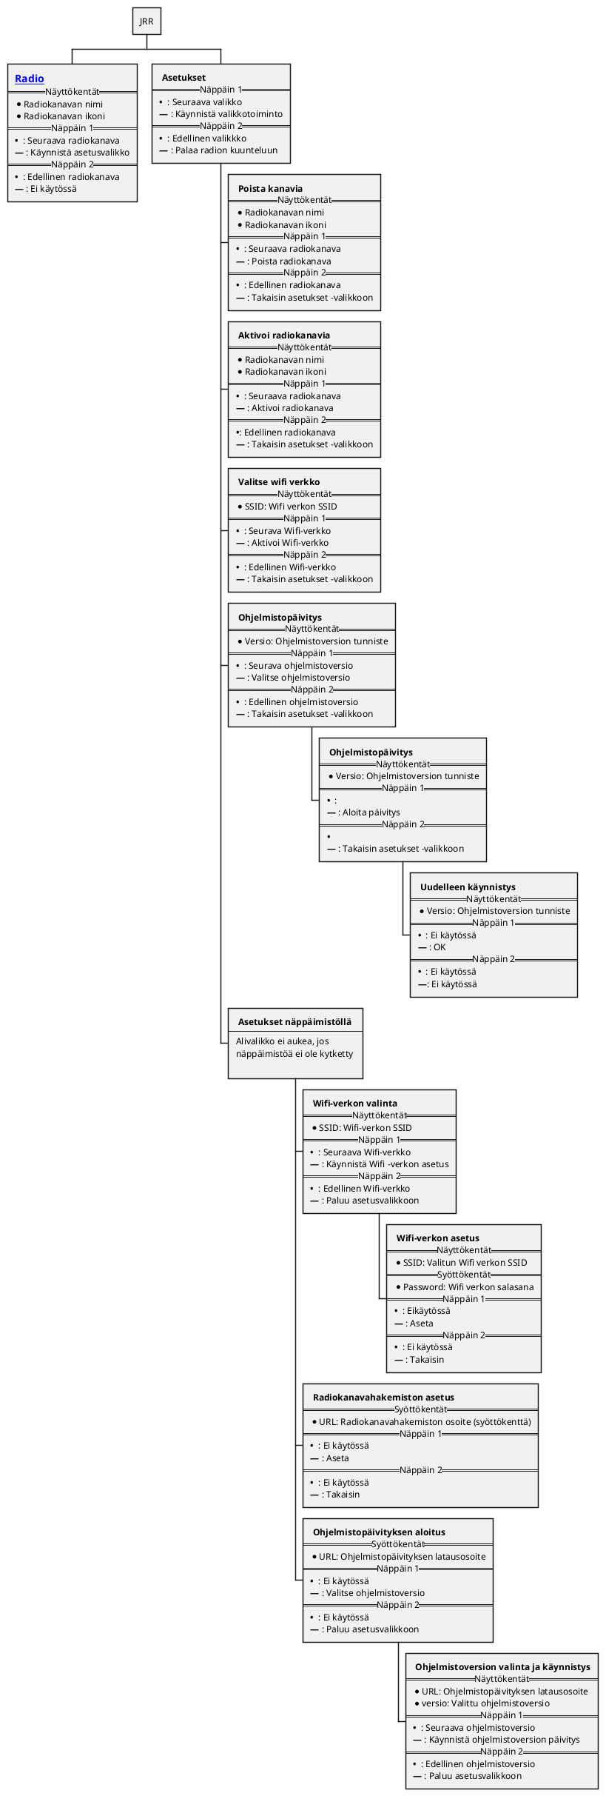
pics/jrr-menu.png
