jarjuk/jrr/resources/sprite/01-net-ok.png

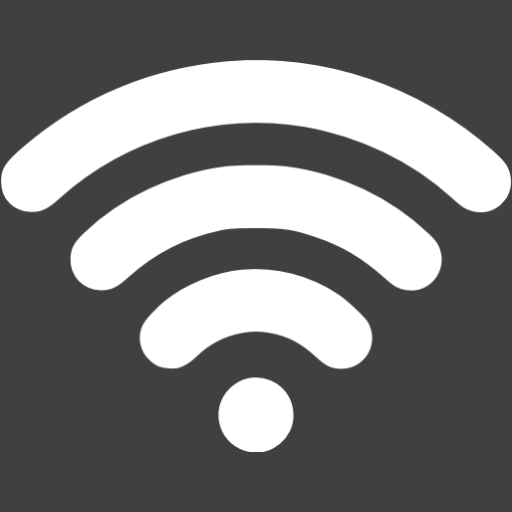
resources/sprite/01-net-ok.png
