jarjuk/jrr/resources/sprite/06-dash.png

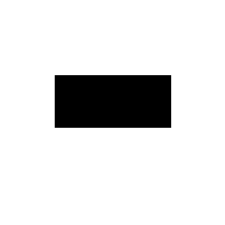
resources/sprite/06-dash.png
