jarjuk/jrr/src/Python_ILI9486/ILI9486.py

# Copyright (c)
# Authors: Tony DiCola, Liqun Hu, Thorben Yzer
#
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
# constants
LCD_WIDTH = 320
LCD_HEIGHT = 480

# commands
CMD_RDPXLFMT = 0x0C

CMD_SLPIN = 0x10
CMD_SLPOUT = 0x11

CMD_INVOFF = 0x20
CMD_INVON = 0x21
CMD_DISPOFF = 0x28
CMD_DISPON = 0x29

CMD_SETCA = 0x2A
CMD_SETPA = 0x2B
CMD_WRMEM = 0x2C
CMD_RDMEM = 0x2E

CMD_MADCTL = 0x36
CMD_IDLOFF = 0x38
CMD_IDLON = 0x39
CMD_PXLFMT = 0x3A

CMD_IFMODE = 0xB0

CMD_PWRCTLNOR = 0xC2
CMD_VCOMCTL = 0xC5

CMD_PGAMCTL = 0xE0
CMD_NGAMCTL = 0xE1


def image_to_data(image: Image) -> object:
    """Converts a PIL image to 666RGB format that can be drawn on the LCD."""
    pb = np.array(image.convert('RGB')).astype('uint16')
    # cut of the two least significant / rightmost bits to convert 8-bit color to 6-bit color
    return np.dstack((pb[:, :, 0] & 0xFC, pb[:, :, 1] & 0xFC, pb[:, :, 2] & 0xFC)).flatten().tolist()


class Origin(Enum):
    """Representation of the display origin. The origin is defined by the position of the image relative to the default
    orientation of the raspberry. The default orientation has the GPIO pins being on top, so that the raspberry logo
    and the model's name are readable. The reference point is then the upper left corner, where GPIO pin 1 is located.
    The origin UPPER_LEFT is the default origin, because the reference point is in the upper left corner."""

    # data: MY | MX | MV | ML | BGR | MH | X | X
    # The MV bit controls the format. 0 means portrait mode, 1 means landscape mode.
    # The BGR bit is a bit weird. 0 means RGB mode, 1 means BGR mode. However, we always set it to 1 / BGR, despite
    # using RGB pixel format. Maybe the documentation is wrong here.
    UPPER_LEFT = 0x28
    UPPER_LEFT_MIRRORED = 0xA8
    LOWER_LEFT = 0x48
    LOWER_LEFT_MIRRORED = 0x08
    UPPER_RIGHT = 0x88
    UPPER_RIGHT_MIRRORED = 0xC8
    LOWER_RIGHT = 0xE8
    LOWER_RIGHT_MIRRORED = 0x68


class ILI9486:
    """Representation of an ILI9486 TFT."""

    @classmethod
    def landscape_dimensions(cls) -> tuple:
        """Returns the display dimensions in landscape mode, no matter what mode is used"""
        return LCD_HEIGHT, LCD_WIDTH

    @classmethod
    def portrait_dimensions(cls) -> tuple:
        """Returns the display dimensions in portrait mode, no matter what mode is used"""
        return LCD_WIDTH, LCD_HEIGHT

    def __init__(self, spi: SpiDev, dc: int, rst: int | None = None, origin: Origin = Origin.LOWER_RIGHT):
        # def __init__(self, spi: SpiDev, dc: int, rst: int = None, *, origin: Origin = Origin.UPPER_LEFT):
        """Creates an instance of the display using the given SPI connection. Must provide the SPI driver and the GPIO
        pin number for the DC pin. Can optionally provide the GPIO pin number for the reset pin. Optionally the origin
        can be set. The default is UPPER_LEFT, which is landscape mode this the bottom of the image located at the
        power, video and audio out are of the Pi."""
        self.__spi = spi
        self.__dc = dc
        self.__rst = rst
        self.__origin = origin
        self.__width = LCD_WIDTH
        self.__height = LCD_HEIGHT
        self.__inverted = False
        self.__idle = False

        GPIO.setmode(GPIO.BCM)
        GPIO.setup(self.__dc, GPIO.OUT)
        GPIO.output(self.__dc, GPIO.HIGH)
        if self.__rst is not None:
            GPIO.setup(self.__rst, GPIO.OUT)
            GPIO.output(self.__rst, GPIO.HIGH)

        # swap width and height if selected origin is landscape mode by checking if third bit is 1
        if self.__origin.value & 0x20:
            self.__width, self.__height = self.__height, self.__width
        self.__buffer = Image.new(
            'RGB', (self.__width, self.__height), (0, 0, 0))

    def dimensions(self) -> tuple:
        """Returns the current display dimensions"""
        return self.__width, self.__height

    def is_landscape(self) -> bool:
        """Returns true if selected origin is landscape mode; false otherwise"""
        return bool(self.__origin.value & 0x20)

    def send(self, data, is_data=True, chunk_size=4096):
        """Writes a byte or an array of bytes to the display."""
        # dc low for command, high for data
        GPIO.output(self.__dc, is_data)
        if isinstance(data, int):
            self.__spi.writebytes([data])
        else:
            for start in range(0, len(data), chunk_size):
                end = min(start + chunk_size, len(data))
                self.__spi.writebytes(data[start: end])
        return self

    def command(self, data):
        """Writes a byte or an array of bytes to the display as a command."""
        return self.send(data, False)

    def data(self, data):
        """Writes a byte or an array of bytes to the display as data."""
        return self.send(data, True)

    def reset(self):
        """Resets the display if a reset pin is provided."""
        if self.__rst is not None:
            GPIO.output(self.__rst, GPIO.HIGH)
            time.sleep(.001)  # wait a bit to make sure the output was HIGH
            GPIO.output(self.__rst, GPIO.LOW)
            # wait 100 µs to trigger the reset (should be 10 µs, but the OS is not precise enough)
            time.sleep(.000100)
            GPIO.output(self.__rst, GPIO.HIGH)
            # wait 120 ms for finishing blanking and resetting
            time.sleep(.120)
            self.__inverted = False
            self.__idle = False
        return self

    def _init_sequence(self):
        """Initializes the display. Protected in case you want to override it for e.g. gamma control"""
        self.command(CMD_IFMODE).data(0x00)
        self.command(CMD_SLPOUT)  # turns off the sleep mode
        time.sleep(0.020)

        self.command(CMD_PXLFMT).data(0x66)  # 18 bits per pixel
        self.command(CMD_RDPXLFMT).data(0x66)  # 18 bits per pixel

        self.command(CMD_PWRCTLNOR).command(0x44)

        self.command(CMD_VCOMCTL).send(
            [0x00, 0x00, 0x00, 0x00], True, chunk_size=1)

        self.command(CMD_PGAMCTL)\
            .send([0x0F, 0x1F, 0x1C, 0x0C, 0x0F, 0x08, 0x48, 0x98, 0x37, 0x0A, 0x13, 0x04, 0x11, 0x0D, 0x00], True,
                  chunk_size=1)  # values must be sent one by one, thus setting chunk size to 1

        self.command(CMD_NGAMCTL)\
            .send([0x0F, 0x32, 0x2E, 0x0B, 0x0D, 0x05, 0x47, 0x75, 0x37, 0x06, 0x10, 0x03, 0x24, 0x20, 0x00], True,
                  chunk_size=1)  # values must be sent one by one, thus setting chunk size to 1

        self.command(CMD_MADCTL).data(
            self.__origin.value)  # memory address control

        self.command(CMD_SLPOUT)
        self.command(CMD_DISPON)
        return self

    def begin(self):
        """Initializes the display by resetting it and calling the init sequence."""
        return self.reset()._init_sequence()

    def set_window(self, x0=0, y0=0, x1=None, y1=None):
        """Sets the pixel address window for proceeding drawing commands."""
        if x1 is None:
            x1 = self.__width - 1
        if y1 is None:
            y1 = self.__height - 1
        self.command(CMD_SETCA)  # column address
        self.data(x0 >> 8)
        self.data(x0 & 0xFF)
        self.data(x1 >> 8)
        self.data(x1 & 0xFF)
        self.command(CMD_SETPA)  # page address / row address
        self.data(y0 >> 8)
        self.data(y0 & 0xFF)
        self.data(y1 >> 8)
        self.data(y1 & 0xFF)
        return self

    def display(self, image=None, x0=0, y0=0):
        """Writes the display buffer or provided image to the display. If no
        image is provided the display buffer will be written to the display.
        If an image is provided, it should be in RGB format and the same
        dimensions as the display."""
        if image is None:
            image = self.__buffer
        width, height = image.size
        x1 = x0 + width - 1
        y1 = y0 + height - 1
        if image.mode != 'RGB':
            raise ValueError('Image must be in RGB format')
        if x1 >= self.__width or y1 >= self.__height or x0 < 0 or y0 < 0:
            raise ValueError(
                'Image exceeds display bounds ({0}x{1})'.format(self.__width, self.__height))
        self.set_window(x0, y0, x1, y1)
        data = image_to_data(image)
        self.command(CMD_WRMEM)
        if isinstance(data, list):
            self.data(list(data))
        return self

    def clear(self, color=(0, 0, 0)):
        """Clears the image buffer to the specified RGB color or black if not provided."""
        width, height = self.__buffer.size
        self.__buffer.putdata([color] * (width * height))
        return self

    def draw(self) -> ImageDraw:
        """Returns a PIL ImageDraw instance for 2D drawing on the image buffer."""
        return ImageDraw.Draw(self.__buffer)

    def is_inverted(self) -> bool:
        """Returns the current inversion state."""
        return self.__inverted

    def invert(self, state: bool = True):
        """Sets display inversion to the specified state. If not provided, state
        is True, which inverts the display. If state is False, the display turns
        back into normal mode."""
        if state:
            self.command(CMD_INVON)
        else:
            self.command(CMD_INVOFF)
        self.__inverted = state
        return self

    def is_idle(self) -> bool:
        """Returns the current idle state."""
        return self.__idle

    def idle(self, state: bool = True):
        """Sets the display idle state to the specified state. If not provided,
        state is True, which turns the idle mode on. If state is False, the
        display turns back into normal mode. In idle mode colors expression is
        reduced."""
        if state:
            self.command(CMD_IDLON)
        else:
            self.command(CMD_IDLOFF)
        self.__idle = state
        return self

    def on(self):
        """Turns the display on."""
        return self.command(CMD_DISPON)

    def off(self):
        """Turns the display off."""
        return self.command(CMD_DISPOFF)

    def sleep(self):
        """Turns the displays sleep mode on"""
        self.command(CMD_SLPIN)
        time.sleep(0.005)
        return self

    def wake_up(self):
        """Turns the displays sleep mode off"""
        self.command(CMD_SLPOUT)
        time.sleep(0.005)
        return self
